OpeningDesign/Vacation_Rental/Transfer/20170905 - ridge rafter hanger proposal/20170905 - ridge rafter hanger proposal - KDF Markup.pdf

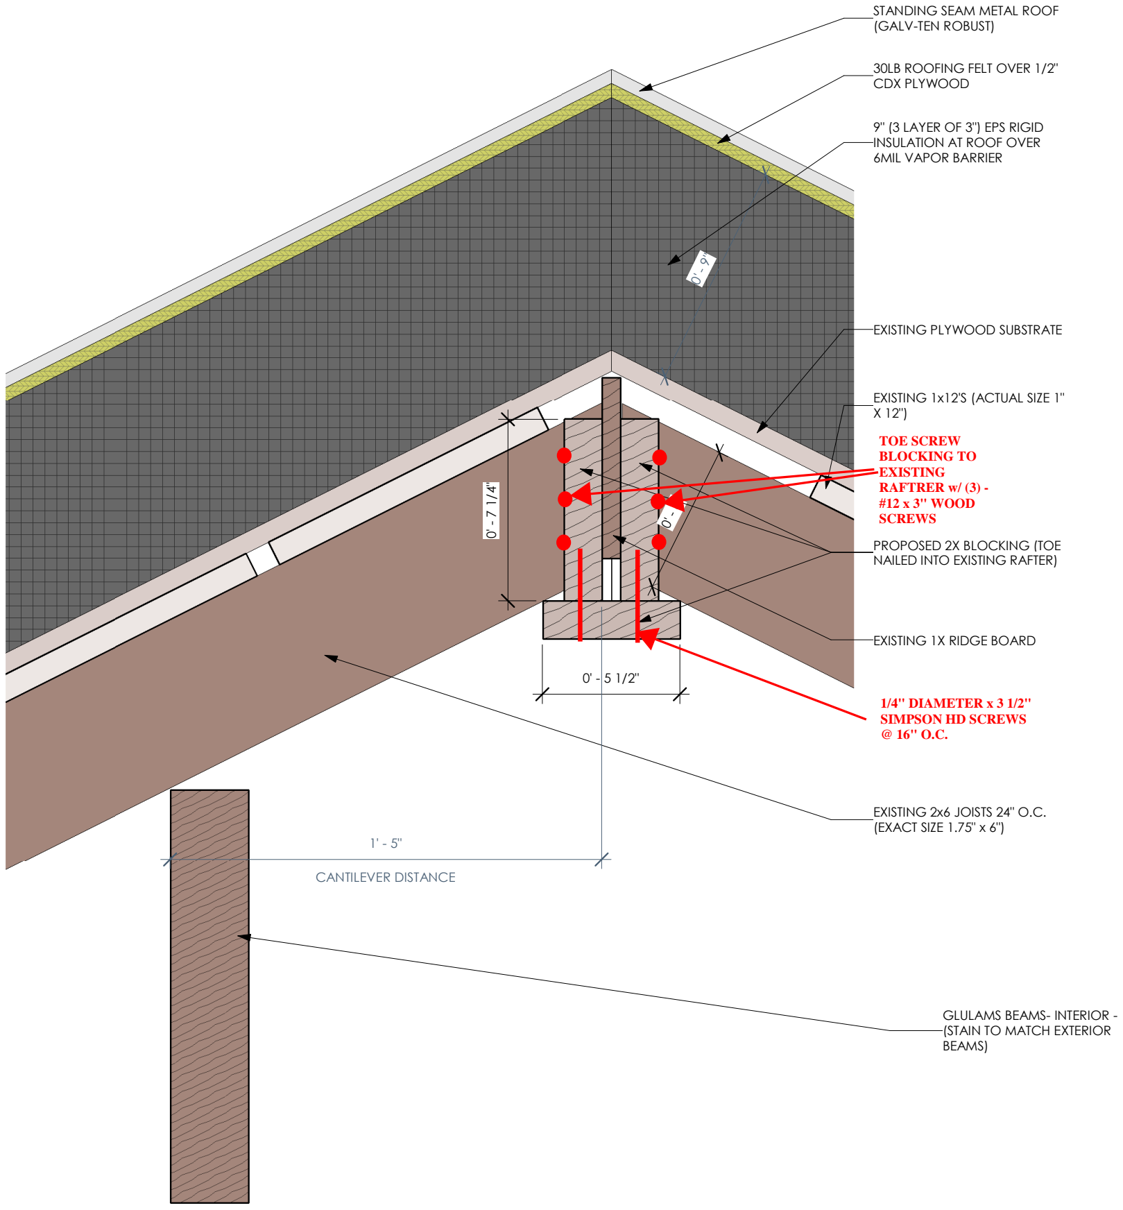
[picture p10: page 1]

EXISTING 1X RIDGE BOARD

GLULAMS BEAMS- INTERIOR -
(STAIN TO MATCH EXTERIOR
BEAMS)

0' - 9"

STANDING SEAM METAL ROOF
(GALV-TEN ROBUST)

30LB ROOFING FELT OVER 1/2" CDX PLYWOOD

9" (3 LAYER OF 3") EPS RIGID INSULATION AT ROOF OVER
6MIL VAPOR BARRIER

EXISTING 1x12'S (ACTUAL SIZE 1" X 12")

0' - 6"

PROPOSED 2X BLOCKING (TOE
NAILED INTO EXISTING RAFTER)

0' - 7 1/4"

0' - 5 1/2"

EXISTING PLYWOOD SUBSTRATE

EXISTING 2x6 JOISTS 24" O.C. (EXACT SIZE 1.75" x 6")

CANTILEVER DISTANCE

1' - 5"
