OpeningDesign/Vacation_Rental/Models/2D Documents/Enscape_2017-05-05-13-06-47.png

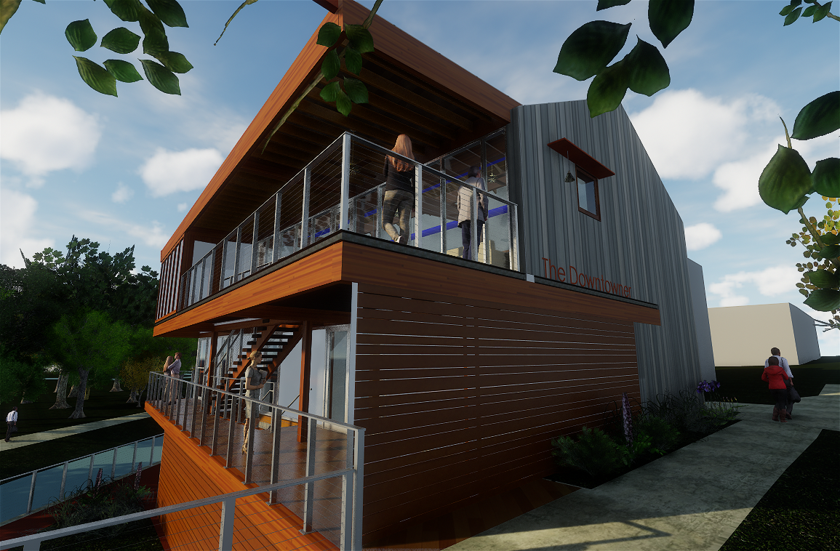
Models/2D Documents/Enscape_2017-05-05-13-06-47.png
