OpeningDesign/Vacation_Rental/Models/2D Documents/Enscape_2017-06-13-12-27-37.png

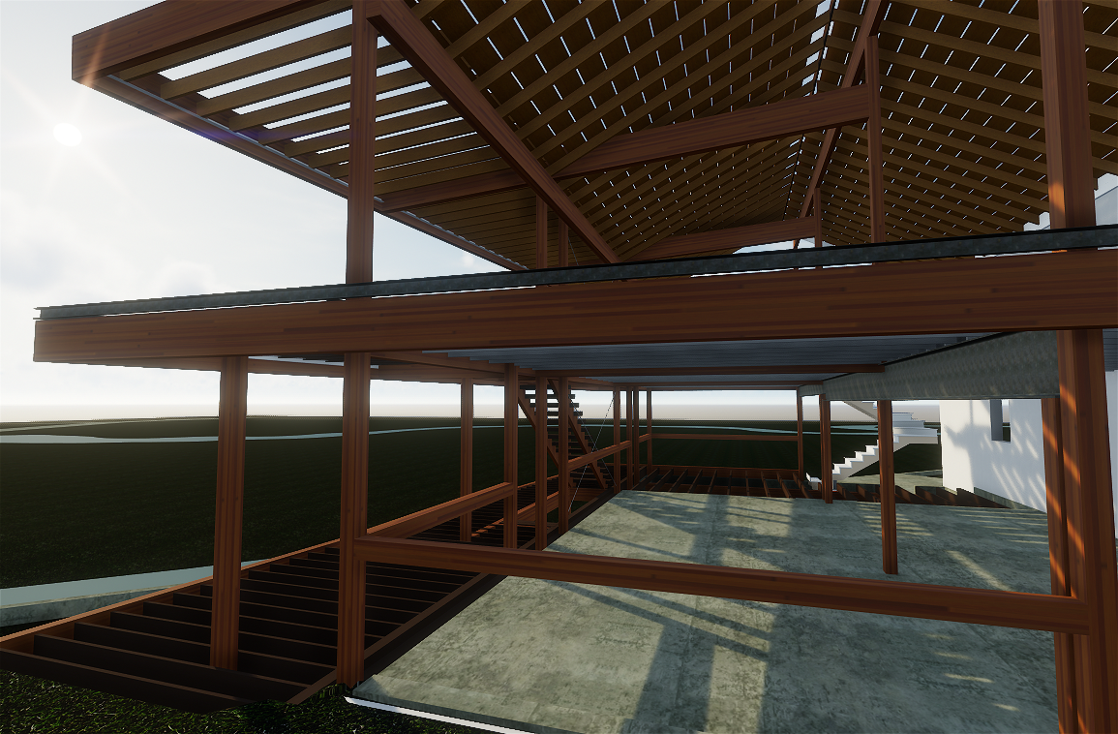
Models/2D Documents/Enscape_2017-06-13-12-27-37.png
