OpeningDesign/Vacation_Rental/Models/2D Documents/Precedent Images/0c7a3d3e602ee59556915388a51b5f31.jpg

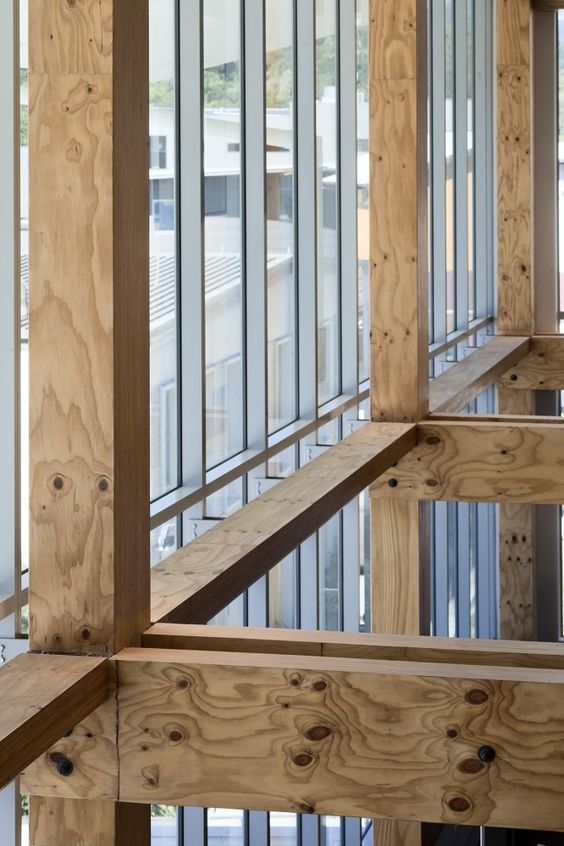
Models/2D Documents/Precedent Images/0c7a3d3e602ee59556915388a51b5f31.jpg
