OpeningDesign/Vacation_Rental/Models/2D Documents/Precedent Images/0d3b4f92185cae513149416970916cf3.jpg

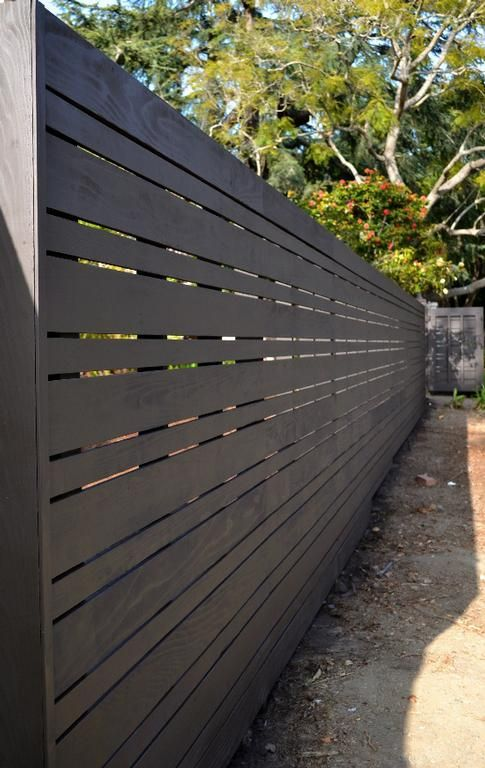
Models/2D Documents/Precedent Images/0d3b4f92185cae513149416970916cf3.jpg
