OpeningDesign/Vacation_Rental/Models/2D Documents/Precedent Images/0d22dfaaf4365529f39f1fb8fd99be02.jpg

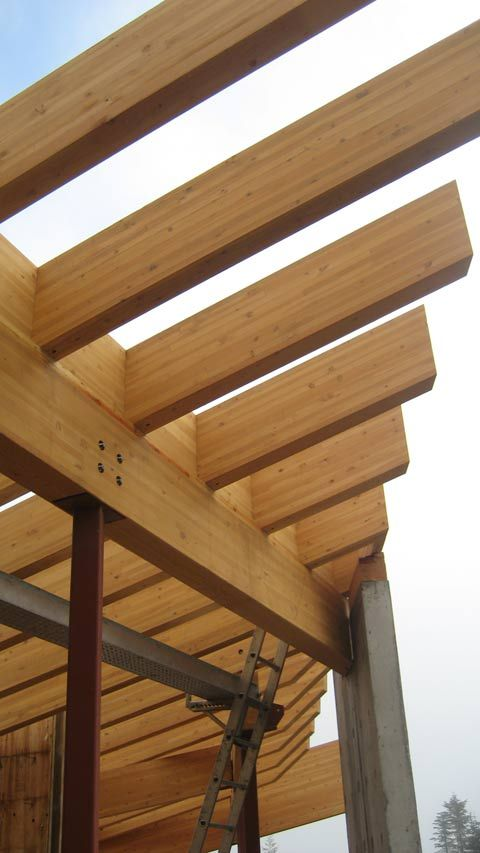
Models/2D Documents/Precedent Images/0d22dfaaf4365529f39f1fb8fd99be02.jpg
