OpeningDesign/Vacation_Rental/Models/2D Documents/Precedent Images/0e876199f10c692c4519da679c8bf5a2.jpg

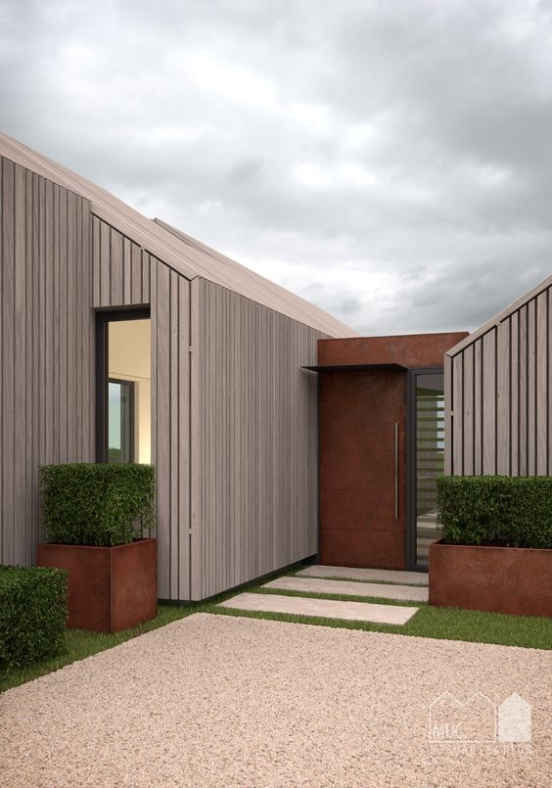
Models/2D Documents/Precedent Images/0e876199f10c692c4519da679c8bf5a2.jpg
