OpeningDesign/Vacation_Rental/Models/2D Documents/Precedent Images/2aeafff6965cd7d682d069013d51a1f6.jpg

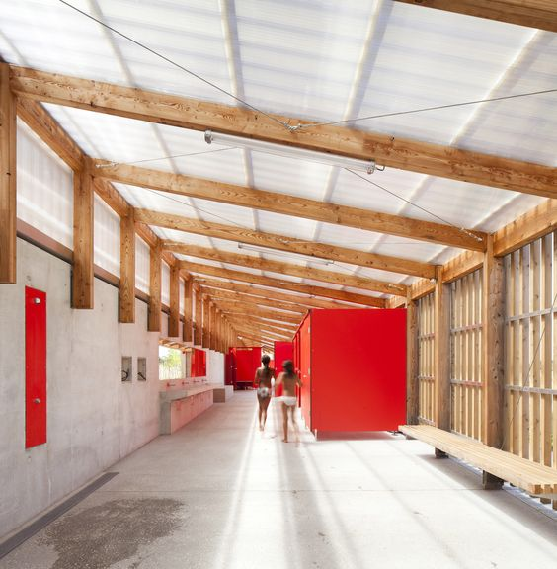
Models/2D Documents/Precedent Images/2aeafff6965cd7d682d069013d51a1f6.jpg
