OpeningDesign/Vacation_Rental/Models/2D Documents/Precedent Images/2b15397afc1d49e527a551473df39ec7.jpg

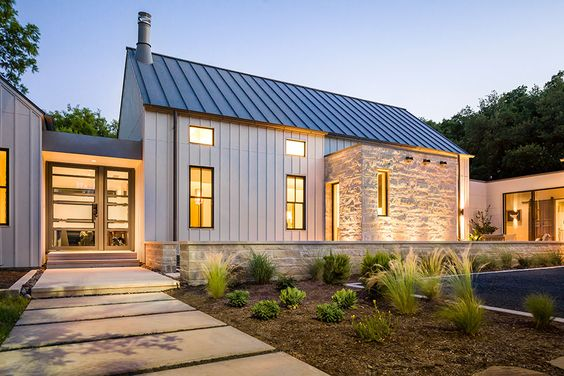
Models/2D Documents/Precedent Images/2b15397afc1d49e527a551473df39ec7.jpg
