OpeningDesign/Vacation_Rental/Models/2D Documents/Precedent Images/02c92ba6af77f66db8dde50bc57269ea.jpg

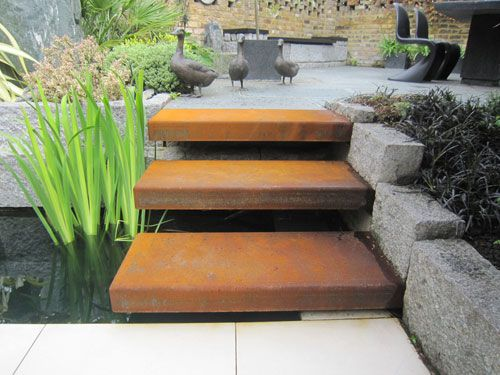
Models/2D Documents/Precedent Images/02c92ba6af77f66db8dde50bc57269ea.jpg
