OpeningDesign/Vacation_Rental/Models/2D Documents/Precedent Images/06a3a0534c0e5ad84e067b8049411fe7.jpg

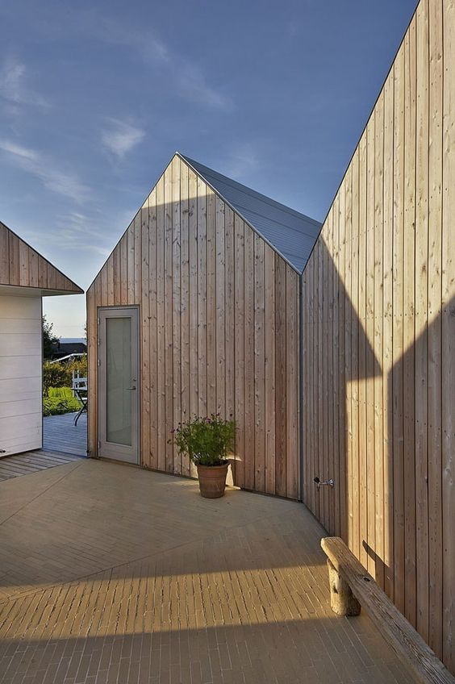
Models/2D Documents/Precedent Images/06a3a0534c0e5ad84e067b8049411fe7.jpg
