OpeningDesign/Vacation_Rental/Models/2D Documents/Precedent Images/07fff5209de71a5784c75fbcb462362a.jpg

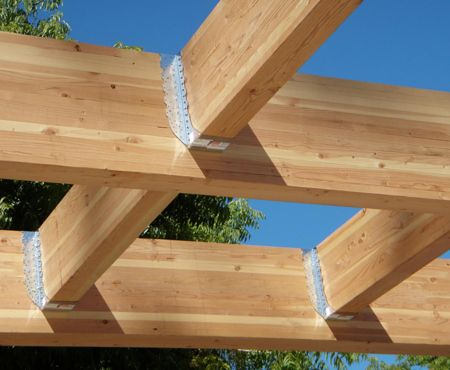
Models/2D Documents/Precedent Images/07fff5209de71a5784c75fbcb462362a.jpg
