OpeningDesign/Vacation_Rental/Models/2D Documents/Precedent Images/9a9ac3109ec64012235650a28028a656.jpg

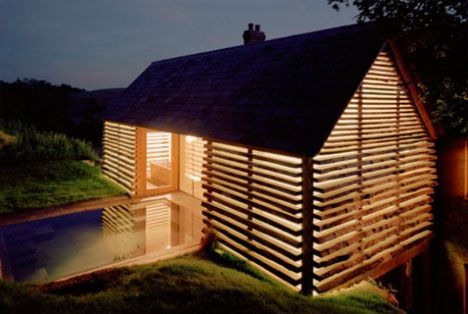
Models/2D Documents/Precedent Images/9a9ac3109ec64012235650a28028a656.jpg
