OpeningDesign/Vacation_Rental/Models/2D Documents/Precedent Images/9c87666fc1ba1ee0fd325ccdcd60f64e.jpg

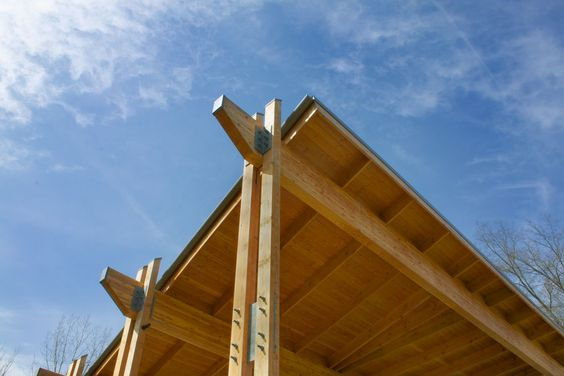
Models/2D Documents/Precedent Images/9c87666fc1ba1ee0fd325ccdcd60f64e.jpg
