OpeningDesign/Vacation_Rental/Models/2D Documents/Precedent Images/40b55ad3849afebcd33c69893c14218f.jpg

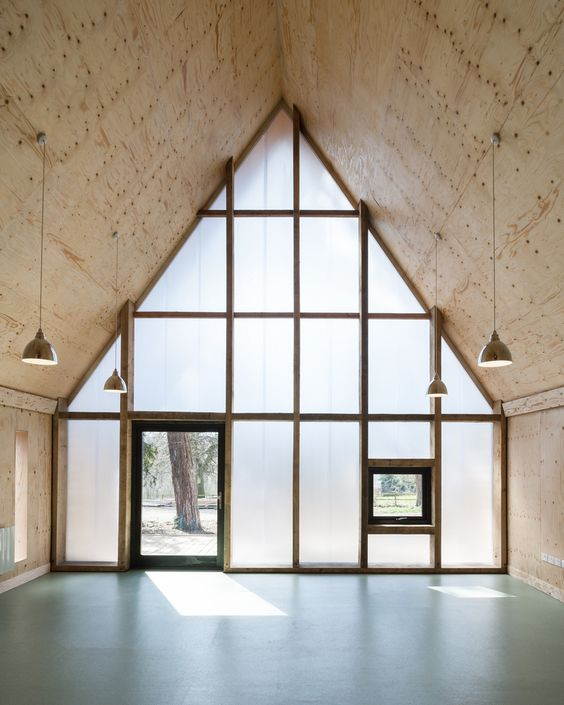
Models/2D Documents/Precedent Images/40b55ad3849afebcd33c69893c14218f.jpg
