OpeningDesign/Vacation_Rental/Models/2D Documents/Precedent Images/41b5add22737bef4c1494f2282eae9dd.jpg

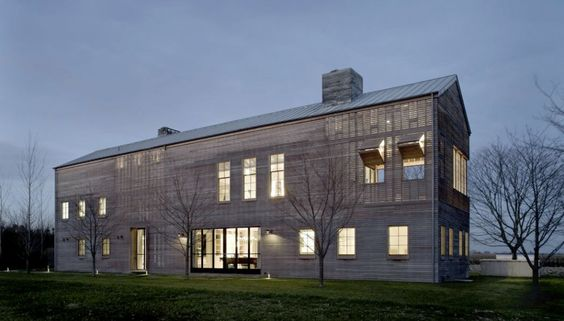
Models/2D Documents/Precedent Images/41b5add22737bef4c1494f2282eae9dd.jpg
