OpeningDesign/Vacation_Rental/Models/2D Documents/Precedent Images/42fc526cb2111db98651c72a134e993a.jpg

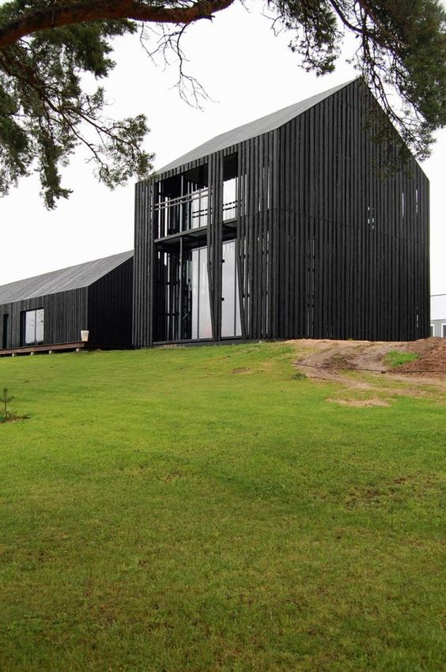
Models/2D Documents/Precedent Images/42fc526cb2111db98651c72a134e993a.jpg
