OpeningDesign/Vacation_Rental/Models/2D Documents/Precedent Images/55af67913b7fc2eed08f882becbad7a5.jpg

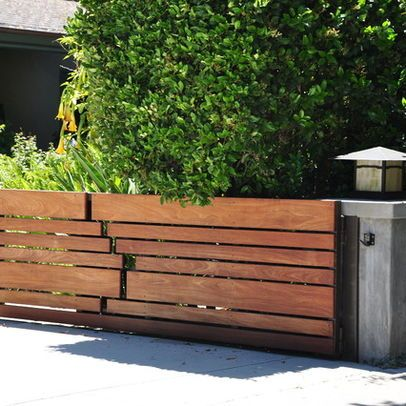
Models/2D Documents/Precedent Images/55af67913b7fc2eed08f882becbad7a5.jpg
