OpeningDesign/Vacation_Rental/Models/2D Documents/Precedent Images/78e75d421c53866a26f0dbb1211216cf.jpg

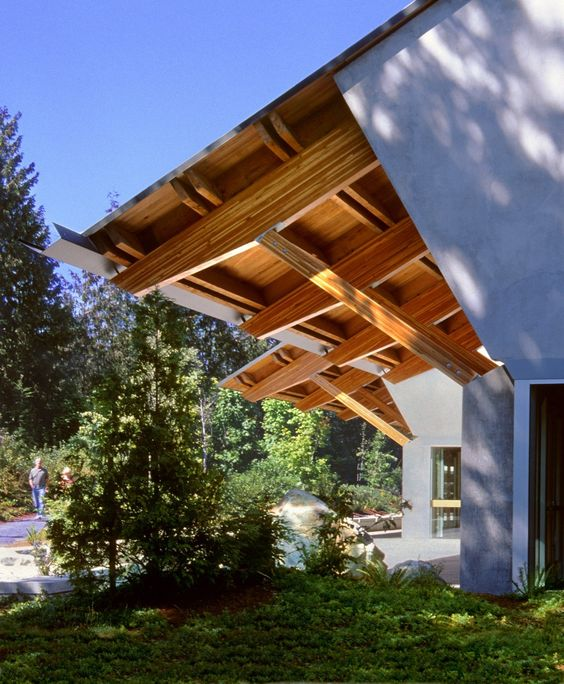
Models/2D Documents/Precedent Images/78e75d421c53866a26f0dbb1211216cf.jpg
