OpeningDesign/Vacation_Rental/Models/2D Documents/Precedent Images/87a9d24e1d08ba55797b84f50cd7fb18.jpg

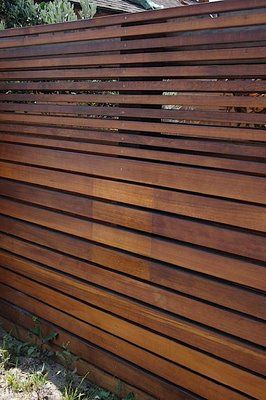
Models/2D Documents/Precedent Images/87a9d24e1d08ba55797b84f50cd7fb18.jpg
