OpeningDesign/Vacation_Rental/Models/2D Documents/Precedent Images/184f7b51ef069aa56a82b9aa3c524680.jpg

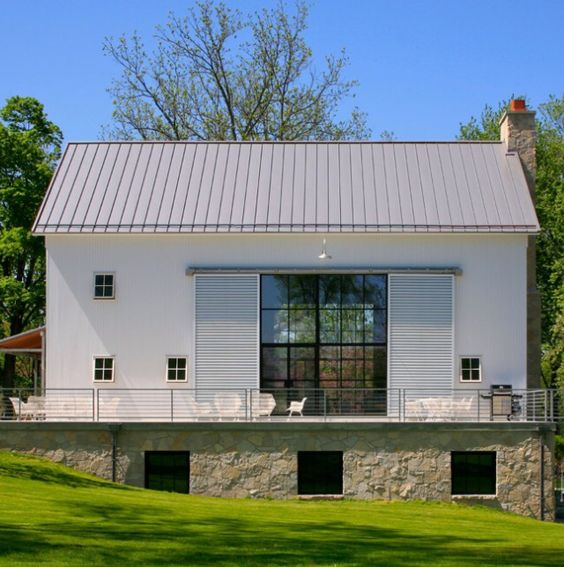
Models/2D Documents/Precedent Images/184f7b51ef069aa56a82b9aa3c524680.jpg
