OpeningDesign/Vacation_Rental/Models/2D Documents/Precedent Images/188d307774ca5b3812a683e529af5a94.jpg

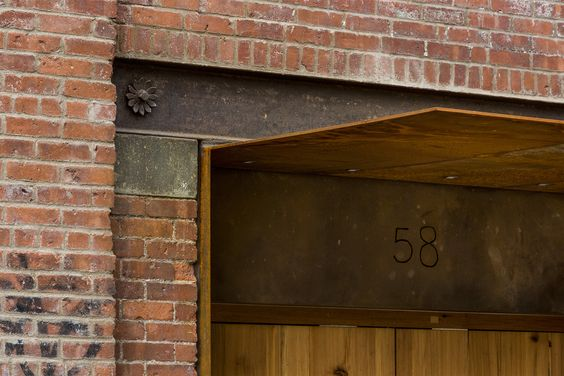
Models/2D Documents/Precedent Images/188d307774ca5b3812a683e529af5a94.jpg
