OpeningDesign/Vacation_Rental/Models/2D Documents/Precedent Images/335ba02f0525db59a8c18d0f0f9bd925.jpg

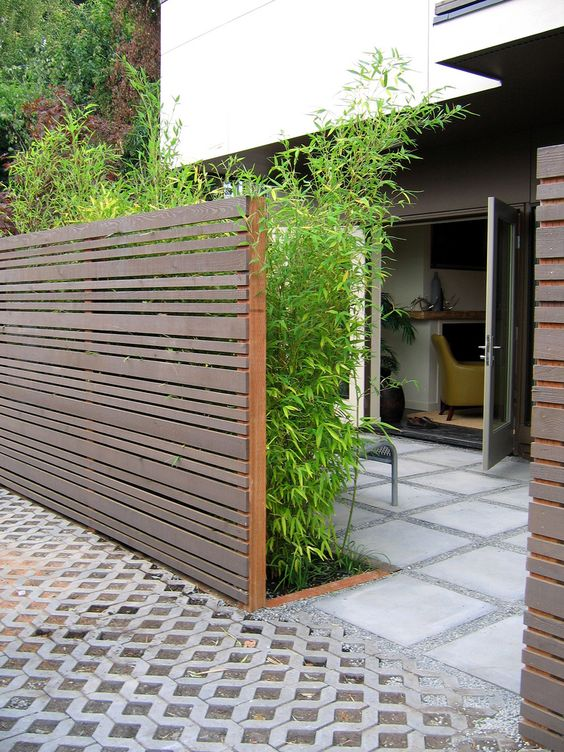
Models/2D Documents/Precedent Images/335ba02f0525db59a8c18d0f0f9bd925.jpg
