OpeningDesign/Vacation_Rental/Models/2D Documents/Precedent Images/350d798f98d4a8c157ad74bf83be0b5d.jpg

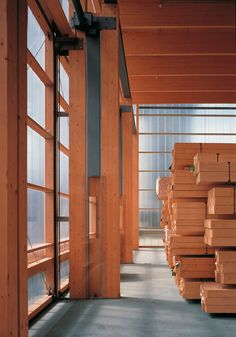
Models/2D Documents/Precedent Images/350d798f98d4a8c157ad74bf83be0b5d.jpg
