OpeningDesign/Vacation_Rental/Models/2D Documents/Precedent Images/5657ed915eb3acebcfed94b91c742628.jpg

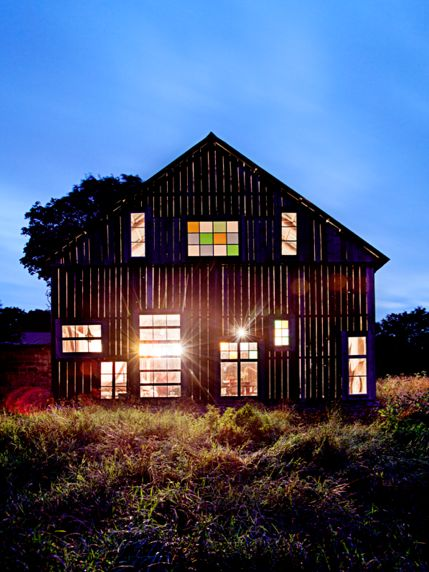
Models/2D Documents/Precedent Images/5657ed915eb3acebcfed94b91c742628.jpg
