OpeningDesign/Vacation_Rental/Models/2D Documents/Precedent Images/7824d757f0b7d5c43f43977f591d6d58.jpg

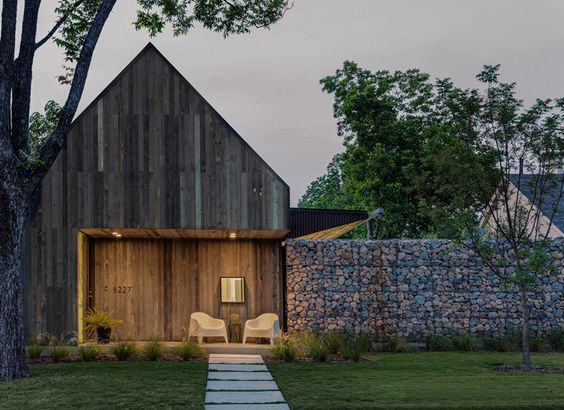
Models/2D Documents/Precedent Images/7824d757f0b7d5c43f43977f591d6d58.jpg
