OpeningDesign/Vacation_Rental/Models/2D Documents/Precedent Images/19436df78f297fb4a34a5acba1796042.jpg

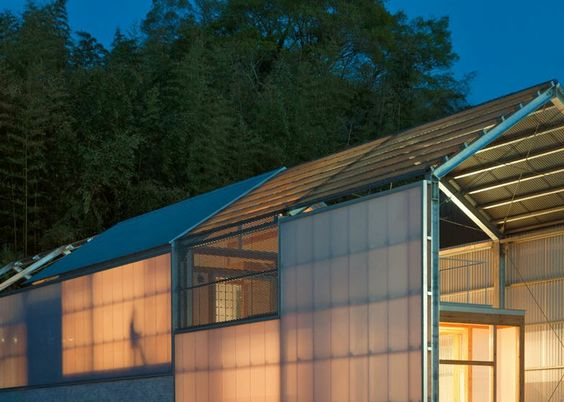
Models/2D Documents/Precedent Images/19436df78f297fb4a34a5acba1796042.jpg
