OpeningDesign/Vacation_Rental/Models/2D Documents/Precedent Images/040659eb7f77c008b3507f8cc1e04a2e.jpg

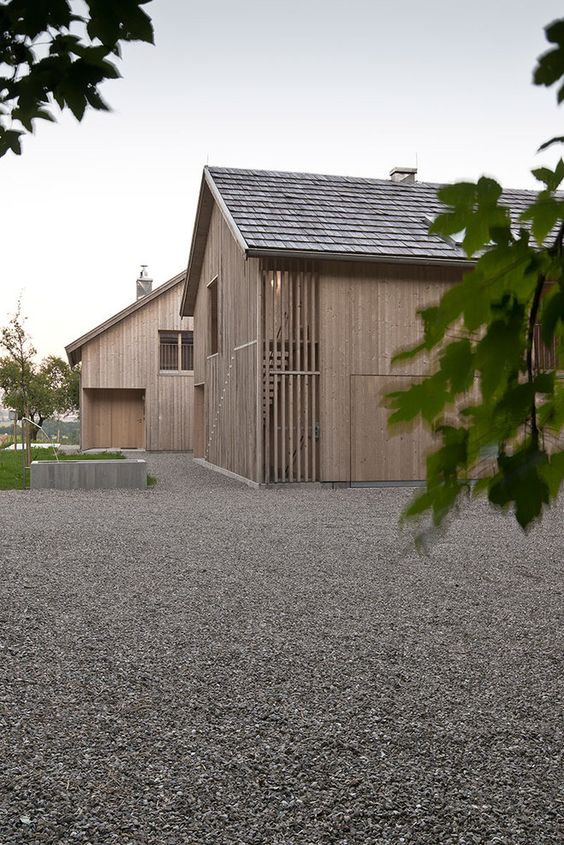
Models/2D Documents/Precedent Images/040659eb7f77c008b3507f8cc1e04a2e.jpg
