OpeningDesign/Vacation_Rental/Models/2D Documents/Precedent Images/148513be1fd4c37da1aaef3aa7b98338.jpg

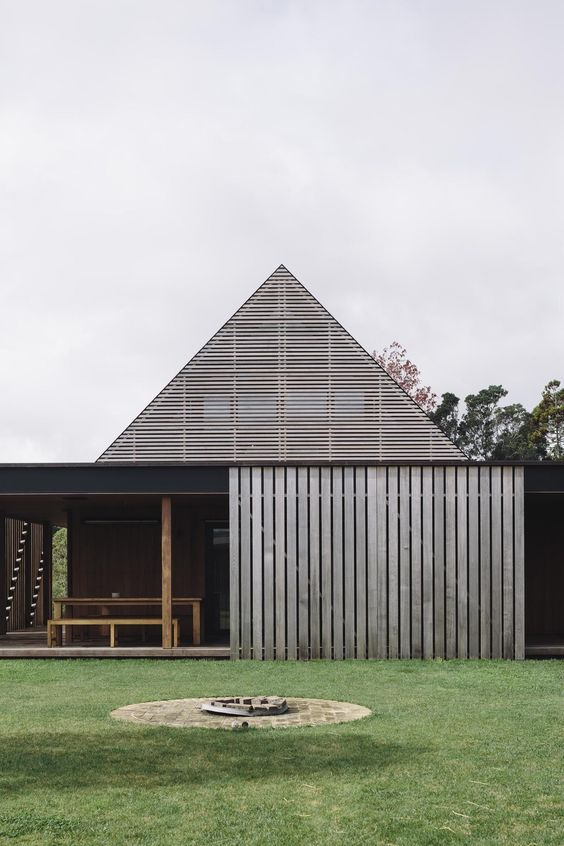
Models/2D Documents/Precedent Images/148513be1fd4c37da1aaef3aa7b98338.jpg
