OpeningDesign/Vacation_Rental/Models/2D Documents/Precedent Images/7329964b805389fec1def58e11ec604a.jpg

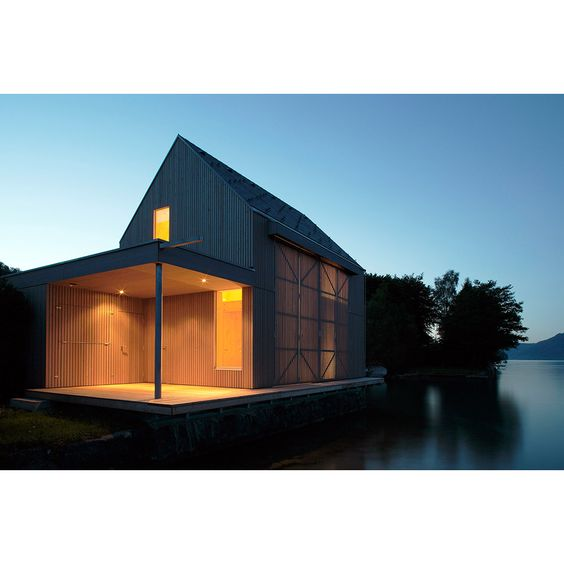
Models/2D Documents/Precedent Images/7329964b805389fec1def58e11ec604a.jpg
