OpeningDesign/Vacation_Rental/Models/2D Documents/Precedent Images/57048091b4c16367bc145f9d35cd8de7.jpg

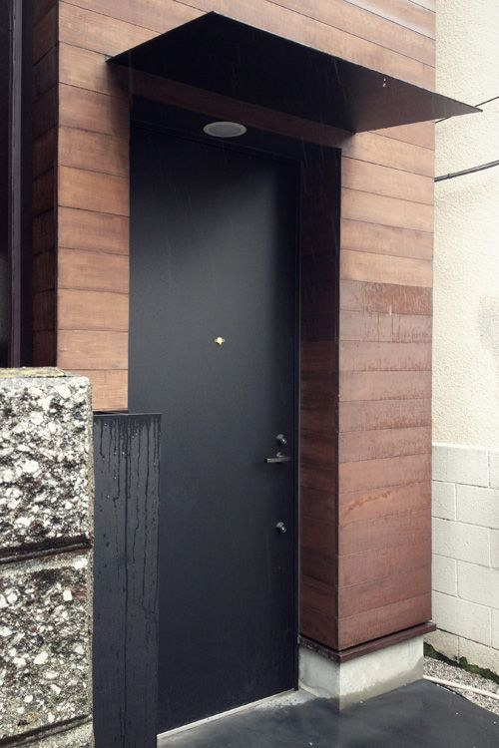
Models/2D Documents/Precedent Images/57048091b4c16367bc145f9d35cd8de7.jpg
