OpeningDesign/Vacation_Rental/Models/2D Documents/Precedent Images/80009552e02b91b7375557edf337d2f3.jpg

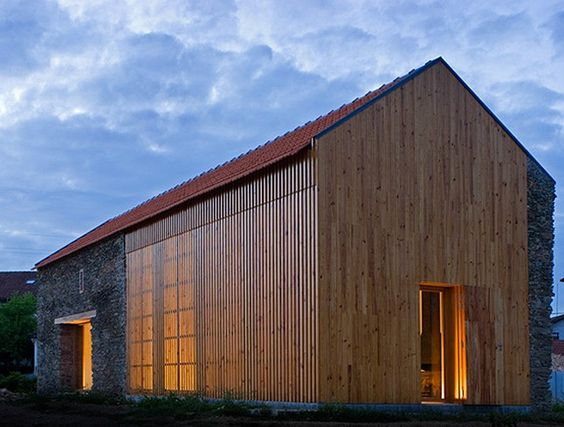
Models/2D Documents/Precedent Images/80009552e02b91b7375557edf337d2f3.jpg
