OpeningDesign/Vacation_Rental/Models/2D Documents/Precedent Images/a5a983e3bf02a2cea2f723c142aec2b0.jpg

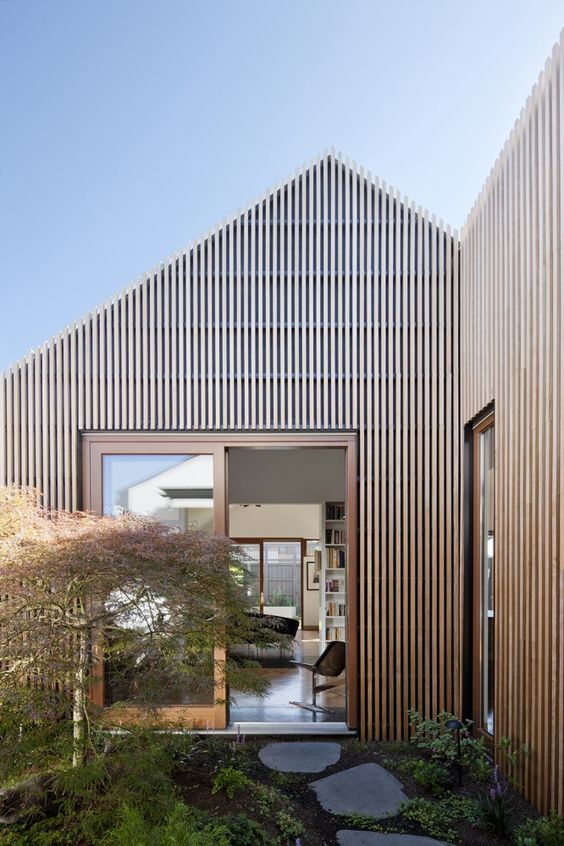
Models/2D Documents/Precedent Images/a5a983e3bf02a2cea2f723c142aec2b0.jpg
