OpeningDesign/Vacation_Rental/Models/2D Documents/Precedent Images/a7e06f509b7f7ce895a32ad0f5a3a4d4.jpg

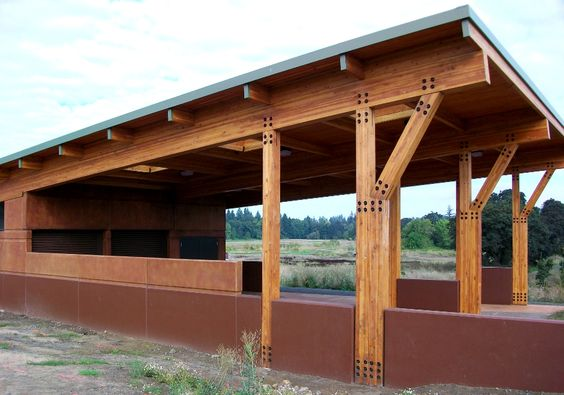
Models/2D Documents/Precedent Images/a7e06f509b7f7ce895a32ad0f5a3a4d4.jpg
