OpeningDesign/Vacation_Rental/Models/2D Documents/Precedent Images/a407f5ff8347d7328c1e697cfa142259.jpg

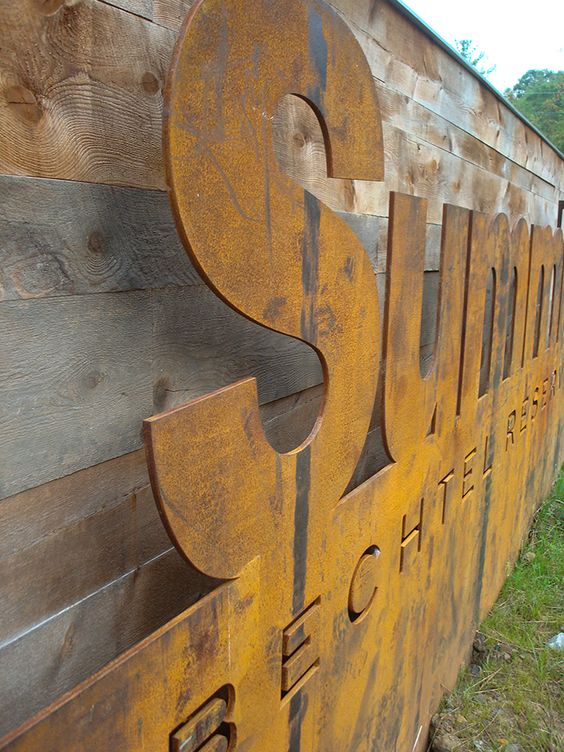
Models/2D Documents/Precedent Images/a407f5ff8347d7328c1e697cfa142259.jpg
