OpeningDesign/Vacation_Rental/Models/2D Documents/Precedent Images/abbfe04b8cfb12c9ef20e34d3efc613c.jpg

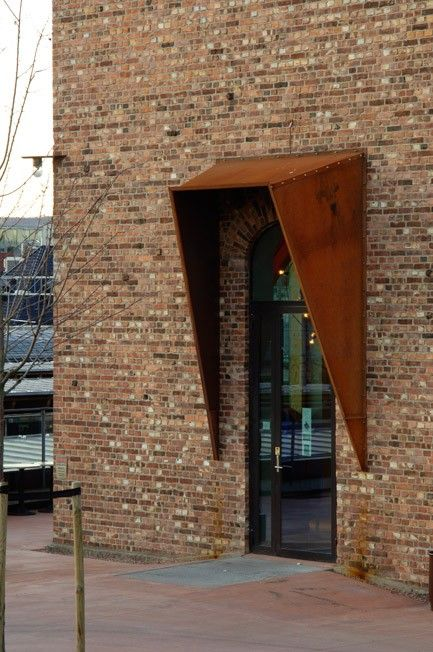
Models/2D Documents/Precedent Images/abbfe04b8cfb12c9ef20e34d3efc613c.jpg
