OpeningDesign/Vacation_Rental/Models/2D Documents/Precedent Images/adb4d52d20b00e25765e1fd135ce175e.jpg

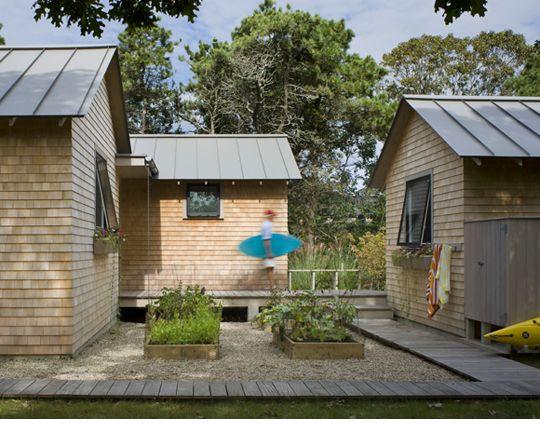
Models/2D Documents/Precedent Images/adb4d52d20b00e25765e1fd135ce175e.jpg
