OpeningDesign/Vacation_Rental/Models/2D Documents/Precedent Images/af5ca8ab25973f4a139beec4719d8663.jpg

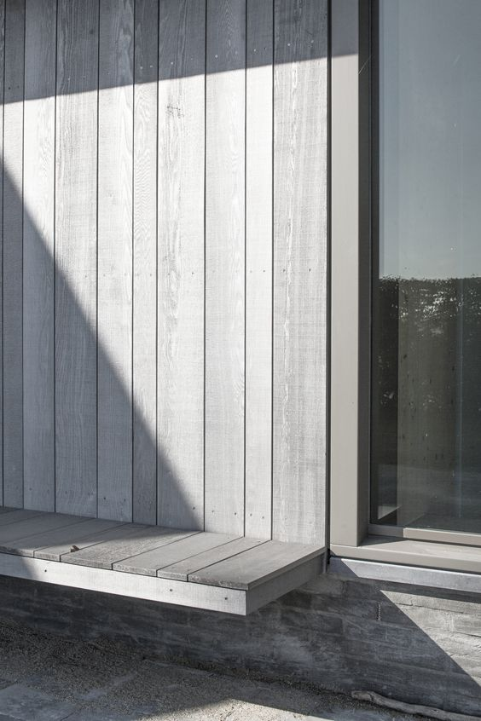
Models/2D Documents/Precedent Images/af5ca8ab25973f4a139beec4719d8663.jpg
