OpeningDesign/Vacation_Rental/Models/2D Documents/Precedent Images/b6b6c0b5eac12a77ff2778b2761079a8.jpg

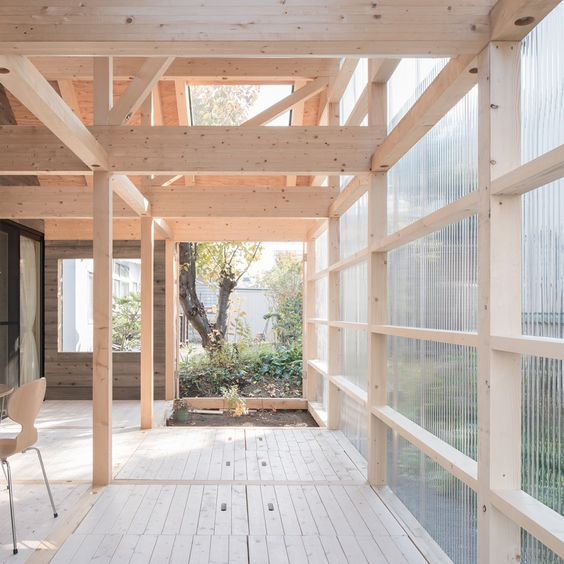
Models/2D Documents/Precedent Images/b6b6c0b5eac12a77ff2778b2761079a8.jpg
