OpeningDesign/Vacation_Rental/Models/2D Documents/Precedent Images/b44d1605a9f73c70cb136d1f243c0d6f.jpg

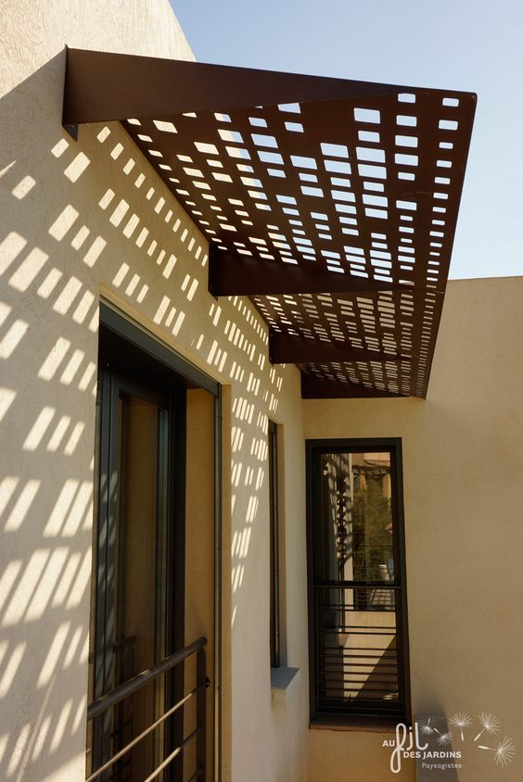
Models/2D Documents/Precedent Images/b44d1605a9f73c70cb136d1f243c0d6f.jpg
