OpeningDesign/Vacation_Rental/Models/2D Documents/Precedent Images/b58d95502113ab2a8a6457f16e2dfd0d.jpg

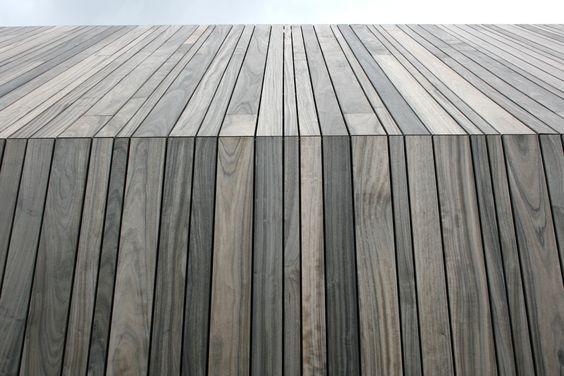
Models/2D Documents/Precedent Images/b58d95502113ab2a8a6457f16e2dfd0d.jpg
