OpeningDesign/Vacation_Rental/Models/2D Documents/Precedent Images/b794573e810852b9f5c5818d71a66ad9.jpg

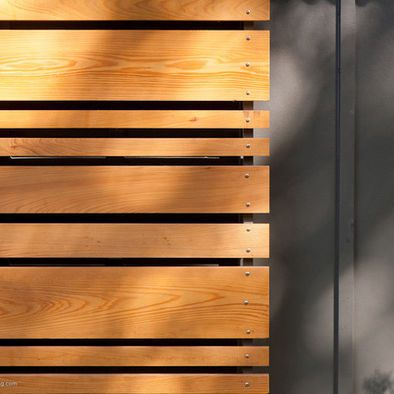
Models/2D Documents/Precedent Images/b794573e810852b9f5c5818d71a66ad9.jpg
