OpeningDesign/Vacation_Rental/Models/2D Documents/Precedent Images/bb8e8208-fb95-49fd-9c0d-446f227f3a53_400.jpg

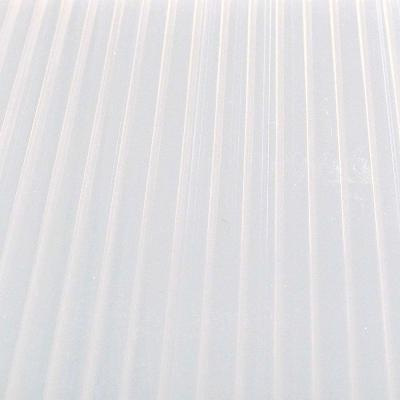
Models/2D Documents/Precedent Images/bb8e8208-fb95-49fd-9c0d-446f227f3a53_400.jpg
