OpeningDesign/Vacation_Rental/Models/2D Documents/Precedent Images/c44c588e8d558fd1838573a1d4a702a1.jpg

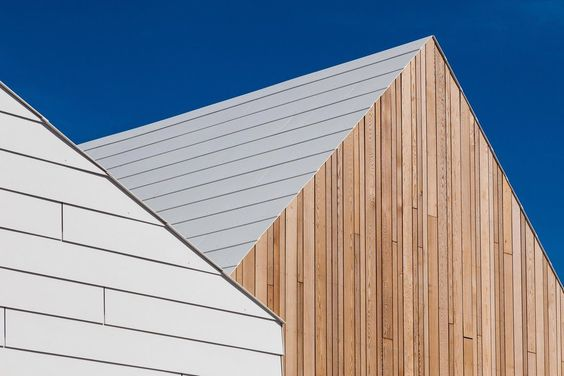
Models/2D Documents/Precedent Images/c44c588e8d558fd1838573a1d4a702a1.jpg
