OpeningDesign/Vacation_Rental/Models/2D Documents/Precedent Images/c00492bd0c0bb27d8dadb2e220c72b18.jpg

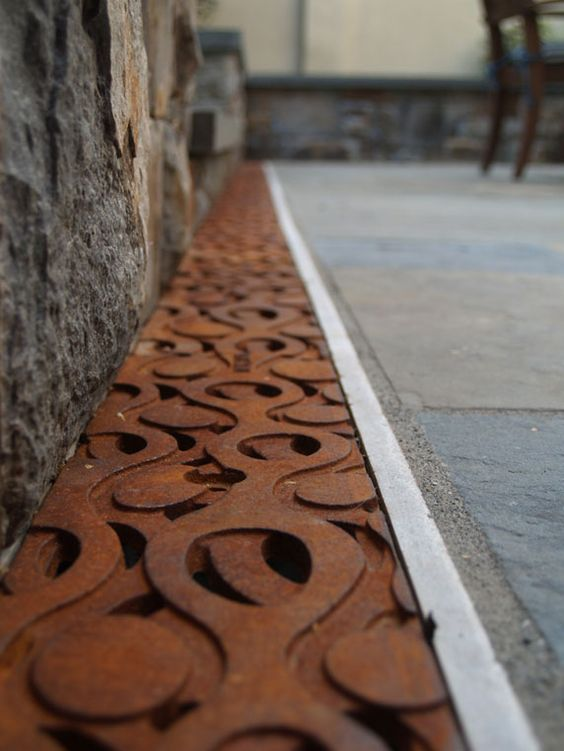
Models/2D Documents/Precedent Images/c00492bd0c0bb27d8dadb2e220c72b18.jpg
