OpeningDesign/Vacation_Rental/Models/2D Documents/Precedent Images/chrome_2016-11-02_14-01-50.png

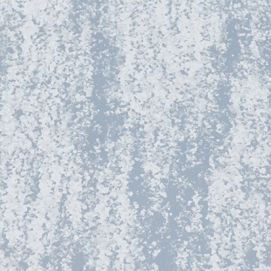
Models/2D Documents/Precedent Images/chrome_2016-11-02_14-01-50.png
