OpeningDesign/Vacation_Rental/Models/2D Documents/Precedent Images/d8a0bcfc8ddbbb11d38e08802ca983df.jpg

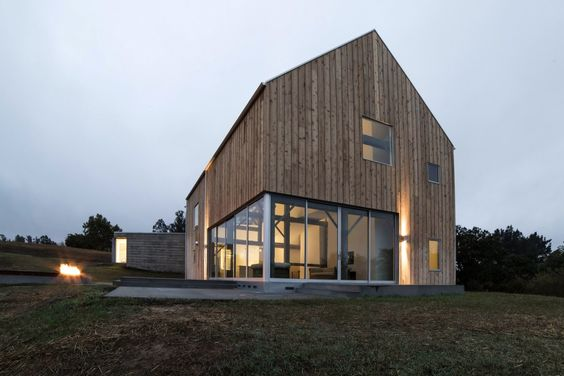
Models/2D Documents/Precedent Images/d8a0bcfc8ddbbb11d38e08802ca983df.jpg
