OpeningDesign/Vacation_Rental/Models/2D Documents/Precedent Images/d315beef983d25dbf1215081fba08e31.jpg

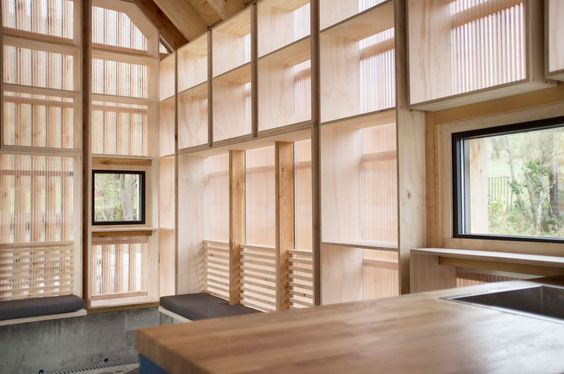
Models/2D Documents/Precedent Images/d315beef983d25dbf1215081fba08e31.jpg
