OpeningDesign/Vacation_Rental/Models/2D Documents/Precedent Images/d9029c70ddbc12151304676f0983d141.jpg

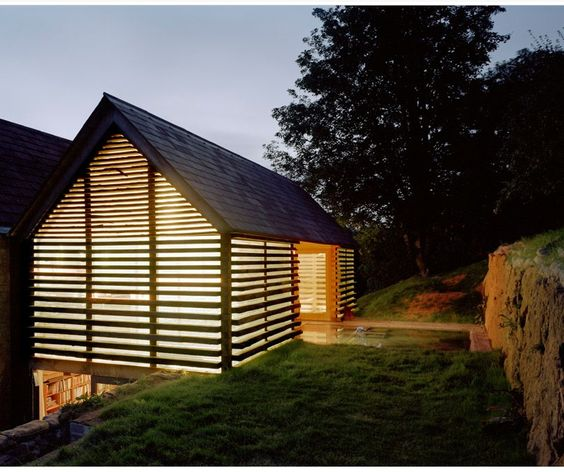
Models/2D Documents/Precedent Images/d9029c70ddbc12151304676f0983d141.jpg
