OpeningDesign/Vacation_Rental/Models/2D Documents/Precedent Images/e4ac24d96331886f48b93c2413805d46.jpg

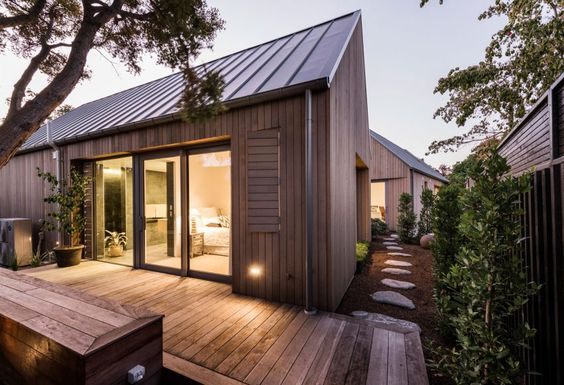
Models/2D Documents/Precedent Images/e4ac24d96331886f48b93c2413805d46.jpg
