OpeningDesign/Vacation_Rental/Models/2D Documents/Precedent Images/e55f57aed85fb10bcdb1eadcb82aa508.jpg

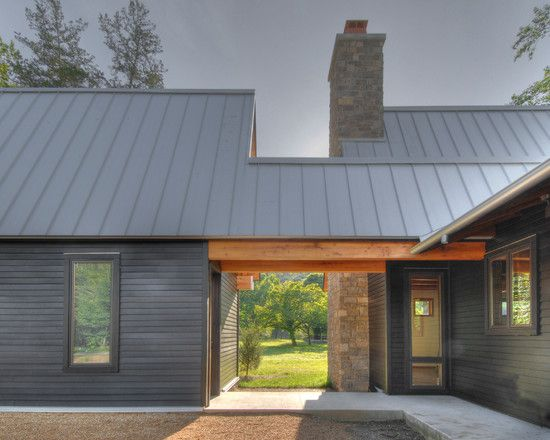
Models/2D Documents/Precedent Images/e55f57aed85fb10bcdb1eadcb82aa508.jpg
