OpeningDesign/Vacation_Rental/Models/2D Documents/Precedent Images/ec4af35faf6695d70a6081da4c38bd10.jpg

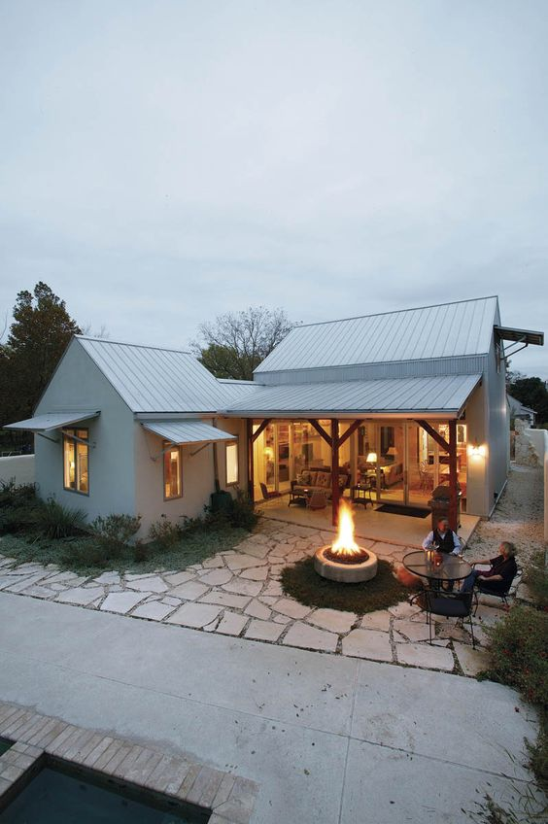
Models/2D Documents/Precedent Images/ec4af35faf6695d70a6081da4c38bd10.jpg
