OpeningDesign/Vacation_Rental/Models/2D Documents/Precedent Images/ec76f3e3b3678906dc25c459d5dc28e5.jpg

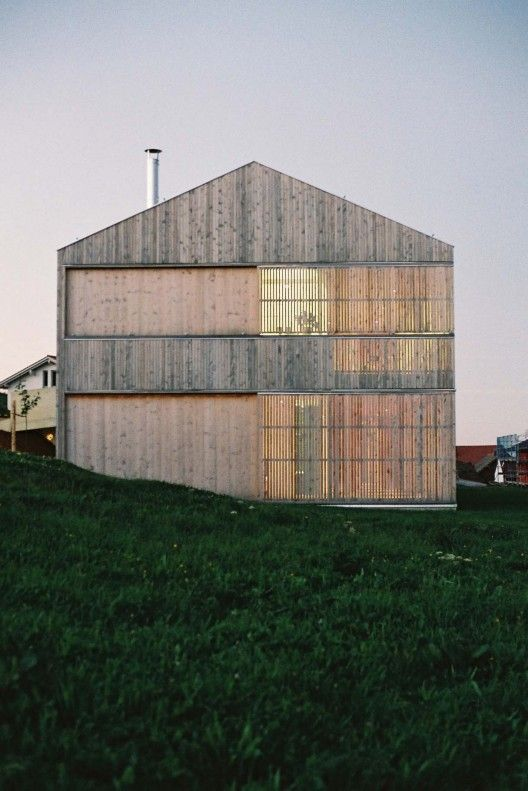
Models/2D Documents/Precedent Images/ec76f3e3b3678906dc25c459d5dc28e5.jpg
