OpeningDesign/Vacation_Rental/Models/2D Documents/Precedent Images/f5e04f823d698f583e8dc3702eadc1c3.jpg

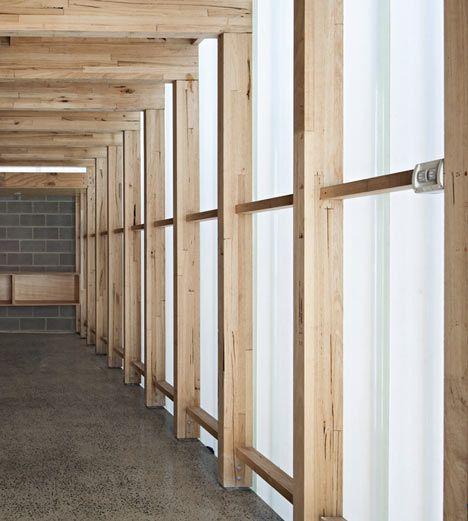
Models/2D Documents/Precedent Images/f5e04f823d698f583e8dc3702eadc1c3.jpg
