OpeningDesign/Vacation_Rental/Models/2D Documents/Precedent Images/f12e88fc55a7d9233867dde64b918f38.jpg

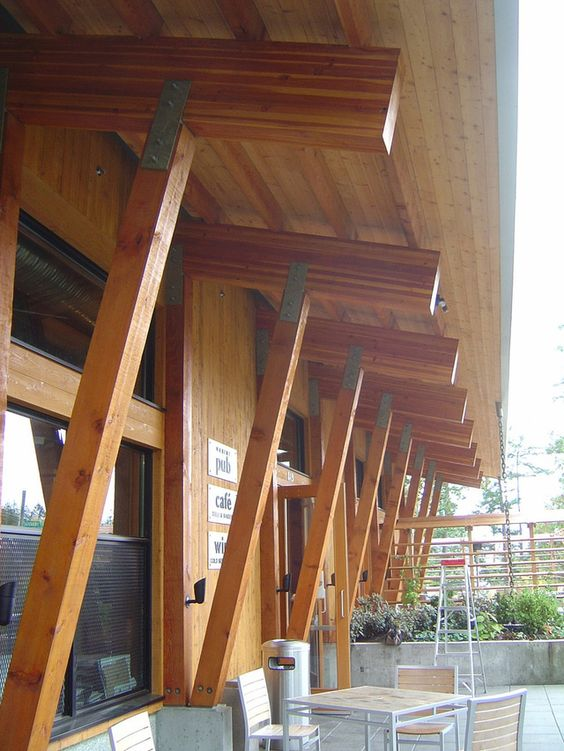
Models/2D Documents/Precedent Images/f12e88fc55a7d9233867dde64b918f38.jpg
