OpeningDesign/Vacation_Rental/Models/2D Documents/Precedent Images/f586c71b3e9edebeaa1a09f825422619.jpg

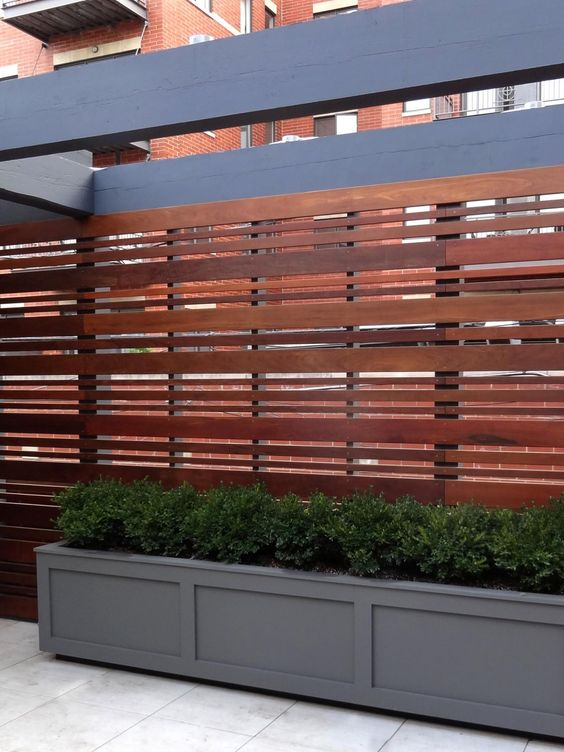
Models/2D Documents/Precedent Images/f586c71b3e9edebeaa1a09f825422619.jpg
