OpeningDesign/Vacation_Rental/Models/2D Documents/Precedent Images/fb6aa189b32866a8f8519f56d074caaf.jpg

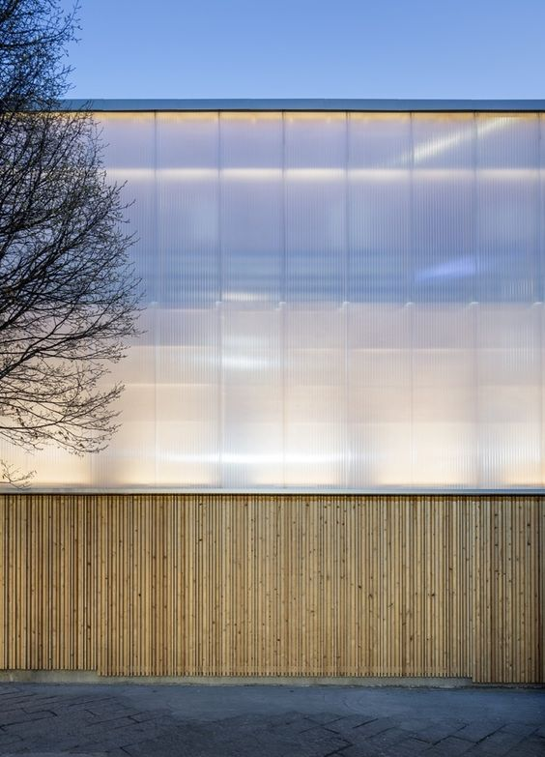
Models/2D Documents/Precedent Images/fb6aa189b32866a8f8519f56d074caaf.jpg
