OpeningDesign/Vacation_Rental/Models/2D Documents/Precedent Images/Galvalume-plus_grande.png

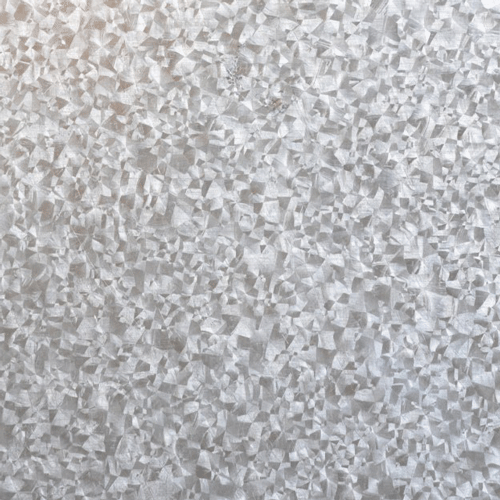
Models/2D Documents/Precedent Images/Galvalume-plus_grande.png
