OpeningDesign/Vacation_Rental/Models/2D Documents/Precedent Images/JUNTA_COM_DOBRA_EM_A_O_CORTEN.jpg

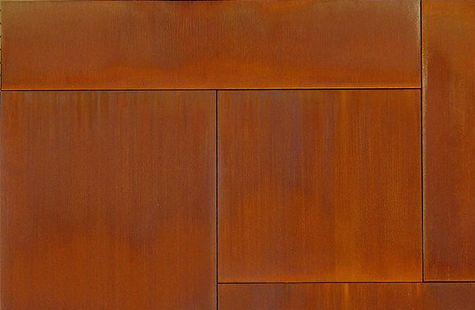
Models/2D Documents/Precedent Images/JUNTA_COM_DOBRA_EM_A_O_CORTEN.jpg
