OpeningDesign/Vacation_Rental/Models/2D Documents/Precedent Images/ss_cordovan_brown_728x728.jpg

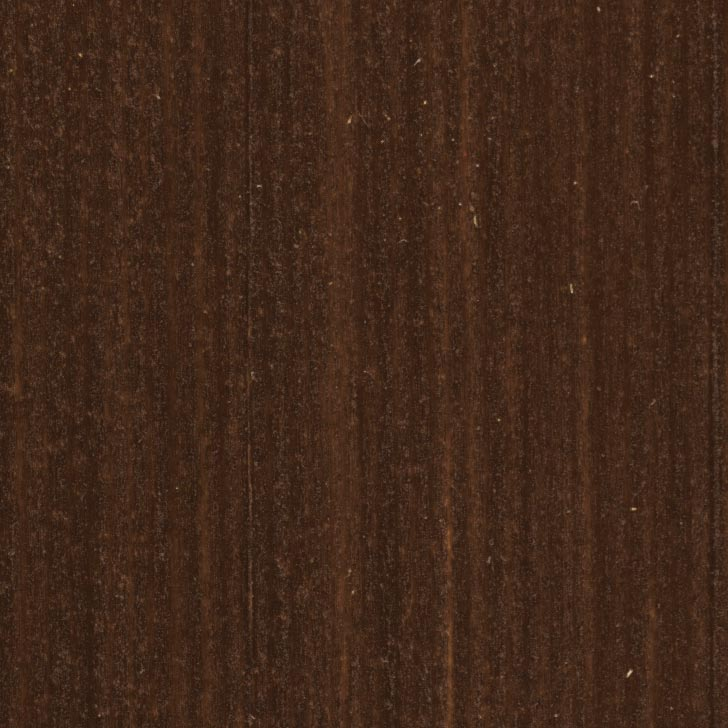
Models/2D Documents/Precedent Images/ss_cordovan_brown_728x728.jpg
