OpeningDesign/Vacation_Rental/Models/2D Documents/Precedent Images/ss_dark_slate_REV1_228x228.jpg

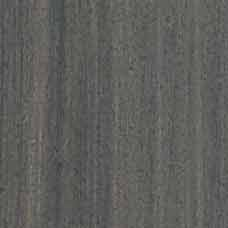
Models/2D Documents/Precedent Images/ss_dark_slate_REV1_228x228.jpg
