OpeningDesign/Vacation_Rental/Models/2D Documents/Revit_2017-05-05_12-48-27.png

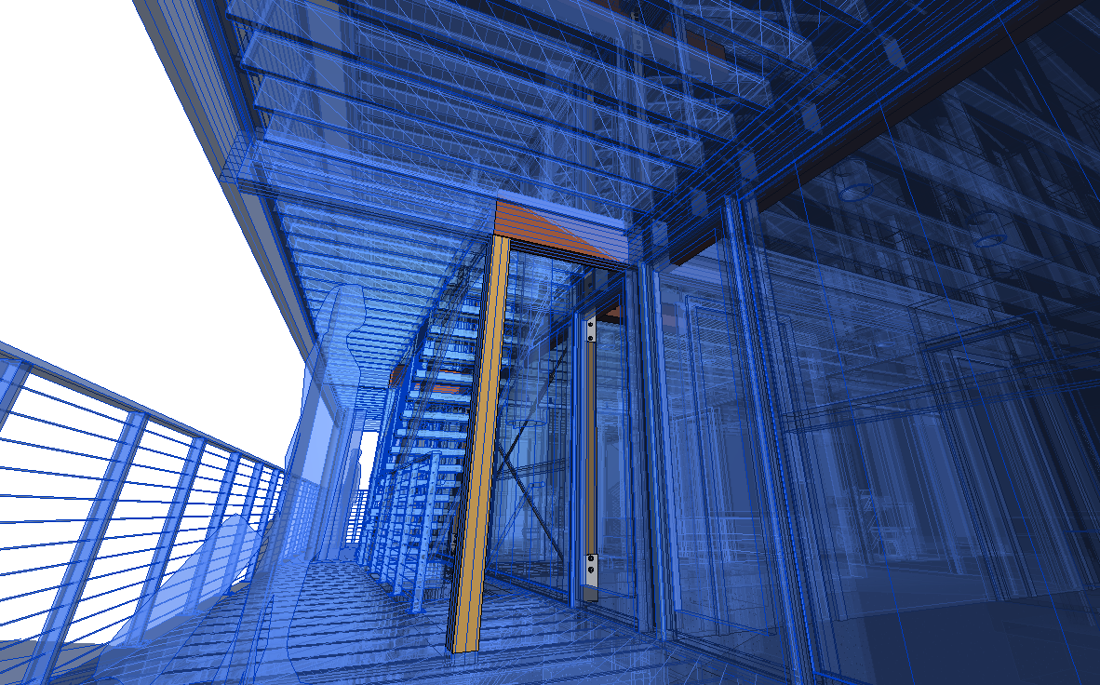
Models/2D Documents/Revit_2017-05-05_12-48-27.png
