OpeningDesign/Vacation_Rental/Models/Textures/Corten-Steel-Texture.jpg

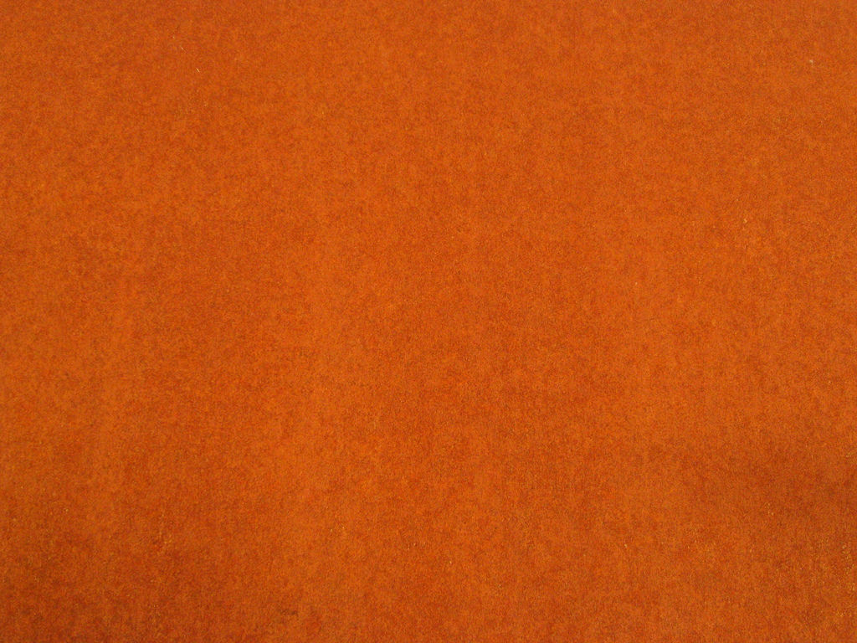
Models/Textures/Corten-Steel-Texture.jpg
