OpeningDesign/Vacation_Rental/Models/Textures/map2.jpg

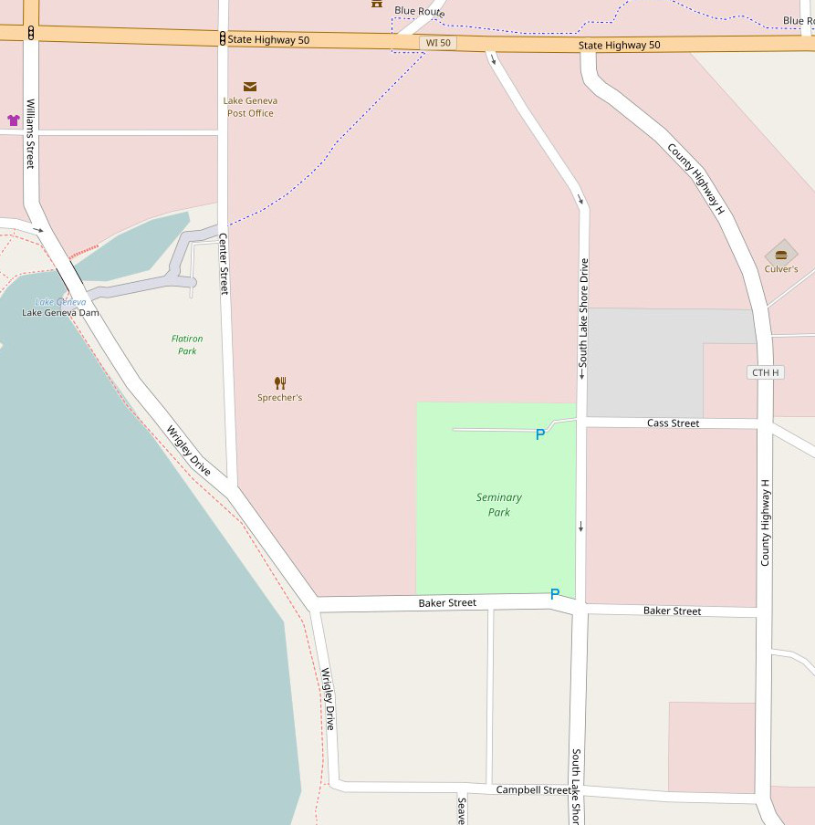
Models/Textures/map2.jpg
