OpeningDesign/Vacation_Rental/Models/Textures/map.jpg

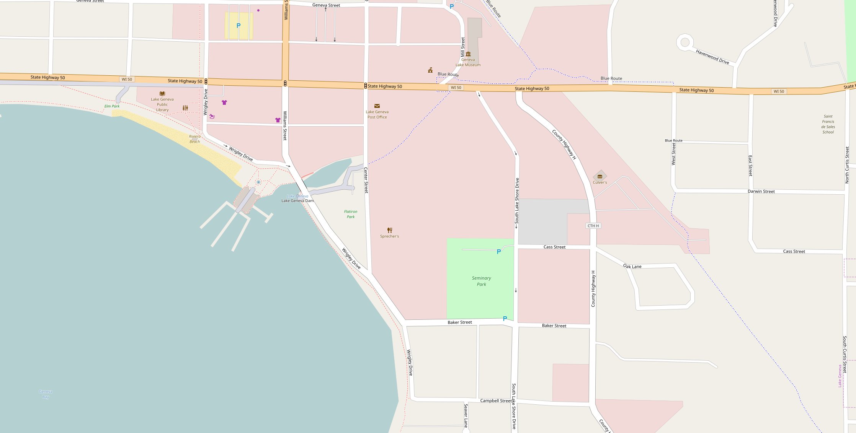
Models/Textures/map.jpg
