OpeningDesign/Vacation_Rental/Models/Textures/mulch_seamless_texture_by_borderlight-d7t0iaq.jpg

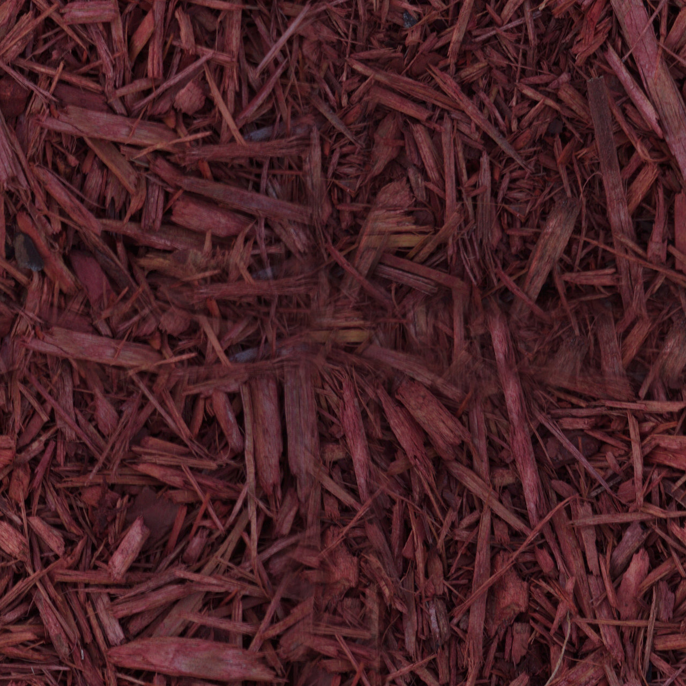
Models/Textures/mulch_seamless_texture_by_borderlight-d7t0iaq.jpg
