OpeningDesign/Vacation_Rental/Models/Textures/SIDING WITH FASTENERS.png

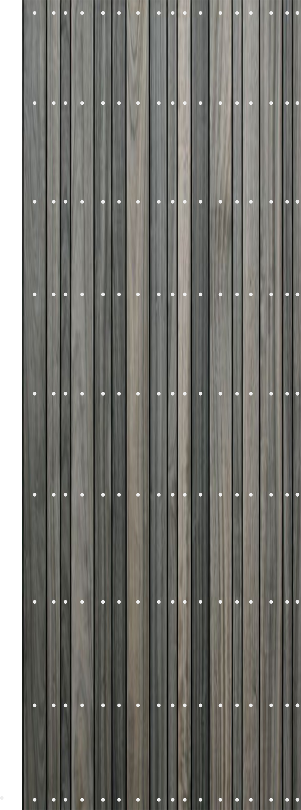
Models/Textures/SIDING WITH FASTENERS.png
