OpeningDesign/Vacation_Rental/Models/Textures/siding.jpg

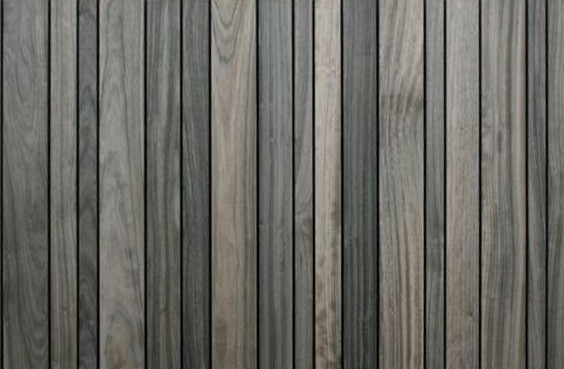
Models/Textures/siding.jpg
