OpeningDesign/Vacation_Rental/Research and CA/Research and Submittals/02 - Existing Conditions and Code Research/3-19-2015_Zoning_Map_36X38_w_Floodway.jpg

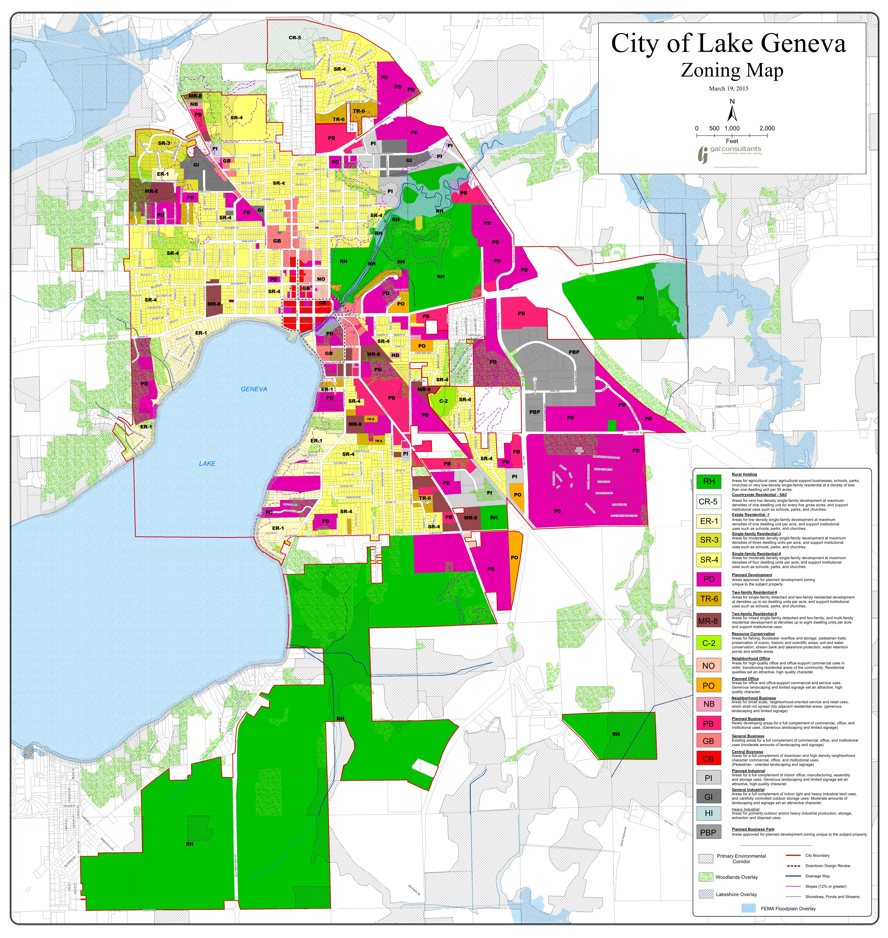
Research and CA/Research and Submittals/02 - Existing Conditions and Code Research/3-19-2015_Zoning_Map_36X38_w_Floodway.jpg
