OpeningDesign/Vacation_Rental/Research and CA/Research and Submittals/02 - Existing Conditions and Code Research/aerial - 100.jpg

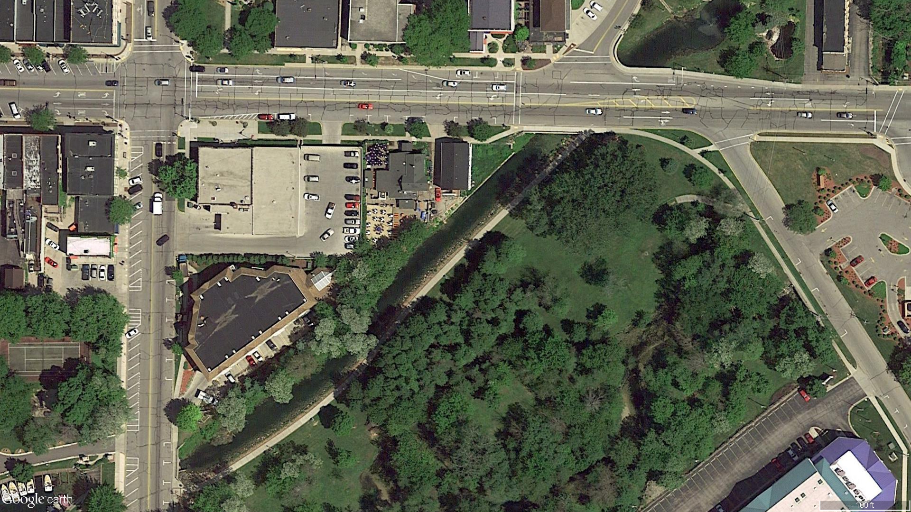
Research and CA/Research and Submittals/02 - Existing Conditions and Code Research/aerial - 100.jpg
