OpeningDesign/Vacation_Rental/Research and CA/Research and Submittals/02 - Existing Conditions and Code Research/chrome_2016-08-26_13-33-07.jpg

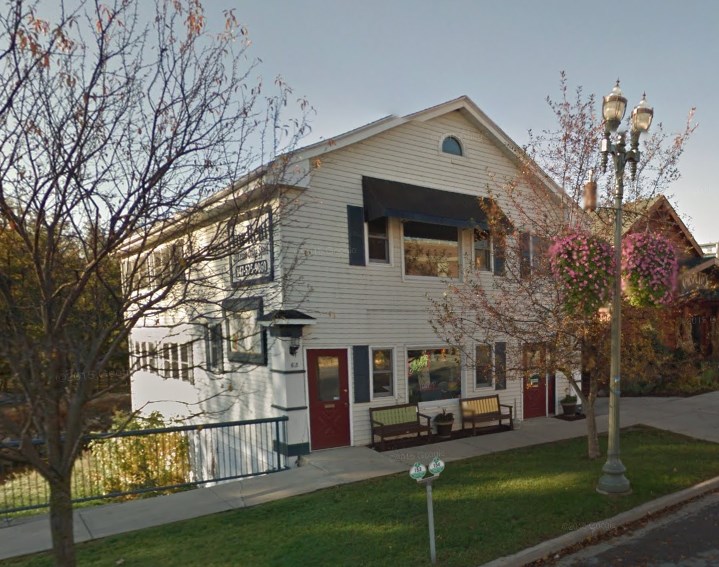
Research and CA/Research and Submittals/02 - Existing Conditions and Code Research/chrome_2016-08-26_13-33-07.jpg
