OpeningDesign/Vacation_Rental/Research and CA/Research and Submittals/02 - Existing Conditions and Code Research/chrome_2016-08-26_13-34-08.png

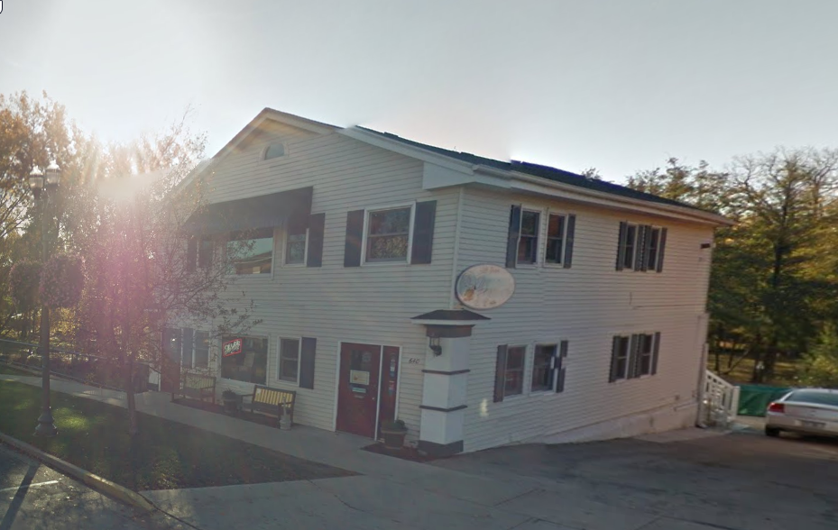
Research and CA/Research and Submittals/02 - Existing Conditions and Code Research/chrome_2016-08-26_13-34-08.png
