OpeningDesign/Vacation_Rental/Research and CA/Research and Submittals/02 - Existing Conditions and Code Research/Site Photos and Videos/20160901/2016-09-01 14.06.57.jpg

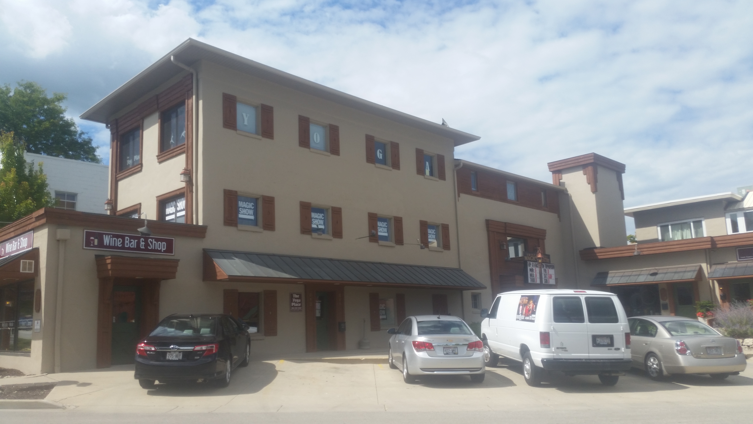
Research and CA/Research and Submittals/02 - Existing Conditions and Code Research/Site Photos and Videos/20160901/2016-09-01 14.06.57.jpg
