OpeningDesign/Vacation_Rental/Research and CA/Research and Submittals/02 - Existing Conditions and Code Research/Site Photos and Videos/fire lane/vlc_2016-10-19_09-33-59.jpg

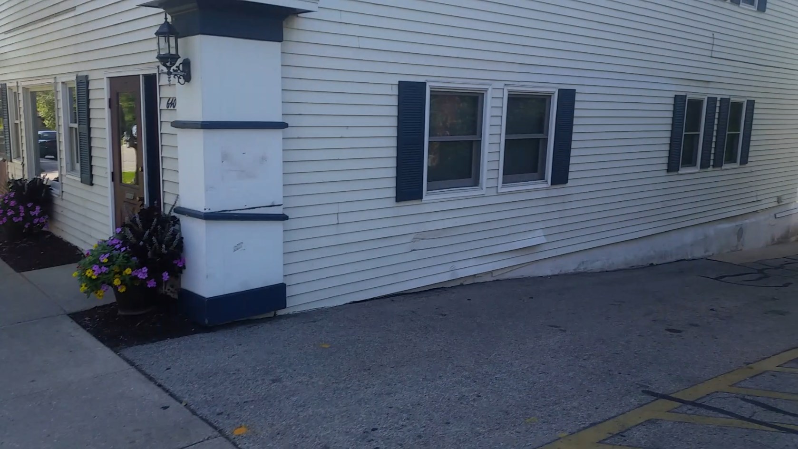
Research and CA/Research and Submittals/02 - Existing Conditions and Code Research/Site Photos and Videos/fire lane/vlc_2016-10-19_09-33-59.jpg
