OpeningDesign/Vacation_Rental/Research and CA/Research and Submittals/02 - Existing Conditions and Code Research/ZOP 00305 - 1984.jpg

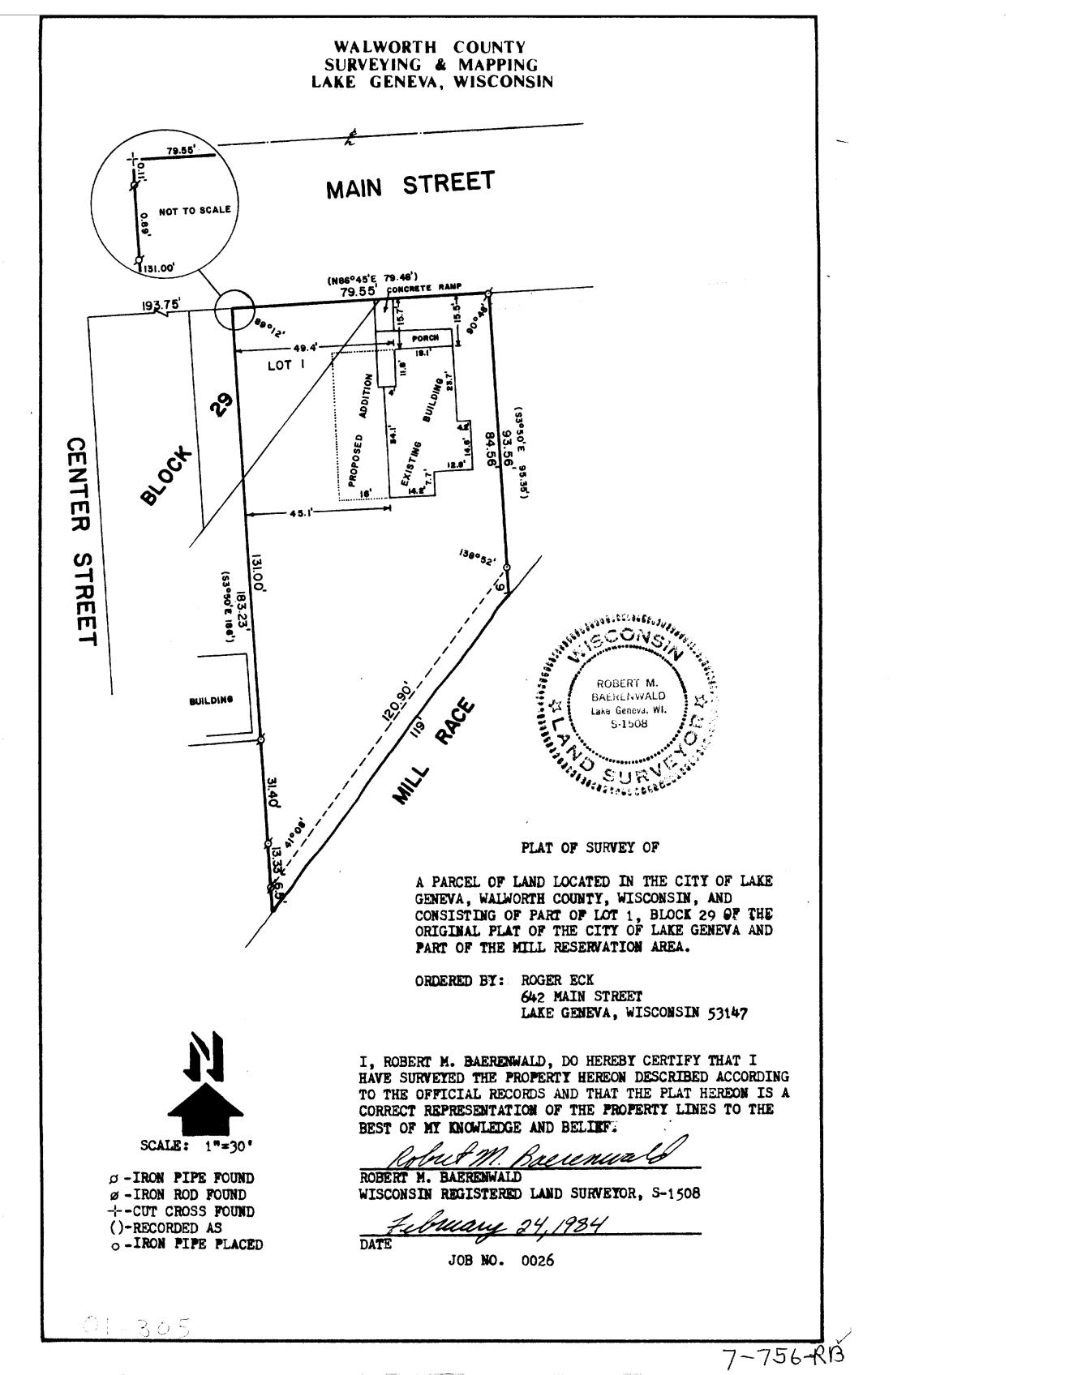
Research and CA/Research and Submittals/02 - Existing Conditions and Code Research/ZOP 00305 - 1984.jpg
