OpeningDesign/Vacation_Rental/Research and CA/Research and Submittals/02 - Existing Conditions and Code Research/ZOP 00306 Survey.jpg

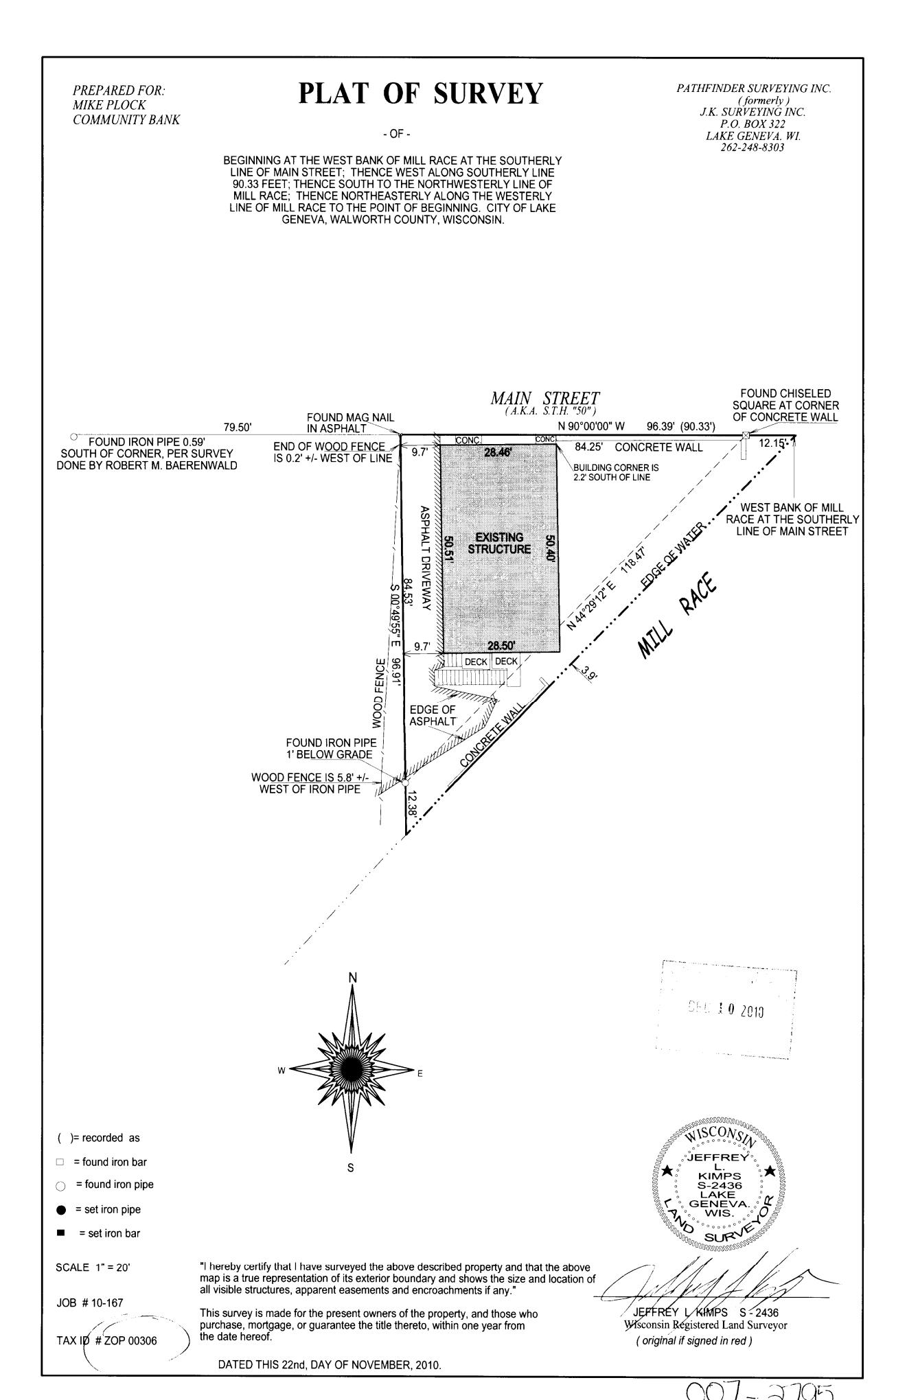
Research and CA/Research and Submittals/02 - Existing Conditions and Code Research/ZOP 00306 Survey.jpg
