OpeningDesign/Vacation_Rental/Research and CA/Research and Submittals/06 - Wood, Plastics, and Composites/Vertical Siding/2016-10-22 14.03.35.jpg

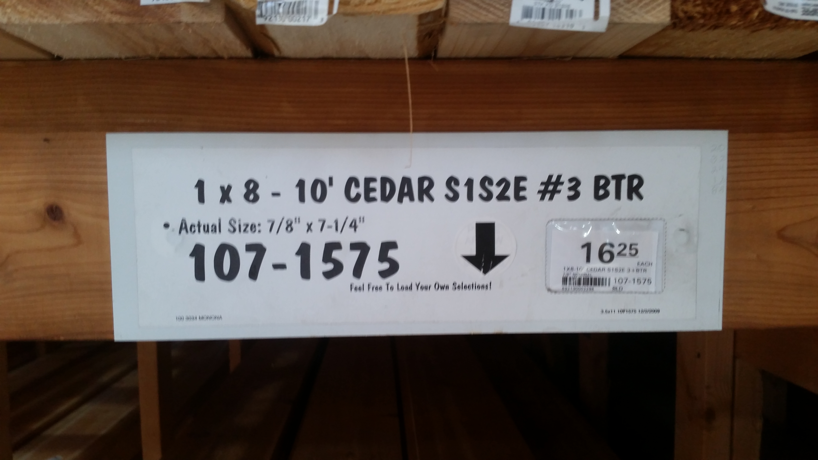
Research and CA/Research and Submittals/06 - Wood, Plastics, and Composites/Vertical Siding/2016-10-22 14.03.35.jpg
