OpeningDesign/Vacation_Rental/Research and CA/Research and Submittals/06 - Wood, Plastics, and Composites/Vertical Siding/Thermory/20171204 - Siding & Decking - 1.jpg

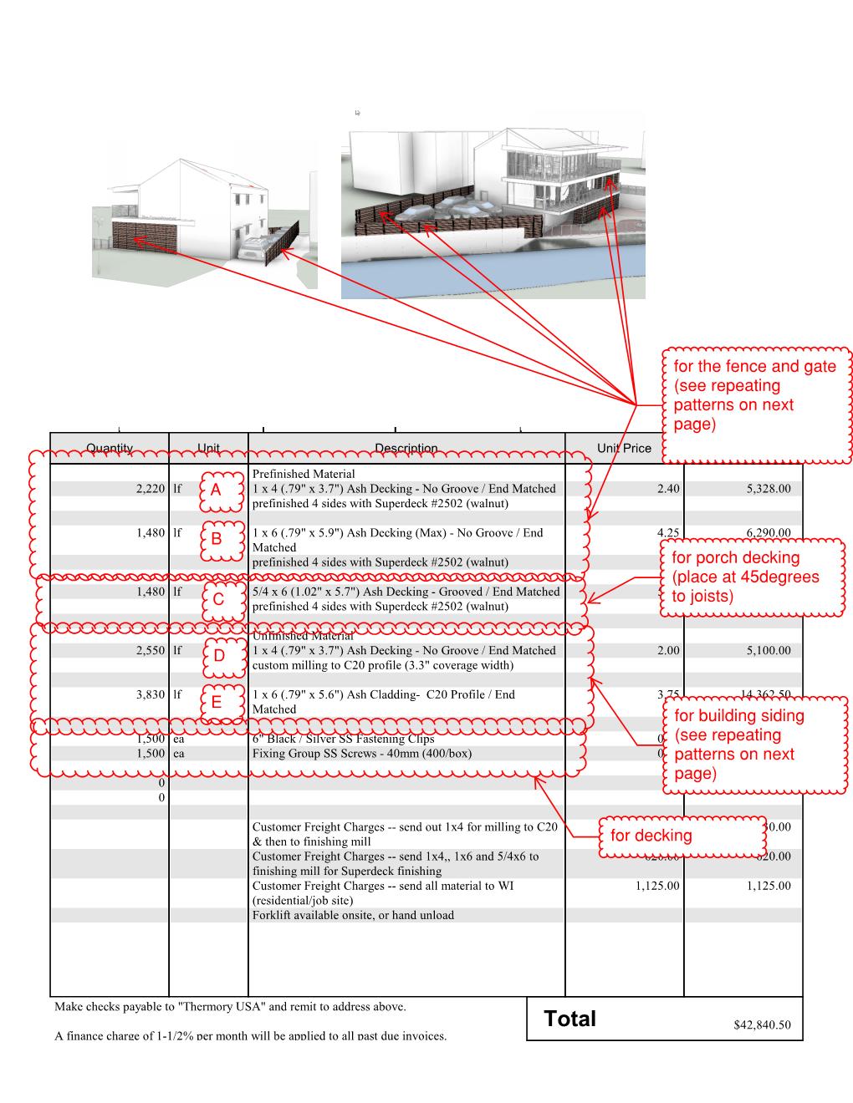
Research and CA/Research and Submittals/06 - Wood, Plastics, and Composites/Vertical Siding/Thermory/20171204 - Siding & Decking - 1.jpg
