OpeningDesign/Vacation_Rental/Research and CA/Site Reports and Photos/20171212/East Facade.jpeg

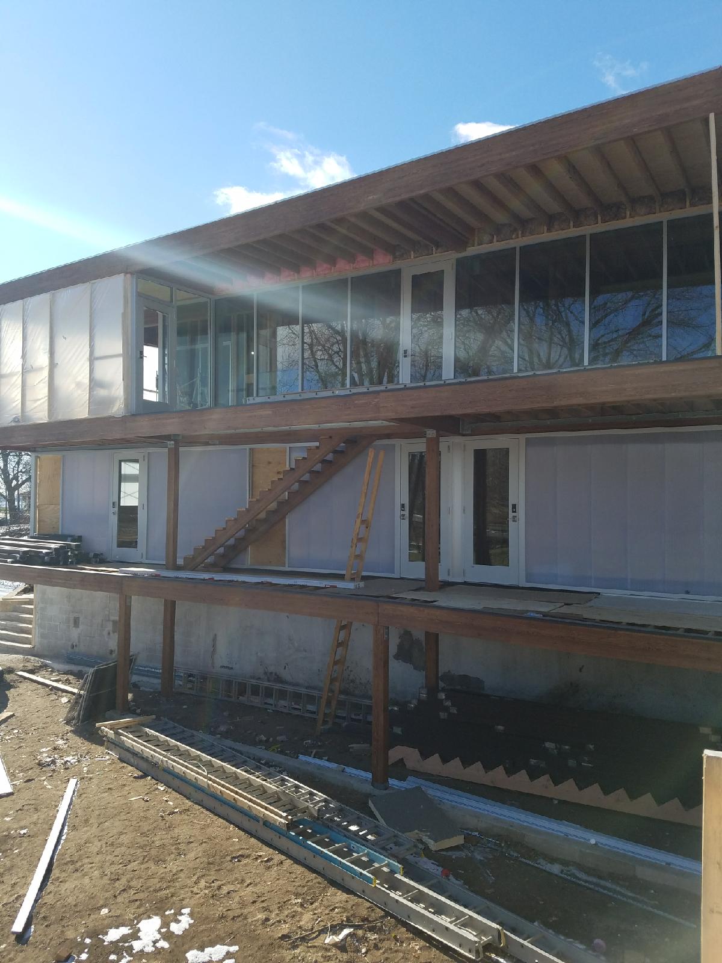
Research and CA/Site Reports and Photos/20171212/East Facade.jpeg
