OpeningDesign/Vacation_Rental/Research and CA/Site Reports and Photos/20180108 - glulam cracks/unnamed (2).jpg

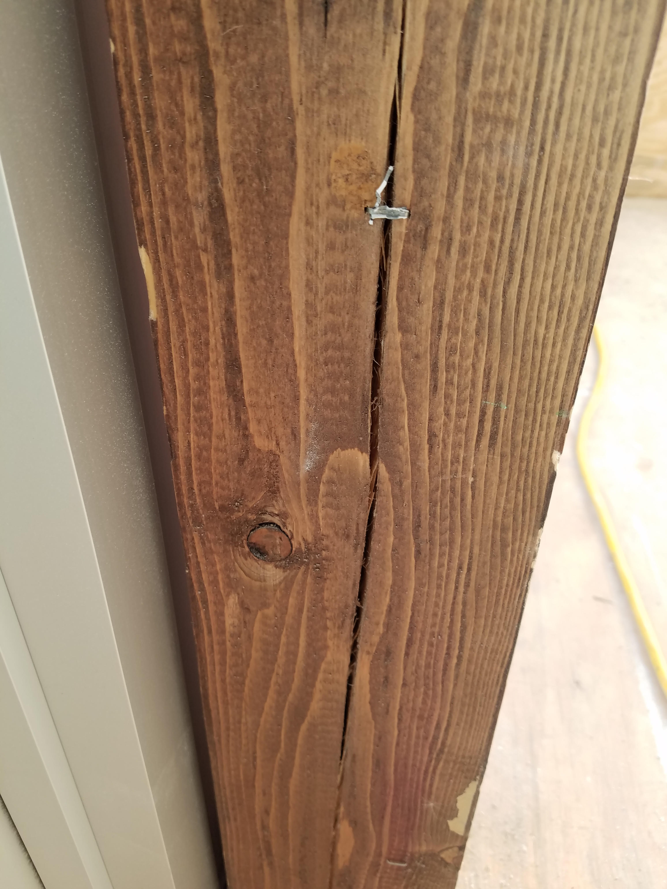
Research and CA/Site Reports and Photos/20180108 - glulam cracks/unnamed (2).jpg
