OpeningDesign/Vacation_Rental/Research and CA/Site Reports and Photos/20180108 - glulam cracks/unnamed.jpg

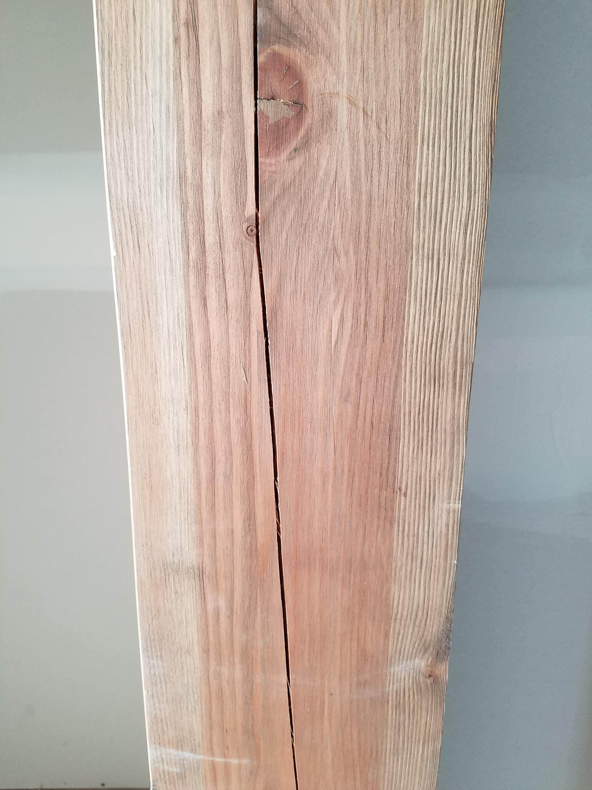
Research and CA/Site Reports and Photos/20180108 - glulam cracks/unnamed.jpg
