OpeningDesign/Vacation_Rental/Research and CA/Site Reports and Photos/20180212/2018-02-10 15.50.50.jpg

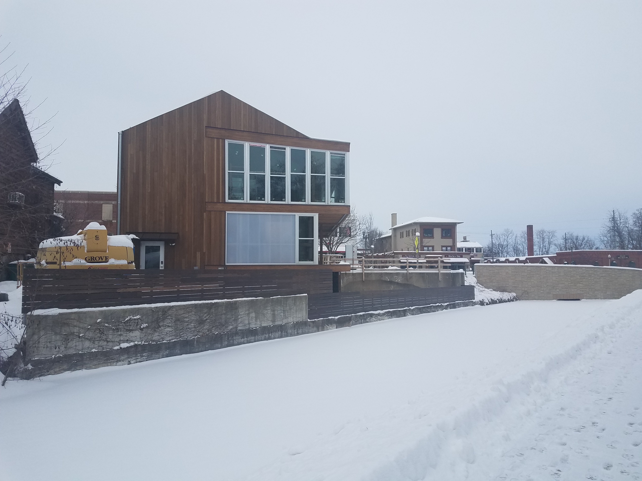
Research and CA/Site Reports and Photos/20180212/2018-02-10 15.50.50.jpg
