OpeningDesign/Vacation_Rental/Research and CA/Site Reports and Photos/20180212/2018-02-10 16.08.14.jpg

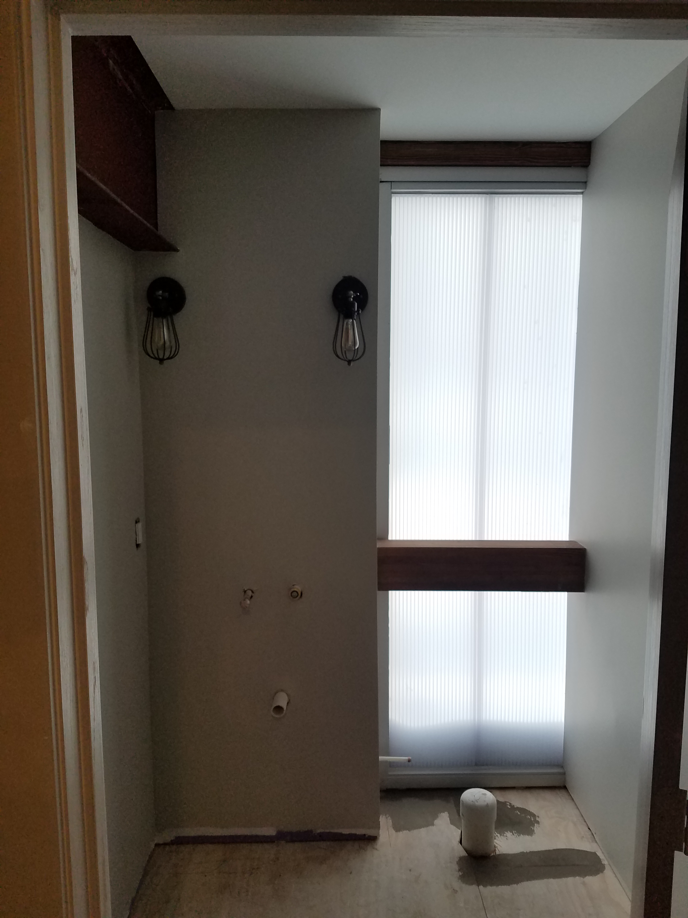
Research and CA/Site Reports and Photos/20180212/2018-02-10 16.08.14.jpg
