OpeningDesign/Vacation_Rental/Transfer/20160918 - floor plan options - owner review/20160919 - Lake Geneva - Vacation Rental Page 005.jpg

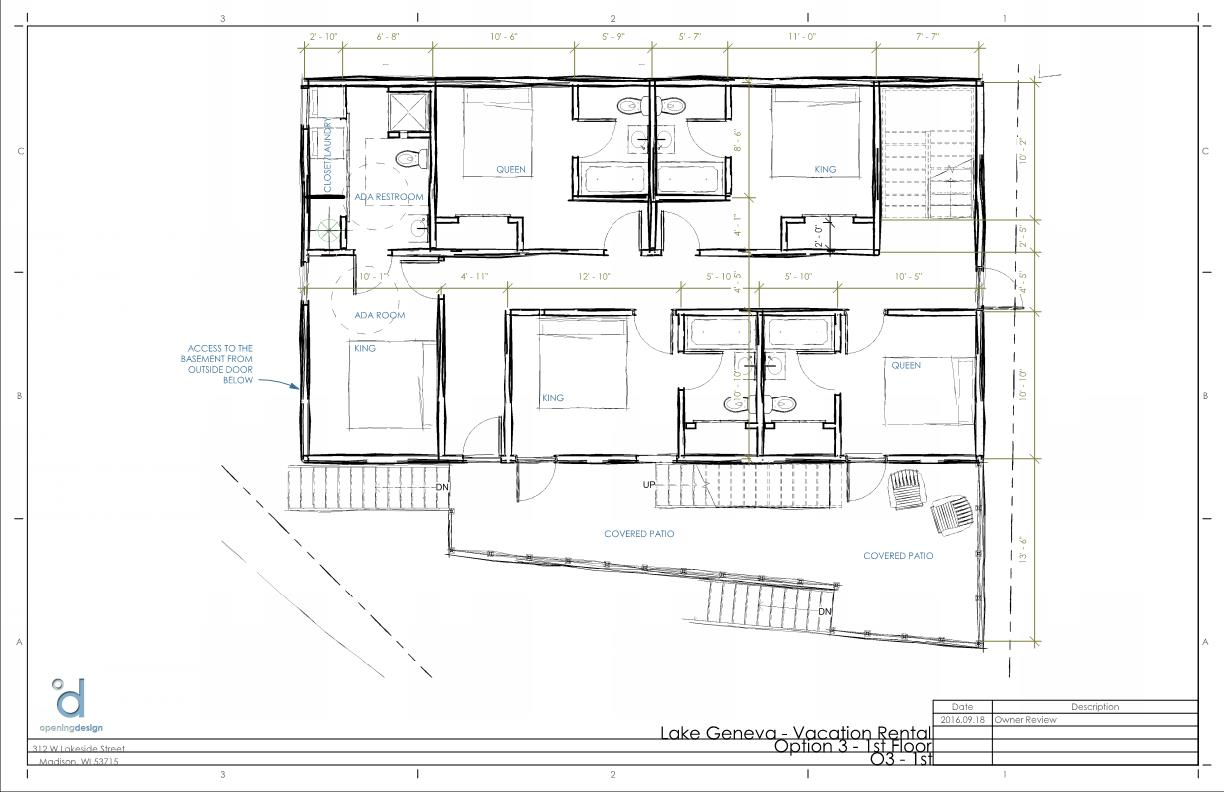
Transfer/20160918 - floor plan options - owner review/20160919 - Lake Geneva - Vacation Rental Page 005.jpg
