OpeningDesign/Vacation_Rental/Transfer/20160927 - city submission - pre-review/renderings/8.png

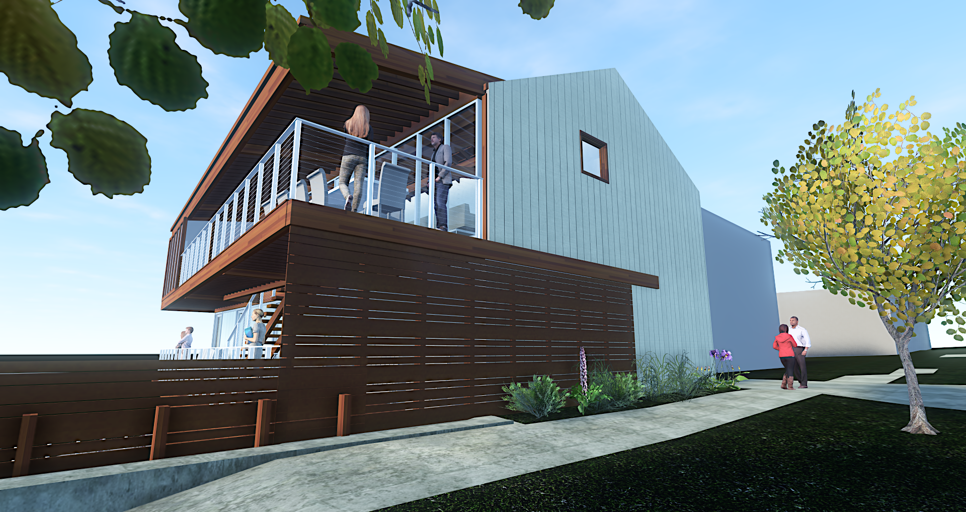
Transfer/20160927 - city submission - pre-review/renderings/8.png
