OpeningDesign/Vacation_Rental/Transfer/20160927 - city submission - pre-review/renderings/Enscape_2016-09-26-15-20-03.png

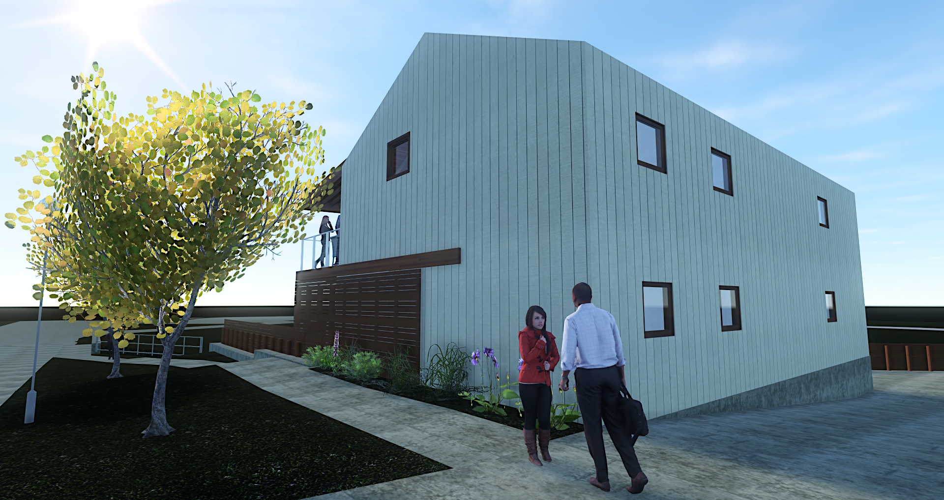
Transfer/20160927 - city submission - pre-review/renderings/Enscape_2016-09-26-15-20-03.png
