OpeningDesign/Vacation_Rental/Transfer/20160928 - owner review/20160928 - LF Vacation Rental Page 009.jpg

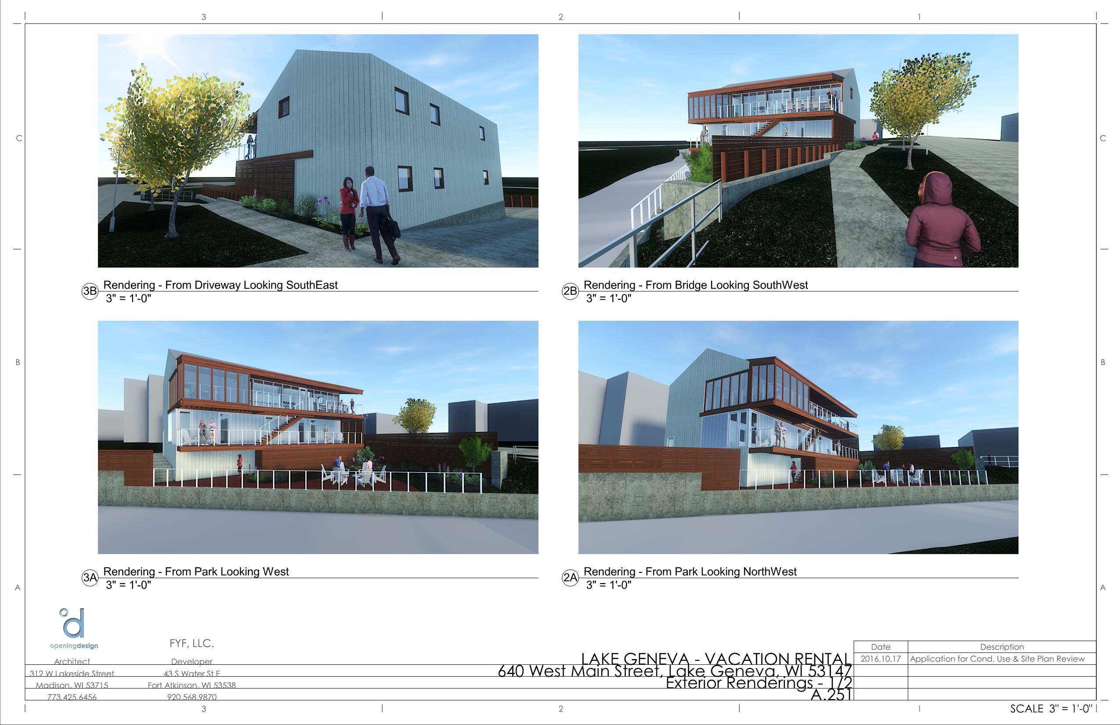
Transfer/20160928 - owner review/20160928 - LF Vacation Rental Page 009.jpg
