OpeningDesign/Vacation_Rental/Transfer/20170327 - jpgs to owner/Enscape_2016-09-29-14-08-28.png

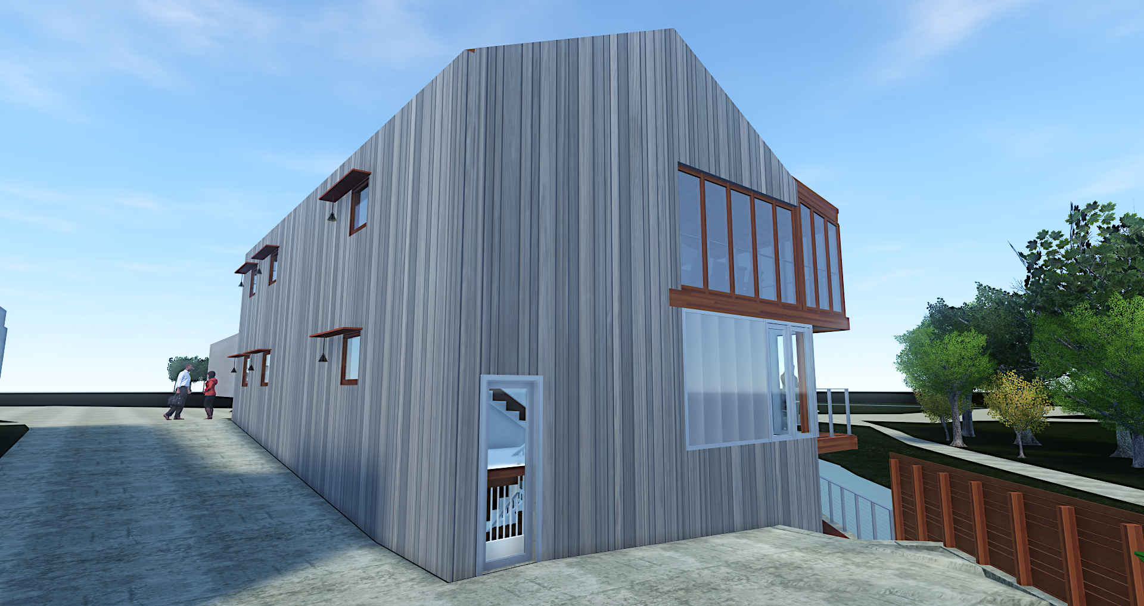
Transfer/20170327 - jpgs to owner/Enscape_2016-09-29-14-08-28.png
