OpeningDesign/Vacation_Rental/Transfer/20170509 - from regis for review/0.PNG

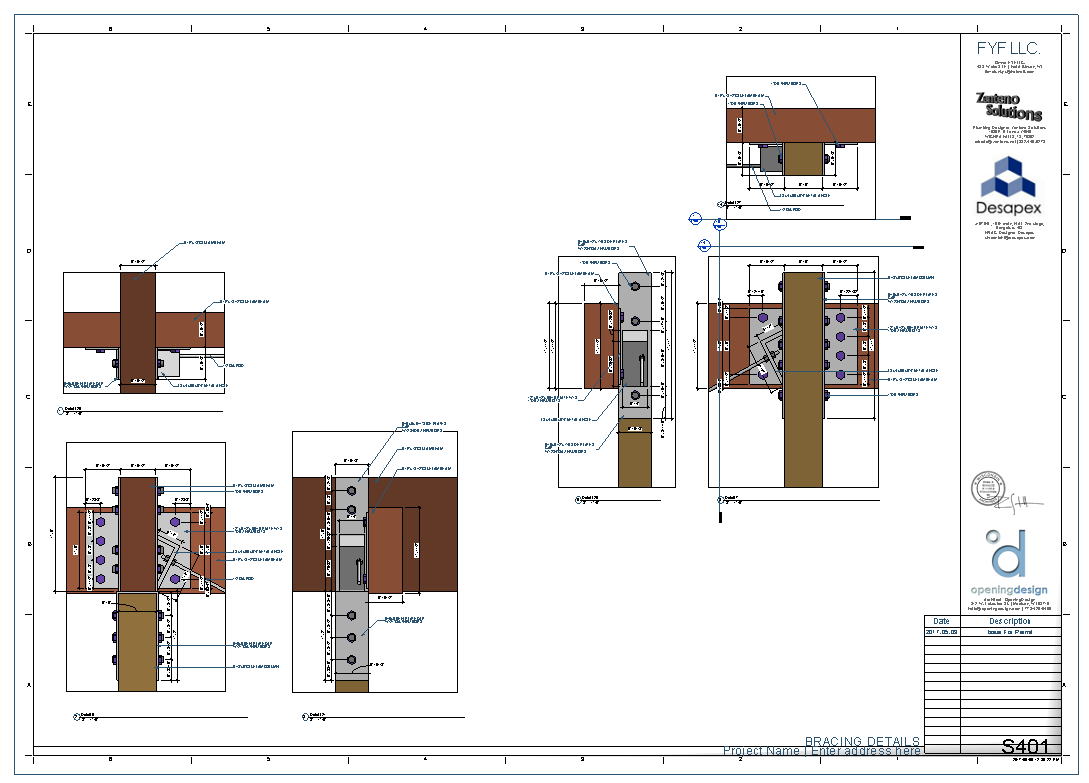
Transfer/20170509 - from regis for review/0.PNG
