OpeningDesign/Vacation_Rental/Transfer/20170509 - from regis for review/1.PNG

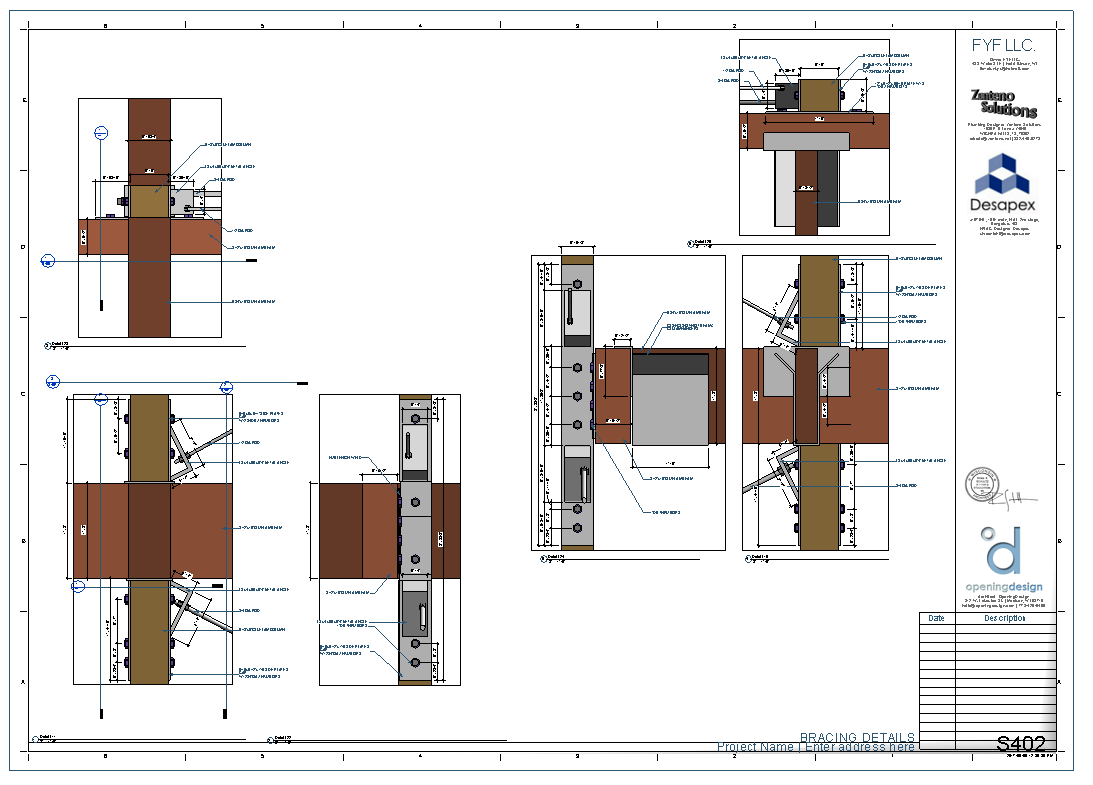
Transfer/20170509 - from regis for review/1.PNG
