OpeningDesign/Vacation_Rental/Transfer/20170509 - from regis for review/3 in scale.PNG

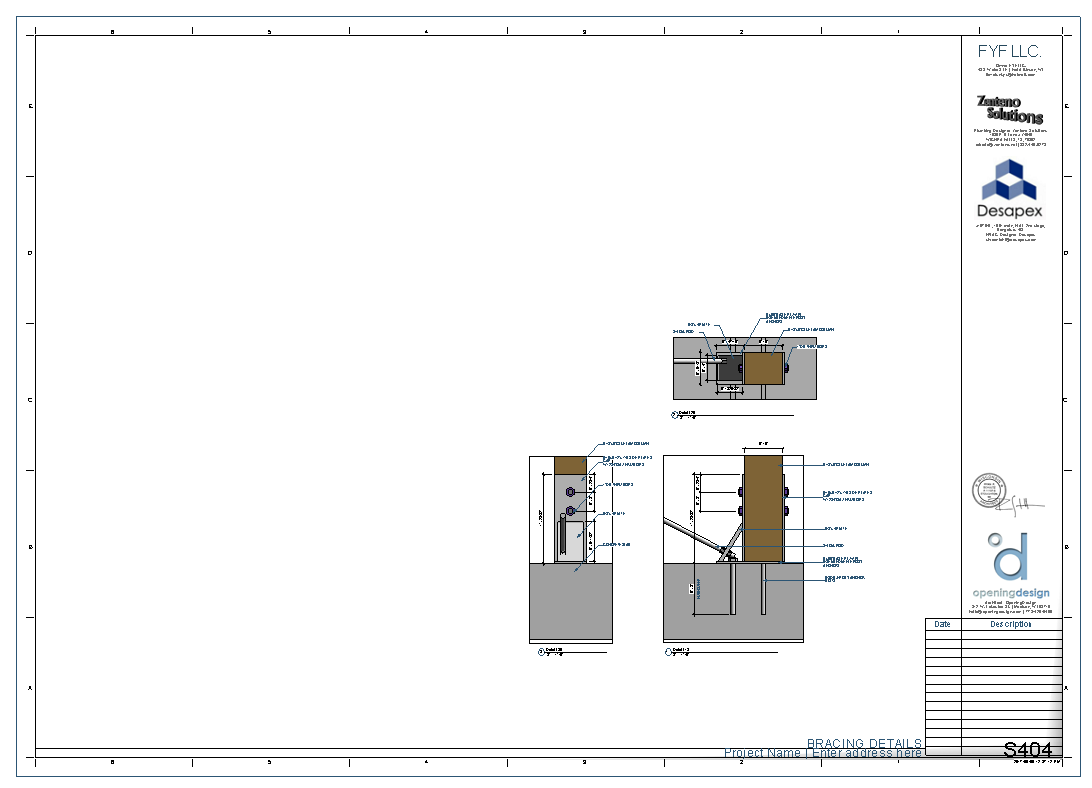
Transfer/20170509 - from regis for review/3 in scale.PNG
