OpeningDesign/Vacation_Rental/Transfer/20170509 - from regis for review/3.PNG

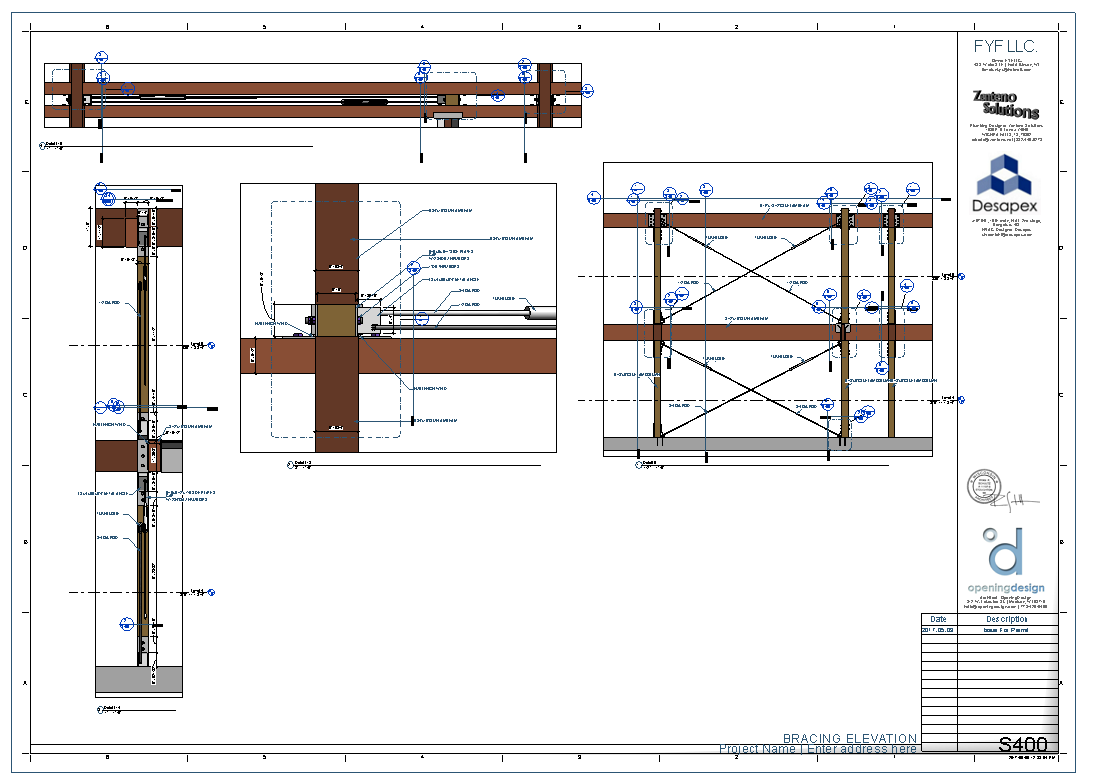
Transfer/20170509 - from regis for review/3.PNG
