OpeningDesign/Vacation_Rental/Transfer/20170713 - ASK-001 - Foundation Plan/20170713 - ASK-001 - Foundation Plan.jpg

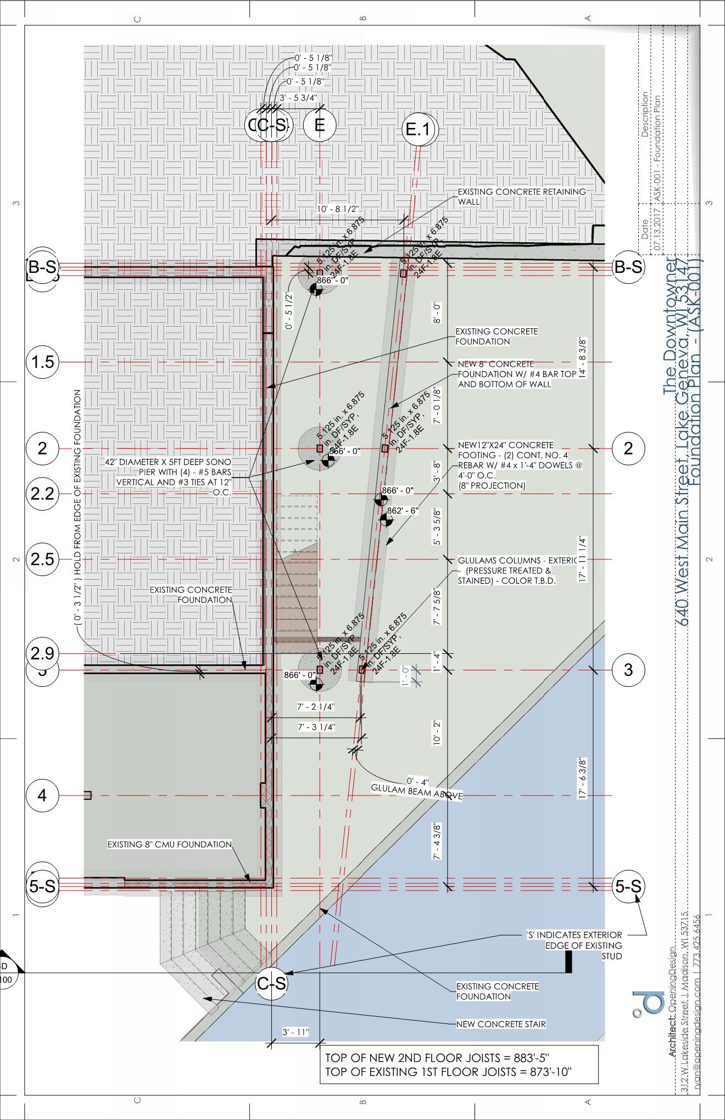
Transfer/20170713 - ASK-001 - Foundation Plan/20170713 - ASK-001 - Foundation Plan.jpg
