OpeningDesign/Vacation_Rental/Transfer/20171011 - to GC - Lateral Bracket Clarification/Resized_20171010_134201.jpeg

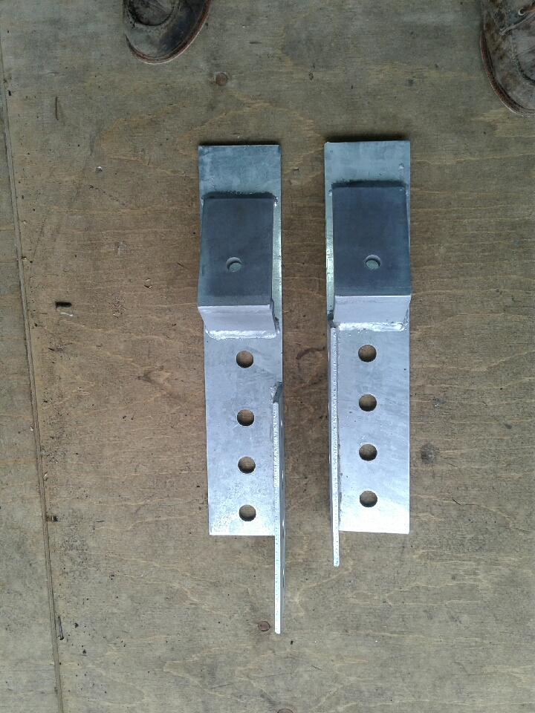
Transfer/20171011 - to GC - Lateral Bracket Clarification/Resized_20171010_134201.jpeg
