OpeningDesign/Vacation_Rental/Transfer/20171011 - to GC - Lateral Bracket Clarification/Revu_2017-10-11_12-00-46.png

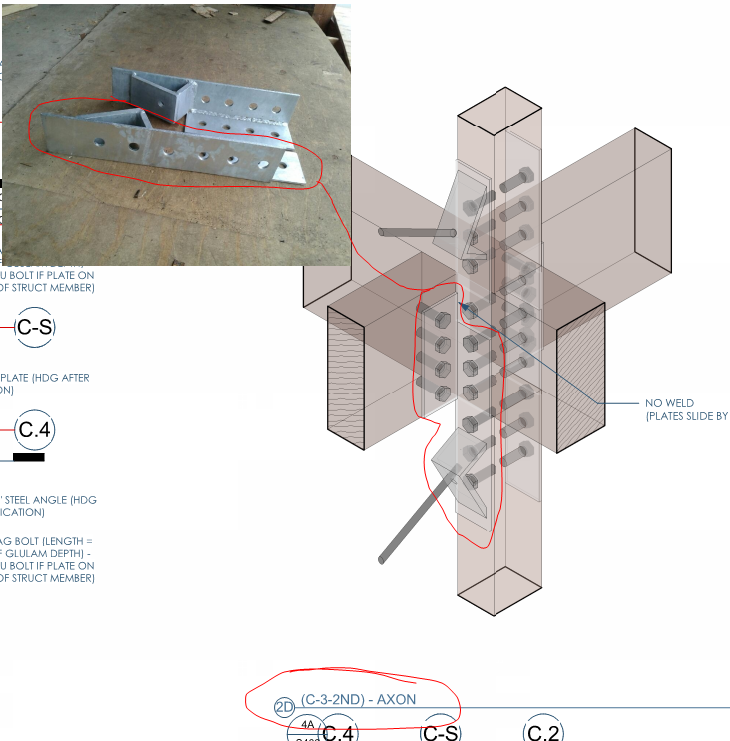
Transfer/20171011 - to GC - Lateral Bracket Clarification/Revu_2017-10-11_12-00-46.png
