OpeningDesign/Vacation_Rental/Transfer/20171011 - to GC - Lateral Bracket Clarification/Revu_2017-10-11_12-01-23.png

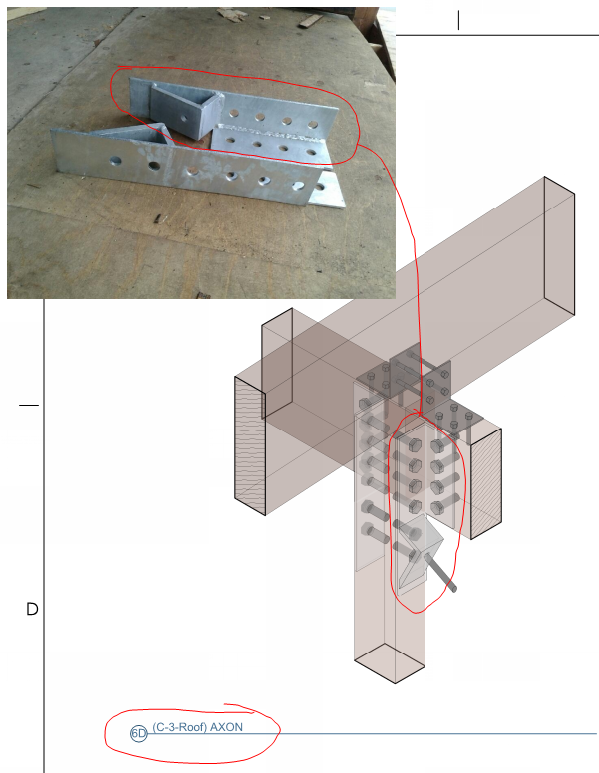
Transfer/20171011 - to GC - Lateral Bracket Clarification/Revu_2017-10-11_12-01-23.png
