OpeningDesign/Vacation_Rental/Transfer/20171011 - to GC - Lateral Bracket Clarification/Revu_2017-10-11_12-14-20.png

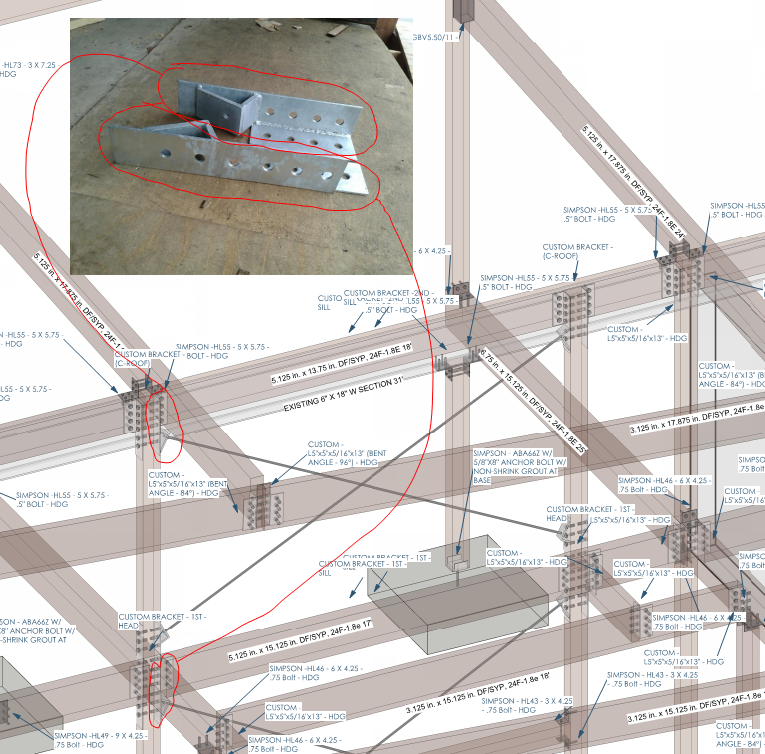
Transfer/20171011 - to GC - Lateral Bracket Clarification/Revu_2017-10-11_12-14-20.png
