OpeningDesign/Vacation_Rental/Transfer/20171222 - fence design - owner review/20171223 - The Downtowner - Fence Details Page 003.jpg

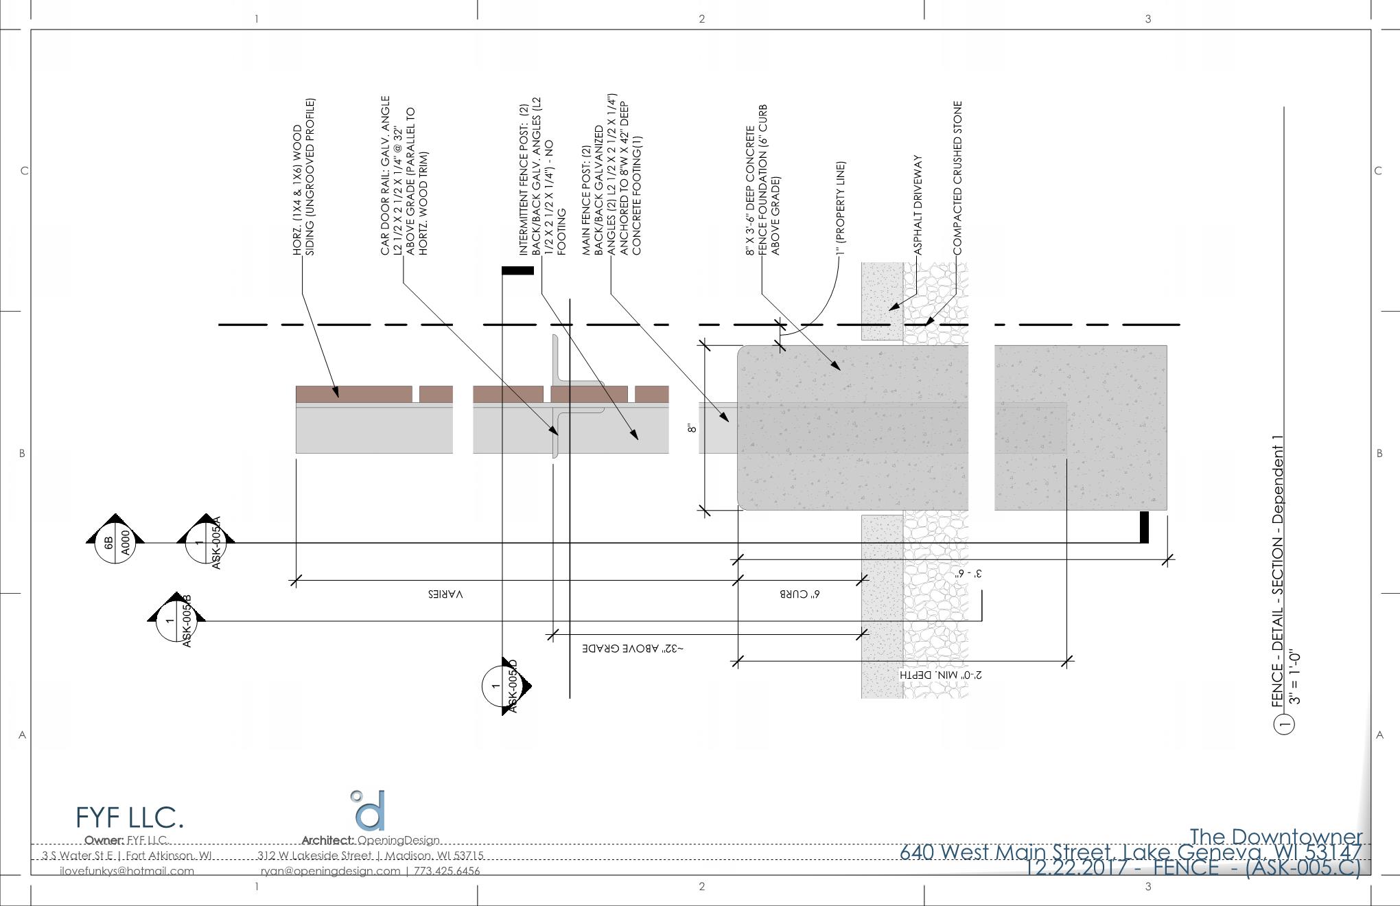
Transfer/20171222 - fence design - owner review/20171223 - The Downtowner - Fence Details Page 003.jpg
