OpeningDesign/Vacation_Rental/Transfer/20171222 - fence design - owner review/The_Downtowner_ARCH.rvt_2017-Dec-23_03-04-55PM-000_FENCE_PERSPECTIVE_1_jpg.jpg

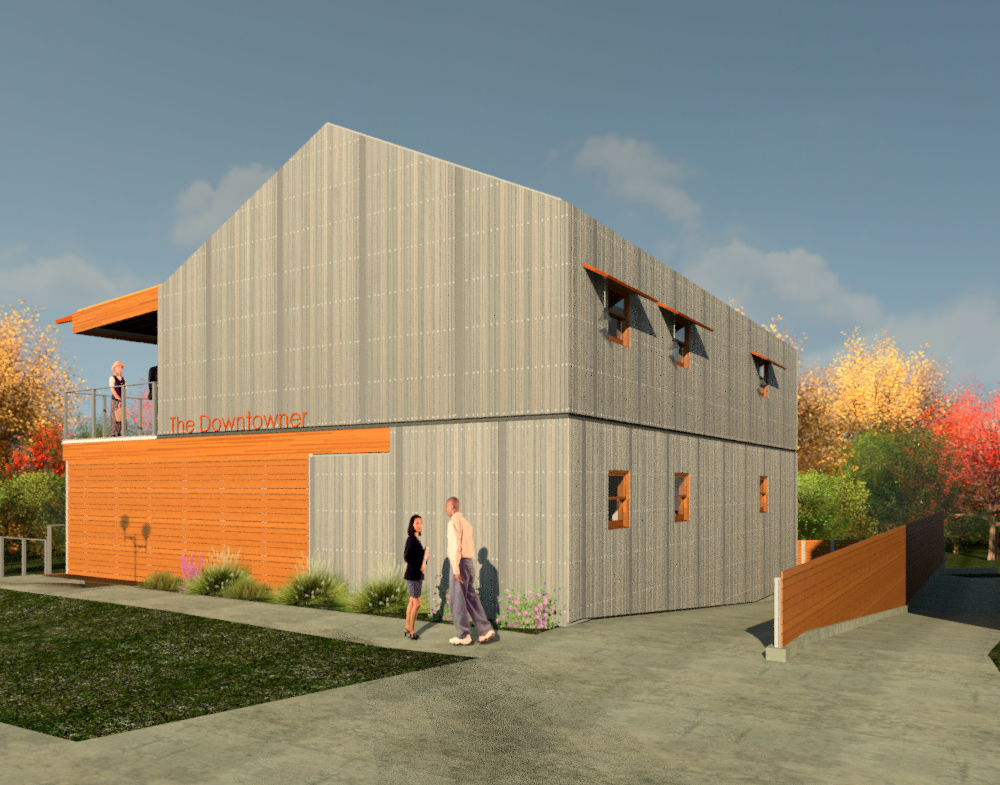
Transfer/20171222 - fence design - owner review/The_Downtowner_ARCH.rvt_2017-Dec-23_03-04-55PM-000_FENCE_PERSPECTIVE_1_jpg.jpg
