OpeningDesign/Vacation_Rental/Transfer/20180205 - to owner - signage for review/Enscape_2018-02-05-10-50-24.png

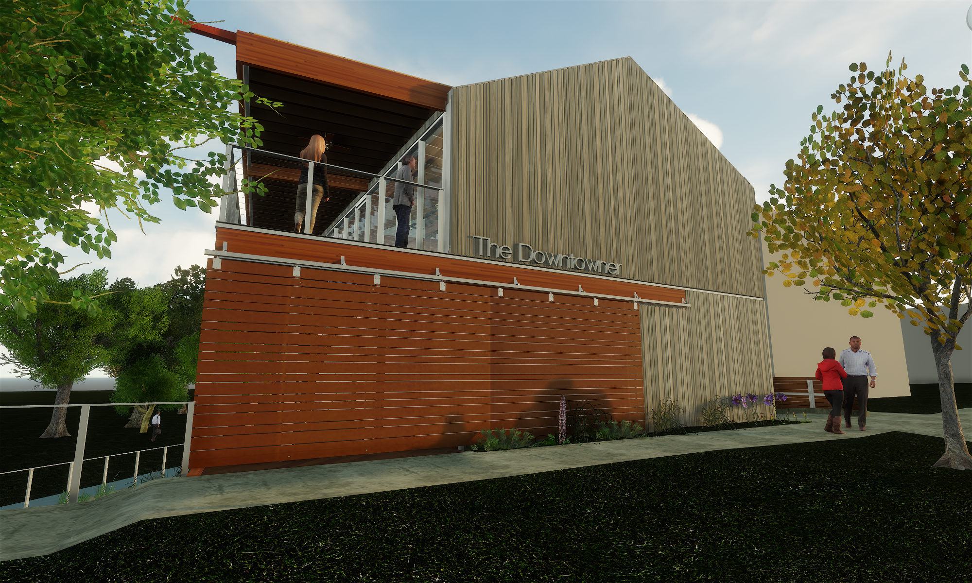
Transfer/20180205 - to owner - signage for review/Enscape_2018-02-05-10-50-24.png
