OpeningDesign/Vacation_Rental/Transfer/20180212 - Combined CD set & site photos/axon.jpg

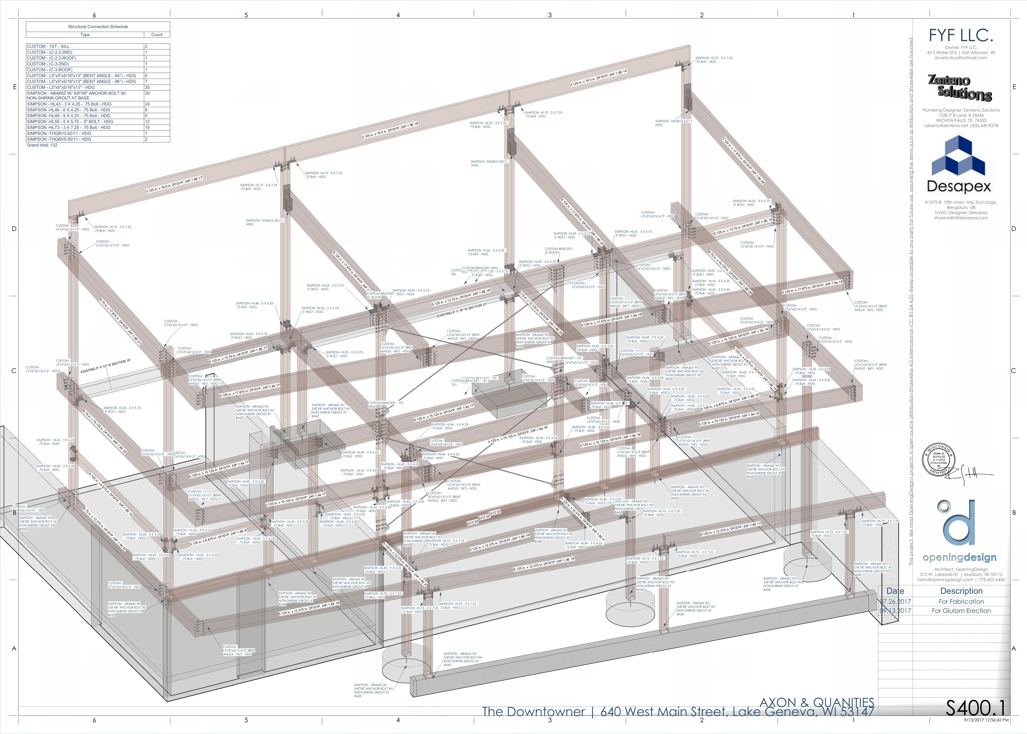
Transfer/20180212 - Combined CD set & site photos/axon.jpg
