OpeningDesign/Vacation_Rental/Transfer/20170327 - jpgs to owner/20161102 - Drawings - Plan Commission - Review of Materials and Fence Page 005.jpg

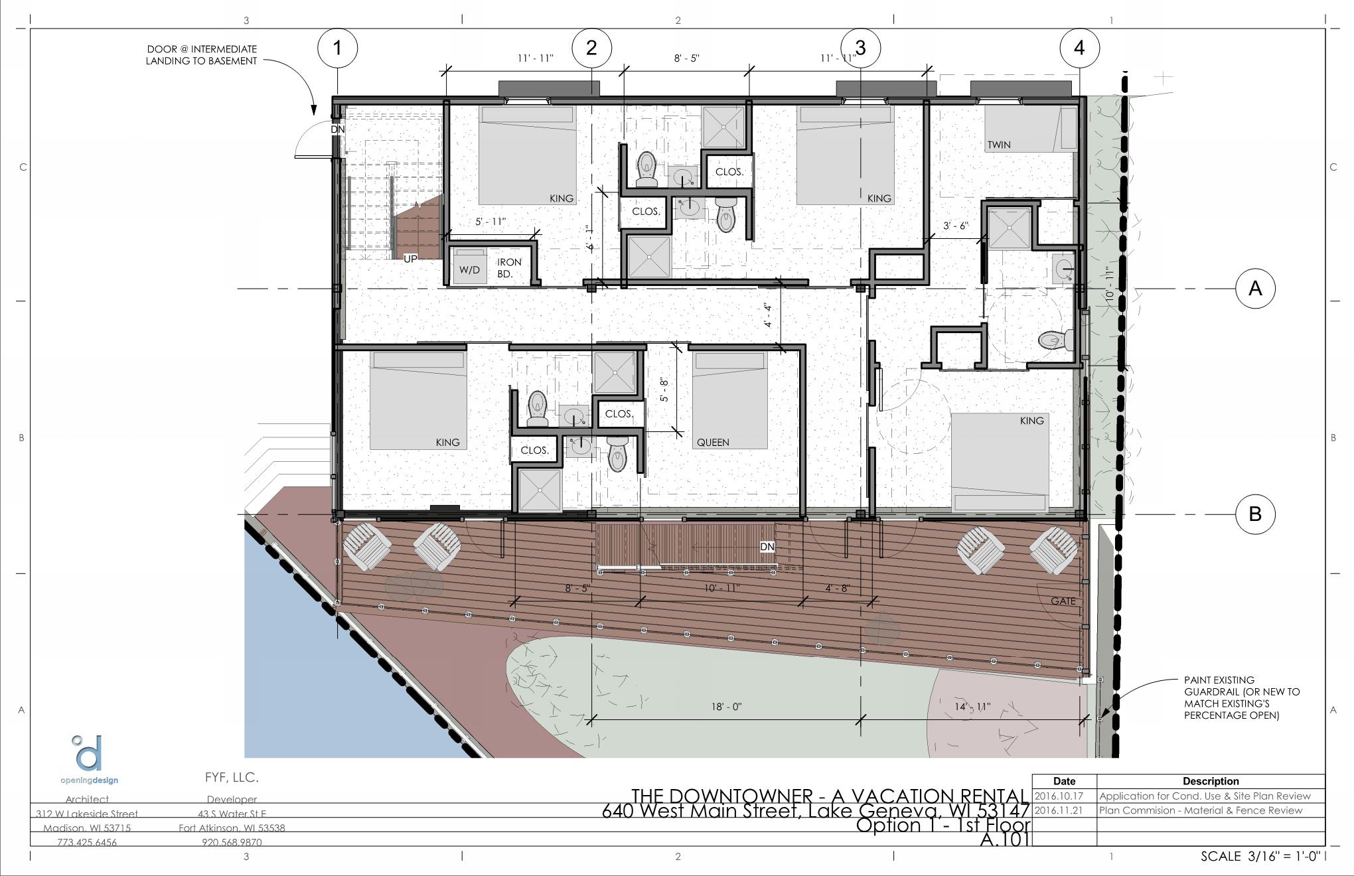
Transfer/20170327 - jpgs to owner/20161102 - Drawings - Plan Commission - Review of Materials and Fence Page 005.jpg
