OpeningDesign/Vacation_Rental/Transfer/20170924 - Marketing Materials/1st Floor Plan.jpg

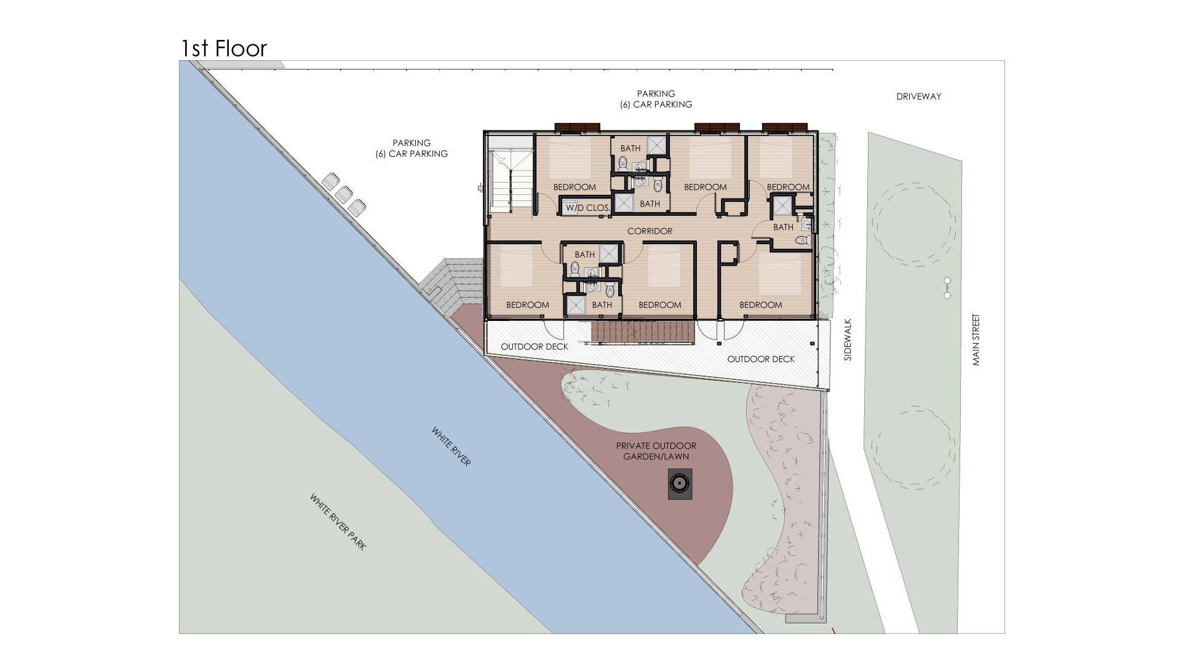
Transfer/20170924 - Marketing Materials/1st Floor Plan.jpg
