OpeningDesign/Vacation_Rental/Transfer/20160930 - Final Printing for City Review/20160930 - Drawings - Conditional Use and Site Review Approval - Vacation Rental Page 010.jpg

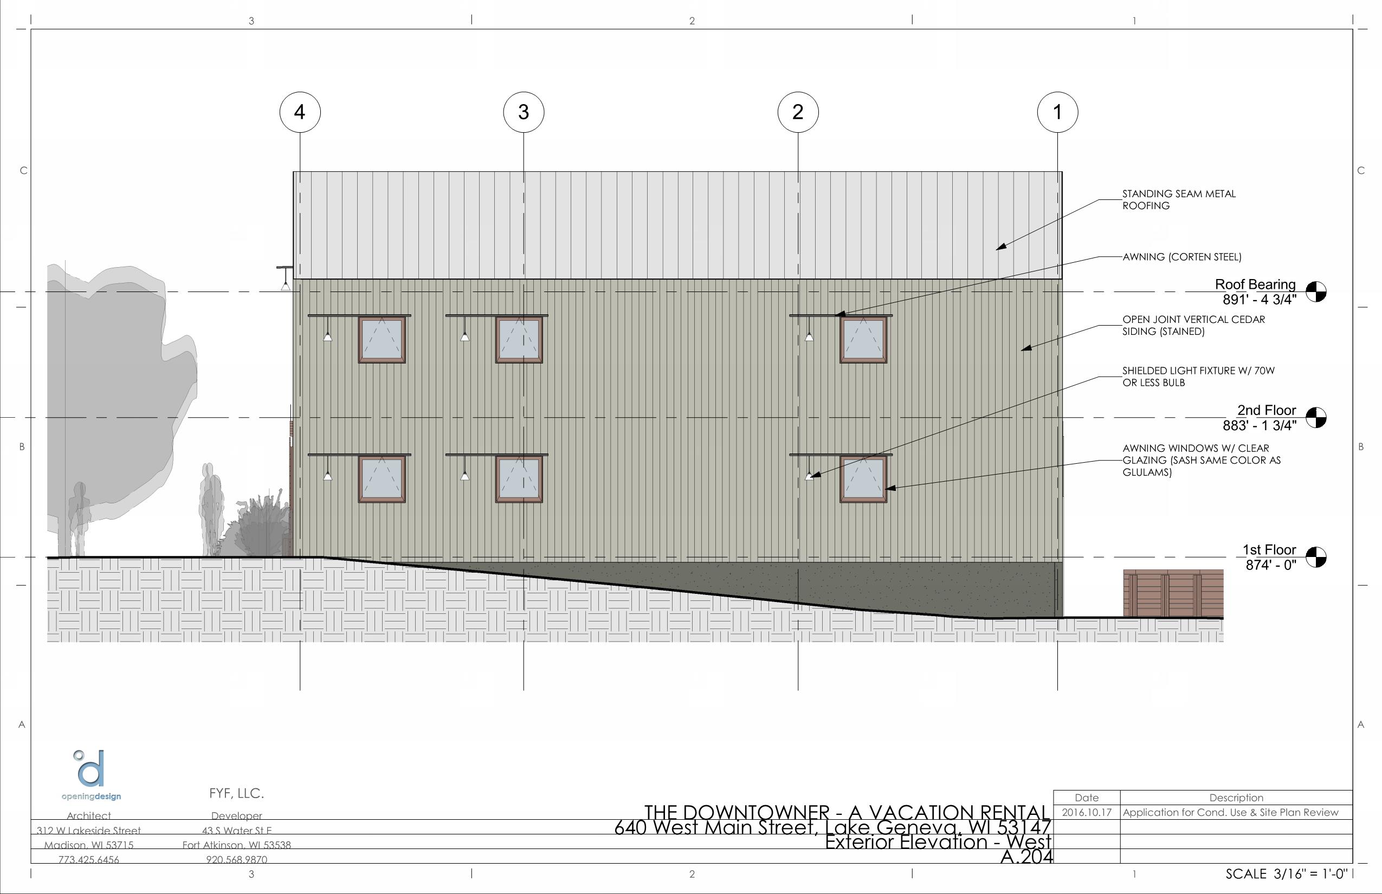
Transfer/20160930 - Final Printing for City Review/20160930 - Drawings - Conditional Use and Site Review Approval - Vacation Rental Page 010.jpg
