OpeningDesign/Vacation_Rental/Transfer/20170726 - to Metal Fabricator - connection shop drawings/Enscape_2017-07-27-08-49-24.png

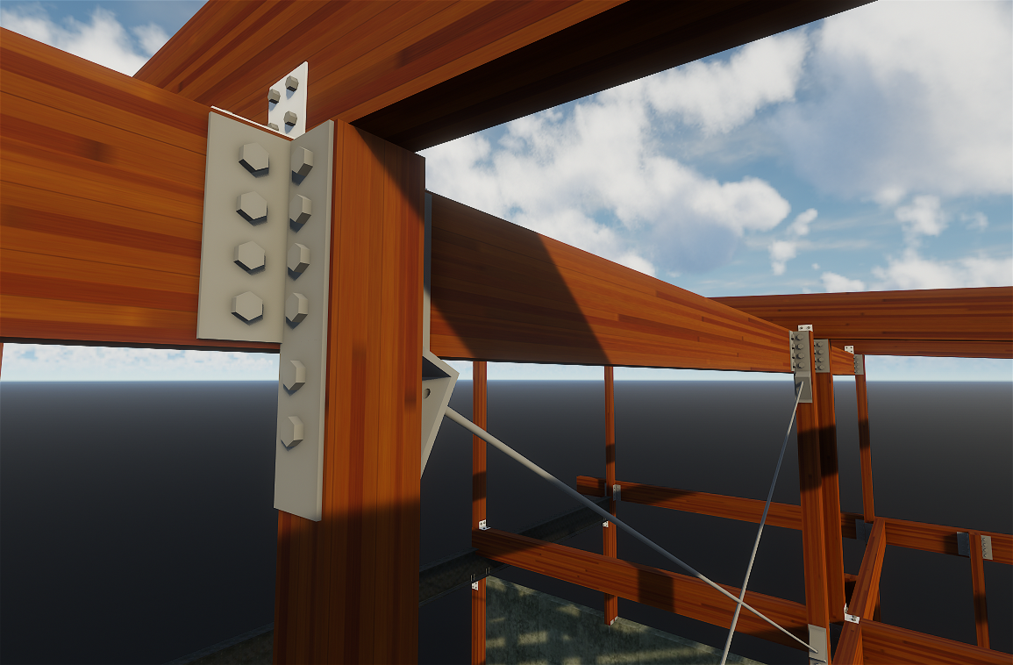
Transfer/20170726 - to Metal Fabricator - connection shop drawings/Enscape_2017-07-27-08-49-24.png
