OpeningDesign/Vacation_Rental/Transfer/20170519 ----- ISSUE FOR BID & PERMIT -------/The Downtowner_ARCH - Sheet - A400 - EXTERIOR DETAILS.pdf

A.S

B

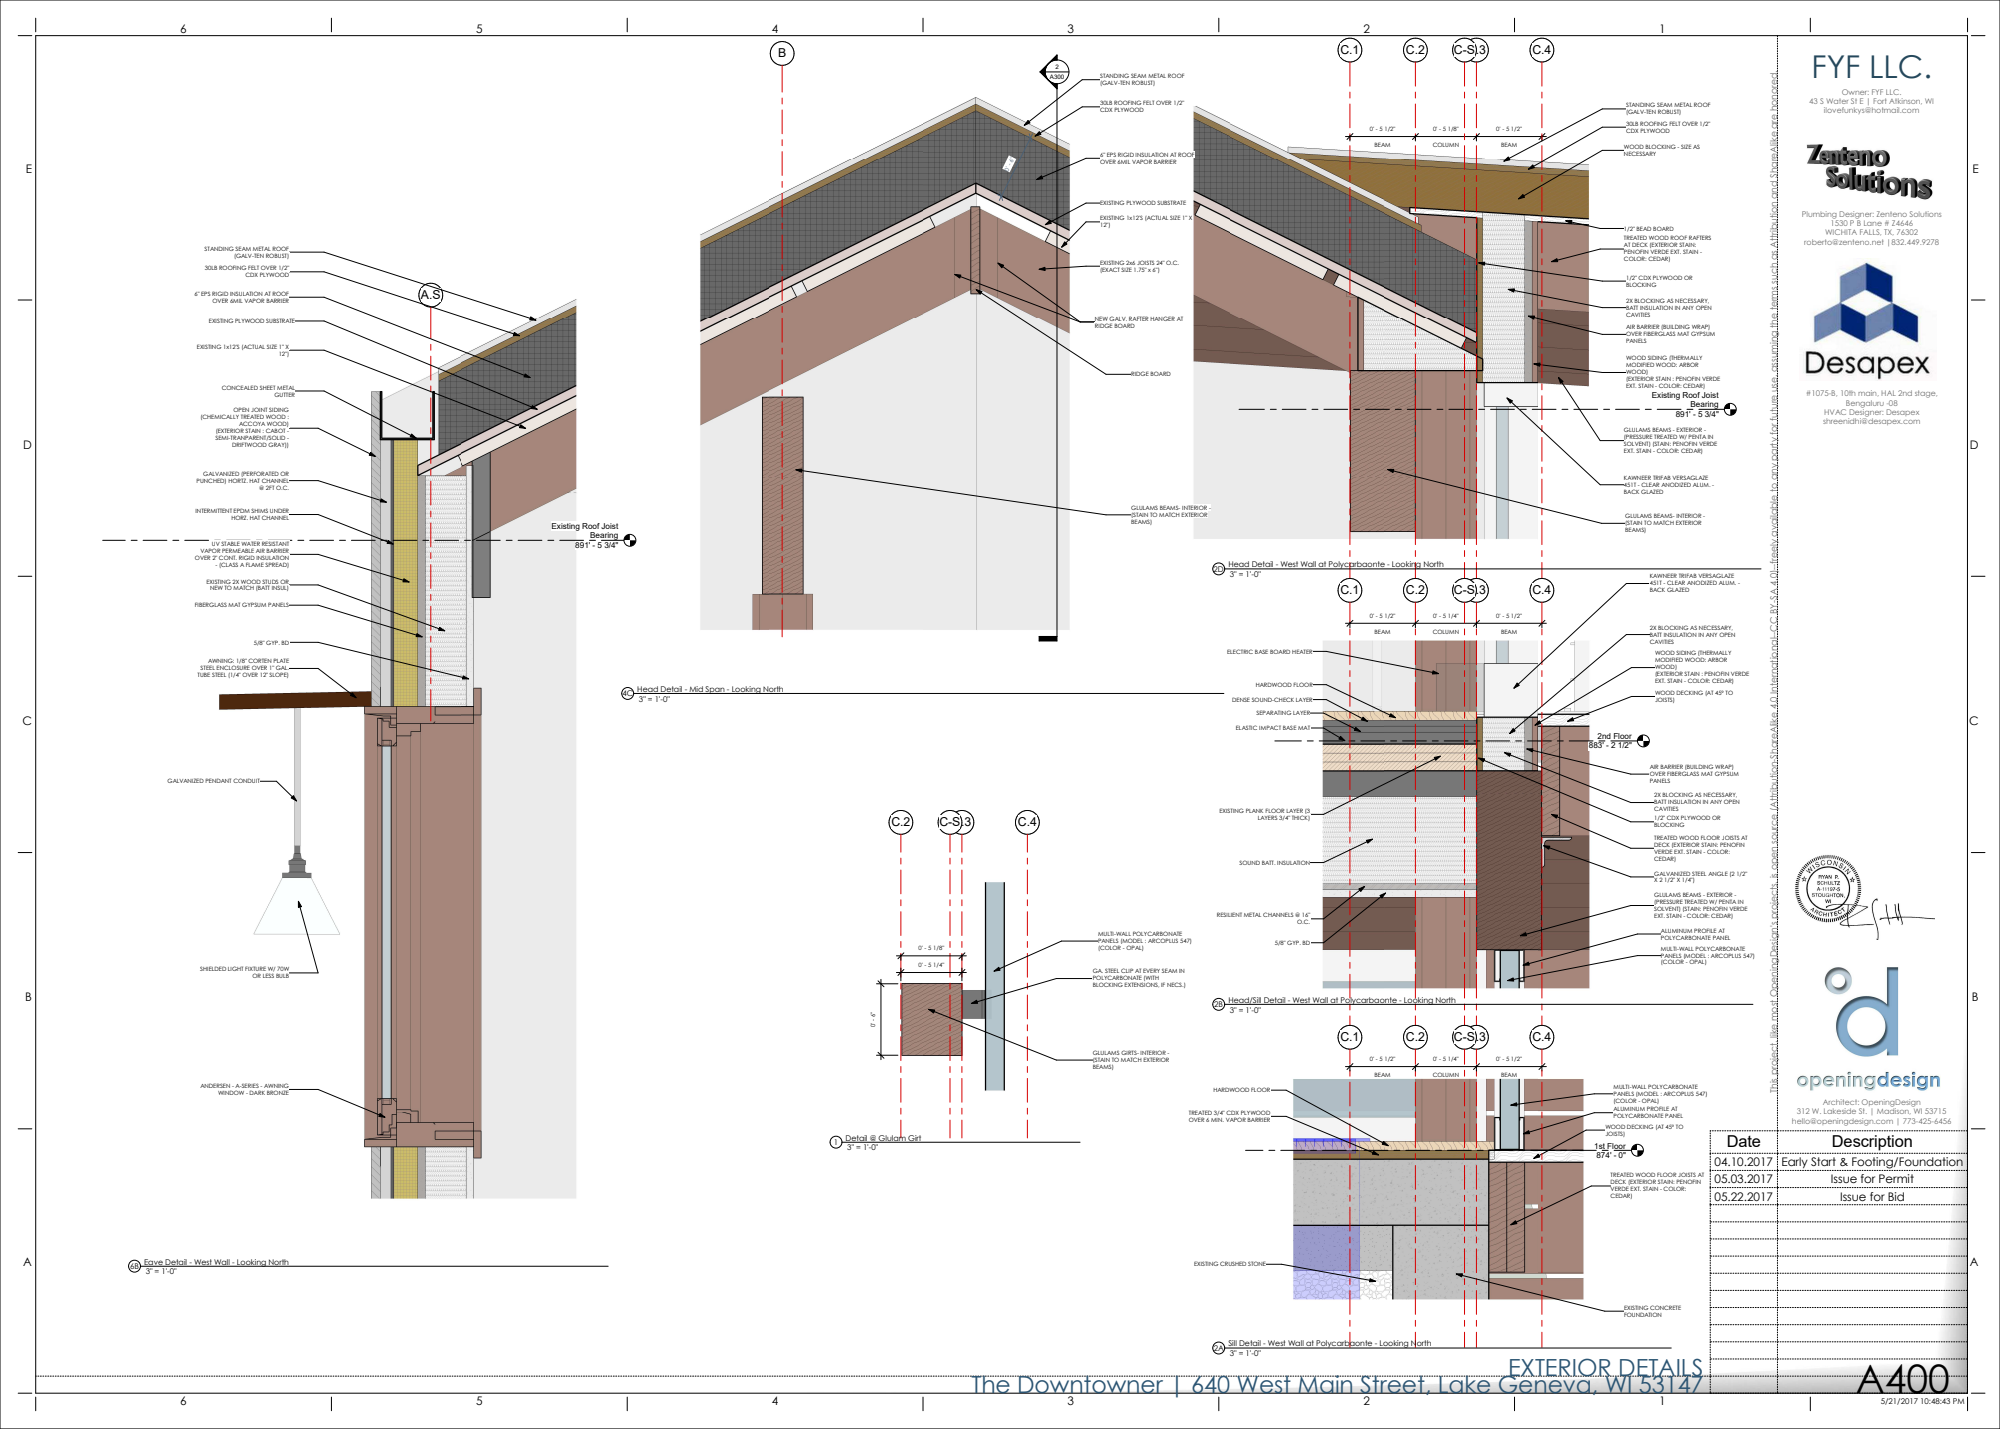
[picture p239: page 1]
Bearing 891' - 5 3/4"; ACCOYA WOOD); GUTTER; 5/8" GYP. BD; CDX PLYWOOD; RIDGE BOARD; EXISTING 2x6 JOISTS 24" O.C. (EXACT SIZE 1.75" x 6"); BEAM; COLUMN; 2nd Floor 883' - 2 1/2"; LAYERS 3/4" THICK); HARDWOOD FLOOR; SEPARATING LAYER; EXISTING CONCRETE FOUNDATION; Architect: OpeningDesign; FYF LLC.; Date; Description

This project, like most OpeningDesign's projects, is open source (Attribution-ShareAlike 4.0 International--CC BY-SA 4.0)--freely available to any party for future use, assuming the terms such as Attribution and ShareAlike are honored.

STANDING SEAM METAL ROOF
(GALV-TEN ROBUST)

Owner: FYF LLC.

30LB ROOFING FELT OVER 1/2"
CDX PLYWOOD

43 S Water St E | Fort Atkinson, WI
ilovefunkys@hotmail.com

WOOD BLOCKING - SIZE AS
NECESSARY

6" EPS RIGID INSULATION AT ROOF
OVER 6MIL VAPOR BARRIER

EXISTING PLYWOOD SUBSTRATE

Plumbing Designer: Zenteno Solutions

EXISTING 1x12'S (ACTUAL SIZE 1" X

1530 P B Lane # Z4646
WICHITA FALLS, TX, 76302
roberto@zenteno.net |832.449.9278

1/2" BEAD BOARD
TREATED WOOD ROOF RAFTERS
AT DECK (EXTERIOR STAIN:
PENOFIN VERDE EXT. STAIN -
COLOR: CEDAR)

1/2" CDX PLYWOOD OR
BLOCKING

2X BLOCKING AS NECESSARY,
BATT INSULATION IN ANY OPEN
CAVITIES

NEW GALV. RAFTER HANGER AT
RIDGE BOARD

AIR BARRIER (BUILDING WRAP)
OVER FIBERGLASS MAT GYPSUM
PANELS

WOOD SIDING (THERMALLY
MODIFIED WOOD: ARBOR
WOOD)
(EXTERIOR STAIN : PENOFIN VERDE
EXT. STAIN - COLOR: CEDAR)

CONCEALED SHEET METAL

Existing Roof Joist

#1075-B, 10th main, HAL 2nd stage,

Bengaluru -08
HVAC Designer: Desapex
shreenidhi@desapex.com

OPEN JOINT SIDING

(CHEMICALLY TREATED WOOD :

(EXTERIOR STAIN : CABOT -
SEMI-TRANPARENT/SOLID -
DRIFTWOOD GRAY))

GLULAMS BEAMS - EXTERIOR -
(PRESSURE TREATED W/ PENTA IN
SOLVENT) (STAIN: PENOFIN VERDE

GALVANIZED (PERFORATED OR
PUNCHED) HORTZ. HAT CHANNEL

KAWNEER TRIFAB VERSAGLAZE
451T - CLEAR ANODIZED ALUM. -
BACK GLAZED

GLULAMS BEAMS- INTERIOR -
(STAIN TO MATCH EXTERIOR
BEAMS)

INTERMITTENT EPDM SHIMS UNDER

HORZ. HAT CHANNEL

UV STABLE WATER RESISTANT
VAPOR PERMEABLE AIR BARRIER
OVER 2" CONT. RIGID INSULATION

- (CLASS A FLAME SPREAD)

3" = 1'-0" 2D Head Detail - West Wall at Polycarbaonte - Looking North

EXISTING 2X WOOD STUDS OR
NEW TO MATCH (BATT INSUL)

FIBERGLASS MAT GYPSUM PANELS

ELECTRIC BASE BOARD HEATER

AWNING: 1/8" CORTEN PLATE
STEEL ENCLOSURE OVER 1" GAL.
TUBE STEEL (1/4" OVER 12" SLOPE)

3" = 1'-0" 4C Head Detail - Mid Span - Looking North

WOOD DECKING (AT 45° TO
JOISTS)

DENSE SOUND-CHECK LAYER

ELASTIC IMPACT BASE MAT

GALVANIZED PENDANT CONDUIT

EXISTING PLANK FLOOR LAYER (3

TREATED WOOD FLOOR JOISTS AT
DECK (EXTERIOR STAIN: PENOFIN
VERDE EXT. STAIN - COLOR:
CEDAR)

SOUND BATT. INSULATION

GALVANIZED STEEL ANGLE (2 1/2"

RESILIENT METAL CHANNELS @ 16"

ALUMINUM PROFILE AT
POLYCARBONATE PANEL

MULTI-WALL POLYCARBONATE
PANELS (MODEL : ARCOPLUS 547)
(COLOR - OPAL)

SHIELDED LIGHT FIXTURE W/ 70W

GA. STEEL CLIP AT EVERY SEAM IN
POLYCARBONATE (WITH
BLOCKING EXTENSIONS, IF NECS.)

OR LESS BULB

3" = 1'-0" 2B Head/Sill Detail - West Wall at Polycarbaonte - Looking North

GLULAMS GIRTS- INTERIOR -

ANDERSEN - A-SERIES - AWNING

1st Floor

WINDOW - DARK BRONZE

312 W. Lakeside St. | Madison, WI 53715
hello@openingdesign.com | 773-425-6456

TREATED 3/4" CDX PLYWOOD
OVER 6 MIN. VAPOR BARRIER

3" = 1'-0" 1 Detail @ Glulam Girt

04.10.2017 Early Start & Footing/Foundation
05.03.2017 Issue for Permit
05.22.2017 Issue for Bid

3" = 1'-0" 6B Eave Detail - West Wall - Looking North

EXISTING CRUSHED STONE

3" = 1'-0" 2A Sill Detail - West Wall at Polycarbaonte - Looking North

EXTERIOR DETAILS The Downtowner | 640 West Main Street, Lake Geneva, WI 53147
