OpeningDesign/Vacation_Rental/Transfer/20170519 ----- ISSUE FOR BID & PERMIT -------/The Downtowner_ARCH - Sheet - A401 - EXTERIOR DETAILS.pdf

## Existing Roof Joist Bearing

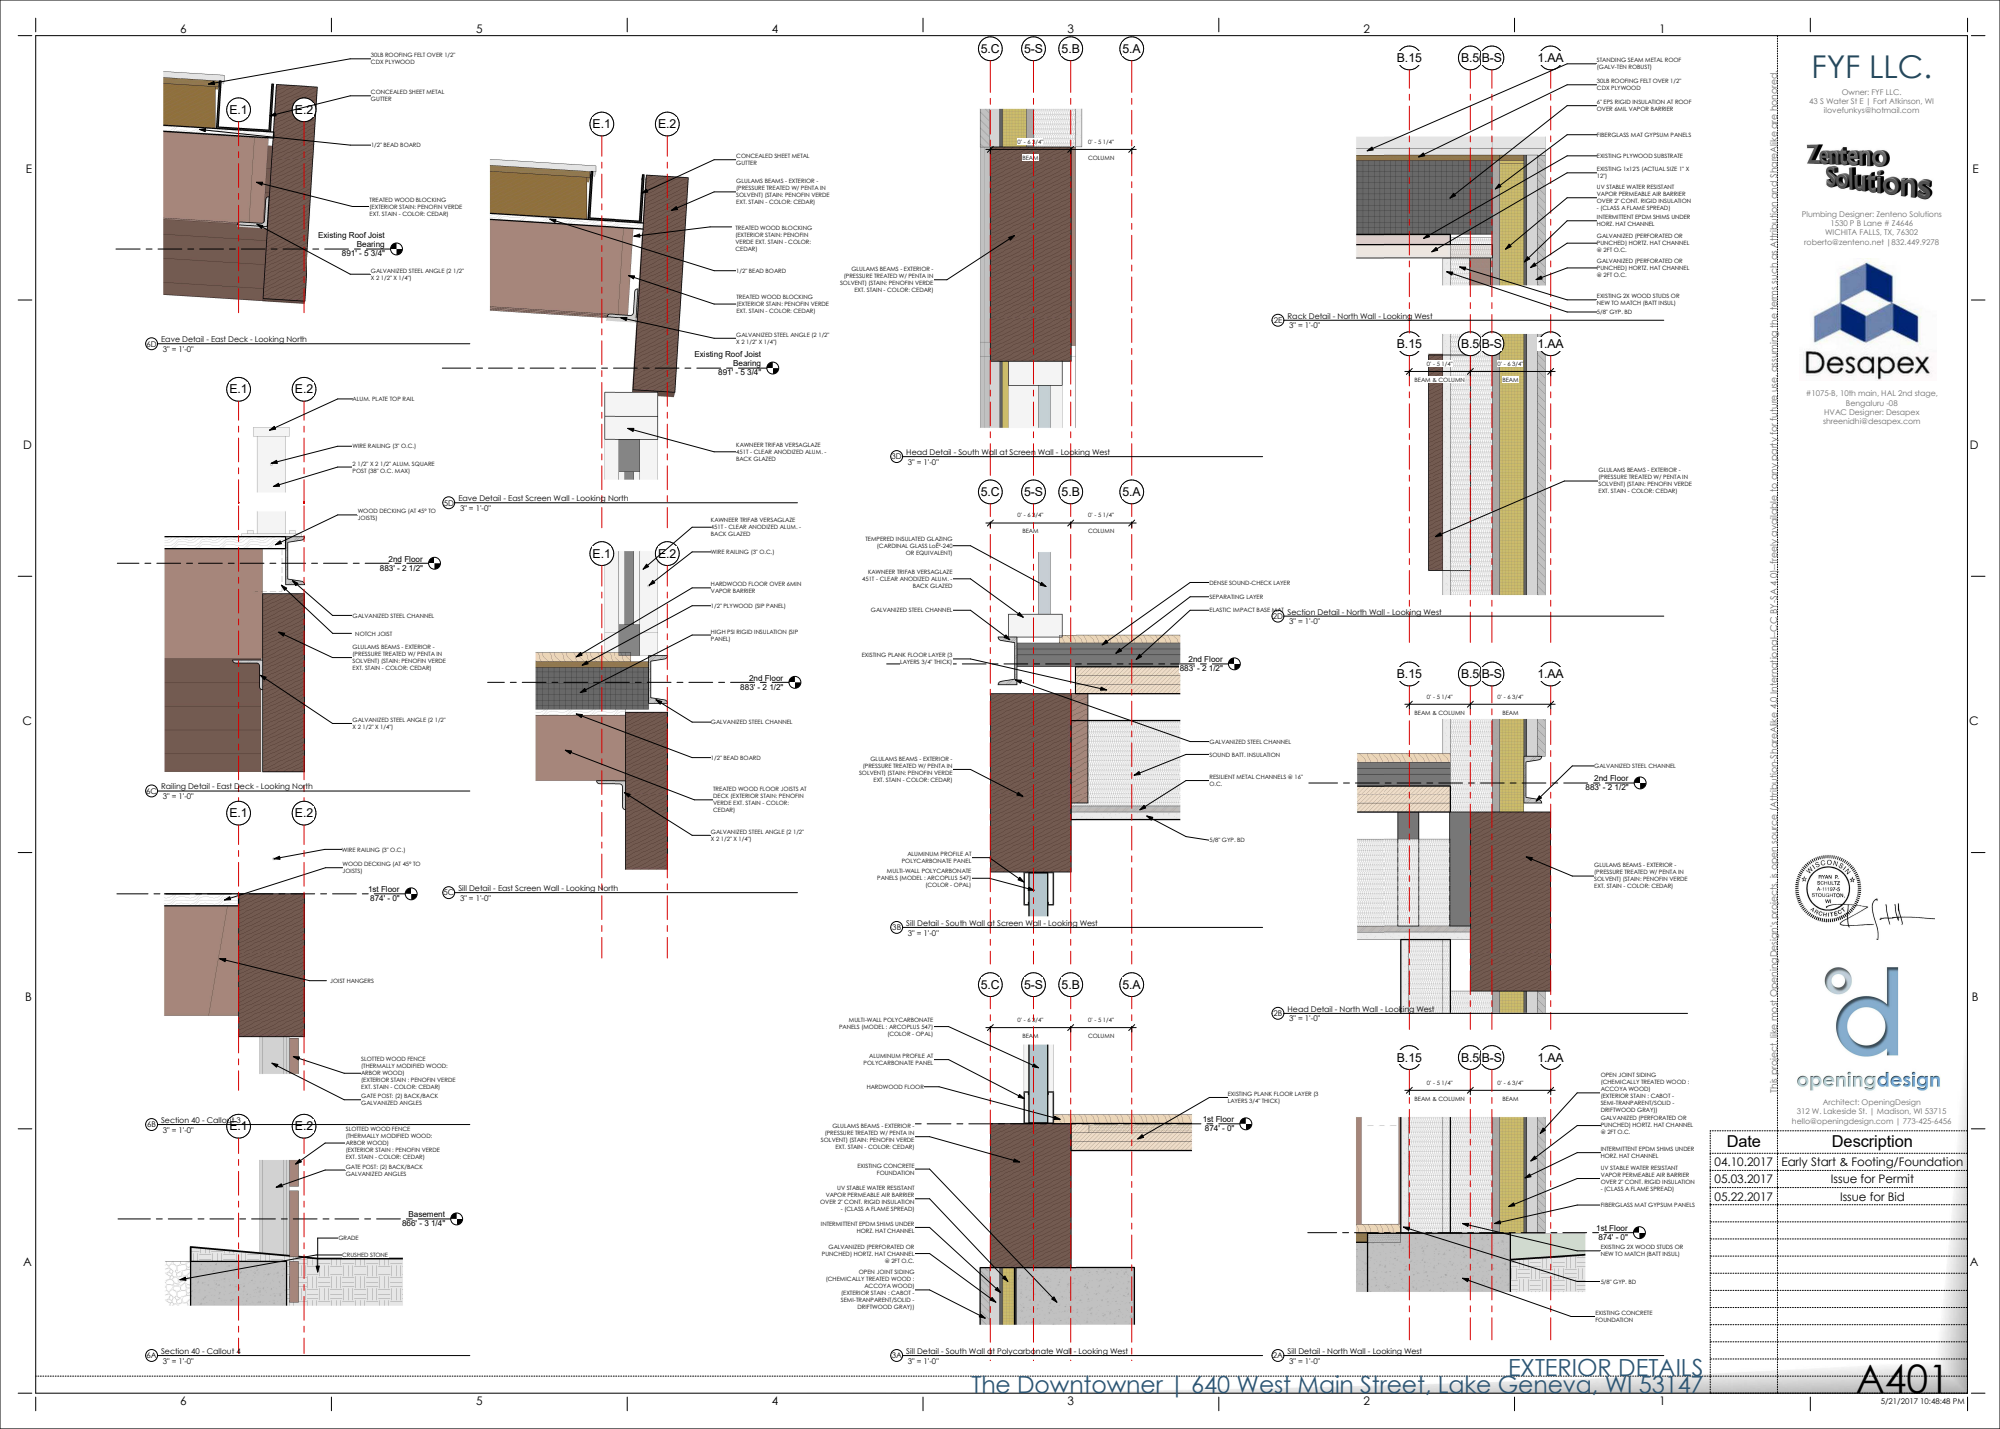
[picture p240: page 1]
1/2" BEAD BOARD; 2nd Floor 883' - 2 1/2"; 2 1/2" X 2 1/2" ALUM. SQUARE POST (38" O.C. MAX); WIRE RAILING (3" O.C.); NOTCH JOIST; 1st Floor 874' - 0"; JOIST HANGERS; Basement 866' - 3 1/4"; CRUSHED STONE; GRADE; BEAM; COLUMN; (COLOR - OPAL); 5/8" GYP. BD; BACK GLAZED; OR EQUIVALENT); LAYERS 3/4" THICK); SEPARATING LAYER; EXISTING CONCRETE FOUNDATION; ACCOYA WOOD); HARDWOOD FLOOR; Bearing 891' - 5 3/4"; BEAM & COLUMN; GALVANIZED STEEL CHANNEL; Architect: OpeningDesign; FYF LLC.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

30LB ROOFING FELT OVER 1/2"
CDX PLYWOOD

STANDING SEAM METAL ROOF
(GALV-TEN ROBUST)

This project, like most OpeningDesign's projects, is open source (Attribution-ShareAlike 4.0 International--CC BY-SA 4.0)--freely available to any party for future use, assuming the terms such as Attribution and ShareAlike are honored.

CONCEALED SHEET METAL
GUTTER

Owner: FYF LLC.

6" EPS RIGID INSULATION AT ROOF
OVER 6MIL VAPOR BARRIER

43 S Water St E | Fort Atkinson, WI
ilovefunkys@hotmail.com

FIBERGLASS MAT GYPSUM PANELS

EXISTING PLYWOOD SUBSTRATE

EXISTING 1x12'S (ACTUAL SIZE 1" X

GLULAMS BEAMS - EXTERIOR -
(PRESSURE TREATED W/ PENTA IN
SOLVENT) (STAIN: PENOFIN VERDE
EXT. STAIN - COLOR: CEDAR)

UV STABLE WATER RESISTANT
VAPOR PERMEABLE AIR BARRIER
OVER 2" CONT. RIGID INSULATION
- (CLASS A FLAME SPREAD)
INTERMITTENT EPDM SHIMS UNDER
HORZ. HAT CHANNEL

TREATED WOOD BLOCKING
(EXTERIOR STAIN: PENOFIN VERDE

Plumbing Designer: Zenteno Solutions

1530 P B Lane # Z4646
WICHITA FALLS, TX, 76302
roberto@zenteno.net |832.449.9278

(EXTERIOR STAIN: PENOFIN
VERDE EXT. STAIN - COLOR:
CEDAR)

GALVANIZED (PERFORATED OR
PUNCHED) HORTZ. HAT CHANNEL

GALVANIZED STEEL ANGLE (2 1/2"

EXISTING 2X WOOD STUDS OR
NEW TO MATCH (BATT INSUL)
5/8" GYP. BD

3" = 1'-0" 2E Rack Detail - North Wall - Looking West

3" = 1'-0" 6D Eave Detail - East Deck - Looking North

Existing Roof Joist

#1075-B, 10th main, HAL 2nd stage,

ALUM. PLATE TOP RAIL

Bengaluru -08
HVAC Designer: Desapex
shreenidhi@desapex.com

KAWNEER TRIFAB VERSAGLAZE
451T - CLEAR ANODIZED ALUM. -
BACK GLAZED

3" = 1'-0" 3D Head Detail - South Wall at Screen Wall - Looking West

3" = 1'-0" 5D Eave Detail - East Screen Wall - Looking North

WOOD DECKING (AT 45° TO
JOISTS)

TEMPERED INSULATED GLAZING
(CARDINAL GLASS LoĒ²-240

HARDWOOD FLOOR OVER 6MIN
VAPOR BARRIER

DENSE SOUND-CHECK LAYER

1/2" PLYWOOD (SIP PANEL)

GALVANIZED STEEL CHANNEL

ELASTIC IMPACT BASE MAT

3" = 1'-0" 2D Section Detail - North Wall - Looking West

HIGH PSI RIGID INSULATION (SIP
PANEL)

EXISTING PLANK FLOOR LAYER (3

SOUND BATT. INSULATION

RESILIENT METAL CHANNELS @ 16"

3" = 1'-0" 6C Railing Detail - East Deck - Looking North

TREATED WOOD FLOOR JOISTS AT
DECK (EXTERIOR STAIN: PENOFIN

ALUMINUM PROFILE AT
POLYCARBONATE PANEL
MULTI-WALL POLYCARBONATE
PANELS (MODEL : ARCOPLUS 547)

3" = 1'-0" 5C Sill Detail - East Screen Wall - Looking North

3" = 1'-0" 3B Sill Detail - South Wall at Screen Wall - Looking West

3" = 1'-0" 2B Head Detail - North Wall - Looking West

SLOTTED WOOD FENCE
(THERMALLY MODIFIED WOOD:
ARBOR WOOD)
(EXTERIOR STAIN : PENOFIN VERDE
GATE POST: (2) BACK/BACK
GALVANIZED ANGLES

OPEN JOINT SIDING
(CHEMICALLY TREATED WOOD :
ACCOYA WOOD)
(EXTERIOR STAIN : CABOT -
SEMI-TRANPARENT/SOLID -
DRIFTWOOD GRAY))

LAYERS 3/4" THICK)

312 W. Lakeside St. | Madison, WI 53715
hello@openingdesign.com | 773-425-6456

04.10.2017 Early Start & Footing/Foundation
05.03.2017 Issue for Permit
05.22.2017 Issue for Bid

3" = 1'-0" 3A Sill Detail - South Wall at Polycarbonate Wall - Looking West

3" = 1'-0" 2A Sill Detail - North Wall - Looking West

EXTERIOR DETAILS The Downtowner | 640 West Main Street, Lake Geneva, WI 53147
