OpeningDesign/Vacation_Rental/Transfer/20170519 ----- ISSUE FOR BID & PERMIT -------/The Downtowner_ARCH - Sheet - A402 - EXTERIOR DETAILS.pdf

B.15 | B.5 | 1.AA

B-S

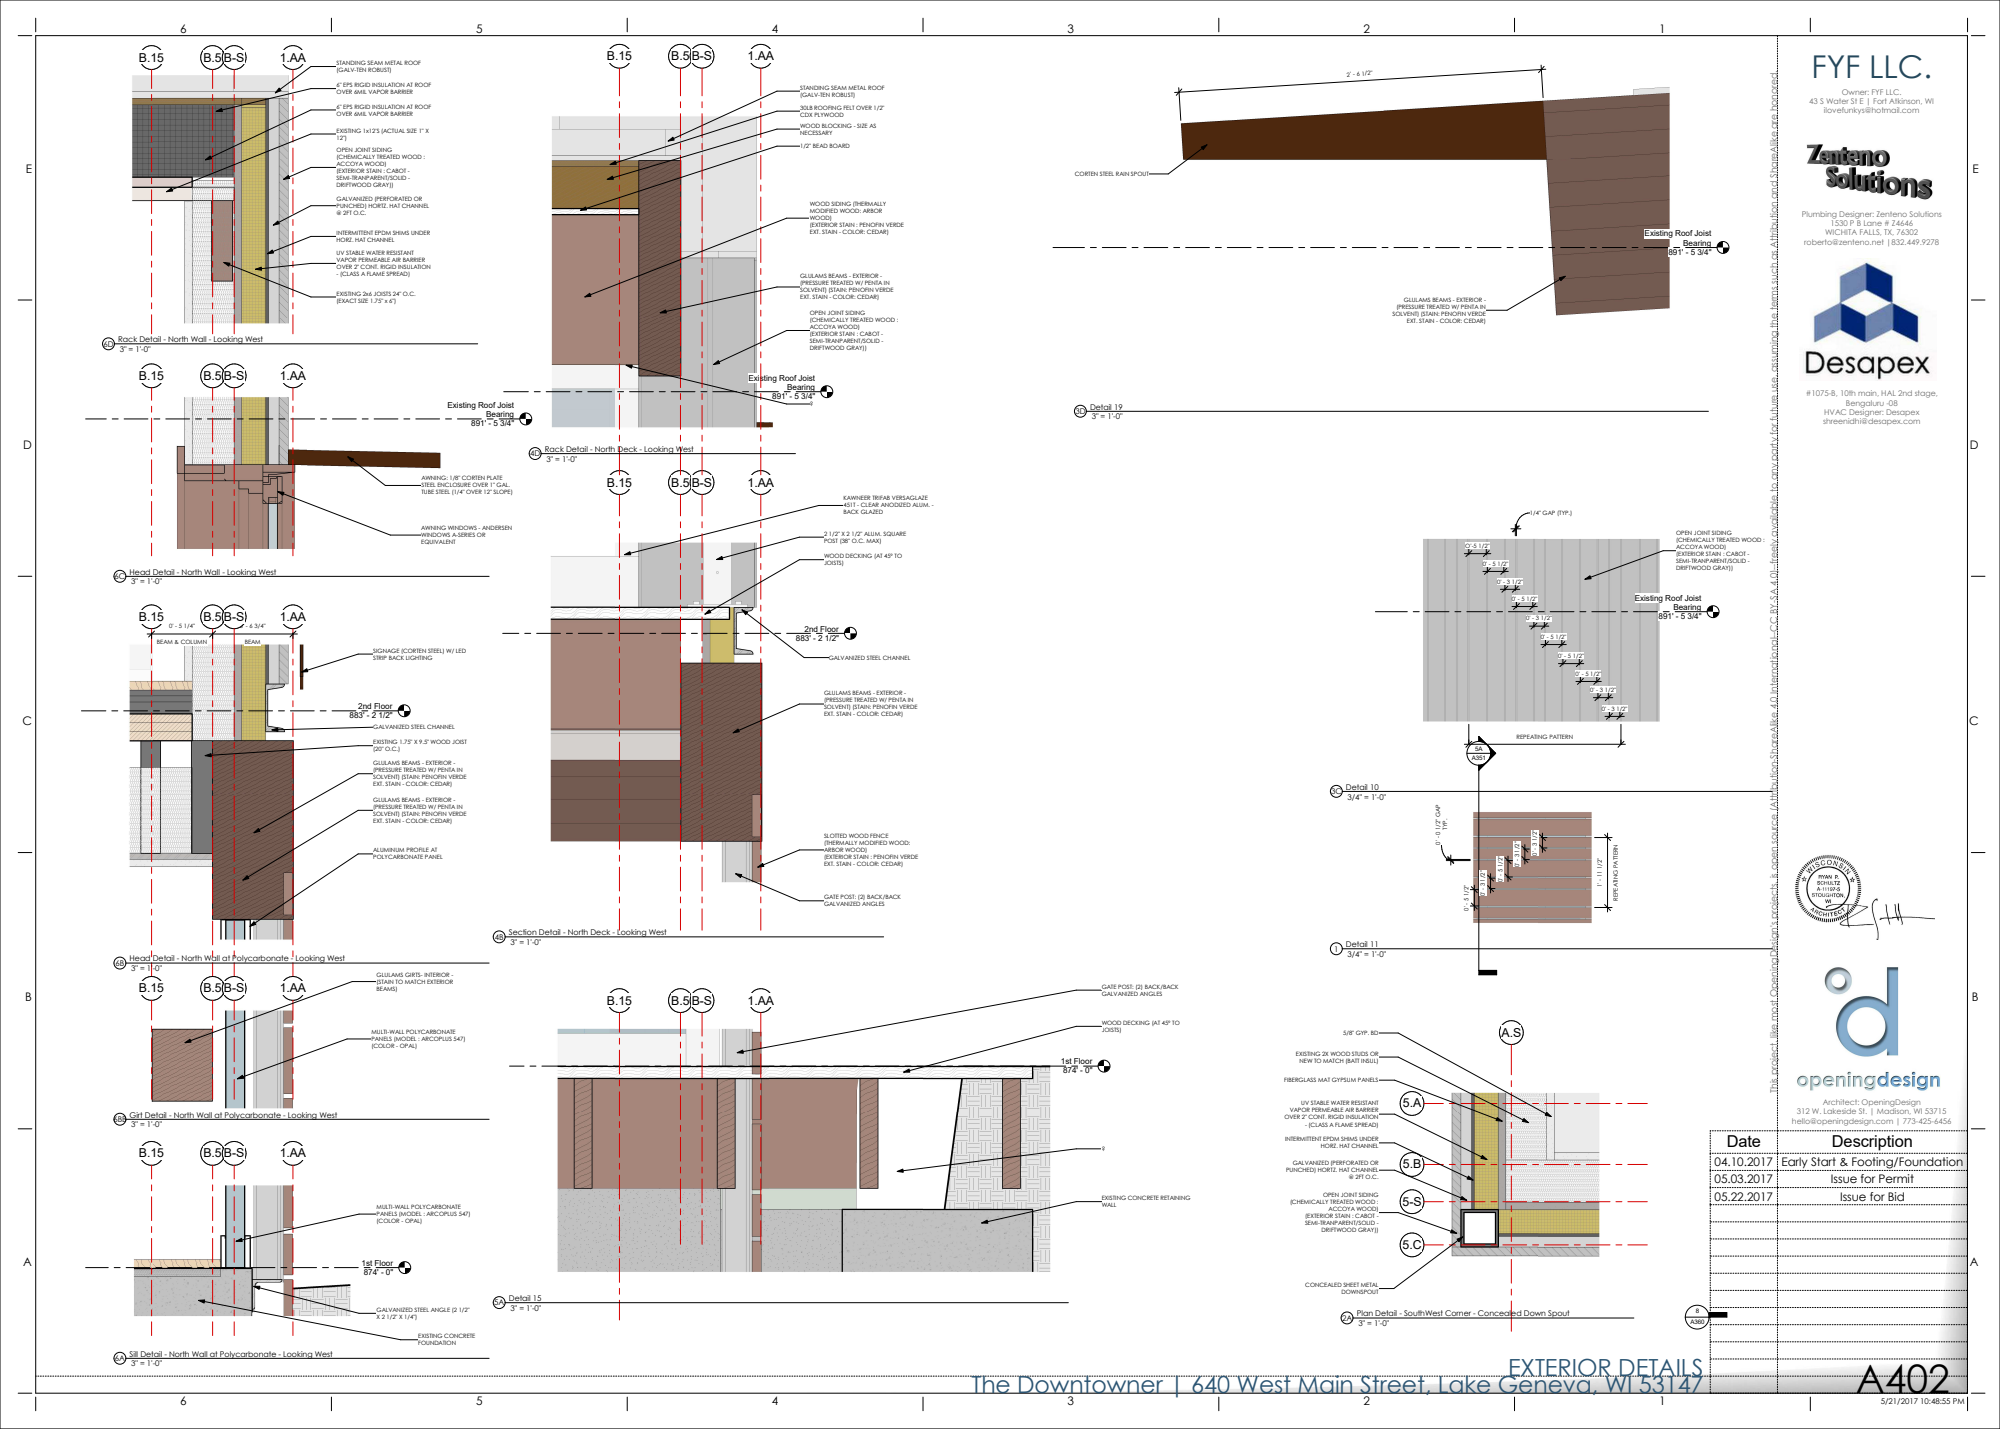
[picture p241: page 1]
Bearing 891' - 5 3/4"; STANDING SEAM METAL ROOF; EXISTING 2x6 JOISTS 24" O.C. (EXACT SIZE 1.75" x 6"); 2nd Floor 883' - 2 1/2"; BEAM & COLUMN; BEAM; 1st Floor 874' - 0"; EXISTING CONCRETE FOUNDATION; 2 1/2" X 2 1/2" ALUM. SQUARE POST (38" O.C. MAX); 1/2" BEAD BOARD; REPEATING PATTERN; 1/4" GAP (TYP.); DOWNSPOUT; ACCOYA WOOD); 5/8" GYP. BD; TYP.; 0' - 0 1/2" GAP; Architect: OpeningDesign; FYF LLC.; 3" = 1'-0" 5A Detail 15; 3" = 1'-0" 3D Detail 19; 3/4" = 1'-0" 3C Detail 10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

(GALV-TEN ROBUST)

This project, like most OpeningDesign's projects, is open source (Attribution-ShareAlike 4.0 International--CC BY-SA 4.0)--freely available to any party for future use, assuming the terms such as Attribution and ShareAlike are honored.

6" EPS RIGID INSULATION AT ROOF
OVER 6MIL VAPOR BARRIER

STANDING SEAM METAL ROOF

Owner: FYF LLC.

43 S Water St E | Fort Atkinson, WI
ilovefunkys@hotmail.com

30LB ROOFING FELT OVER 1/2"
CDX PLYWOOD

WOOD BLOCKING - SIZE AS
NECESSARY

EXISTING 1x12'S (ACTUAL SIZE 1" X

OPEN JOINT SIDING
(CHEMICALLY TREATED WOOD :
ACCOYA WOOD)
(EXTERIOR STAIN : CABOT -
SEMI-TRANPARENT/SOLID -
DRIFTWOOD GRAY))

CORTEN STEEL RAIN SPOUT

GALVANIZED (PERFORATED OR
PUNCHED) HORTZ. HAT CHANNEL

WOOD SIDING (THERMALLY
MODIFIED WOOD: ARBOR
WOOD)
(EXTERIOR STAIN : PENOFIN VERDE
EXT. STAIN - COLOR: CEDAR)

Plumbing Designer: Zenteno Solutions

1530 P B Lane # Z4646
WICHITA FALLS, TX, 76302
roberto@zenteno.net |832.449.9278

INTERMITTENT EPDM SHIMS UNDER
HORZ. HAT CHANNEL

Existing Roof Joist

UV STABLE WATER RESISTANT
VAPOR PERMEABLE AIR BARRIER
OVER 2" CONT. RIGID INSULATION
- (CLASS A FLAME SPREAD)

GLULAMS BEAMS - EXTERIOR -
(PRESSURE TREATED W/ PENTA IN
SOLVENT) (STAIN: PENOFIN VERDE

3" = 1'-0" 6D Rack Detail - North Wall - Looking West

#1075-B, 10th main, HAL 2nd stage,

Bengaluru -08
HVAC Designer: Desapex
shreenidhi@desapex.com

3" = 1'-0" 4D Rack Detail - North Deck - Looking West

AWNING: 1/8" CORTEN PLATE
STEEL ENCLOSURE OVER 1" GAL.
TUBE STEEL (1/4" OVER 12" SLOPE)

KAWNEER TRIFAB VERSAGLAZE
451T - CLEAR ANODIZED ALUM. -
BACK GLAZED

AWNING WINDOWS - ANDERSEN
WINDOWS A-SERIES OR
EQUIVALENT

WOOD DECKING (AT 45° TO
JOISTS)

3" = 1'-0" 6C Head Detail - North Wall - Looking West

SIGNAGE (CORTEN STEEL) W/ LED
STRIP BACK LIGHTING

GALVANIZED STEEL CHANNEL

EXISTING 1.75" X 9.5" WOOD JOIST

SLOTTED WOOD FENCE
(THERMALLY MODIFIED WOOD:
ARBOR WOOD)

ALUMINUM PROFILE AT
POLYCARBONATE PANEL

GATE POST: (2) BACK/BACK
GALVANIZED ANGLES

3" = 1'-0" 4B Section Detail - North Deck - Looking West

3" = 1'-0" 6B Head Detail - North Wall at Polycarbonate - Looking West

GLULAMS GIRTS- INTERIOR -
(STAIN TO MATCH EXTERIOR
BEAMS)

MULTI-WALL POLYCARBONATE
PANELS (MODEL : ARCOPLUS 547)
(COLOR - OPAL)

EXISTING 2X WOOD STUDS OR
NEW TO MATCH (BATT INSUL)

FIBERGLASS MAT GYPSUM PANELS

312 W. Lakeside St. | Madison, WI 53715
hello@openingdesign.com | 773-425-6456

3" = 1'-0" 6BB Girt Detail - North Wall at Polycarbonate - Looking West

04.10.2017 Early Start & Footing/Foundation
05.03.2017 Issue for Permit
05.22.2017 Issue for Bid

5-S OPEN JOINT SIDING (CHEMICALLY TREATED WOOD :

EXISTING CONCRETE RETAINING
WALL

CONCEALED SHEET METAL

GALVANIZED STEEL ANGLE (2 1/2"

3" = 1'-0" 2A Plan Detail - SouthWest Corner - Concealed Down Spout

3" = 1'-0" 6A Sill Detail - North Wall at Polycarbonate - Looking West

EXTERIOR DETAILS The Downtowner | 640 West Main Street, Lake Geneva, WI 53147
