OpeningDesign/Vacation_Rental/Transfer/20170519 ----- ISSUE FOR BID & PERMIT -------/The Downtowner_ARCH - Sheet - S500 - FRAMING SCHEDULE.pdf

Architect: OpeningDesign
312 W. Lakeside St. | Madison, WI 53715
hello@openingdesign.com | 773-425-6456

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
Owner: FYF LLC.

### 43 S Water St E | Fort Atkinson, WI

ilovefunkys@hotmail.com

FYF LLC.

Plumbing Designer: Zenteno Solutions 1530 P B Lane # Z4646
WICHITA FALLS, TX, 76302
roberto@zenteno.net |832.449.9278

#1075-B, 10th main, HAL 2nd stage, Bengaluru -08

HVAC Designer: Desapex
shreenidhi@desapex.com

This project, like most OpeningDesign's projects, is open source (Attribution-ShareAlike 4.0 International--CC BY-SA 4.0)--freely available to any party for future use, assuming the terms such as Attribution and ShareAlike are honored.

5/21/2017 10:49:10 PM

# S500 FRAMING SCHEDULE The Downtowner | 640 West Main Street, Lake Geneva, WI 53147

Structural Framing Schedule

MARK | TYPE | DESCRIPTION - FINISH | LENGTH | LEVEL

ELEVATIO
N

ELEV. AT
BOTTOM

ELEVATIO
N AT TOP
C4X5.4: 3 | | | 101' - 9 13/32"
EXISTING 5" X 12" W SECTION | EXISTING STEEL W SECTION | 18' - 4 1/2" | 2nd Floor | 883' - 2 1/2" | 881' - 2 1/2" | 883' - 2 1/2"
EXISTING 6" X 18" W SECTION | EXISTING STEEL W SECTION | 30' - 6 5/16" | 2nd Floor | 883' - 2 1/2" | 880' - 8 19/32" | 883' - 2 1/2"
EXISTING 6" X 18" W SECTION: 1 | 30' - 6 5/16"
L2-1/2X2-1/2X1/4 | GALVANIZED STEEL ANGLE (2 1/2" X 2 1/2" X 1/4") | 3' - 5 1/2" | 2nd Floor | 883' - 2 1/2" | 882' - 3 7/8" | 883' - 2 1/2"
L2-1/2X2-1/2X1/4 | GALVANIZED STEEL ANGLE (2 1/2" X 2 1/2" X 1/4") | 3' - 5 1/2" | 2nd Floor | 883' - 2 1/2" | 882' - 3 7/8" | 883' - 2 1/2"
L2-1/2X2-1/2X1/4 | GALVANIZED STEEL ANGLE (2 1/2" X 2 1/2" X 1/4") | 13' - 11
9/16"
2nd Floor | 883' - 2 1/2" | Varies | Varies
L2-1/2X2-1/2X1/4 | GALVANIZED STEEL ANGLE (2 1/2" X 2 1/2" X 1/4") | 14' - 1
11/32"
2nd Floor | 883' - 2 1/2" | 882' - 3 7/8" | 883' - 2 1/2"
L2-1/2X2-1/2X1/4 | GALVANIZED STEEL ANGLE (2 1/2" X 2 1/2" X 1/4") | 14' - 4 7/8" | 2nd Floor | 883' - 2 1/2" | 882' - 3 7/8" | 883' - 2 1/2"
L2-1/2X2-1/2X1/4 | GALVANIZED STEEL ANGLE (2 1/2" X 2 1/2" X 1/4") | 16' - 5 3/8" | 2nd Floor | 883' - 2 1/2" | 882' - 3 3/4" | 883' - 2 1/2"
L2-1/2X2-1/2X1/4 | GALVANIZED STEEL ANGLE (2 1/2" X 2 1/2" X 1/4") | 16' - 5 7/8" | 2nd Floor | 883' - 2 1/2" | 882' - 3 3/4" | 883' - 2 1/2"
L2-1/2X2-1/2X1/4 | GALVANIZED STEEL ANGLE (2 1/2" X 2 1/2" X 1/4") | 16' - 6 9/16" | 2nd Floor | 883' - 2 1/2" | Varies | Varies
L2-1/2X2-1/2X1/4 | GALVANIZED STEEL ANGLE (2 1/2" X 2 1/2" X 1/4") | 18' - 0 15/32" | 2nd Floor | 883' - 2 1/2" | 882' - 3 7/8" | 883' - 2 1/2"
L2-1/2X2-1/2X1/4 | GALVANIZED STEEL ANGLE (2 1/2" X 2 1/2" X 1/4") | 18' - 1 15/32" | 2nd Floor | 883' - 2 1/2" | 882' - 3 7/8" | 883' - 2 1/2"
L2-1/2X2-1/2X1/4 | GALVANIZED STEEL ANGLE (2 1/2" X 2 1/2" X 1/4") | 18' - 6 5/8" | 2nd Floor | 883' - 2 1/2" | Varies | Varies
L2-1/2X2-1/2X1/4: 11 | 153' - 7 1/8"
2nd Floor: 37 | 685' - 10 1/4"

Existing Roof Joist Bearing
3 1/2" x 16 1/2" GLULAM | GLULAMS BEAMS- INTERIOR - (STAIN TO MATCH EXTERIOR BEAMS) | 14' - 5 11/32" | Existing Roof Joist Bearing | 891' - 5 3/4" | 891' - 5 3/4" | 897' - 6 3/4"
3 1/2" x 16 1/2" GLULAM | GLULAMS BEAMS- INTERIOR - (STAIN TO MATCH EXTERIOR BEAMS) | 16' - 9 3/4" | Existing Roof Joist Bearing | 891' - 5 3/4" | 891' - 5 3/4" | 897' - 6 3/4"
3 1/2" x 16 1/2" GLULAM | GLULAMS BEAMS- INTERIOR - (STAIN TO MATCH EXTERIOR BEAMS) | 18' - 5 25/32" | Existing Roof Joist Bearing | 891' - 5 3/4" | 891' - 5 3/4" | 897' - 6 3/4"
3 1/2" x 16 1/2" GLULAM: 3 | 49' - 8 7/8"
5 1/2" X 13 1/2" GLULAM | GLULAMS BEAMS - EXTERIOR - (PRESSURE TREATED W/ PENTA IN SOLVENT) (STAIN: PENOFIN VERDE EXT. STAIN - COLOR: CEDAR) | 19' - 11 7/8" | Existing Roof Joist Bearing | 891' - 5 3/4" | 890' - 7 1/2" | 891' - 9"
5 1/2" X 13 1/2" GLULAM | GLULAMS BEAMS- INTERIOR - (STAIN TO MATCH EXTERIOR BEAMS) | 14' - 5 1/32" | Existing Roof Joist Bearing | 891' - 5 3/4" | 890' - 7 1/2" | 891' - 9"
5 1/2" X 13 1/2" GLULAM | GLULAMS BEAMS- INTERIOR - (STAIN TO MATCH EXTERIOR BEAMS) | 18' - 5 25/32" | Existing Roof Joist Bearing | 891' - 5 3/4" | 890' - 7 1/2" | 891' - 9"
5 1/2" X 13 1/2" GLULAM: 3 | 52' - 10 11/16"
Existing Roof Joist Bearing: 6 | 102' - 7 17/32"

Structural Framing Schedule

MARK | TYPE | DESCRIPTION - FINISH | LENGTH | LEVEL

ELEVATIO
N

ELEV. AT
BOTTOM

ELEVATIO
N AT TOP

Basement
3 1/8" X 12" GLULAM -STRINGER | GLULAMS BEAMS - EXTERIOR - (PRESSURE TREATED W/ PENTA IN SOLVENT) (STAIN: PENOFIN VERDE EXT. STAIN - COLOR: CEDAR) | 16' - 0" | Basement | 866' - 3 1/4" | 865' - 3 1/4" | 866' - 3 1/4"
3 1/8" X 12" GLULAM -STRINGER | GLULAMS BEAMS - EXTERIOR - (PRESSURE TREATED W/ PENTA IN SOLVENT) (STAIN: PENOFIN VERDE EXT. STAIN - COLOR: CEDAR) | 16' - 0" | Basement | 866' - 3 1/4" | 865' - 3 1/4" | 866' - 3 1/4" | EXISTING 5" X 12" W SECTION: 1 18' - 4 1/2"
3 1/8" X 12" GLULAM - STRINGER: 2 | 32' - 0"
Basement: 2 | 32' - 0"
1st Floor
1 3/4 x 9 1/2 LVL | LVL | 3' - 11 1/4" | 1st Floor | 874' - 0" | 873' - 3 1/2" | 874' - 1"
1 3/4 x 9 1/2 LVL | LVL | 3' - 11 1/4" | 1st Floor | 874' - 0" | 873' - 3 1/2" | 874' - 1"
1 3/4 x 9 1/2 LVL: 2 | | 7' - 10 1/2"
3 1/2" X 12" GLULAM | GLULAMS BEAMS - EXTERIOR - (PRESSURE TREATED W/ PENTA IN SOLVENT) (STAIN: PENOFIN VERDE EXT. STAIN - COLOR: CEDAR) | 3' - 3 3/8" | 1st Floor | 874' - 0" | 872' - 11" | 874' - 0"

3 1/2" X 12"
GLULAM

GLULAMS BEAMS - EXTERIOR - (PRESSURE TREATED W/ PENTA IN SOLVENT) (STAIN: PENOFIN VERDE EXT. STAIN - COLOR: CEDAR)

3' - 4 3/8" | 1st Floor | 874' - 0" | 872' - 11" | 874' - 0"
3 1/2" X 12" GLULAM: 2 | 6' - 7 3/4"
3 1/8" X 12" GLULAM -STRINGER | GLULAMS BEAMS - EXTERIOR - (PRESSURE TREATED W/ PENTA IN SOLVENT) (STAIN: PENOFIN VERDE EXT. STAIN - COLOR: CEDAR) | 19' - 0" | 1st Floor | 874' - 0" | 873' - 0" | 874' - 0"
3 1/8" X 12" GLULAM -STRINGER | GLULAMS BEAMS - EXTERIOR - (PRESSURE TREATED W/ PENTA IN SOLVENT) (STAIN: PENOFIN VERDE EXT. STAIN - COLOR: CEDAR) | 19' - 0" | 1st Floor | 874' - 0" | 873' - 0" | 874' - 0"
3 1/8" X 12" GLULAM - STRINGER: 2 | 38' - 0"
5 1/2" X 12" GLULAM | GLULAMS BEAMS - EXTERIOR - (PRESSURE TREATED W/ PENTA IN SOLVENT) (STAIN: PENOFIN VERDE EXT. STAIN - COLOR: CEDAR) | 16' - 9 5/32" | 1st Floor | 874' - 0" | 873' - 0" | 874' - 0"
5 1/2" X 12" GLULAM | GLULAMS BEAMS - EXTERIOR - (PRESSURE TREATED W/ PENTA IN SOLVENT) (STAIN: PENOFIN VERDE EXT. STAIN - COLOR: CEDAR) | 16' - 10 3/8" | 1st Floor | 874' - 0" | 873' - 0" | 874' - 0"
5 1/2" X 12" GLULAM | GLULAMS BEAMS - EXTERIOR - (PRESSURE TREATED W/ PENTA IN SOLVENT) (STAIN: PENOFIN VERDE EXT. STAIN - COLOR: CEDAR) | 18' - 4 25/32" | 1st Floor | 874' - 0" | 872' - 11" | 874' - 0"
5 1/2" X 12" GLULAM | GLULAMS BEAMS - EXTERIOR - (PRESSURE TREATED W/ PENTA IN SOLVENT) (STAIN: PENOFIN VERDE EXT. STAIN - COLOR: CEDAR) | 18' - 7 1/32" | 1st Floor | 874' - 0" | 873' - 0" | 874' - 0"
5 1/2" X 12" GLULAM: 4 | 70' - 7 11/32"
5 1/8" x 6" GLULAM GIRT | GLULAMS GIRTS- INTERIOR - (STAIN TO MATCH EXTERIOR BEAMS) | 4' - 4 3/4" | 1st Floor | 874' - 0" | 874' - 0" | 877' - 6"
5 1/8" x 6" GLULAM GIRT | GLULAMS GIRTS- INTERIOR - (STAIN TO MATCH EXTERIOR BEAMS) | 7' - 7" | 1st Floor | 874' - 0" | 874' - 0" | 877' - 6"
5 1/8" x 6" GLULAM GIRT | GLULAMS GIRTS- INTERIOR - (STAIN TO MATCH EXTERIOR BEAMS) | 9' - 9 21/32" | 1st Floor | 874' - 0" | 874' - 0" | 877' - 6"
5 1/8" x 6" GLULAM GIRT | GLULAMS GIRTS- INTERIOR - (STAIN TO MATCH EXTERIOR BEAMS) | 14' - 3 25/32" | 1st Floor | 874' - 0" | 874' - 0" | 877' - 6"
5 1/8" x 6" GLULAM GIRT | GLULAMS GIRTS- INTERIOR - (STAIN TO MATCH EXTERIOR BEAMS) | 14' - 9 9/16" | 1st Floor | 874' - 0" | 874' - 0" | 877' - 6"
5 1/8" x 6" GLULAM GIRT | GLULAMS GIRTS- INTERIOR - (STAIN TO MATCH EXTERIOR BEAMS) | 14' - 9 9/16" | 1st Floor | 874' - 0" | 874' - 0" | 877' - 6"
5 1/8" x 6" GLULAM GIRT: 6 | | 65' - 8 5/16"
6 3/4" x 12" GLULAM | GLULAMS BEAMS - EXTERIOR - (PRESSURE TREATED W/ PENTA IN SOLVENT) (STAIN: PENOFIN VERDE EXT. STAIN - COLOR: CEDAR) | 21' - 4 15/32" | 1st Floor | 874' - 0" | 873' - 0" | 874' - 0"
6 3/4" x 12" GLULAM: 1 | | 21' - 4 15/32"
L2-1/2X2-1/2X1/4 | GALVANIZED STEEL ANGLE (2 1/2" X 2 1/2" X 1/4") | 12' - 8 9/16" | 1st Floor | 874' - 0" | 873' - 8 1/2" | 874' - 0"
L2-1/2X2-1/2X1/4: 1 | | 12' - 8 9/16"
1st Floor: 18 | 222' - 10 29/32"

2nd Floor
1 3/4 x 9 1/2 LVL | LVL | 6' - 10 3/8" | 2nd Floor | 883' - 2 1/2" | 882' - 2 1/2" | 883' - 2 1/2"
1 3/4 x 9 1/2 LVL | LVL | 12' - 8 3/16" | 2nd Floor | 883' - 2 1/2" | 882' - 2 1/2" | 883' - 2 1/2"
1 3/4 x 9 1/2 LVL: 2 | | 19' - 6 9/16"
3 1/2" x 15" GLULAM | GLULAMS BEAMS - EXTERIOR - (PRESSURE TREATED W/ PENTA IN SOLVENT) (STAIN: PENOFIN VERDE EXT. STAIN - COLOR: CEDAR) | 3' - 3 9/16" | 2nd Floor | 883' - 2 1/2" | 881' - 9" | 883' - 2 1/2"
3 1/2" x 15" GLULAM | GLULAMS BEAMS - EXTERIOR - (PRESSURE TREATED W/ PENTA IN SOLVENT) (STAIN: PENOFIN VERDE EXT. STAIN - COLOR: CEDAR) | 14' - 6 5/8" | 2nd Floor | 883' - 2 1/2" | 881' - 9" | 883' - 2 1/2"
3 1/2" x 15" GLULAM | GLULAMS BEAMS - EXTERIOR - (PRESSURE TREATED W/ PENTA IN SOLVENT) (STAIN: PENOFIN VERDE EXT. STAIN - COLOR: CEDAR) | 16' - 9 23/32" | 2nd Floor | 883' - 2 1/2" | 881' - 9" | 883' - 2 1/2"
3 1/2" x 15" GLULAM | GLULAMS BEAMS - EXTERIOR - (PRESSURE TREATED W/ PENTA IN SOLVENT) (STAIN: PENOFIN VERDE EXT. STAIN - COLOR: CEDAR) | 17' - 11 27/32" | 2nd Floor | 883' - 2 1/2" | 881' - 9" | 883' - 2 1/2"
3 1/2" x 15" GLULAM | GLULAMS BEAMS - EXTERIOR - (PRESSURE TREATED W/ PENTA IN SOLVENT) (STAIN: PENOFIN VERDE EXT. STAIN - COLOR: CEDAR) | 18' - 7" | 2nd Floor | 883' - 2 1/2" | 881' - 9" | 883' - 2 1/2"
3 1/2" x 15" GLULAM: 5 | 71' - 2 3/4"
3 1/2" x 18" GLULAM | GLULAMS BEAMS - EXTERIOR - (PRESSURE TREATED W/ PENTA IN SOLVENT) (STAIN: PENOFIN VERDE EXT. STAIN - COLOR: CEDAR) | 14' - 3 1/32" | 2nd Floor | 883' - 2 1/2" | Varies | Varies
3 1/2" x 18" GLULAM | GLULAMS BEAMS - EXTERIOR - (PRESSURE TREATED W/ PENTA IN SOLVENT) (STAIN: PENOFIN VERDE EXT. STAIN - COLOR: CEDAR) | 16' - 9 13/16" | 2nd Floor | 883' - 2 1/2" | Varies | Varies

3 1/2" x 18"
GLULAM

GLULAMS BEAMS - EXTERIOR - (PRESSURE TREATED W/ PENTA IN SOLVENT) (STAIN: PENOFIN VERDE EXT. STAIN - COLOR: CEDAR)

18' - 6 5/8" | 2nd Floor | 883' - 2 1/2" | Varies | Varies

3 1/2" x 18"
GLULAM

GLULAMS BEAMS - EXTERIOR - (PRESSURE TREATED W/ PENTA IN SOLVENT) (STAIN: PENOFIN VERDE EXT. STAIN - COLOR: CEDAR)

26' - 2 1/16" | 2nd Floor | 883' - 2 1/2" | Varies | Varies
3 1/2" x 18" GLULAM: 4 | 75' - 9 1/2"
5 1/2" X 15" GLULAM | GLULAMS BEAMS - EXTERIOR - (PRESSURE TREATED W/ PENTA IN SOLVENT) (STAIN: PENOFIN VERDE EXT. STAIN - COLOR: CEDAR) | 14' - 1 31/32" | 2nd Floor | 883' - 2 1/2" | 881' - 9" | 883' - 2 1/2"
5 1/2" X 15" GLULAM | GLULAMS BEAMS - EXTERIOR - (PRESSURE TREATED W/ PENTA IN SOLVENT) (STAIN: PENOFIN VERDE EXT. STAIN - COLOR: CEDAR) | 16' - 5 3/8" | 2nd Floor | 883' - 2 1/2" | 881' - 9" | 883' - 2 1/2"
5 1/2" X 15" GLULAM | GLULAMS BEAMS - EXTERIOR - (PRESSURE TREATED W/ PENTA IN SOLVENT) (STAIN: PENOFIN VERDE EXT. STAIN - COLOR: CEDAR) | 17' - 11 27/32" | 2nd Floor | 883' - 2 1/2" | 881' - 9" | 883' - 2 1/2"
5 1/2" X 15" GLULAM: 3 | 48' - 7 3/16"
5 1/2" x 18" GLULAM | GLULAMS BEAMS - EXTERIOR - (PRESSURE TREATED W/ PENTA IN SOLVENT) (STAIN: PENOFIN VERDE EXT. STAIN - COLOR: CEDAR) | 22' - 5 23/32" | 2nd Floor | 883' - 2 1/2" | Varies | Varies
5 1/2" x 18" GLULAM | GLULAMS BEAMS - EXTERIOR - (PRESSURE TREATED W/ PENTA IN SOLVENT) (STAIN: PENOFIN VERDE EXT. STAIN - COLOR: CEDAR) | 24' - 5" | 2nd Floor | 883' - 2 1/2" | Varies | Varies
5 1/2" x 18" GLULAM: 2 | 46' - 10 23/32"
6 3/4" x 15" GLULAM | GLULAMS BEAMS - EXTERIOR - (PRESSURE TREATED W/ PENTA IN SOLVENT) (STAIN: PENOFIN VERDE EXT. STAIN - COLOR: CEDAR) | 21' - 4 31/32" | 2nd Floor | 883' - 2 1/2" | 881' - 9" | 883' - 2 1/2"
6 3/4" x 15" GLULAM | GLULAMS BEAMS - EXTERIOR - (PRESSURE TREATED W/ PENTA IN SOLVENT) (STAIN: PENOFIN VERDE EXT. STAIN - COLOR: CEDAR) | 22' - 7 1/4" | 2nd Floor | 883' - 2 1/2" | 881' - 9" | 883' - 2 1/2"
6 3/4" x 15" GLULAM | GLULAMS BEAMS - EXTERIOR - (PRESSURE TREATED W/ PENTA IN SOLVENT) (STAIN: PENOFIN VERDE EXT. STAIN - COLOR: CEDAR) | 24' - 6 1/2" | 2nd Floor | 883' - 2 1/2" | 881' - 9" | 883' - 2 1/2"
6 3/4" x 15" GLULAM | GLULAMS BEAMS - EXTERIOR - (PRESSURE TREATED W/ PENTA IN SOLVENT) (STAIN: PENOFIN VERDE EXT. STAIN - COLOR: CEDAR) | 29' - 5 3/32" | 2nd Floor | 883' - 2 1/2" | 881' - 9" | 883' - 2 1/2"
6 3/4" x 15" GLULAM: 4 | 97' - 11 13/16"

6 3/4" x 18"
GLULAM

GLULAMS BEAMS - EXTERIOR - (PRESSURE TREATED W/ PENTA IN SOLVENT) (STAIN: PENOFIN VERDE EXT. STAIN - COLOR: CEDAR)

21' - 6
13/32"
2nd Floor | 883' - 2 1/2" | Varies | Varies
6 3/4" x 18" GLULAM: 1 | 21' - 6 13/32"
C4X5.4 | GALVANIZED STEEL CHANNEL | 21' - 4 15/32" | 2nd Floor | 883' - 2 1/2" | 883' - 0 3/4" | 883' - 4 3/4"
C4X5.4 | GALVANIZED STEEL CHANNEL | 29' - 5
19/32"
2nd Floor | 883' - 2 1/2" | 883' - 0 3/4" | 883' - 4 3/4"
C4X5.4 | GALVANIZED STEEL CHANNEL | 50' - 11
11/32"
2nd Floor | 883' - 2 1/2" | 883' - 0 3/4" | 883' - 4 3/4"

Structural Column Schedule

MARK | TYPE | LEVEL

LEVEL
| | OFFSET | COLUMN LOCATION | LENGTH | DESCRIPTION - FINISH | Top Offset

Basement
5 1/8" x 6" G.L. | Basement | 0' - 2" | B.5-E | 6' - 5 3/4" | GLULAMS COLUMNS - EXTERIOR (PRESSURE TREATED W/ PENTA IN SOLVENT) (STAIN: PENOFIN VERDE EXT. STAIN - COLOR: CEDAR) | -1' - 1"
5 1/8" x 6" G.L. | Basement | 0' - 2" | B.5-E.1 | 6' - 6 3/4" | GLULAMS COLUMNS - EXTERIOR (PRESSURE TREATED W/ PENTA IN SOLVENT) (STAIN: PENOFIN VERDE EXT. STAIN - COLOR: CEDAR) | -1' - 0"
5 1/8" x 6" G.L. | Basement | 0' - 2" | E-2 | 6' - 5 3/4" | GLULAMS COLUMNS - EXTERIOR (PRESSURE TREATED W/ PENTA IN SOLVENT) (STAIN: PENOFIN VERDE EXT. STAIN - COLOR: CEDAR) | -1' - 1"
5 1/8" x 6" G.L. | Basement | 0' - 2" | E-3 | 6' - 5 3/4" | GLULAMS COLUMNS - EXTERIOR (PRESSURE TREATED W/ PENTA IN SOLVENT) (STAIN: PENOFIN VERDE EXT. STAIN - COLOR: CEDAR) | -1' - 1"
5 1/8" x 6" G.L. | Basement | 0' - 2" | E.1-2 | 6' - 6 3/4" | GLULAMS COLUMNS - EXTERIOR (PRESSURE TREATED W/ PENTA IN SOLVENT) (STAIN: PENOFIN VERDE EXT. STAIN - COLOR: CEDAR) | -1' - 0"
5 1/8" x 6" G.L. | Basement | 0' - 2" | E.1-3 | 6' - 5 3/4" | GLULAMS COLUMNS - EXTERIOR (PRESSURE TREATED W/ PENTA IN SOLVENT) (STAIN: PENOFIN VERDE EXT. STAIN - COLOR: CEDAR) | -1' - 1"
5 1/8" x 6" G.L.: 6 | 39' - 0 1/2"
40" | Basement | -5' - 4 1/2" | E-1.AA | 5' - 1" | 40" DIAMETER X 5FT DEEP SONO PIER WITH (4) - #5 BARS VERTICAL AND #3 TIES AT 12" O.C. | -0' - 3 1/2"
40" | Basement | -5' - 4 1/2" | E-2 | 5' - 1" | 40" DIAMETER X 5FT DEEP SONO PIER WITH (4) - #5 BARS VERTICAL AND #3 TIES AT 12" O.C. | -0' - 3 1/2"
40" | Basement | -5' - 3 1/2" | E-3 | 5' - 0" | 40" DIAMETER X 5FT DEEP SONO PIER WITH (4) - #5 BARS VERTICAL AND #3 TIES AT 12" O.C. | -0' - 3 1/2"
40": 3 | 15' - 2"
PIPE COLUMN | Basement | 0' - 0" | B(-2' - 0 13/16")-5.A(2' - 10 29/32") | 7' - 0 1/4" | Steel ASTM A53 | -0' - 8 1/2"
PIPE COLUMN: 1 | | | | 7' - 0 1/4"
Basement: 10 | | | | 61' - 2 3/4"
1st Floor
5 1/8" x 6" G.L. | 1st Floor | 0' - 0" | B.5-E | 9' - 0" | GLULAMS COLUMNS - EXTERIOR (PRESSURE TREATED W/ PENTA IN SOLVENT) (STAIN: PENOFIN VERDE EXT. STAIN - COLOR: CEDAR) | -0' - 2 1/2"
5 1/8" x 6" G.L. | 1st Floor | 0' - 0" | E-2 | 7' - 9" | GLULAMS COLUMNS - EXTERIOR (PRESSURE TREATED W/ PENTA IN SOLVENT) (STAIN: PENOFIN VERDE EXT. STAIN - COLOR: CEDAR) | -1' - 5 1/2"
5 1/8" x 6" G.L. | 1st Floor | 0' - 0" | E-3 | 7' - 9" | GLULAMS COLUMNS - EXTERIOR (PRESSURE TREATED W/ PENTA IN SOLVENT) (STAIN: PENOFIN VERDE EXT. STAIN - COLOR: CEDAR) | -1' - 5 1/2"
5 1/8" x 6" G.L. | 1st Floor | -0' - 0 3/4" | B-2 | 6' - 9 11/32" | GLULAMS COLUMNS - INTERIOR - (STAIN TO MATCH EXTERIOR COLUMNS) | -2' - 5 29/32"
5 1/8" x 6" G.L. | 1st Floor | -0' - 0 3/4" | B-2.9 | 6' - 9 11/32" | GLULAMS COLUMNS - INTERIOR - (STAIN TO MATCH EXTERIOR COLUMNS) | -2' - 5 29/32"
5 1/8" x 6" G.L. | 1st Floor | -1' - 0" | B-3 | 8' - 2 1/2" | GLULAMS COLUMNS - INTERIOR - (STAIN TO MATCH EXTERIOR COLUMNS) | -2' - 0"
5 1/8" x 6" G.L. | 1st Floor | -1' - 0" | B-5.A | 9' - 4 1/2" | GLULAMS COLUMNS - INTERIOR - (STAIN TO MATCH EXTERIOR COLUMNS) | -0' - 10"
5 1/8" x 6" G.L. | 1st Floor | -0' - 0 3/4" | B-B.5 | 8' - 5 1/4" | GLULAMS COLUMNS - INTERIOR - (STAIN TO MATCH EXTERIOR COLUMNS) | -0' - 10"
5 1/8" x 6" G.L. | 1st Floor | -0' - 0 3/4" | B-B.5(-1' - 0 3/16") | 6' - 9 11/32" | GLULAMS COLUMNS - INTERIOR - (STAIN TO MATCH EXTERIOR COLUMNS) | -2' - 5 29/32"
5 1/8" x 6" G.L. | 1st Floor | -0' - 0 3/4" | B.5-C.2 | 8' - 5 1/4" | GLULAMS COLUMNS - INTERIOR - (STAIN TO MATCH EXTERIOR COLUMNS) | -0' - 10"
5 1/8" x 6" G.L. | 1st Floor | -0' - 0 3/4" | C.2-2 | 8' - 0 3/4" | GLULAMS COLUMNS - INTERIOR - (STAIN TO MATCH EXTERIOR COLUMNS) | -1' - 2 1/2"
5 1/8" x 6" G.L. | 1st Floor | -0' - 0 3/4" | C.2-2.2 | 8' - 5 1/4" | GLULAMS COLUMNS - INTERIOR - (STAIN TO MATCH EXTERIOR COLUMNS) | -0' - 10"
5 1/8" x 6" G.L. | 1st Floor | -1' - 0" | C.2-3 | 8' - 9" | GLULAMS COLUMNS - INTERIOR - (STAIN TO MATCH EXTERIOR COLUMNS) | -1' - 5 1/2"
5 1/8" x 6" G.L. | 1st Floor | -1' - 0" | C.2-5.A | 9' - 4 1/2" | GLULAMS COLUMNS - INTERIOR - (STAIN TO MATCH EXTERIOR COLUMNS) | -0' - 10"
5 1/8" x 6" G.L.: 14 | 113' - 11 1/16"
5 1/8" X 6" GLULAM @ JAMB | 1st Floor | -0' - 0 3/4" | C.1(0' - 8 1/16")-1.5(-3' -1 13/32") | 8' - 3 1/4" | GLULAMS COLUMNS - INTERIOR - (STAIN TO MATCH EXTERIOR COLUMNS) | -1' - 0"
5 1/8" X 6" GLULAM @ JAMB | 1st Floor | -1' - 0" | C.1(0' - 8 1/16")-4(1' - 2 3/4") | 9' - 8 1/2" | GLULAMS COLUMNS - INTERIOR - (STAIN TO MATCH EXTERIOR COLUMNS) | -0' - 6"
5 1/8" X 6" GLULAM @ JAMB | 1st Floor | -1' - 0" | C.1(0' - 8 3/8")-3(-4' - 10 3/4") | 9' - 8 1/2" | GLULAMS COLUMNS - INTERIOR - (STAIN TO MATCH EXTERIOR COLUMNS) | -0' - 6"
5 1/8" X 6" GLULAM @ JAMB: 3 | 27' - 8 1/4"
1st Floor: 17 | 141' - 7 5/16"

2nd Floor
5 1/8" x 6" G.L. | 2nd Floor | -0' - 2 1/2" | B-2 | 13' - 2 1/4" | GLULAMS COLUMNS - INTERIOR - (STAIN TO MATCH EXTERIOR COLUMNS) | 4' - 8 1/2"
5 1/8" x 6" G.L. | 2nd Floor | -1' - 0" | B-3 | 13' - 11 3/4" | GLULAMS COLUMNS - INTERIOR - (STAIN TO MATCH EXTERIOR COLUMNS) | 4' - 8 1/2"
5 1/8" x 6" G.L. | 2nd Floor | -0' - 10" | B-5.A | 13' - 9 3/4" | GLULAMS COLUMNS - INTERIOR - (STAIN TO MATCH EXTERIOR COLUMNS) | 4' - 8 1/2"
5 1/8" x 6" G.L. | 2nd Floor | -0' - 10" | B-B.5 | 13' - 9 3/4" | GLULAMS COLUMNS - INTERIOR - (STAIN TO MATCH EXTERIOR COLUMNS) | 4' - 8 1/2"
5 1/8" x 6" G.L. | 2nd Floor | -0' - 10" | B.5-C.2 | 9' - 4 1/2" | GLULAMS COLUMNS - INTERIOR - (STAIN TO MATCH EXTERIOR COLUMNS) | 0' - 3 1/4"
5 1/8" x 6" G.L. | 2nd Floor | -0' - 2 1/2" | C.2-2 | 8' - 9" | GLULAMS COLUMNS - INTERIOR - (STAIN TO MATCH EXTERIOR COLUMNS) | 0' - 3 1/4"
5 1/8" x 6" G.L. | 2nd Floor | -0' - 10" | C.2-2.2 | 9' - 4 1/2" | GLULAMS COLUMNS - INTERIOR - (STAIN TO MATCH EXTERIOR COLUMNS) | 0' - 3 1/4"
5 1/8" x 6" G.L. | 2nd Floor | -0' - 2 1/2" | C.2-3 | 8' - 9" | GLULAMS COLUMNS - INTERIOR - (STAIN TO MATCH EXTERIOR COLUMNS) | 0' - 3 1/4"
5 1/8" x 6" G.L. | 2nd Floor | -0' - 10" | C.2-5.A | 9' - 4 1/2" | GLULAMS COLUMNS - INTERIOR - (STAIN TO MATCH EXTERIOR COLUMNS) | 0' - 3 1/4"
5 1/8" x 6" G.L.: 9 | 100' - 5"
2nd Floor: 9 | 100' - 5"
Date | Description

## 05.22.2017 Issue for Bid
