OpeningDesign/Vacation_Rental/Transfer/20170519 ----- ISSUE FOR BID & PERMIT -------/The Downtowner_HVAC - Sheet - M-002 - HVAC 1st & 2nd Floor plan.pdf

# BCDE

# ABCDE

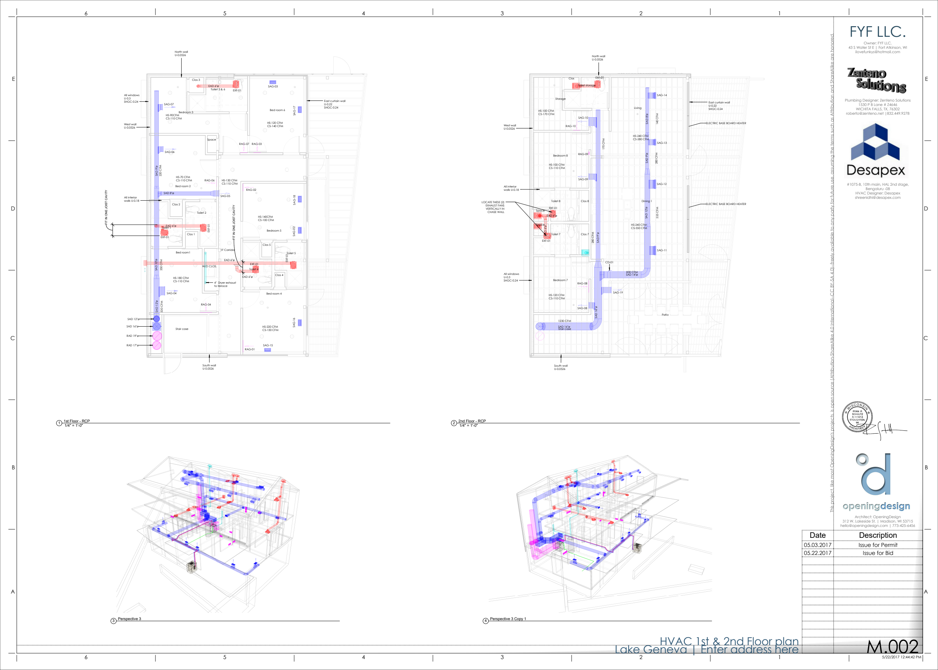
[picture p242: page 1]

Stair case

Clos 1

Clos 2

Clos 4

Clos 5

Bed room1

Clos 3

Space

Bed room 2

Toilet 3 & 6

Bed room 6

1F Corridor

Bedroom 5

Bed room 4

Toilet 1

Toilet 2

Toilet 5

Toilet 4

Bedroom 3

W/D CLOS.

HS-180 CFM
CS-110 CFM

SAD 12"ø

## 530 CFM 350 CFM 220 CFM

EXF-01

EXF-01

SAD 10"ø SAD 9"ø

EAD 6"ø

SAG-04

SAG-05

SAG-07

SAG-06

SAD 12"ø

EAD 6"ø

EAD 6"ø

EAD 6"ø
EXF-01

HS-70 CFM
CS-110 CFM

HS-90CFM
CS-110 CFM

HS-220 CFM
CS-130 CFM

HS-140CFM
CS-100 CFM

HS-120 CFM
CS-140 CFM

HS-130 CFM
CS-110 CFM

SAD 16"ø

RAD 19"ø

East curtain wall
U-0.22
SHGC-0.24

West wall
U-0.0526

North wall
U-0.0526

South wall
U-0.0526

All interior
walls U-0.18

All windows
U-0.3
SHGC-0.24

SAD 8"ø

RAD 17"ø

4" Dryer exhaust
to terrace

EXF-01

SAG-02

SAG-03

SAG-16

SAG-15

SAG-17 SAG-18

EXF-01

FIT IN ONE JOIST CAVITY

FIT IN ONE JOIST CAVITY

RAG-04

RAG-06

RAG-07 RAG-03

RAG-01

RAG-02

HS-120 CFM
CS-110 CFM

## SAD 16"ø SAD 9"ø

EXF-01

EXF-01

EXF-01

1230 CFM

830 CFM

280 CFM

## 555 CFM 280 CFM 140 CFM

SAD 14"ø

RAG-10

RAG-09

SAG-09

RAG-08

SAG-08

SAG-10

### SAD 12"ø SAD 9"ø SAD 8"ø

170 CFM

HS-100 CFM
CS-110 CFM

HS-100 CFM
CS-170 CFM

HS-240 CFM
CS-280 CFM

HS-240 CFM
CS-550 CFM

East curtain wall
U-0.22
SHGC-0.24

West wall
U-0.0526

North wall
U-0.0526

South wall
U-0.0526

All interior
walls U-0.18

All windows
U-0.3
SHGC-0.24

SAD 16"ø

EAD 6"ø

EAD 6"ø

CD-01

SAG-11

SAG-14

SAG-13

SAG-12

LOCATE THESE (2)
EXHAUST FANS
VERTICALLY IN
CHASE WALL

SAG-19

Stair case

Space

Bedroom 7

Space

Bedroom 8

Toilet 7 | Clos 7
Toilet 8 | Clos 8

Storage

Clos

Living

Dining 1

Toilet storage

Patio

ELECTRIC BASE BOARD HEATER

ELECTRIC BASE BOARD HEATER

## Architect: OpeningDesign 312 W. Lakeside St. | Madison, WI 53715 hello@openingdesign.com | 773-425-6456

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
Owner: FYF LLC.

## 43 S Water St E | Fort Atkinson, WI ilovefunkys@hotmail.com

FYF LLC.

## Plumbing Designer: Zenteno Solutions 1530 P B Lane # Z4646 WICHITA FALLS, TX, 76302 roberto@zenteno.net |832.449.9278

#1075-B, 10th main, HAL 2nd stage,

## Bengaluru -08 HVAC Designer: Desapex shreenidhi@desapex.com

This project, like most OpeningDesign's projects, is open source (Attribution-ShareAlike 4.0 International--CC BY-SA 4.0)--freely available to any party for future use, assuming the terms such as Attribution and ShareAlike are honored.

M.002

5/22/2017 12:44:42 PM

# HVAC 1st & 2nd Floor plan Lake Geneva | Enter address here

Date | Description

# 05.03.2017 Issue for Permit 05.22.2017 Issue for Bid

1/4" = 1'-0"

1

## 1st Floor - RCP

1/4" = 1'-0"

2

## 2nd Floor - RCP

3

## Perspective 3

4

## Perspective 3 Copy 1
