OpeningDesign/Vacation_Rental/Transfer/20170519 ----- ISSUE FOR BID & PERMIT -------/The_Downtowner_PLMB_ZS - Sheet - P0-00 - PLUMBING SYMBOLS & ABBREVIATIONS.pdf

PLUMBING PIPING LEGEND | PROJECT NOTES | DRAWING LIST

# PLUMBING ABBREVIATIONS

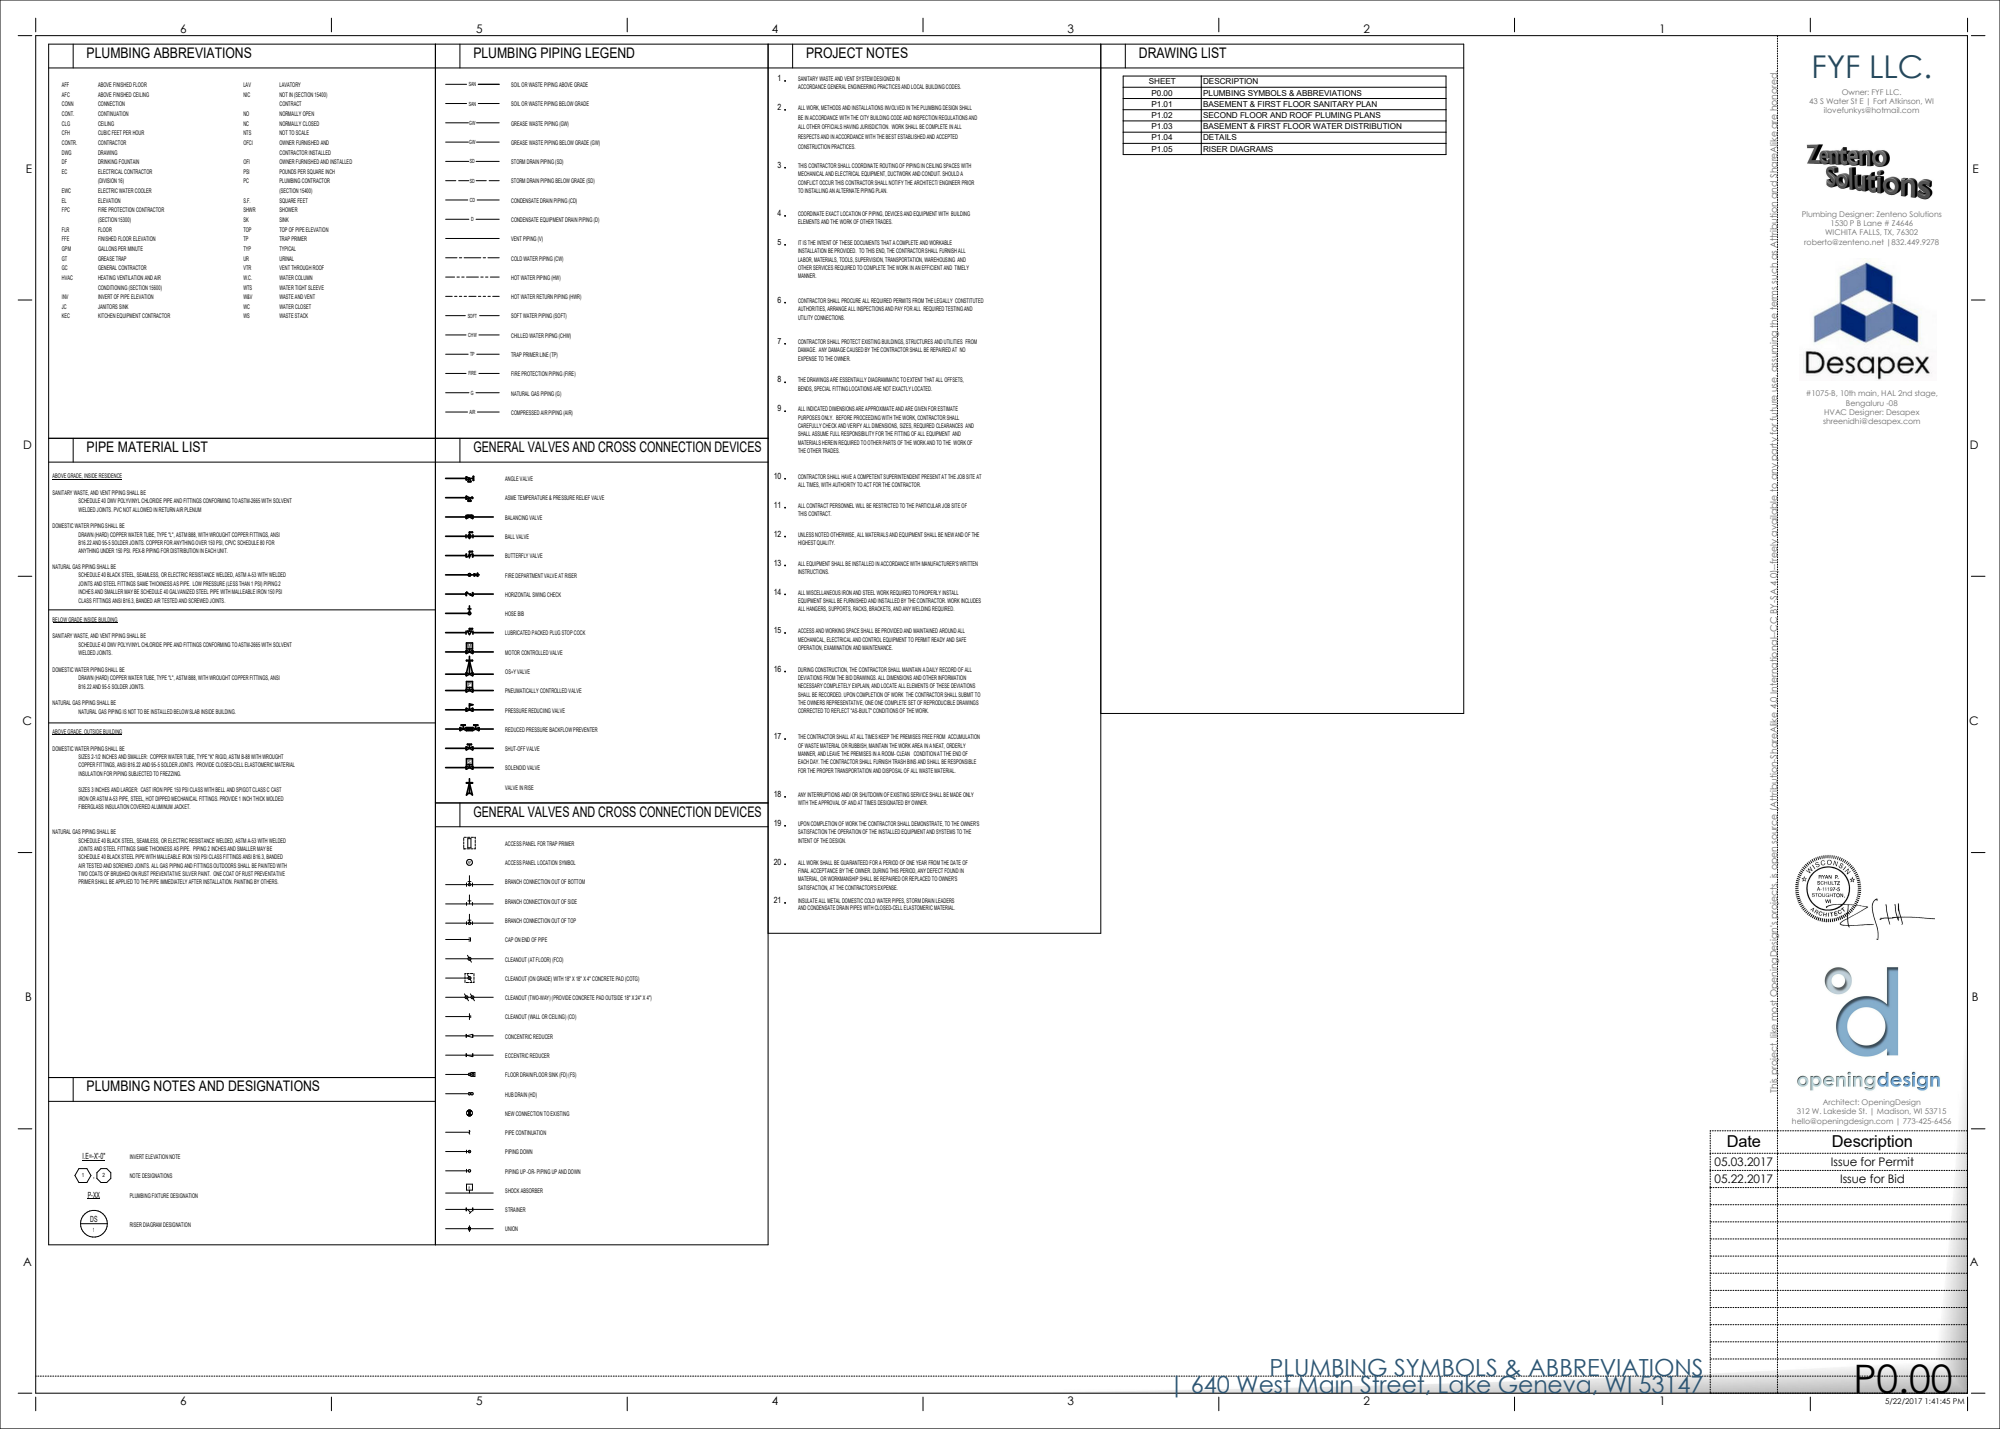
[picture p243: page 1]
PSI; OFI; OFCI; LAV; NIC; INV; HVAC; GPM; FPC; FFE; FLR; EWC; DWG; CONT.; CLG; CFH; AFC; CONN; AFF; SHWR; NTS; NOT TO SCALE; WTS; TYP; TOP; NORMALLY CLOSED; TRAP PRIMER; GREASE TRAP; SQUARE FEET; CONTR.; VTR; VENT PIPING (V); SAN; CHW; SOFT; FIRE; AIR; BALANCING VALVE; SOLENOID VALVE; BALL VALVE; BUTTERFLY VALVE; ANGLE VALVE; OS+Y VALVE; PIPING DOWN; UNION; ECCENTRIC REDUCER; CONCENTRIC REDUCER; STRAINER; HOSE BIB; SHOCK ABSORBER; NOTE DESIGNATIONS; KEC; KITCHEN EQUIPMENT CONTRACTOR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

This project, like most OpeningDesign's projects, is open source (Attribution-ShareAlike 4.0 International--CC BY-SA 4.0)--freely available to any party for future use, assuming the terms such as Attribution and ShareAlike are honored.

SANITARY WASTE AND VENT SYSTEM DESIGNED IN
ACCORDANCE GENERAL ENGINEERING PRACTICES AND LOCAL BUILDING CODES.

SHEET | DESCRIPTION
P0.00 | PLUMBING SYMBOLS & ABBREVIATIONS
P1.01 | BASEMENT & FIRST FLOOR SANITARY PLAN
P1.02 | SECOND FLOOR AND ROOF PLUMING PLANS
P1.03 | BASEMENT & FIRST FLOOR WATER DISTRIBUTION
P1.04 | DETAILS
P1.05 | RISER DIAGRAMS

ABOVE FINISHED FLOOR
ABOVE FINISHED CEILING
CONNECTION
CONTINUATION
CEILING
CUBIC FEET PER HOUR
CONTRACTOR
DRAWING
DRINKING FOUNTAIN
ELECTRICAL CONTRACTOR
(DIVISION 16)
ELECTRIC WATER COOLER
ELEVATION
FIRE PROTECTION CONTRACTOR

LAVATORY
NOT IN (SECTION 15400)
CONTRACT
NORMALLY OPEN

SOIL OR WASTE PIPING ABOVE GRADE

Owner: FYF LLC.

SOIL OR WASTE PIPING BELOW GRADE

43 S Water St E | Fort Atkinson, WI
ilovefunkys@hotmail.com

ALL WORK, METHODS AND INSTALLATIONS INVOLVED IN THE PLUMBING DESIGN SHALL
BE IN ACCORDANCE WITH THE CITY BUILDING CODE AND INSPECTION REGULATIONS AND
ALL OTHER OFFICIALS HAVING JURISDICTION. WORK SHALL BE COMPLETE IN ALL
RESPECTS AND IN ACCORDANCE WITH THE BEST ESTABLISHED AND ACCEPTED
CONSTRUCTION PRACTICES.

GREASE WASTE PIPING (GW)

OWNER FURNISHED AND
CONTRACTOR INSTALLED
OWNER FURNISHED AND INSTALLED
POUNDS PER SQUARE INCH
PLUMBING CONTRACTOR
(SECTION 15400)

GREASE WASTE PIPING BELOW GRADE (GW)

STORM DRAIN PIPING (SD)

THIS CONTRACTOR SHALL COORDINATE ROUTING OF PIPING IN CEILING SPACES WITH
MECHANICAL AND ELECTRICAL EQUIPMENT, DUCTWORK AND CONDUIT. SHOULD A
CONFLICT OCCUR THIS CONTRACTOR SHALL NOTIFY THE ARCHITECT/ ENGINEER PRIOR
TO INSTALLING AN ALTERNATE PIPING PLAN.

STORM DRAIN PIPING BELOW GRADE (SD)

CONDENSATE DRAIN PIPING (CD)

SHOWER
SINK
TOP OF PIPE ELEVATION

COORDINATE EXACT LOCATION OF PIPING, DEVICES AND EQUIPMENT WITH BUILDING
ELEMENTS AND THE WORK OF OTHER TRADES.

Plumbing Designer: Zenteno Solutions

(SECTION 15300)
FLOOR
FINISHED FLOOR ELEVATION
GALLONS PER MINUTE

CONDENSATE EQUIPMENT DRAIN PIPING (D)

1530 P B Lane # Z4646
WICHITA FALLS, TX, 76302
roberto@zenteno.net |832.449.9278

IT IS THE INTENT OF THESE DOCUMENTS THAT A COMPLETE AND WORKABLE
INSTALLATION BE PROVIDED. TO THIS END, THE CONTRACTOR SHALL FURNISH ALL
LABOR, MATERIALS, TOOLS, SUPERVISION, TRANSPORTATION, WAREHOUSING AND
OTHER SERVICES REQUIRED TO COMPLETE THE WORK IN AN EFFICIENT AND TIMELY
MANNER.

TYPICAL
URINAL
VENT THROUGH ROOF
WATER COLUMN
WATER TIGHT SLEEVE
WASTE AND VENT
WATER CLOSET
WASTE STACK

COLD WATER PIPING (CW)

GENERAL CONTRACTOR
HEATING VENTILATION AND AIR
CONDITIONING (SECTION 15600)
INVERT OF PIPE ELEVATION
JANITORS SINK

HOT WATER PIPING (HW)

HOT WATER RETURN PIPING (HWR)

CONTRACTOR SHALL PROCURE ALL REQUIRED PERMITS FROM THE LEGALLY CONSTITUTED
AUTHORITIES, ARRANGE ALL INSPECTIONS AND PAY FOR ALL REQUIRED TESTING AND
UTILITY CONNECTIONS.

SOFT WATER PIPING (SOFT)

CHILLED WATER PIPNG (CHW)

CONTRACTOR SHALL PROTECT EXISTING BUILDINGS, STRUCTURES AND UTILITIES FROM
DAMAGE. ANY DAMAGE CAUSED BY THE CONTRACTOR SHALL BE REPAIRED AT NO
EXPENSE TO THE OWNER.

TRAP PRIMER LINE (TP)

FIRE PROTECTION PIPING (FIRE)

THE DRAWINGS ARE ESSENTIALLY DIAGRAMMATIC TO EXTENT THAT ALL OFFSETS,
BENDS, SPECIAL FITTING LOCATIONS ARE NOT EXACTLY LOCATED.

NATURAL GAS PIPING (G)

#1075-B, 10th main, HAL 2nd stage,

Bengaluru -08
HVAC Designer: Desapex
shreenidhi@desapex.com

COMPRESSED AIR PIPING (AIR)

ALL INDICATED DIMENSIONS ARE APPROXIMATE AND ARE GIVEN FOR ESTIMATE
PURPOSES ONLY. BEFORE PROCEEDING WITH THE WORK, CONTRACTOR SHALL
CAREFULLY CHECK AND VERIFY ALL DIMENSIONS, SIZES, REQUIRED CLEARANCES AND
SHALL ASSUME FULL RESPONSIBILITY FOR THE FITTING OF ALL EQUIPMENT AND
MATERIALS HEREIN REQUIRED TO OTHER PARTS OF THE WORK AND TO THE WORK OF
THE OTHER TRADES.

PIPE MATERIAL LIST

GENERAL VALVES AND CROSS CONNECTION DEVICES

ABOVE GRADE, INSIDE RESIDENCE

CONTRACTOR SHALL HAVE A COMPETENT SUPERINTENDENT PRESENT AT THE JOB SITE AT
ALL TIMES, WITH AUTHORITY TO ACT FOR THE CONTRACTOR.

SANITARY WASTE, AND VENT PIPING SHALL BE

SCHEDULE 40 DWV POLYVINYL CHLORIDE PIPE AND FITTINGS CONFORMING TO ASTM-2665 WITH SOLVENT
WELDED JOINTS. PVC NOT ALLOWED IN RETURN AIR PLENUM

ASME TEMPERATURE & PRESSURE RELIEF VALVE

ALL CONTRACT PERSONNEL WILL BE RESTRICTED TO THE PARTICULAR JOB SITE OF
THIS CONTRACT.

DOMESTIC WATER PIPING SHALL BE

DRAWN (HARD) COPPER WATER TUBE, TYPE "L", ASTM B88, WITH WROUGHT COPPER FITTINGS, ANSI
B16.22 AND 95-5 SOLDER JOINTS. COPPER FOR ANYTHING OVER 150 PSI, CPVC SCHEDULE 80 FOR
ANYTHING UNDER 150 PSI. PEX-B PIPING FOR DISTRIBUTION IN EACH UNIT.

UNLESS NOTED OTHERWISE, ALL MATERIALS AND EQUIPMENT SHALL BE NEW AND OF THE
HIGHEST QUALITY.

ALL EQUIPMENT SHALL BE INSTALLED IN ACCORDANCE WITH MANUFACTURER'S WRITTEN
INSTRUCTIONS.

NATURAL GAS PIPING SHALL BE

SCHEDULE 40 BLACK STEEL, SEAMLESS, OR ELECTRIC RESISTANCE WELDED, ASTM A-53 WITH WELDED
JOINTS AND STEEL FITTINGS SAME THICKNESS AS PIPE. LOW PRESSURE (LESS THAN 1 PSI) PIPING 2
INCHES AND SMALLER MAY BE SCHEDULE 40 GALVANIZED STEEL PIPE WITH MALLEABLE IRON 150 PSI
CLASS FITTINGS ANSI B16.3, BANDED AIR TESTED AND SCREWED JOINTS.

FIRE DEPARTMENT VALVE AT RISER

ALL MISCELLANEOUS IRON AND STEEL WORK REQUIRED TO PROPERLY INSTALL
EQUIPMENT SHALL BE FURNISHED AND INSTALLED BY THE CONTRACTOR. WORK INCLUDES
ALL HANGERS, SUPPORTS, RACKS, BRACKETS, AND ANY WELDING REQUIRED.

HORIZONTAL SWING CHECK

BELOW GRADE INSIDE BUILDING

LUBRICATED PACKED PLUG STOP COCK

ACCESS AND WORKING SPACE SHALL BE PROVIDED AND MAINTAINED AROUND ALL
MECHANICAL, ELECTRICAL AND CONTROL EQUIPMENT TO PERMIT READY AND SAFE
OPERATION, EXAMINATION AND MAINTENANCE.

WELDED JOINTS.

MOTOR CONTROLLED VALVE

DURING CONSTRUCTION, THE CONTRACTOR SHALL MAINTAIN A DAILY RECORD OF ALL
DEVIATIONS FROM THE BID DRAWINGS. ALL DIMENSIONS AND OTHER INFORMATION
NECESSARY COMPLETELY EXPLAIN, AND LOCATE ALL ELEMENTS OF THESE DEVIATIONS
SHALL BE RECORDED. UPON COMPLETION OF WORK THE CONTRACTOR SHALL SUBMIT TO
THE OWNERS REPRESENTATIVE, ONE ONE COMPLETE SET OF REPRODUCIBLE DRAWINGS
CORRECTED TO REFLECT "AS-BUILT" CONDITIONS OF THE WORK.

B16.22 AND 95-5 SOLDER JOINTS.

PNEUMATICALLY CONTROLLED VALVE

NATURAL GAS PIPING IS NOT TO BE INSTALLED BELOW SLAB INSIDE BUILDING.

PRESSURE REDUCIING VALVE

REDUCED PRESSURE BACKFLOW PREVENTER

ABOVE GRADE, OUTSIDE BUILDING

THE CONTRACTOR SHALL AT ALL TIMES KEEP THE PREMISES FREE FROM ACCUMULATION
OF WASTE MATERIAL OR RUBBISH, MAINTAIN THE WORK AREA IN A NEAT, ORDERLY
MANNER, AND LEAVE THE PREMISES IN A ROOM- CLEAN CONDITION AT THE END OF
EACH DAY. THE CONTRACTOR SHALL FURNISH TRASH BINS AND SHALL BE RESPONSIBLE
FOR THE PROPER TRANSPORTATION AND DISPOSAL OF ALL WASTE MATERIAL.

SHUT-OFF VALVE

SIZES 2-1/2 INCHES AND SMALLER: COPPER WATER TUBE, TYPE "K" RIGID, ASTM B-88 WITH WROUGHT
COPPER FITTINGS, ANSI B16.22 AND 95-5 SOLDER JOINTS. PROVIDE CLOSED-CELL ELASTOMERIC MATERIAL
INSULATION FOR PIPING SUBJECTED TO FREZZING.

VALVE IN RISE

SIZES 3 INCHES AND LARGER: CAST IRON PIPE 150 PSI CLASS WITH BELL AND SPIGOT CLASS C CAST
IRON OR ASTM A-53 PIPE, STEEL, HOT DIPPED MECHANICAL FITTINGS. PROVIDE 1 INCH THICK MOLDED
FIBERGLASS INSULATION COVERED ALUMINUM JACKET.

ANY INTERRUPTIONS AND/ OR SHUTDOWN OF EXISTING SERVICE SHALL BE MADE ONLY
WITH THE APPROVAL OF AND AT TIMES DESIGNATED BY OWNER.

UPON COMPLETION OF WORK THE CONTRACTOR SHALL DEMONSTRATE, TO THE OWNER'S
SATISFACTION THE OPERATION OF THE INSTALLED EQUIPMENT AND SYSTEMS TO THE
INTENT OF THE DESIGN.

JOINTS AND STEEL FITTINGS SAME THICKNESS AS PIPE. PIPING 2 INCHES AND SMALLER MAY BE
SCHEDULE 40 BLACK STEEL PIPE WITH MALLEABLE IRON 150 PSI CLASS FITTINGS ANSI B16.3, BANDED
AIR TESTED AND SCREWED JOINTS. ALL GAS PIPING AND FITTINGS OUTDOORS SHALL BE PAINTED WITH
TWO COATS OF BRUSHED ON RUST PREVENTATIVE SILVER PAINT. ONE COAT OF RUST PREVENTATIVE
PRIMER SHALL BE APPLIED TO THE PIPE IMMEDIATELY AFTER INSTALLATION. PAINTING BY OTHERS.

ACCESS PANEL FOR TRAP PRIMER

ALL WORK SHALL BE GUARANTEED FOR A PERIOD OF ONE YEAR FROM THE DATE OF
FINAL ACCEPTANCE BY THE OWNER. DURING THIS PERIOD, ANY DEFECT FOUND IN
MATERIAL, OR WORKMANSHIP SHALL BE REPAIRED OR REPLACED TO OWNER'S
SATISFACTION, AT THE CONTRACTOR'S EXPENSE.

ACCESS PANEL LOCATION SYMBOL CLEANOUT (AT FLOOR) (FCO) CLEANOUT (ON GRADE) WITH 18" X 18" X 4" CONCRETE PAD (COTG) CLEANOUT (TWO-WAY) (PROVIDE CONCRETE PAD OUTSIDE 18" X 24" X 4") HUB DRAIN (HD) PIPE CONTINUATION

BRANCH CONNECTION OUT OF BOTTOM

BRANCH CONNECTION OUT OF SIDE

AND CONDENSATE DRAIN PIPES WITH CLOSED-CELL ELASTOMERIC MATERIAL.

BRANCH CONNECTION OUT OF TOP

CAP ON END OF PIPE

CLEANOUT (WALL OR CEILING) (CO)

FLOOR DRAIN/FLOOR SINK (FD) (FS)

PLUMBING NOTES AND DESIGNATIONS

312 W. Lakeside St. | Madison, WI 53715
hello@openingdesign.com | 773-425-6456

NEW CONNECTION TO EXISTING

I.E=-X'-0" P-XX DS 1 | | INVERT ELEVATION NOTE PLUMBING FIXTURE DESIGNATION RISER DIAGRAM DESIGNATION

05.03.2017 Issue for Permit
05.22.2017 Issue for Bid

PIPING UP -OR- PIPING UP AND DOWN

PLUMBING SYMBOLS & ABBREVIATIONS

640 West Main Street, Lake Geneva, WI 53147
