OpeningDesign/Vacation_Rental/Transfer/20170503 ----- ISSUE FOR PERMIT ------/A000 - SITE PLAN & CODE SUMMARY.pdf

# MAIN STREET

E

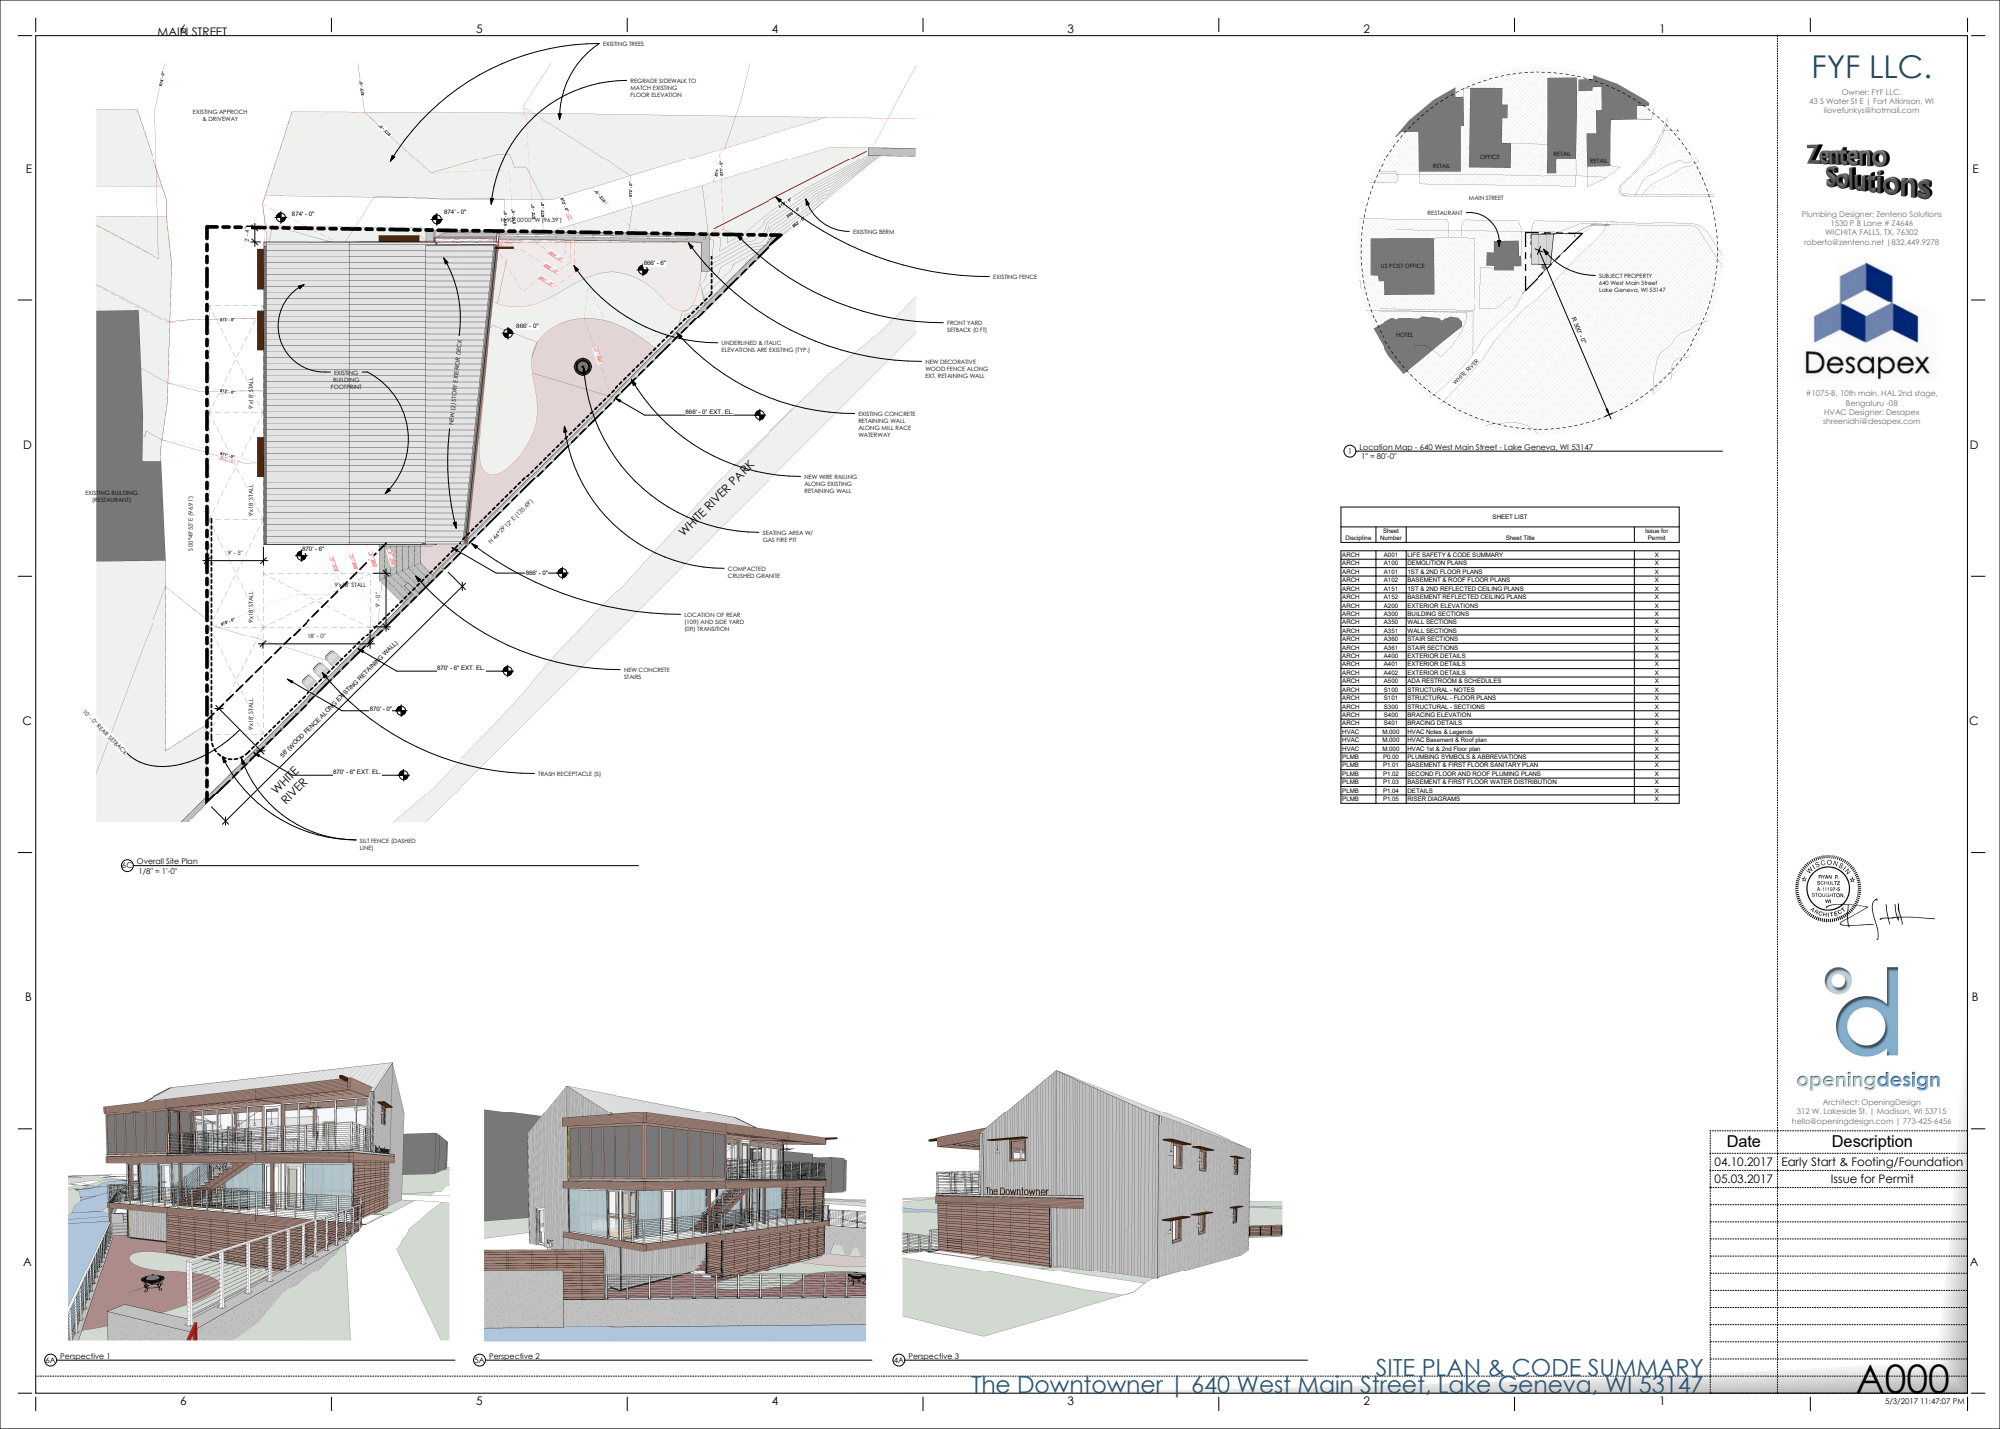
[picture p245: page 1]
870' - 6" EXT. EL.; 866' - 0" EXT. EL.; EXISTING BERM; 9'x18' STALL; 10' - 0" REAR SETBACK; EXISTING APPROCH & DRIVEWAY; EXISTING TREES; TRASH RECEPTACLE (S); WHITE RIVER; EXISTING FENCE; COMPACTED CRUSHED GRANITE; FOOTPRINT; EXT; FRONT YARD SETBACK (0 FT); EXISTING BUILDING (RESTAURANT); HOTEL; RESTAURANT; OFFICE; RETAIL RETAIL; RETAIL; MAIN STREET; Architect: OpeningDesign; FYF LLC.; SITE PLAN & CODE SUMMARY The Downtowner | 640 West Main Street, Lake Geneva, WI 53147 ⁶A Perspective 1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

REGRADE SIDEWALK TO
MATCH EXISTING
FLOOR ELEVATION

Owner: FYF LLC.

43 S Water St E | Fort Atkinson, WI
ilovefunkys@hotmail.com

Plumbing Designer: Zenteno Solutions

1530 P B Lane # Z4646
WICHITA FALLS, TX, 76302
roberto@zenteno.net |832.449.9278

US POST OFFICE

SUBJECT PROPERTY
640 West Main Street
Lake Geneva, WI 53147

UNDERLINED & ITALIC
ELEVATIONS ARE EXISTING (TYP.)

NEW DECORATIVE
WOOD FENCE ALONG

EXT. RETAINING WALL EXISTING BUILDING

9'x18' STALL 9'x18' STALL 9'x18' STALL

#1075-B, 10th main, HAL 2nd stage,

Bengaluru -08
HVAC Designer: Desapex
shreenidhi@desapex.com

EXISTING CONCRETE
RETAINING WALL
ALONG MILL RACE
WATERWAY

1" = 80'-0" 1 Location Map - 640 West Main Street - Lake Geneva, WI 53147

WHITE RIVER PARK

NEW WIRE RAILING
ALONG EXISTING

SEATING AREA W/
GAS FIRE PIT

ARCH | A001 | LIFE SAFETY & CODE SUMMARY | X
ARCH | A100 | DEMOLITION PLANS | X
ARCH | A101 | 1ST & 2ND FLOOR PLANS | X
ARCH | A102 | BASEMENT & ROOF FLOOR PLANS | X
ARCH | A151 | 1ST & 2ND REFLECTED CEILING PLANS | X
ARCH | A152 | BASEMENT REFLECTED CEILING PLANS | X
ARCH | A200 | EXTERIOR ELEVATIONS | X
ARCH | A300 | BUILDING SECTIONS | X
ARCH | A350 | WALL SECTIONS | X
ARCH | A351 | WALL SECTIONS | X
ARCH | A360 | STAIR SECTIONS | X
ARCH | A361 | STAIR SECTIONS | X
ARCH | A400 | EXTERIOR DETAILS | X
ARCH | A401 | EXTERIOR DETAILS | X
ARCH | A402 | EXTERIOR DETAILS | X
ARCH | A500 | ADA RESTROOM & SCHEDULES | X
ARCH | S100 | STRUCTURAL - NOTES | X
ARCH | S101 | STRUCTURAL - FLOOR PLANS | X
ARCH | S300 | STRUCTURAL - SECTIONS | X
ARCH | S400 | BRACING ELEVATION | X
ARCH | S401 | BRACING DETAILS | X
HVAC | M.000 | HVAC Notes & Legends | X
HVAC | M.000 | HVAC Basement & Roof plan | X
HVAC | M.000 | HVAC 1st & 2nd Floor plan | X
PLMB | P0.00 | PLUMBING SYMBOLS & ABBREVIATIONS | X
PLMB | P1.01 | BASEMENT & FIRST FLOOR SANITARY PLAN | X
PLMB | P1.02 | SECOND FLOOR AND ROOF PLUMING PLANS | X
PLMB | P1.03 | BASEMENT & FIRST FLOOR WATER DISTRIBUTION | X
PLMB | P1.04 | DETAILS | X
PLMB | P1.05 | RISER DIAGRAMS | X

LOCATION OF REAR
(10ft) AND SIDE YARD
(0ft) TRANSITION

56' (WOOD FENCE ALONG EXISTING RETAINING WALL) NEW CONCRETE STAIRS

SILT FENCE (DASHED
LINE)

1/8" = 1'-0" 6C Overall Site Plan

312 W. Lakeside St. | Madison, WI 53715
hello@openingdesign.com | 773-425-6456

04.10.2017 Early Start & Footing/Foundation
05.03.2017 Issue for Permit
