OpeningDesign/Vacation_Rental/Transfer/20170503 ----- ISSUE FOR PERMIT ------/A400 - EXTERIOR DETAILS.pdf

## Existing Roof Joist Bearing

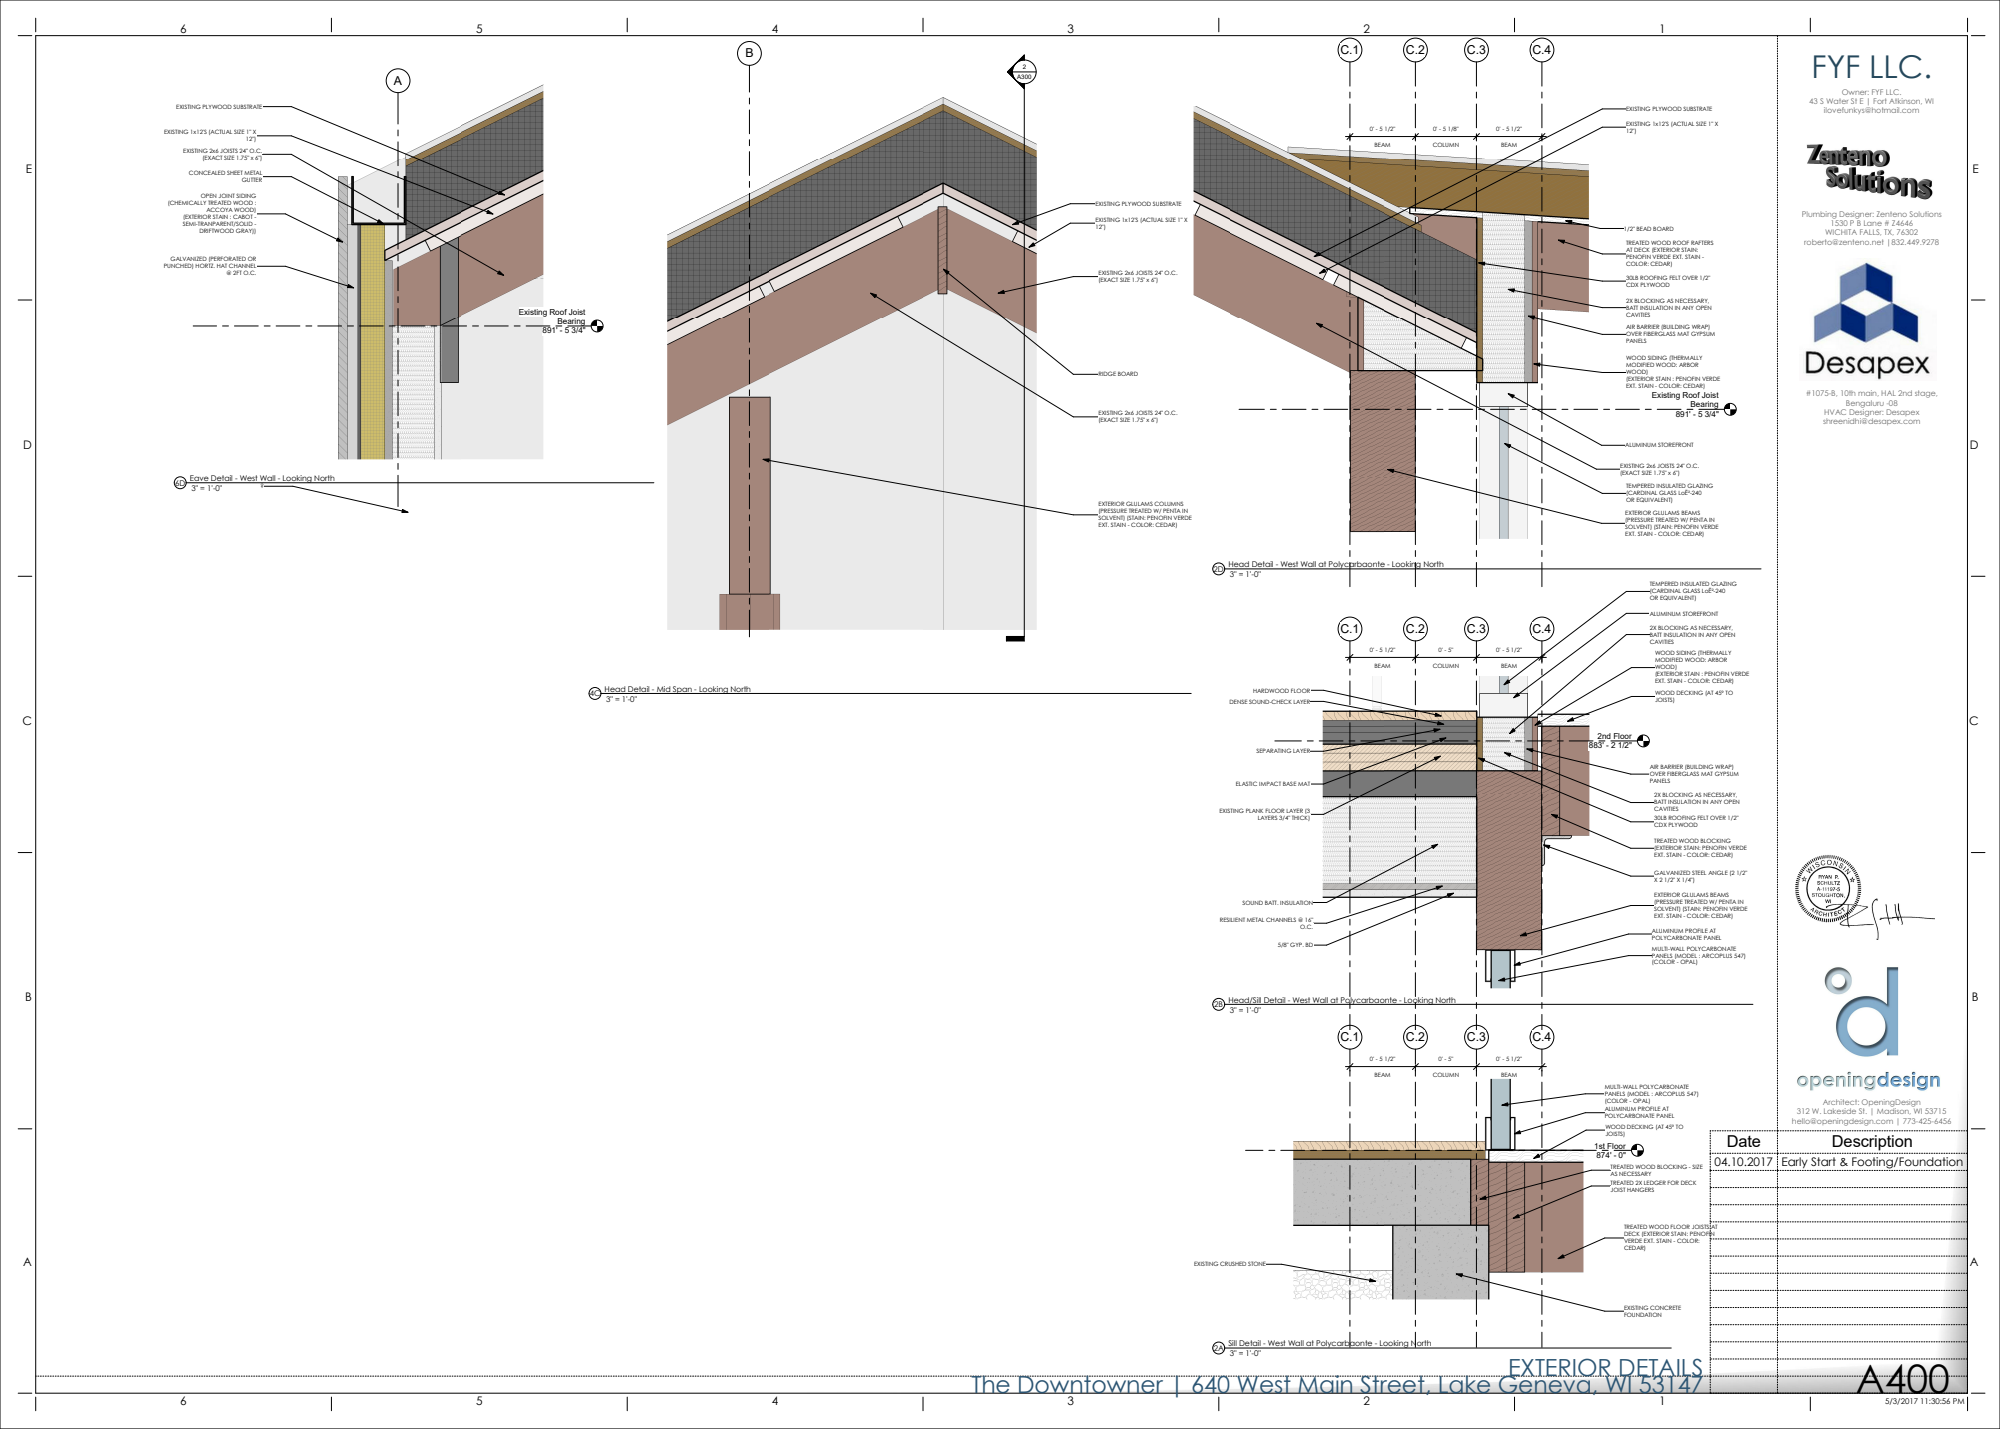
[picture p246: page 1]
ACCOYA WOOD); GUTTER; EXISTING 2x6 JOISTS 24" O.C. (EXACT SIZE 1.75" x 6"); RIDGE BOARD; Bearing 891' - 5 3/4"; 1/2" BEAD BOARD; BEAM; COLUMN; ALUMINUM STOREFRONT; 2nd Floor 883' - 2 1/2"; HARDWOOD FLOOR; SEPARATING LAYER; LAYERS 3/4" THICK); 5/8" GYP. BD; MULTI-WALL POLYCARBONATE; EXISTING CONCRETE FOUNDATION; Architect: OpeningDesign; FYF LLC.; Date; Description

Owner: FYF LLC.

43 S Water St E | Fort Atkinson, WI
ilovefunkys@hotmail.com

EXISTING PLYWOOD SUBSTRATE

EXISTING 1x12'S (ACTUAL SIZE 1" X

CONCEALED SHEET METAL

OPEN JOINT SIDING

(CHEMICALLY TREATED WOOD :

Plumbing Designer: Zenteno Solutions

(EXTERIOR STAIN : CABOT -
SEMI-TRANPARENT/SOLID -
DRIFTWOOD GRAY))

1530 P B Lane # Z4646
WICHITA FALLS, TX, 76302
roberto@zenteno.net |832.449.9278

TREATED WOOD ROOF RAFTERS
AT DECK (EXTERIOR STAIN:
PENOFIN VERDE EXT. STAIN -
COLOR: CEDAR)

GALVANIZED (PERFORATED OR
PUNCHED) HORTZ. HAT CHANNEL

30LB ROOFING FELT OVER 1/2"
CDX PLYWOOD

2X BLOCKING AS NECESSARY,
BATT INSULATION IN ANY OPEN
CAVITIES

AIR BARRIER (BUILDING WRAP)
OVER FIBERGLASS MAT GYPSUM
PANELS

WOOD SIDING (THERMALLY
MODIFIED WOOD: ARBOR
WOOD)
(EXTERIOR STAIN : PENOFIN VERDE
EXT. STAIN - COLOR: CEDAR)

Existing Roof Joist

#1075-B, 10th main, HAL 2nd stage,

Bengaluru -08
HVAC Designer: Desapex
shreenidhi@desapex.com

3" = 1'-0" 6D Eave Detail - West Wall - Looking North

TEMPERED INSULATED GLAZING
(CARDINAL GLASS LoĒ²-240
OR EQUIVALENT)

EXTERIOR GLULAMS COLUMNS
(PRESSURE TREATED W/ PENTA IN
SOLVENT) (STAIN: PENOFIN VERDE

EXTERIOR GLULAMS BEAMS

3" = 1'-0" 2D Head Detail - West Wall at Polycarbaonte - Looking North

3" = 1'-0" 4C Head Detail - Mid Span - Looking North

WOOD DECKING (AT 45° TO
JOISTS)

DENSE SOUND-CHECK LAYER

ELASTIC IMPACT BASE MAT

EXISTING PLANK FLOOR LAYER (3

TREATED WOOD BLOCKING
(EXTERIOR STAIN: PENOFIN VERDE

GALVANIZED STEEL ANGLE (2 1/2"

SOUND BATT. INSULATION

RESILIENT METAL CHANNELS @ 16"

ALUMINUM PROFILE AT
POLYCARBONATE PANEL

PANELS (MODEL : ARCOPLUS 547)
(COLOR - OPAL)

3" = 1'-0" 2B Head/Sill Detail - West Wall at Polycarbaonte - Looking North

MULTI-WALL POLYCARBONATE
1st Floor

312 W. Lakeside St. | Madison, WI 53715
hello@openingdesign.com | 773-425-6456

04.10.2017 Early Start & Footing/Foundation

TREATED WOOD BLOCKING - SIZE
AS NECESSARY
TREATED 2X LEDGER FOR DECK
JOIST HANGERS

TREATED WOOD FLOOR JOISTS AT
DECK (EXTERIOR STAIN: PENOFIN
VERDE EXT. STAIN - COLOR:
CEDAR)

EXISTING CRUSHED STONE

3" = 1'-0" 2A Sill Detail - West Wall at Polycarbaonte - Looking North

EXTERIOR DETAILS The Downtowner | 640 West Main Street, Lake Geneva, WI 53147
