OpeningDesign/Vacation_Rental/Transfer/20170503 ----- ISSUE FOR PERMIT ------/A401 - EXTERIOR DETAILS.pdf

## Existing Roof Joist Bearing

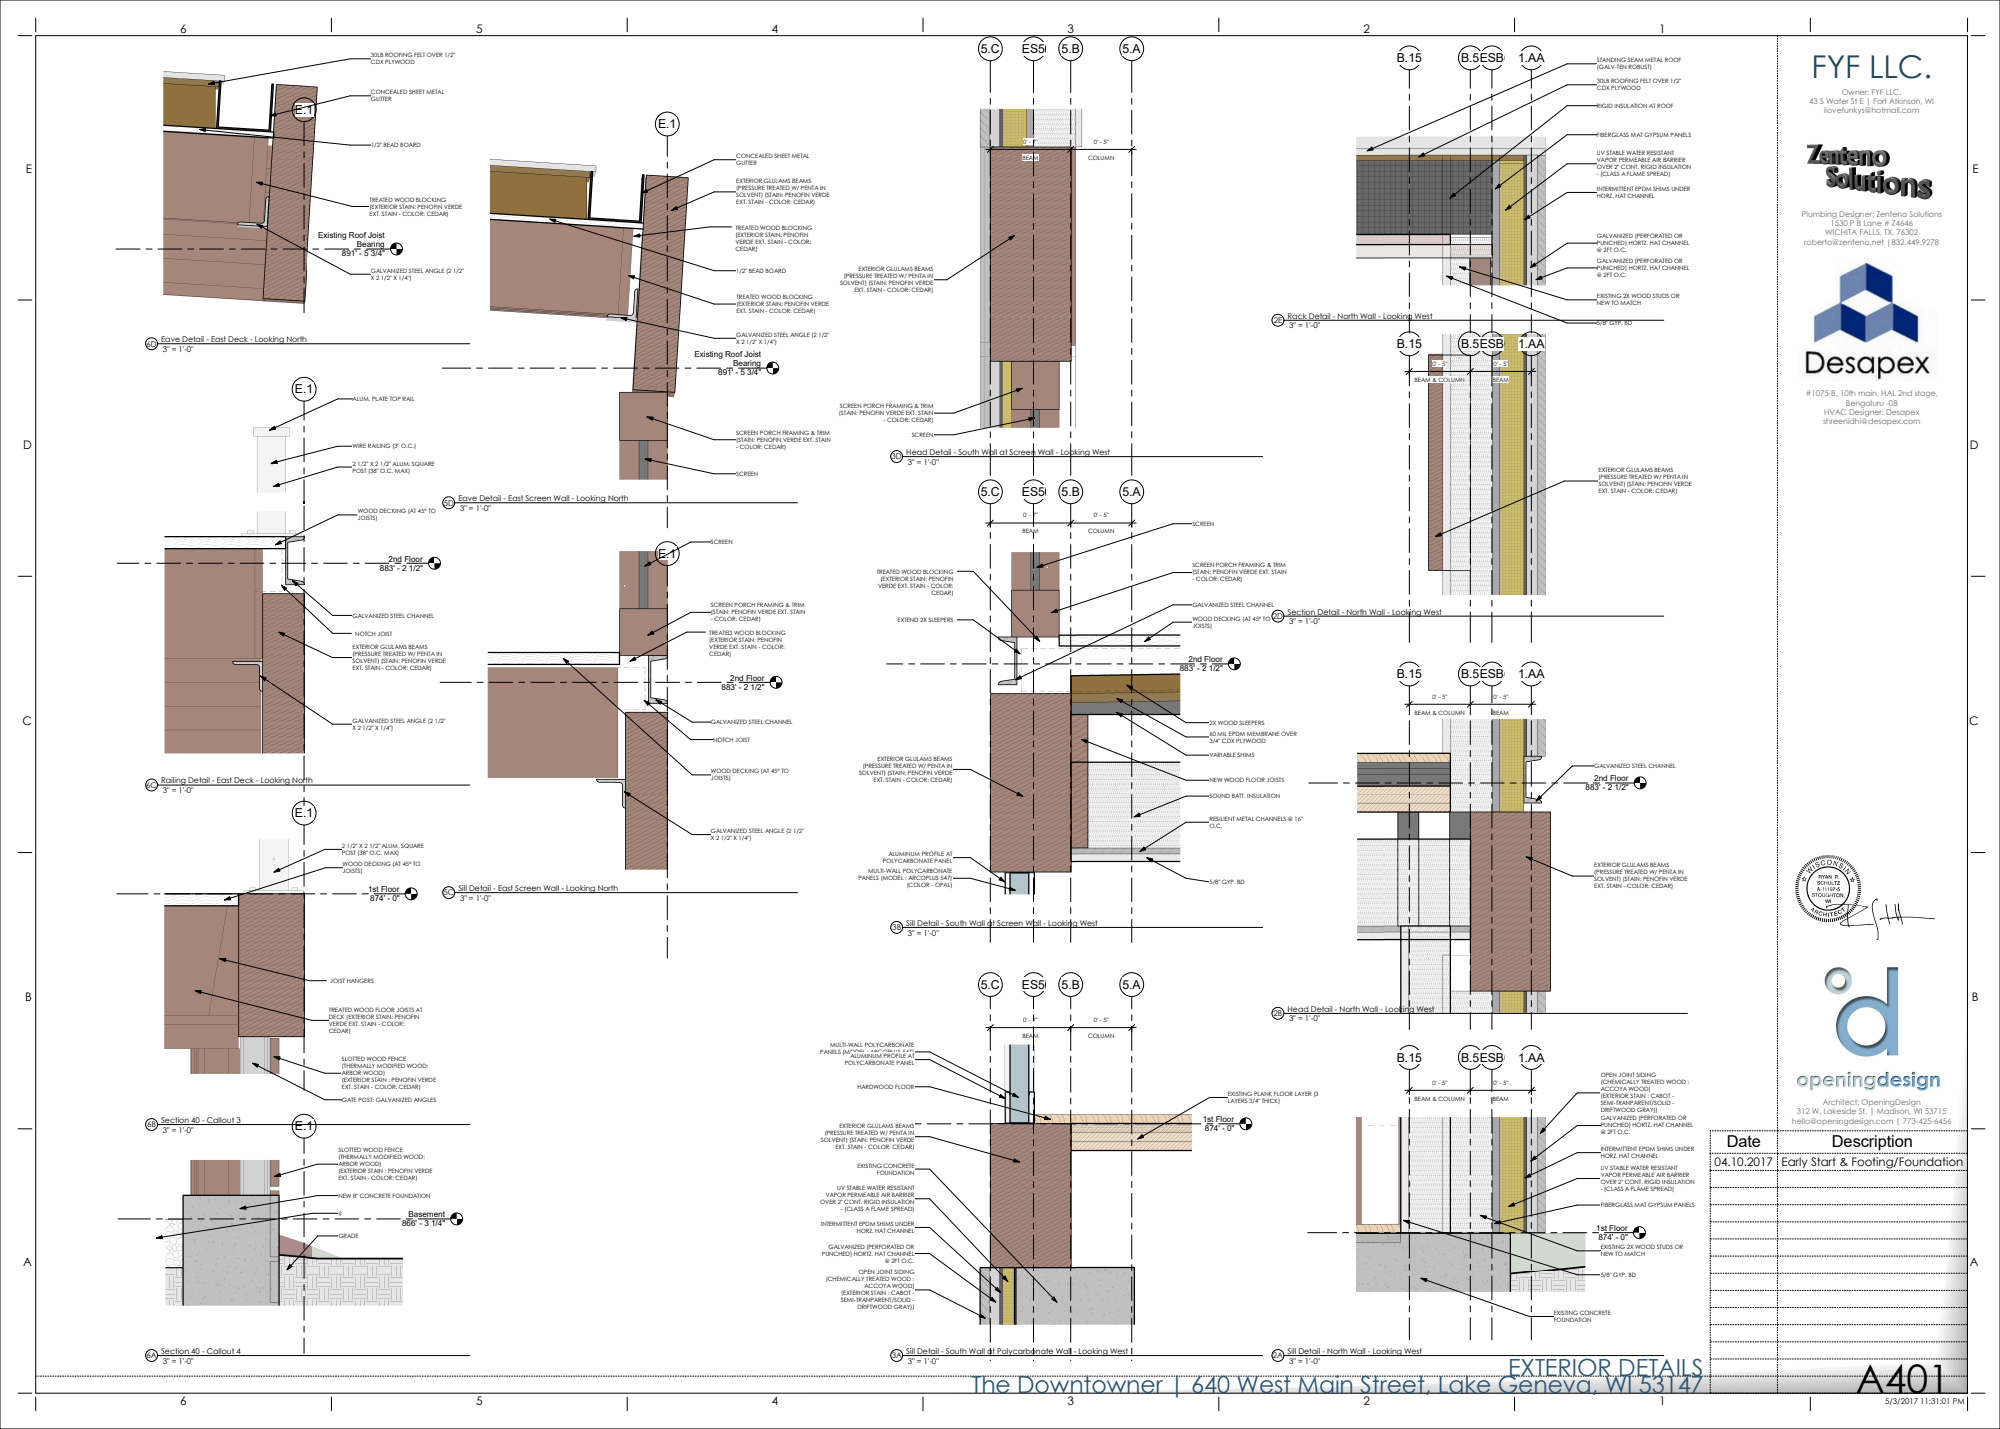
[picture p247: page 1]
1/2" BEAD BOARD; 2nd Floor 883' - 2 1/2"; 2 1/2" X 2 1/2" ALUM. SQUARE POST (38" O.C. MAX); WIRE RAILING (3" O.C.); NOTCH JOIST; 1st Floor 874' - 0"; JOIST HANGERS; Basement 866' - 3 1/4"; GRADE; BEAM; COLUMN; - COLOR: CEDAR); SCREEN; 2X WOOD SLEEPERS; VARIABLE SHIMS; (COLOR - OPAL); EXTEND 2X SLEEPERS; CEDAR); 5/8" GYP. BD; EXISTING CONCRETE FOUNDATION; ACCOYA WOOD); HARDWOOD FLOOR; Bearing 891' - 5 3/4"; BEAM & COLUMN; ESB; GALVANIZED STEEL CHANNEL; Architect: OpeningDesign; FYF LLC.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

30LB ROOFING FELT OVER 1/2"
CDX PLYWOOD

STANDING SEAM METAL ROOF
(GALV-TEN ROBUST)

CONCEALED SHEET METAL
GUTTER

Owner: FYF LLC.

43 S Water St E | Fort Atkinson, WI
ilovefunkys@hotmail.com

RIGID INSULATION AT ROOF

FIBERGLASS MAT GYPSUM PANELS

UV STABLE WATER RESISTANT
VAPOR PERMEABLE AIR BARRIER
OVER 2" CONT. RIGID INSULATION
- (CLASS A FLAME SPREAD)

EXTERIOR GLULAMS BEAMS
(PRESSURE TREATED W/ PENTA IN
SOLVENT) (STAIN: PENOFIN VERDE
EXT. STAIN - COLOR: CEDAR)

INTERMITTENT EPDM SHIMS UNDER
HORZ. HAT CHANNEL

TREATED WOOD BLOCKING
(EXTERIOR STAIN: PENOFIN VERDE

Plumbing Designer: Zenteno Solutions

1530 P B Lane # Z4646
WICHITA FALLS, TX, 76302
roberto@zenteno.net |832.449.9278

(EXTERIOR STAIN: PENOFIN
VERDE EXT. STAIN - COLOR:
CEDAR)

GALVANIZED (PERFORATED OR
PUNCHED) HORTZ. HAT CHANNEL

GALVANIZED STEEL ANGLE (2 1/2"

EXISTING 2X WOOD STUDS OR
NEW TO MATCH

3" = 1'-0" 2E Rack Detail - North Wall - Looking West

3" = 1'-0" 6D Eave Detail - East Deck - Looking North

Existing Roof Joist

#1075-B, 10th main, HAL 2nd stage,

ALUM. PLATE TOP RAIL

SCREEN PORCH FRAMING & TRIM
(STAIN: PENOFIN VERDE EXT. STAIN

Bengaluru -08
HVAC Designer: Desapex
shreenidhi@desapex.com

- COLOR: CEDAR)

3" = 1'-0" 3D Head Detail - South Wall at Screen Wall - Looking West

3" = 1'-0" 5D Eave Detail - East Screen Wall - Looking North

WOOD DECKING (AT 45° TO
JOISTS)

GALVANIZED STEEL CHANNEL

3" = 1'-0" 2D Section Detail - North Wall - Looking West

60 MIL EPDM MEMBRANE OVER
3/4" CDX PLYWOOD

3" = 1'-0" 6C Railing Detail - East Deck - Looking North

NEW WOOD FLOOR JOISTS

SOUND BATT. INSULATION

RESILIENT METAL CHANNELS @ 16"

ALUMINUM PROFILE AT
POLYCARBONATE PANEL
MULTI-WALL POLYCARBONATE
PANELS (MODEL : ARCOPLUS 547)

3" = 1'-0" 5C Sill Detail - East Screen Wall - Looking North

3" = 1'-0" 3B Sill Detail - South Wall at Screen Wall - Looking West

TREATED WOOD FLOOR JOISTS AT
DECK (EXTERIOR STAIN: PENOFIN

3" = 1'-0" 2B Head Detail - North Wall - Looking West

(COLOR - OPAL) ALUMINUM PROFILE AT POLYCARBONATE PANEL

SLOTTED WOOD FENCE
(THERMALLY MODIFIED WOOD:
ARBOR WOOD)
(EXTERIOR STAIN : PENOFIN VERDE

OPEN JOINT SIDING
(CHEMICALLY TREATED WOOD :
ACCOYA WOOD)
(EXTERIOR STAIN : CABOT -
SEMI-TRANPARENT/SOLID -
DRIFTWOOD GRAY))

EXISTING PLANK FLOOR LAYER (3
LAYERS 3/4" THICK)

GATE POST: GALVANIZED ANGLES

312 W. Lakeside St. | Madison, WI 53715
hello@openingdesign.com | 773-425-6456

04.10.2017 Early Start & Footing/Foundation

NEW 8" CONCRETE FOUNDATION

3" = 1'-0" 3A Sill Detail - South Wall at Polycarbonate Wall - Looking West

3" = 1'-0" 2A Sill Detail - North Wall - Looking West

EXTERIOR DETAILS The Downtowner | 640 West Main Street, Lake Geneva, WI 53147
