OpeningDesign/Vacation_Rental/Transfer/20170519 ----- ISSUE FOR BID & PERMIT -------/The Downtowner_ARCH - Sheet - A501 - SCHEDULES.pdf

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
6 | 5 | 4 | 3 | 2 | 1

Owner: FYF LLC.

### 43 S Water St E | Fort Atkinson, WI

ilovefunkys@hotmail.com

FYF LLC.

Plumbing Designer: Zenteno Solutions 1530 P B Lane # Z4646
WICHITA FALLS, TX, 76302
roberto@zenteno.net |832.449.9278

#1075-B, 10th main, HAL 2nd stage, Bengaluru -08

HVAC Designer: Desapex
shreenidhi@desapex.com

This project, like most OpeningDesign's projects, is open source (Attribution-ShareAlike 4.0 International--CC BY-SA 4.0)--freely available to any party for future use, assuming the terms such as Attribution and ShareAlike are honored.

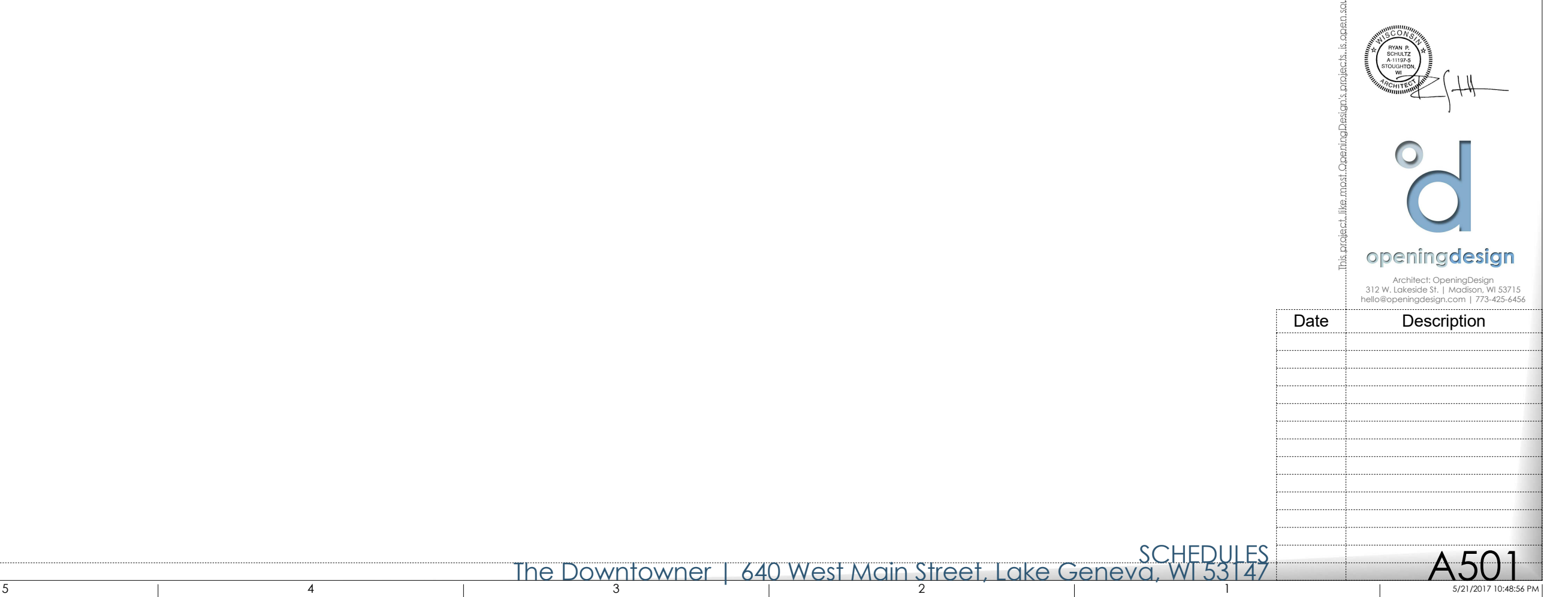
[picture p251: figure]
Architect: OpeningDesign 312 W. Lakeside St. | Madison, WI 53715 hello@openingdesign.com | 773-425-6456; Date; Description

# SCHEDULES The Downtowner | 640 West Main Street, Lake Geneva, WI 53147

Wall Schedule

Type | Area | Phase Created
(P4) INTERIOR 2X4 WALL | 482 SF | New Construction
(P4) INTERIOR 2X4 WALL | 121 SF | New Construction
(P4) INTERIOR 2X4 WALL | 122 SF | New Construction
(P4) INTERIOR 2X4 WALL | 161 SF | New Construction
(P4) INTERIOR 2X4 WALL | 69 SF | New Construction
(P4) INTERIOR 2X4 WALL | 108 SF | New Construction
(P4) INTERIOR 2X4 WALL | 119 SF | New Construction
(P4) INTERIOR 2X4 WALL | 106 SF | New Construction
(P4) INTERIOR 2X4 WALL | 202 SF | New Construction
(P4) INTERIOR 2X4 WALL | 32 SF | New Construction
(P4) INTERIOR 2X4 WALL | 21 SF | New Construction
(P4) INTERIOR 2X4 WALL | 22 SF | New Construction
(P4) INTERIOR 2X4 WALL | 29 SF | New Construction
(P4) INTERIOR 2X4 WALL | 34 SF | New Construction | MULTI-WALL POLYCARBONATE PANELS (MODEL- ARCOPLUS 547) (COLOR - OPAL): 6 435 SF
(P4) INTERIOR 2X4 WALL | 21 SF | New Construction
(P4) INTERIOR 2X4 WALL | 22 SF | New Construction
(P4) INTERIOR 2X4 WALL | 29 SF | New Construction
(P4) INTERIOR 2X4 WALL | 33 SF | New Construction
(P4) INTERIOR 2X4 WALL | 18 SF | New Construction
(P4) INTERIOR 2X4 WALL | 24 SF | New Construction
(P4) INTERIOR 2X4 WALL | 30 SF | New Construction
(P4) INTERIOR 2X4 WALL | 30 SF | New Construction
(P4) INTERIOR 2X4 WALL | 18 SF | New Construction
(P4) INTERIOR 2X4 WALL | 24 SF | New Construction
(P4) INTERIOR 2X4 WALL | 24 SF | New Construction
(P4) INTERIOR 2X4 WALL | 23 SF | New Construction
(P4) INTERIOR 2X4 WALL | 69 SF | New Construction
(P4) INTERIOR 2X4 WALL | 36 SF | New Construction
(P4) INTERIOR 2X4 WALL | 25 SF | New Construction
(P4) INTERIOR 2X4 WALL | 23 SF | New Construction
(P4) INTERIOR 2X4 WALL | 26 SF | New Construction
(P4) INTERIOR 2X4 WALL | 93 SF | New Construction
(P4) INTERIOR 2X4 WALL | 26 SF | New Construction
(P4) INTERIOR 2X4 WALL | 26 SF | New Construction
(P4) INTERIOR 2X4 WALL | 97 SF | New Construction
(P4) INTERIOR 2X4 WALL | 87 SF | New Construction
(P4) INTERIOR 2X4 WALL | 114 SF | New Construction
(P4) INTERIOR 2X4 WALL | 18 SF | New Construction
(P4) INTERIOR 2X4 WALL | 49 SF | New Construction
(P4) INTERIOR 2X4 WALL | 20 SF | New Construction
(P4) INTERIOR 2X4 WALL | 26 SF | New Construction
(P4) INTERIOR 2X4 WALL | 97 SF | New Construction
(P4) INTERIOR 2X4 WALL | 11 SF | New Construction
(P4) INTERIOR 2X4 WALL | 9 SF | New Construction
(P4) INTERIOR 2X4 WALL | 15 SF | New Construction
(P4) INTERIOR 2X4 WALL | 16 SF | New Construction
(P4) INTERIOR 2X4 WALL | 109 SF | New Construction
(P4) INTERIOR 2X4 WALL | 69 SF | New Construction
(P4) INTERIOR 2X4 WALL | 37 SF | New Construction
(P4) INTERIOR 2X4 WALL | 44 SF | New Construction
(P4) INTERIOR 2X4 WALL | 78 SF | New Construction
(P4) INTERIOR 2X4 WALL | 28 SF | New Construction
(P4) INTERIOR 2X4 WALL | 53 SF | New Construction
(P4) INTERIOR 2X4 WALL: 53 | 3224 SF
(P6) INTERIOR 2X6 WALL | 72 SF | New Construction
(P6) INTERIOR 2X6 WALL | 69 SF | New Construction
(P6) INTERIOR 2X6 WALL | 114 SF | New Construction
(P6) INTERIOR 2X6 WALL: 3 | 254 SF
2x4 ALUM. STOREFRONT SYSTEM | 94 SF | New Construction
2x4 ALUM. STOREFRONT SYSTEM | 137 SF | New Construction
2x4 ALUM. STOREFRONT SYSTEM | 106 SF | New Construction
2x4 ALUM. STOREFRONT SYSTEM | 304 SF | New Construction
2x4 ALUM. STOREFRONT SYSTEM | 169 SF | New Construction
2x4 ALUM. STOREFRONT SYSTEM | 62 SF | New Construction
2x4 ALUM. STOREFRONT SYSTEM: 6 | 871 SF
8" CONCRETE FOUNDATION WALL | 122 SF | New Construction
8" CONCRETE FOUNDATION WALL: 1 | 122 SF
ABOVE STOREFRONT | 55 SF | New Construction
ABOVE STOREFRONT: 1 | 55 SF
FURRING | 41 SF | New Construction
FURRING: 1 | 41 SF
OPEN JOINT SIDING | 312 SF | New Construction
OPEN JOINT SIDING | 35 SF | New Construction
OPEN JOINT SIDING | 307 SF | New Construction
OPEN JOINT SIDING | 7 SF | New Construction
OPEN JOINT SIDING | 182 SF | New Construction
OPEN JOINT SIDING: 5 | 843 SF
OPEN JOINT SIDING (1HR) | 821 SF | New Construction
OPEN JOINT SIDING (1HR): 1 | 821 SF
OPEN JOINT SIDING OVER FOUNDATION WALL | 215 SF | New Construction
OPEN JOINT SIDING OVER FOUNDATION WALL | 109 SF | New Construction

OPEN JOINT SIDING OVER FOUNDATION
WALL: 2 | 324 SF
POLYCARBONATE PANEL - ARCOPLUS 547 - OPAL - W/O IR TREATMENT | 100 SF | New Construction
POLYCARBONATE PANEL - ARCOPLUS 547 - OPAL - W/O IR TREATMENT | 110 SF | New Construction
POLYCARBONATE PANEL - ARCOPLUS 547 - OPAL - W/O IR TREATMENT | 388 SF | New Construction

POLYCARBONATE PANEL - ARCOPLUS 547
- OPAL - W/O IR TREATMENT: 3 | 598 SF
Retaining - 10" Concrete | New Construction
Retaining - 10" Concrete | New Construction
Retaining - 10" Concrete: 2 | 0 SF
SLOTTED WOOD FENCE | 269 SF | New Construction
SLOTTED WOOD FENCE | 269 SF | New Construction
SLOTTED WOOD FENCE | 41 SF | New Construction
SLOTTED WOOD FENCE | 139 SF | New Construction
SLOTTED WOOD FENCE | 411 SF | New Construction
SLOTTED WOOD FENCE | 31 SF | New Construction
SLOTTED WOOD FENCE: 6 | 1159 SF
SOFFIT WALL | 17 SF | New Construction
SOFFIT WALL: 1 | 17 SF
Grand total: 85 | 8330 SF

Glazing Schedule

Type Mark | Type | Width | Height | Area
MULTI-WALL POLYCARBONATE PANELS (MODEL- ARCOPLUS 547) (COLOR - OPAL) | 5' - 0 7/8" | 7' - 8 7/8" | 39 SF
MULTI-WALL POLYCARBONATE PANELS (MODEL- ARCOPLUS 547) (COLOR - OPAL) | 7' - 11 9/32" | 7' - 8 7/8" | 61 SF
MULTI-WALL POLYCARBONATE PANELS (MODEL- ARCOPLUS 547) (COLOR - OPAL) | 8' - 8" | 7' - 8 7/8" | 67 SF
MULTI-WALL POLYCARBONATE PANELS (MODEL- ARCOPLUS 547) (COLOR - OPAL) | 10' - 8 7/8" | 7' - 8 7/8" | 83 SF
MULTI-WALL POLYCARBONATE PANELS (MODEL- ARCOPLUS 547) (COLOR - OPAL) | 10' - 9 3/8" | 7' - 8 7/8" | 83 SF

MULTI-WALL POLYCARBONATE PANELS (MODEL- ARCOPLUS
547) (COLOR - OPAL)

12' - 11
9/32"
7' - 8 7/8" | 100 SF
TEMPERED INSULATED GLAZING (CARDINAL GLASS LoĒ²-240 | 29 SF
TEMPERED INSULATED GLAZING (CARDINAL GLASS LoĒ²-240 | 18 SF
TEMPERED INSULATED GLAZING (CARDINAL GLASS LoĒ²-240 | | | 27 SF
TEMPERED INSULATED GLAZING (CARDINAL GLASS LoĒ²-240 | | | 19 SF
TEMPERED INSULATED GLAZING (CARDINAL GLASS LoĒ²-240 | | | 21 SF
TEMPERED INSULATED GLAZING (CARDINAL GLASS LoĒ²-240 | | | 21 SF
TEMPERED INSULATED GLAZING (CARDINAL GLASS LoĒ²-240 | | | 25 SF
TEMPERED INSULATED GLAZING (CARDINAL GLASS LoĒ²-240 | | | 21 SF
TEMPERED INSULATED GLAZING (CARDINAL GLASS LoĒ²-240 | | | 21 SF
TEMPERED INSULATED GLAZING (CARDINAL GLASS LoĒ²-240 | | | 5 SF
TEMPERED INSULATED GLAZING (CARDINAL GLASS LoĒ²-240 | | | 4 SF
TEMPERED INSULATED GLAZING (CARDINAL GLASS LoĒ²-240 | 2' - 9 15/32" | 6' - 10 1/2" | 19 SF
TEMPERED INSULATED GLAZING (CARDINAL GLASS LoĒ²-240 | 2' - 11 31/32" | 6' - 10 1/2" | 21 SF
TEMPERED INSULATED GLAZING (CARDINAL GLASS LoĒ²-240 | 3' - 0 31/32" | 6' - 10 1/2" | 21 SF
TEMPERED INSULATED GLAZING (CARDINAL GLASS LoĒ²-240 | 3' - 0 31/32" | 6' - 10 1/2" | 21 SF
TEMPERED INSULATED GLAZING (CARDINAL GLASS LoĒ²-240 | 3' - 2 1/32" | 6' - 10 1/2" | 22 SF
TEMPERED INSULATED GLAZING (CARDINAL GLASS LoĒ²-240 | 3' - 4 15/32" | 7' - 9" | 26 SF
TEMPERED INSULATED GLAZING (CARDINAL GLASS LoĒ²-240 | 3' - 4 15/32" | 7' - 9" | 26 SF
TEMPERED INSULATED GLAZING (CARDINAL GLASS LoĒ²-240 | 3' - 5 15/32" | 7' - 9" | 27 SF
TEMPERED INSULATED GLAZING (CARDINAL GLASS LoĒ²-240 | 3' - 5 15/32" | 7' - 9" | 27 SF
TEMPERED INSULATED GLAZING (CARDINAL GLASS LoĒ²-240 | 3' - 5 21/32" | 7' - 9" | 27 SF
TEMPERED INSULATED GLAZING (CARDINAL GLASS LoĒ²-240 | 3' - 5 15/16" | 7' - 9" | 27 SF
TEMPERED INSULATED GLAZING (CARDINAL GLASS LoĒ²-240 | 3' - 6 15/16" | 7' - 9" | 28 SF
TEMPERED INSULATED GLAZING (CARDINAL GLASS LoĒ²-240 | 3' - 6 15/16" | 7' - 9" | 28 SF
TEMPERED INSULATED GLAZING (CARDINAL GLASS LoĒ²-240 | 3' - 7 11/16" | 7' - 9" | 28 SF
TEMPERED INSULATED GLAZING (CARDINAL GLASS LoĒ²-240 | 4' - 1 9/32" | 6' - 10 1/2" | 28 SF
TEMPERED INSULATED GLAZING (CARDINAL GLASS LoĒ²-240: 26 | 584 SF
