OpeningDesign/Vacation_Rental/Transfer/20170519 ----- ISSUE FOR BID & PERMIT -------/The Downtowner_ARCH_2D and Schedules - Sheet - A500 - ADA RESTROOM & SCHEDULES.pdf

10 28 00
SURFACE
MOUNTED
PAPER TOWEL
DISPENSER

OPERATIN

G POINT

4' - 0" MAX

10 28 00
SOAP
DISPENSER

OPERATING POINT

2' - 2"

10 28 00
SEAT COVER
DISPENSER AT
SIDE WALL

OPERATING POINT

4' - 0" MAX

10 28 00
SEAT COVER
DISPENSER AT
BACK WALL

OPERATING POINT

2' - 2"

10 28 00
SANITARY
NAPKIN
DISPOSAL

10 28 00
WASTE
RECEPTACLE

42" MAX

27" MAX

IF PROTRUDES

> 4" FROM WALL

10 28 00 RECESSED
PAPER TOWEL /

WASTE RECEPTACLE OPERATING POINT

4' - 0" MAX

OPERATING POINT

4' - 0" MAX

PTD

PTD/WR

SD

SC

SC SN

WR

REFLECTIVE SURFACE
40" MAX BOTTOM OF
EQ | EQ

29" MIN CLR
34" MAX

30" MIN CLR

DIV 22 SINK

10 28 00
MIRROR

34" MAX

APRON CLR

T.O. RIM OR
29" MIN

COUNTER WHICH
EVER IS HIGHER

INSULATE EXPOSED
HOT WATER AND
DRAIN PIPES, TYP

MIN

8"

MIN

### 9" KNEE CLR

27" MIN

17" MIN

DIV 22 SINK

WALL FACE

25" MAX TO FAUCET / SOAP
AT FORWARD APPROACH - 11"
MAX TO ELECTRONIC
FAUCET / SOAP ACTIVATION

33" - 36"

1' - 6"

33" - 36"

1' - 6"
MIN. 39" - 41"

BACK WALL

OF SHOWER

4" MAX.

3" MIN

6" MAX

CONTROLS 48" MAX.
CONTROLS: 38" MIN.

15" MAX FROM C.L.

CONTROLS:

EQ | EQ

MAX

6"

36" MIN

1' - 6"

24" MIN 12" MIN WALL FACE

33" - 36"

10 28 00 GRAB BARS W/
REINFORCEMENT, TYP

15"-19" STANDARD

17"-19" ACCESSIBLE
T.O. SEAT

33" - 36"

12" MAX

42" MIN

2' - 2"

7" - 9"

1 1/2" MIN CLR OBJECTS

12" CLR TO

PROTRUDING

1' - 6" 39" - 41"

39" - 41"

10 28 00 GRAB BARS W/

WALL FACE

REINFORCEMENT, TYP

54" MIN

B

B.5

1.AA

B.15

B-S

4B | A500
| 3B
3C | A500 4C
A500 | 4D

3D

STANDARD ADA FLIP-DOWN BENCH
(PROVIDE BLOCKING
IN WALL)

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
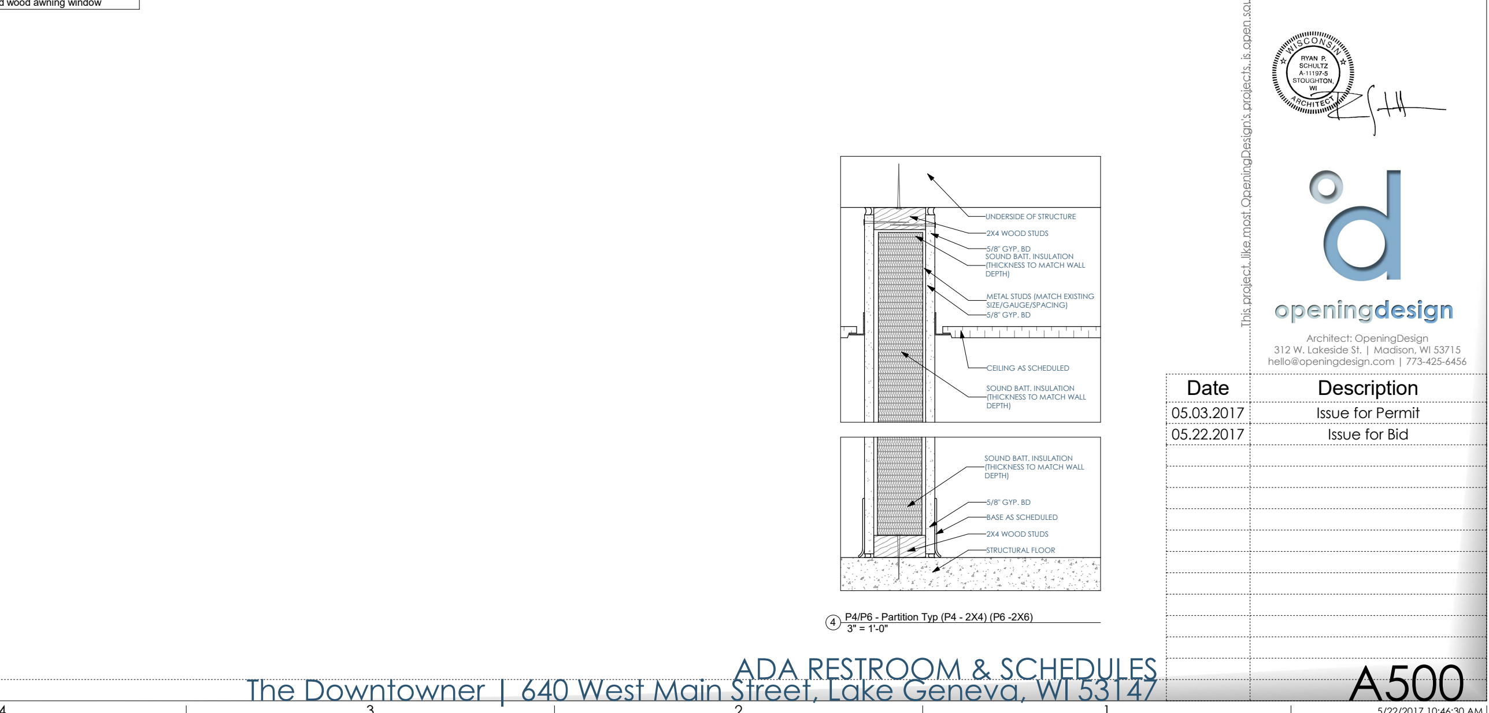
[picture p252: figure]
5/8" GYP. BD; METAL STUDS (MATCH EXISTING SIZE/GAUGE/SPACING); 2X4 WOOD STUDS; SOUND BATT. INSULATION (THICKNESS TO MATCH WALL DEPTH); BASE AS SCHEDULED; STRUCTURAL FLOOR; CEILING AS SCHEDULED; UNDERSIDE OF STRUCTURE; Architect: OpeningDesign 312 W. Lakeside St. | Madison, WI 53715 hello@openingdesign.com | 773-425-6456; ADA RESTROOM & SCHEDULES; Date; Description; 05.03.2017 Issue for Permit; 05.22.2017 Issue for Bid

5 | 4 | 3 | 2 | 1
6 | 5 | 4 | 3 | 2 | 1

Owner: FYF LLC.

## 43 S Water St E | Fort Atkinson, WI ilovefunkys@hotmail.com

FYF LLC.

## Plumbing Designer: Zenteno Solutions 1530 P B Lane # Z4646 WICHITA FALLS, TX, 76302 roberto@zenteno.net |832.449.9278

#1075-B, 10th main, HAL 2nd stage,

## Bengaluru -08 HVAC Designer: Desapex shreenidhi@desapex.com

This project, like most OpeningDesign's projects, is open source (Attribution-ShareAlike 4.0 International--CC BY-SA 4.0)--freely available to any party for future use, assuming the terms such as Attribution and ShareAlike are honored.

5/22/2017 10:46:30 AM

# The Downtowner | 640 West Main Street, Lake Geneva, WI 53147

1/2" = 1'-0" 3

## ADA COMPLIENT HEIGHTS

## 1/2" = 1'-0" 4C Lavatory - Front Elevation 1/2" = 1'-0" 3C Lavatory - Side Elevation

## 1/2" = 1'-0" 4B Shower - Back Elevation

## 1/2" = 1'-0" 3B Shower - Side Elevation

## 1/2" = 1'-0" 3D Toilet - Front Elevation

## 1/2" = 1'-0" 4D Toilet - Side Elevation

## P4/P6 - Partition Typ (P4 - 2X4) (P6 -2X6)

1/2" = 1'-0"

1

## ADA (TYPE A) RESTROOM PLAN

DOOR SCHEDULE

OD_DS_Door_Type

OD_DS_Door_M
aterial

DOOR SCHEDULE

Door

Number | Room Name | Room
| | Number

Door
Width | Height | Notes
B000 | BASEMENT | B000 | 3' - 0" | 6' - 8" | SWING | T.B.D.
203.A | BATH | 203.A | 2' - 8" | 6' - 4" | SLIDER | T.B.D.
204.A | BATH | 204.A | 2' - 8" | 6' - 4" | SLIDER | T.B.D.
203.B | BATH | 203.A | 5' - 6" | 6' - 5 3/8" SLIDER
204.B | BATH | 204.A | 5' - 6" | 6' - 5 3/8" SLIDER
206 | BATH | 206 | 2' - 10" | 6' - 8" | SWING | T.B.D.
100.A | BATH | 100.A | 2' - 8" | 6' - 4" | SLIDER | T.B.D.
101.A | BATH | 101.A | 2' - 8" | 6' - 4" | SLIDER | T.B.D.
104.A | BATH | 104.A | 2' - 8" | 6' - 4" | SLIDER | T.B.D.
105.A | BATH | 105.A | 2' - 8" | 6' - 4" | SLIDER | T.B.D.
103.A | BATH (ADA) | 103.A | 3' - 0" | 6' - 8" | SWING | T.B.D.
104.B | BEDROOM | 104 | 3' - 0" | 6' - 8" | SWING | T.B.D.
101 | BEDROOM | 101 | 3' - 0" | 6' - 8" | SWING | T.B.D.
102 | BEDROOM | 102 | 3' - 0" | 6' - 8" | SWING | T.B.D.
105.A | BEDROOM | 105 | 3' - 0" | 6' - 8" | SWING | T.B.D.
203 | BEDROOM | 203 | 3' - 0" | 6' - 8" | SWING | T.B.D.
204 | BEDROOM | 204 | 3' - 0" | 6' - 8" | SWING | T.B.D.
104.C | BEDROOM | 104 | 3' - 4" | 7' - 9" | STOREFRONT - SINGLE HUNG WINDOW | ALUM./GLAZIN
| | | | | | G
105.C | BEDROOM | 105 | 3' - 4" | 7' - 9" | STOREFRONT (NARROW STILE) | ALUM./GLAZIN
| | | | | | G
105.E | BEDROOM | 105 | 3' - 4" | 7' - 9" | STOREFRONT - SINGLE HUNG WINDOW | ALUM./GLAZIN
| | | | | | G
103.A | BEDROOM (ADA) | 103 | 3' - 0" | 6' - 8" | SWING | T.B.D.
103.B | BEDROOM (ADA) | 103 | 3' - 0" | 6' - 8" | SWING | T.B.D.
103.C | BEDROOM (ADA) | 103 | 3' - 4" | 7' - 9" | STOREFRONT (NARROW STILE) | ALUM./GLAZIN
| | | | | | G
101.B | CLOS. | 101.B | 2' - 2
| | | 9/16" | 6' - 4" | SLIDER | T.B.D.
100.B | CLOS. | 100.B | 2' - 2
| | | 9/16" | 6' - 4" | SLIDER | T.B.D.
104.B | CLOS. | 104.B | 2' - 2
| | | 9/16" | 6' - 4" | SLIDER | T.B.D.
105.B | CLOS. | 105.B | 2' - 2
| | | 9/16" | 6' - 4" | SLIDER | T.B.D.
102.A | CLOS. | 102.A | 2' - 2
| | | 9/16" | 6' - 4" | SLIDER | T.B.D.
205.A | CLOS. | 205.A | 2' - 2
| | | 9/16" | 6' - 4" | SLIDER | T.B.D.
102.B | CLOS. | 102.B | 2' - 2
| | | 9/16" | 6' - 4" | SLIDER | T.B.D.
100 | CORRIDOR | 106 | 3' - 0" | 6' - 8" | SWING | T.B.D.
106.B | CORRIDOR | 106 | 7' - 6" | 6' - 5 3/8" SLIDER
106 | CORRIDOR | 106 | 3' - 4" | 7' - 9" | STOREFRONT (NARROW STILE) | ALUM./GLAZIN
| | | | | | G
201 | DINING/KITCHEN | 201 | 3' - 0" | 7' - 11" | STOREFRONT (NARROW STILE) | ALUM./GLAZIN
| | | | | | G

180 DEGREE OPEN

109 | OUTDOOR DECK | 109 | 3' - 0 1/2" | 1' - 11
| | | | 1/2" | GATE DOOR | WOOD
208.J | OUTDOOR DECK | 109 | 3' - 4" | 7' - 9" | STOREFRONT - SINGLE HUNG WINDOW | ALUM./GLAZIN
| | | | | | G
B001 | OUTDOOR STORAGE
| UNDER DECK | B001 | 2' - 9 5/8" | 1' - 11
| | | | 1/2" | GATE DOOR | WOOD
208.B | SCREENED PATIO | 208 | 3' - 2
| | | 1/32" | 6' - 10
| | | | 1/2" | STOREFRONT (NARROW STILE) | ALUM./GLAZIN
| | | | | | G

180 DEGREE OPEN

208.A | SCREENED PATIO | 208 | 3' - 2
| | | 1/32" | 6' - 10
| | | | 1/2" | STOREFRONT (NARROW STILE) | ALUM./GLAZIN
| | | | | | G

180 DEGREE OPEN

208.C | SCREENED PATIO | 208 | 2' - 9 7/8" | 7' - 10
| | | | 15/32" | STOREFRONT (NARROW STILE) | ALUM./GLAZIN
| | | | | | G
208.E | SCREENED PATIO | 208 | 2' - 9
| | | 13/16" | 7' - 7
| | | | 1/16" | STOREFRONT (NARROW STILE) | ALUM./GLAZIN
| | | | | | G

180 DEGREE OPEN

208.D | SCREENED PATIO | 208 | 2' - 9
| | | 13/16" | 7' - 7
| | | | 1/16" | STOREFRONT (NARROW STILE) | ALUM./GLAZIN
| | | | | | G

180 DEGREE OPEN

208.G | SCREENED PATIO | 208 | 3' - 2
| | | 19/32"
7' - 0 3/4" STOREFRONT (NARROW STILE) | ALUM./GLAZIN
| | | | | | G

180 DEGREE OPEN

208.F | SCREENED PATIO | 208 | 3' - 2
| | | 19/32"
7' - 0 3/4" STOREFRONT (NARROW STILE) | ALUM./GLAZIN
| | | | | | G

180 DEGREE OPEN

108 | STAIR | 108 | 3' - 0" | 7' - 0" | STOREFRONT (NARROW STILE) | ALUM./GLAZIN
| | | | | | G
205 | STORAGE | 205 | 2' - 10" | 6' - 8" | SWING | T.B.D.

## Window Schedule

Type Mark | Width | Height | Type Comments
W1 | 3' - 1" | 3' - 1" | Fiberglass and Fibrex clad wood awning window
W1 | 3' - 1" | 3' - 1" | Fiberglass and Fibrex clad wood awning window
W1 | 3' - 1" | 3' - 1" | Fiberglass and Fibrex clad wood awning window
W1 | 3' - 1" | 3' - 1" | Fiberglass and Fibrex clad wood awning window
W1 | 3' - 1" | 3' - 1" | Fiberglass and Fibrex clad wood awning window
W1 | 3' - 1" | 3' - 1" | Fiberglass and Fibrex clad wood awning window
W1 | 3' - 1" | 3' - 1" | Fiberglass and Fibrex clad wood awning window
