OpeningDesign/Vacation_Rental/Transfer/20170519 ----- ISSUE FOR BID & PERMIT -------/The Downtowner_HVAC - Sheet - M-001 - HVAC Basement & Roof plan.pdf

### BCDE

### ABCDE

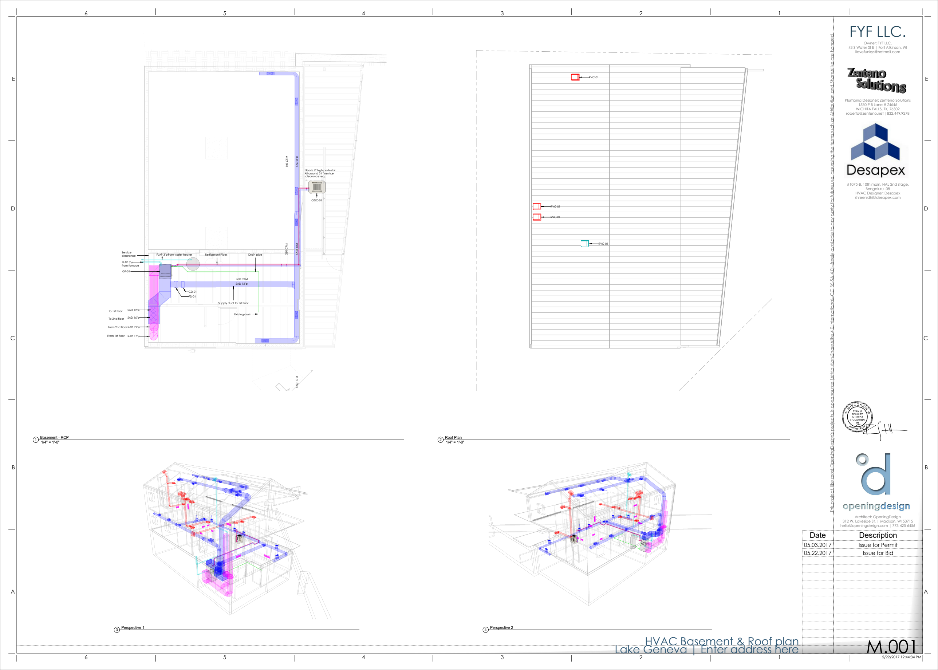
[picture p253: page 1]

RVC-01

RVC-01

RVC-01

RVC-01

500 CFM

SAD 12"ø

SAD 10"ø SAD 8"ø

280 CFM 140 CFM

Needs 6" high pedestal
All around 24 " service
clearance req

Supply duct to 1st floor

ODC-01

GF-01

RAD 17"ø

To 1st floor

To 2nd floor

From 2nd floor

From 1st floor

FLAP 3"ø

FLAP 3"ø

from water heater

from furnace

Service
clearance | Refrigerant Pipes | Drain pipe

Existing drain

RAD 19"ø

SAD 16"ø

FD-01

CD-01

SAD 12"ø

SAD 10"ø

Architect: OpeningDesign
312 W. Lakeside St. | Madison, WI 53715
hello@openingdesign.com | 773-425-6456

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
Owner: FYF LLC.

### 43 S Water St E | Fort Atkinson, WI

ilovefunkys@hotmail.com

FYF LLC.

Plumbing Designer: Zenteno Solutions 1530 P B Lane # Z4646
WICHITA FALLS, TX, 76302
roberto@zenteno.net |832.449.9278

#1075-B, 10th main, HAL 2nd stage, Bengaluru -08

HVAC Designer: Desapex
shreenidhi@desapex.com

This project, like most OpeningDesign's projects, is open source (Attribution-ShareAlike 4.0 International--CC BY-SA 4.0)--freely available to any party for future use, assuming the terms such as Attribution and ShareAlike are honored.

M.001

5/22/2017 12:44:34 PM

# HVAC Basement & Roof plan Lake Geneva | Enter address here

1/4" = 1'-0"

2

Roof Plan

Date | Description

## 05.03.2017 Issue for Permit 05.22.2017 Issue for Bid

1/4" = 1'-0"

1

Basement - RCP

3

Perspective 1
4

Perspective 2
