OpeningDesign/Vacation_Rental/Transfer/20170519 ----- ISSUE FOR BID & PERMIT -------/The Downtowner_ARCH - Sheet - A361 - STAIR SECTIONS.pdf

## Existing Roof Joist Bearing

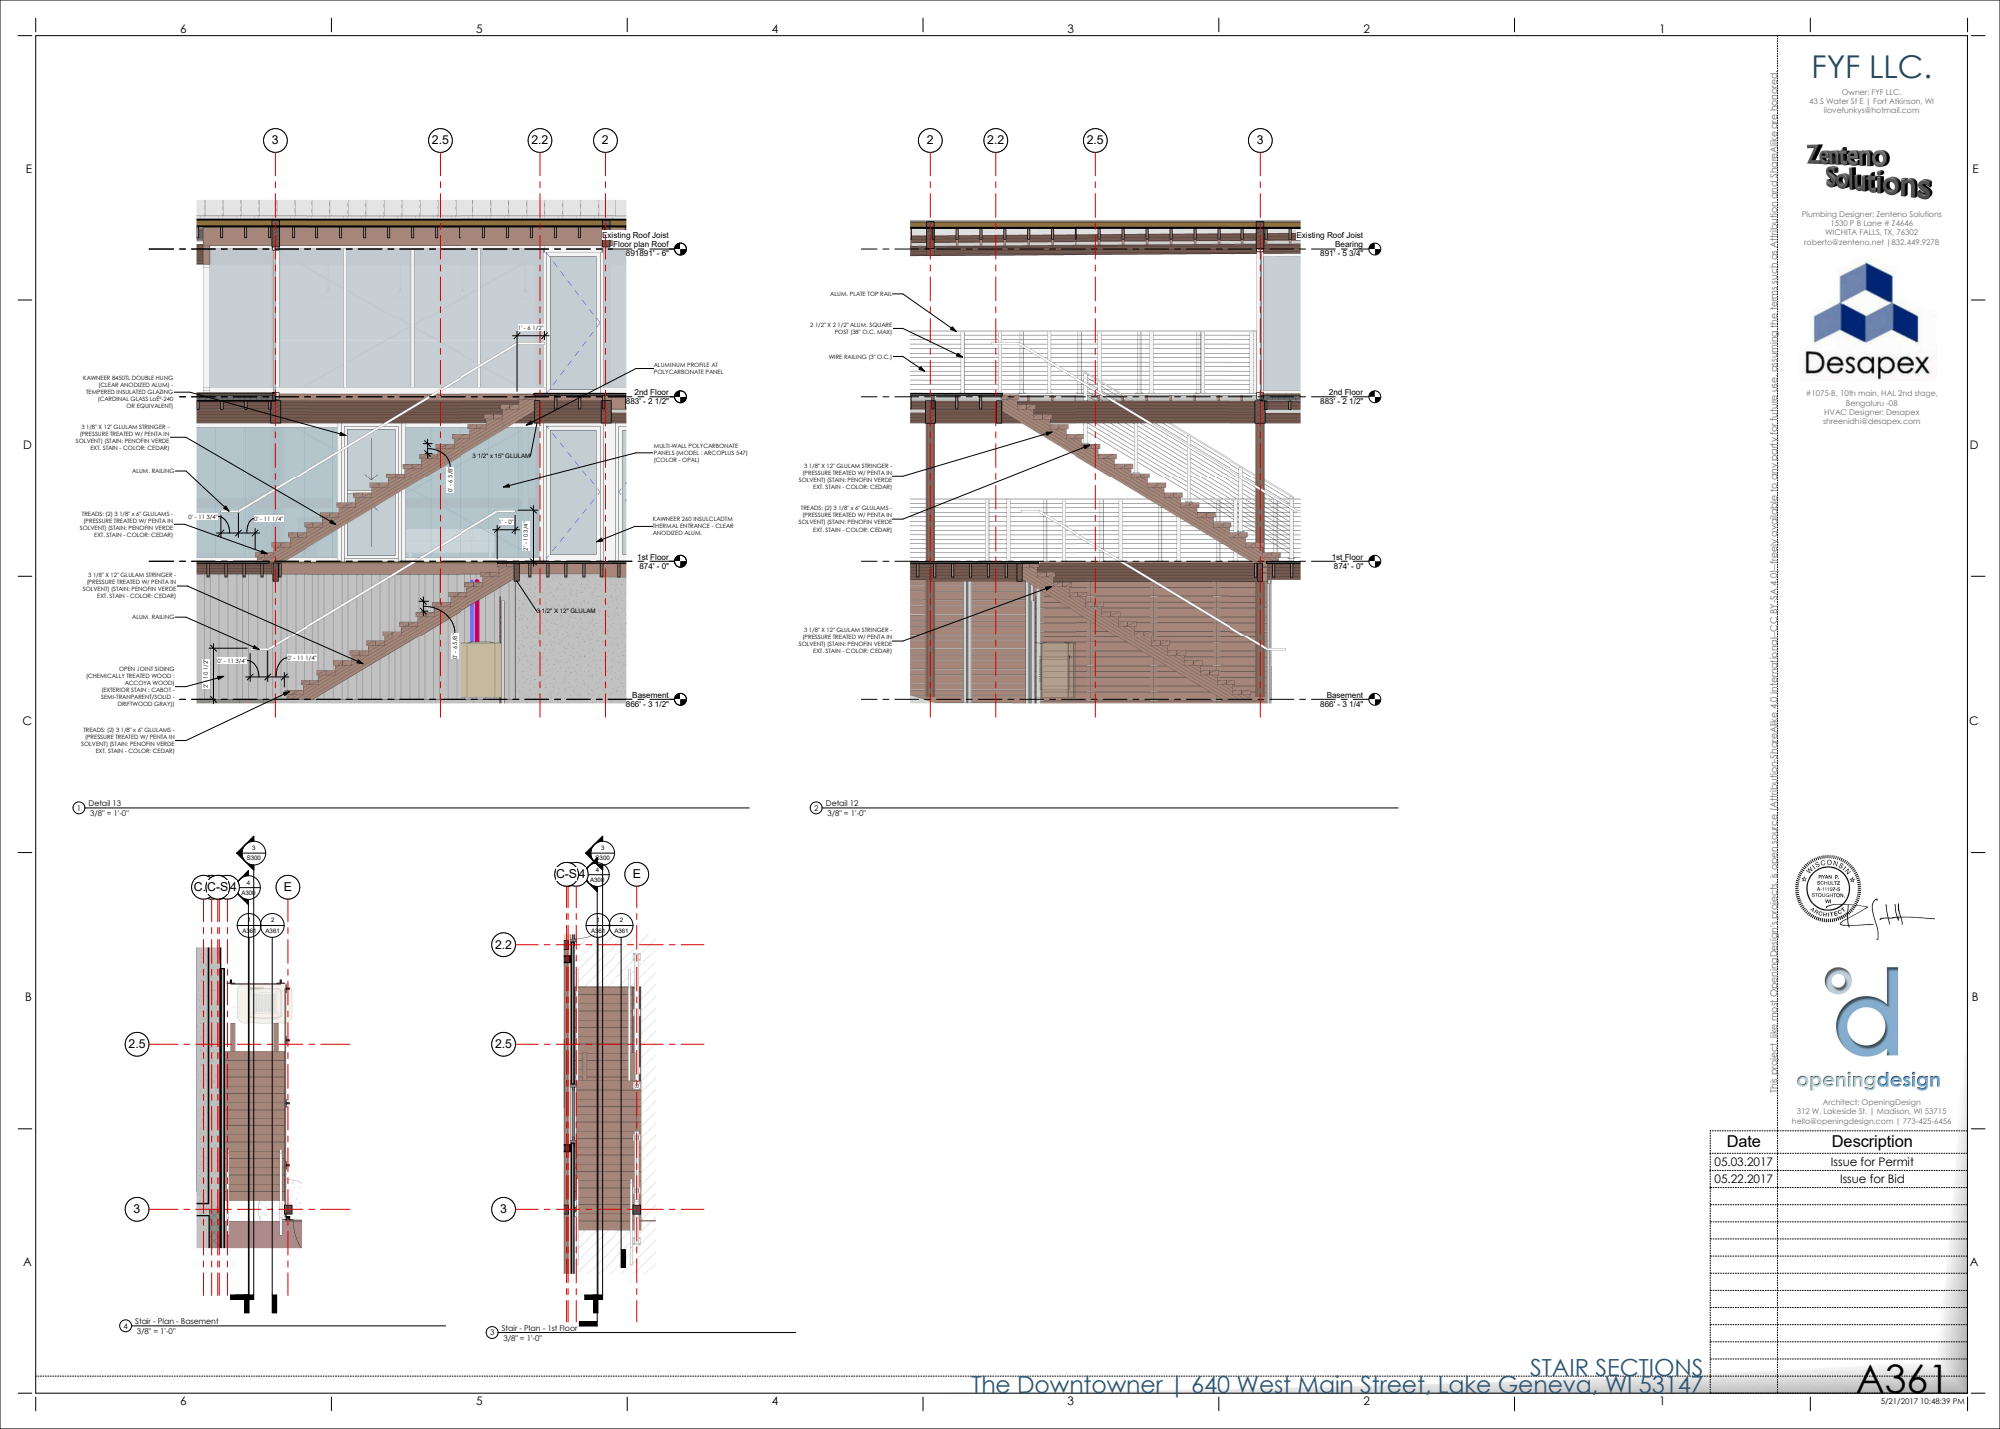
[picture p256: page 1]
1st Floor 874' - 0"; 2nd Floor 883' - 2 1/2"; Basement 866' - 3 1/4"; Basement 866' - 3 1/2"; ALUM. RAILING; 3 1/2" x 15" GLULAM; 3 1/2" X 12" GLULAM; OR EQUIVALENT); ACCOYA WOOD); Bearing 891' - 5 3/4"; 2 1/2" X 2 1/2" ALUM. SQUARE POST (38" O.C. MAX); WIRE RAILING (3" O.C.); Architect: OpeningDesign; FYF LLC.; 3/8" = 1'-0" 1 Detail 13; 3/8" = 1'-0" 2 Detail 12; Date; Description

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

Owner: FYF LLC.

43 S Water St E | Fort Atkinson, WI
ilovefunkys@hotmail.com

Plumbing Designer: Zenteno Solutions

1530 P B Lane # Z4646
WICHITA FALLS, TX, 76302
roberto@zenteno.net |832.449.9278

Existing Roof Joist

Floor plan Roof

ALUM. PLATE TOP RAIL

ALUMINUM PROFILE AT
POLYCARBONATE PANEL

KAWNEER 8450TL DOUBLE HUNG
(CLEAR ANODIZED ALUM) -
TEMPERED INSULATED GLAZING
(CARDINAL GLASS LoĒ²-240

#1075-B, 10th main, HAL 2nd stage,

Bengaluru -08
HVAC Designer: Desapex
shreenidhi@desapex.com

3 1/8" X 12" GLULAM STRINGER -
(PRESSURE TREATED W/ PENTA IN
SOLVENT) (STAIN: PENOFIN VERDE
EXT. STAIN - COLOR: CEDAR)

MULTI-WALL POLYCARBONATE
PANELS (MODEL : ARCOPLUS 547)
(COLOR - OPAL)

TREADS: (2) 3 1/8" x 6" GLULAMS -

KAWNEER 260 INSULCLADTM
THERMAL ENTRANCE - CLEAR
ANODIZED ALUM.

OPEN JOINT SIDING

(CHEMICALLY TREATED WOOD :

(EXTERIOR STAIN : CABOT -
SEMI-TRANPARENT/SOLID -
DRIFTWOOD GRAY))

312 W. Lakeside St. | Madison, WI 53715
hello@openingdesign.com | 773-425-6456

05.03.2017 Issue for Permit
05.22.2017 Issue for Bid

3/8" = 1'-0" 3 Stair - Plan - 1st Floor 3/8" = 1'-0" 4 Stair - Plan - Basement

STAIR SECTIONS The Downtowner | 640 West Main Street, Lake Geneva, WI 53147
