OpeningDesign/Vacation_Rental/Transfer/20170519 ----- ISSUE FOR BID & PERMIT -------/The Downtowner_ARCH_Exterior Details - Sheet - S401 - BRACING DETAILS.pdf

3

C.2

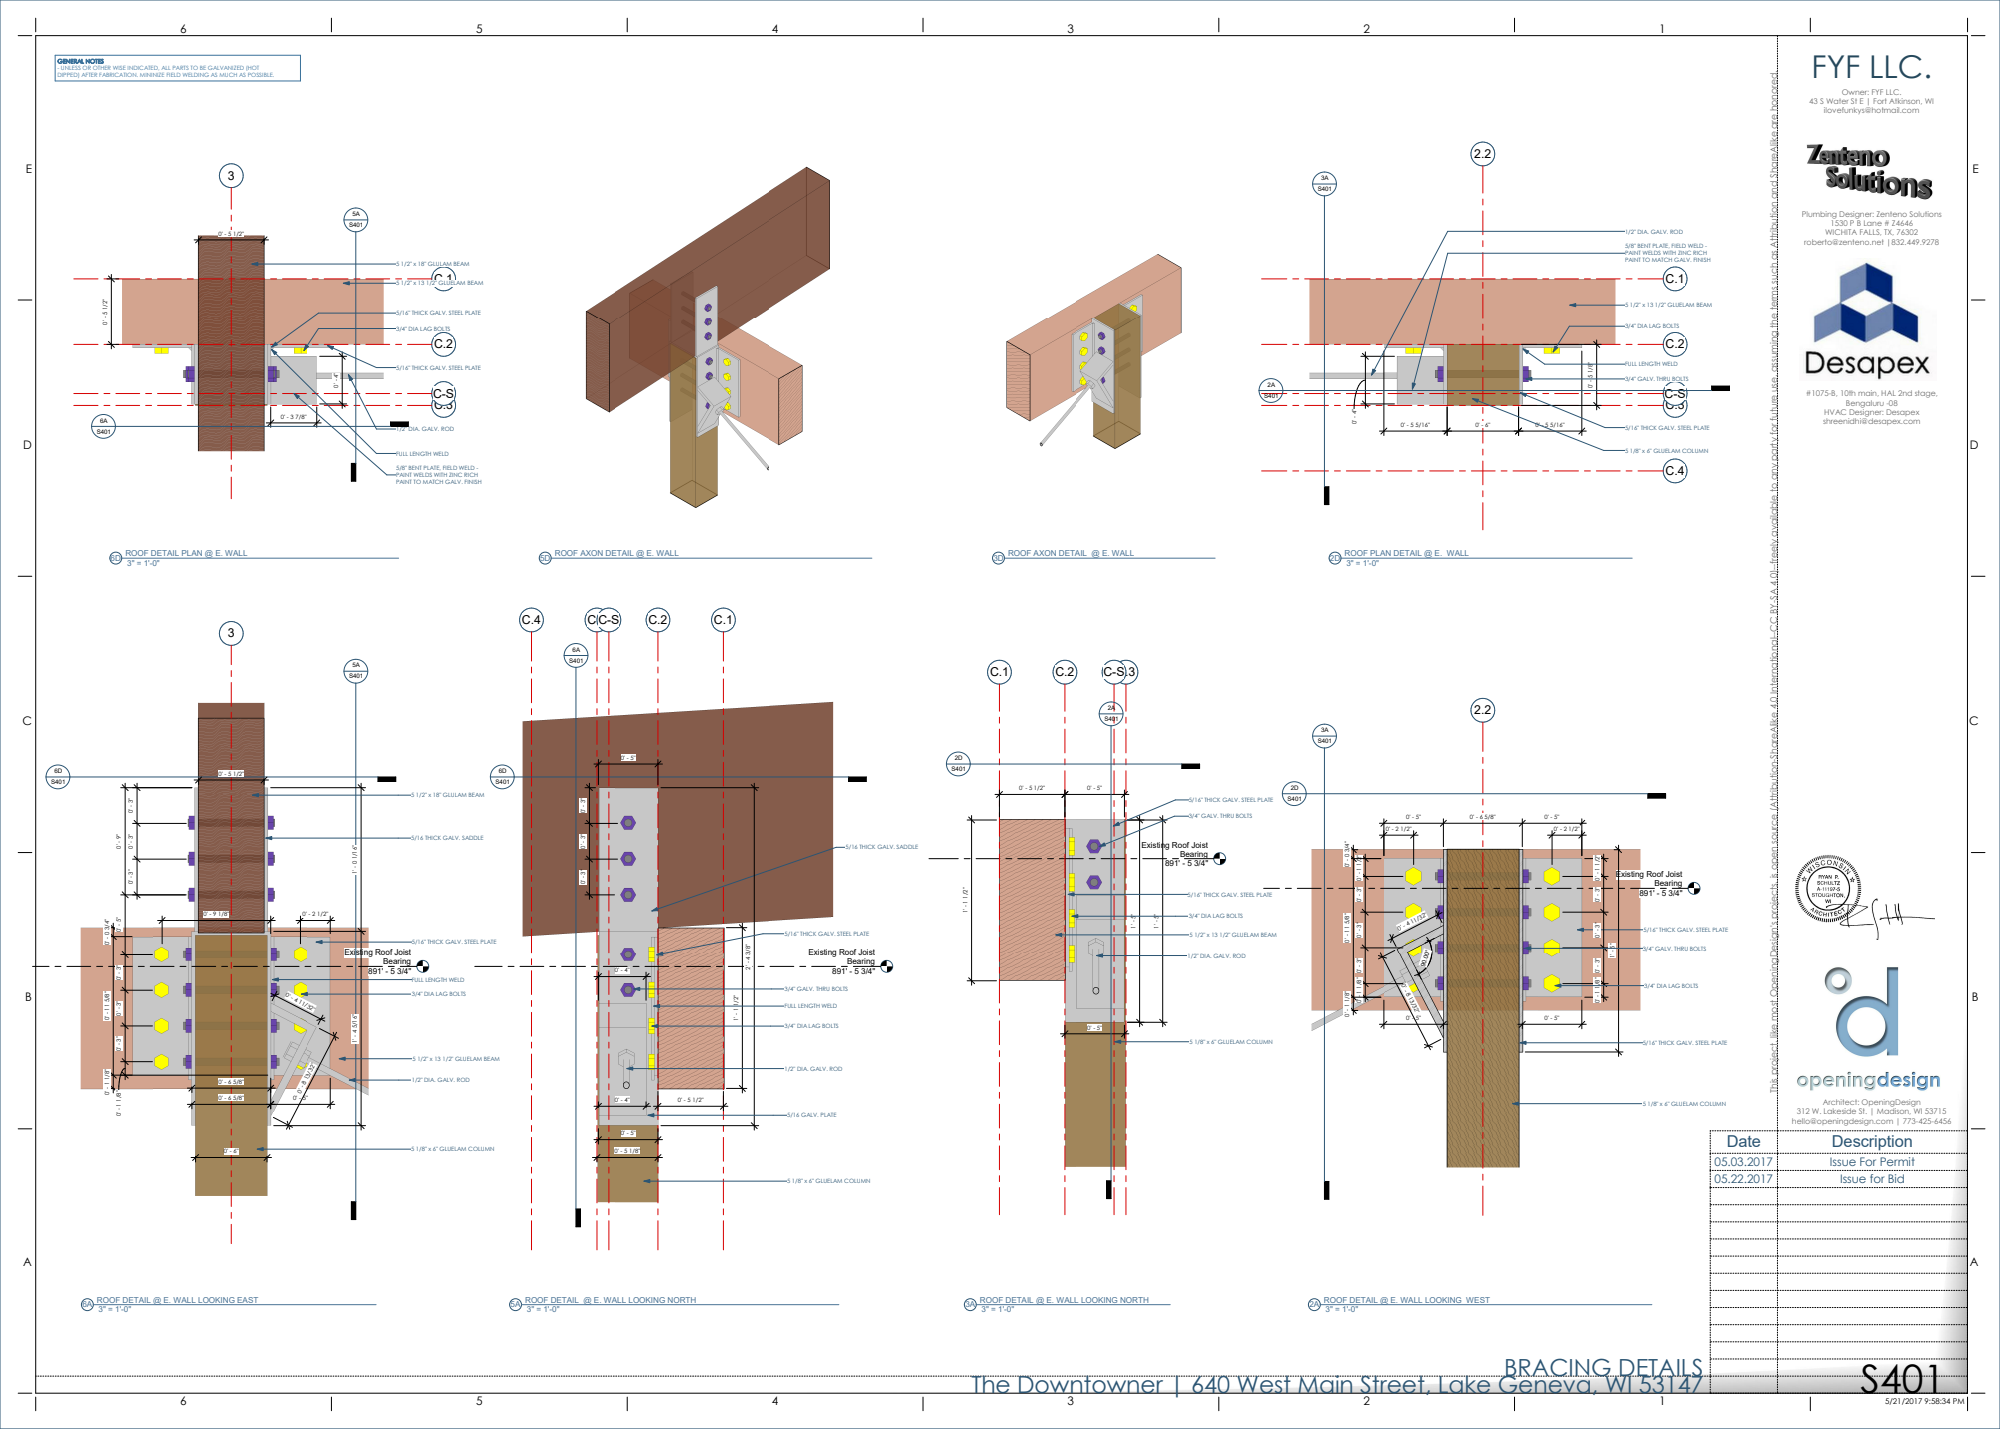
[picture p257: page 1]
5 1/2" x 18" GLULAM BEAM; 5 1/2" x 13 1/2" GLUELAM BEAM; Bearing 891' - 5 3/4"; 5 1/8" x 6" GLUELAM COLUMN; 5/16 GALV. PLATE; Architect: OpeningDesign; FYF LLC.; BRACING DETAILS; ROOF PLAN DETAIL @ E. WALL; 5D ROOF AXON DETAIL @ E. WALL; Date; Description

GENERAL NOTES
- UNLESS OR OTHER WISE INDICATED, ALL PARTS TO BE GALVANIZED (HOT
DIPPED) AFTER FABRICATION. MININIZE FIELD WELDING AS MUCH AS POSSIBLE.

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

Owner: FYF LLC.

43 S Water St E | Fort Atkinson, WI
ilovefunkys@hotmail.com

Plumbing Designer: Zenteno Solutions

1530 P B Lane # Z4646
WICHITA FALLS, TX, 76302
roberto@zenteno.net |832.449.9278

1/2" DIA. GALV. ROD

5/8" BENT PLATE, FIELD WELD -
PAINT WELDS WITH ZINC RICH
PAINT TO MATCH GALV. FINISH

5/16" THICK GALV. STEEL PLATE

3/4" DIA LAG BOLTS

FULL LENGTH WELD

3/4" GALV. THRU BOLTS

#1075-B, 10th main, HAL 2nd stage,

Bengaluru -08
HVAC Designer: Desapex
shreenidhi@desapex.com

3" = 1'-0" 6D ROOF DETAIL PLAN @ E. WALL

ROOF AXON DETAIL @ E. WALL

5/16 THICK GALV. SADDLE

Existing Roof Joist

312 W. Lakeside St. | Madison, WI 53715
hello@openingdesign.com | 773-425-6456

05.03.2017 Issue For Permit
05.22.2017 Issue for Bid

3" = 1'-0" 6A ROOF DETAIL @ E. WALL LOOKING EAST

3" = 1'-0" 5A ROOF DETAIL @ E. WALL LOOKING NORTH

ROOF DETAIL @ E. WALL LOOKING NORTH

ROOF DETAIL @ E. WALL LOOKING WEST

The Downtowner | 640 West Main Street, Lake Geneva, WI 53147
