OpeningDesign/Vacation_Rental/Transfer/20170519 ----- ISSUE FOR BID & PERMIT -------/The Downtowner_ARCH_Exterior Details - Sheet - S402 - BRACING DETAILS.pdf

3

C.3

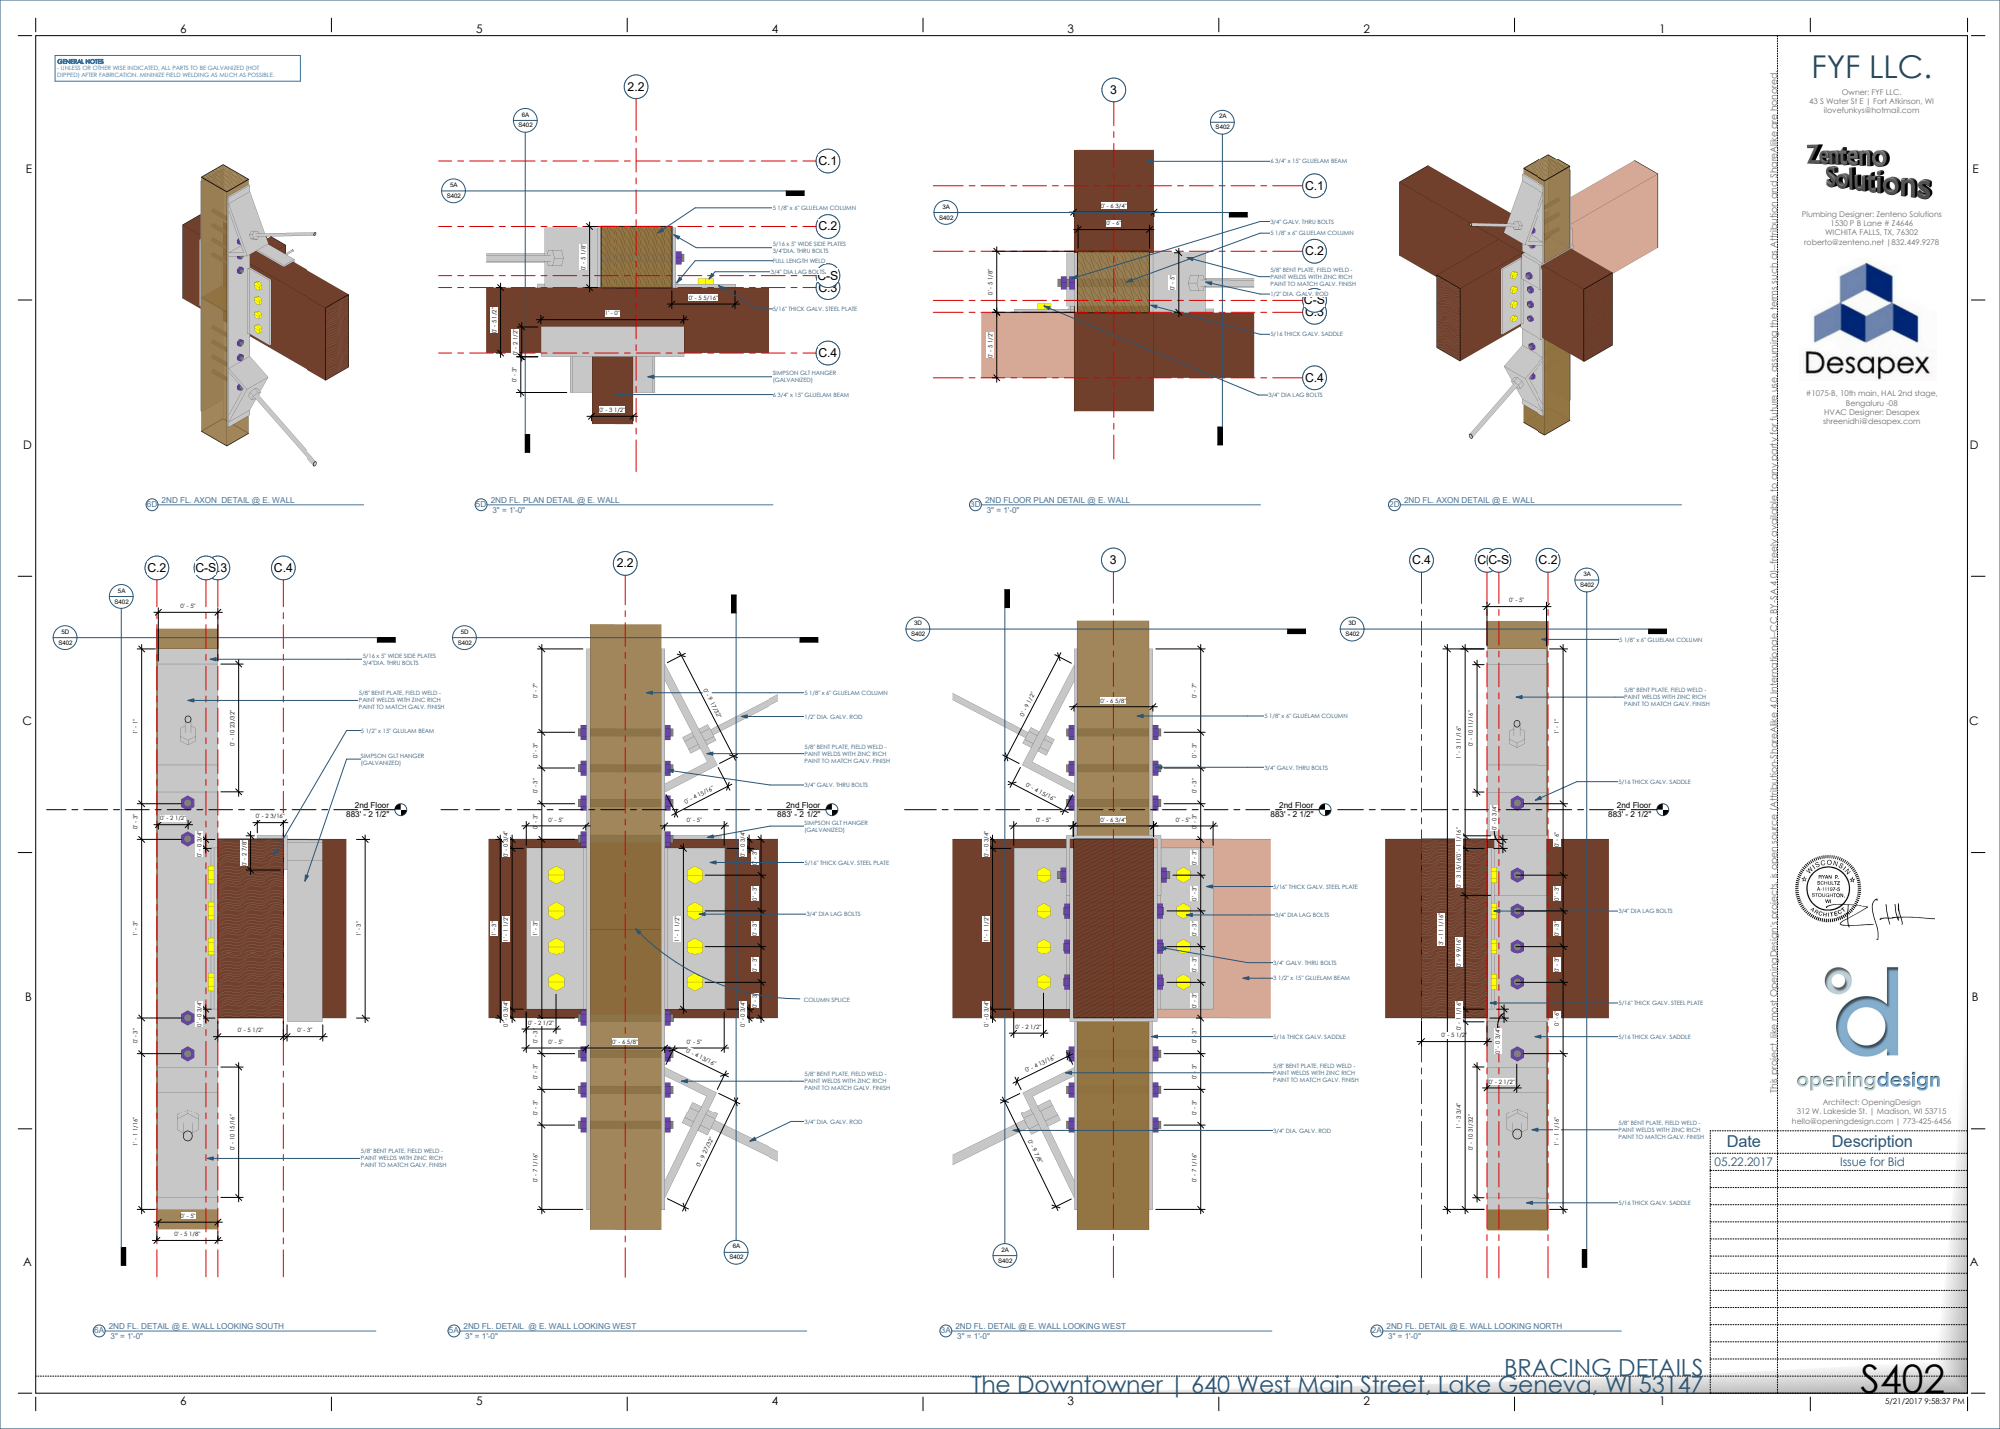
[picture p258: page 1]
2nd Floor 883' - 2 1/2"; 5 1/8" x 6" GLUELAM COLUMN; 6 3/4" x 15" GLUELAM BEAM; 5 1/2" x 15" GLULAM BEAM; 3 1/2" x 15" GLUELAM BEAM; Architect: OpeningDesign; FYF LLC.; BRACING DETAILS; 2ND FLOOR PLAN DETAIL @ E. WALL; 3" = 1'-0" 5D 2ND FL. PLAN DETAIL @ E. WALL; COLUMN SPLICE; Date; Description

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

Owner: FYF LLC.

43 S Water St E | Fort Atkinson, WI
ilovefunkys@hotmail.com

Plumbing Designer: Zenteno Solutions

3/4" GALV. THRU BOLTS

1530 P B Lane # Z4646
WICHITA FALLS, TX, 76302
roberto@zenteno.net |832.449.9278

5/16 x 5" WIDE SIDE PLATES
3/4"DIA. THRU BOLTS
FULL LENGTH WELD

5/8" BENT PLATE, FIELD WELD -
PAINT WELDS WITH ZINC RICH
PAINT TO MATCH GALV. FINISH
1/2" DIA. GALV. ROD

3/4" DIA LAG BOLTS

5/16" THICK GALV. STEEL PLATE

5/16 THICK GALV. SADDLE

SIMPSON GLT HANGER
(GALVANIZED)

#1075-B, 10th main, HAL 2nd stage,

Bengaluru -08
HVAC Designer: Desapex
shreenidhi@desapex.com

6D 2ND FL. AXON DETAIL @ E. WALL

2ND FL. AXON DETAIL @ E. WALL

312 W. Lakeside St. | Madison, WI 53715
hello@openingdesign.com | 773-425-6456

3/4" DIA. GALV. ROD

05.22.2017 Issue for Bid

3" = 1'-0" 6A 2ND FL. DETAIL @ E. WALL LOOKING SOUTH

3" = 1'-0" 5A 2ND FL. DETAIL @ E. WALL LOOKING WEST

2ND FL. DETAIL @ E. WALL LOOKING WEST
The Downtowner | 640 West Main Street, Lake Geneva, WI 53147

2ND FL. DETAIL @ E. WALL LOOKING NORTH
