OpeningDesign/Vacation_Rental/Transfer/20170519 ----- ISSUE FOR BID & PERMIT -------/The Downtowner_ARCH_Exterior Details - Sheet - S403 - BRACING DETAILS.pdf

2

C.2

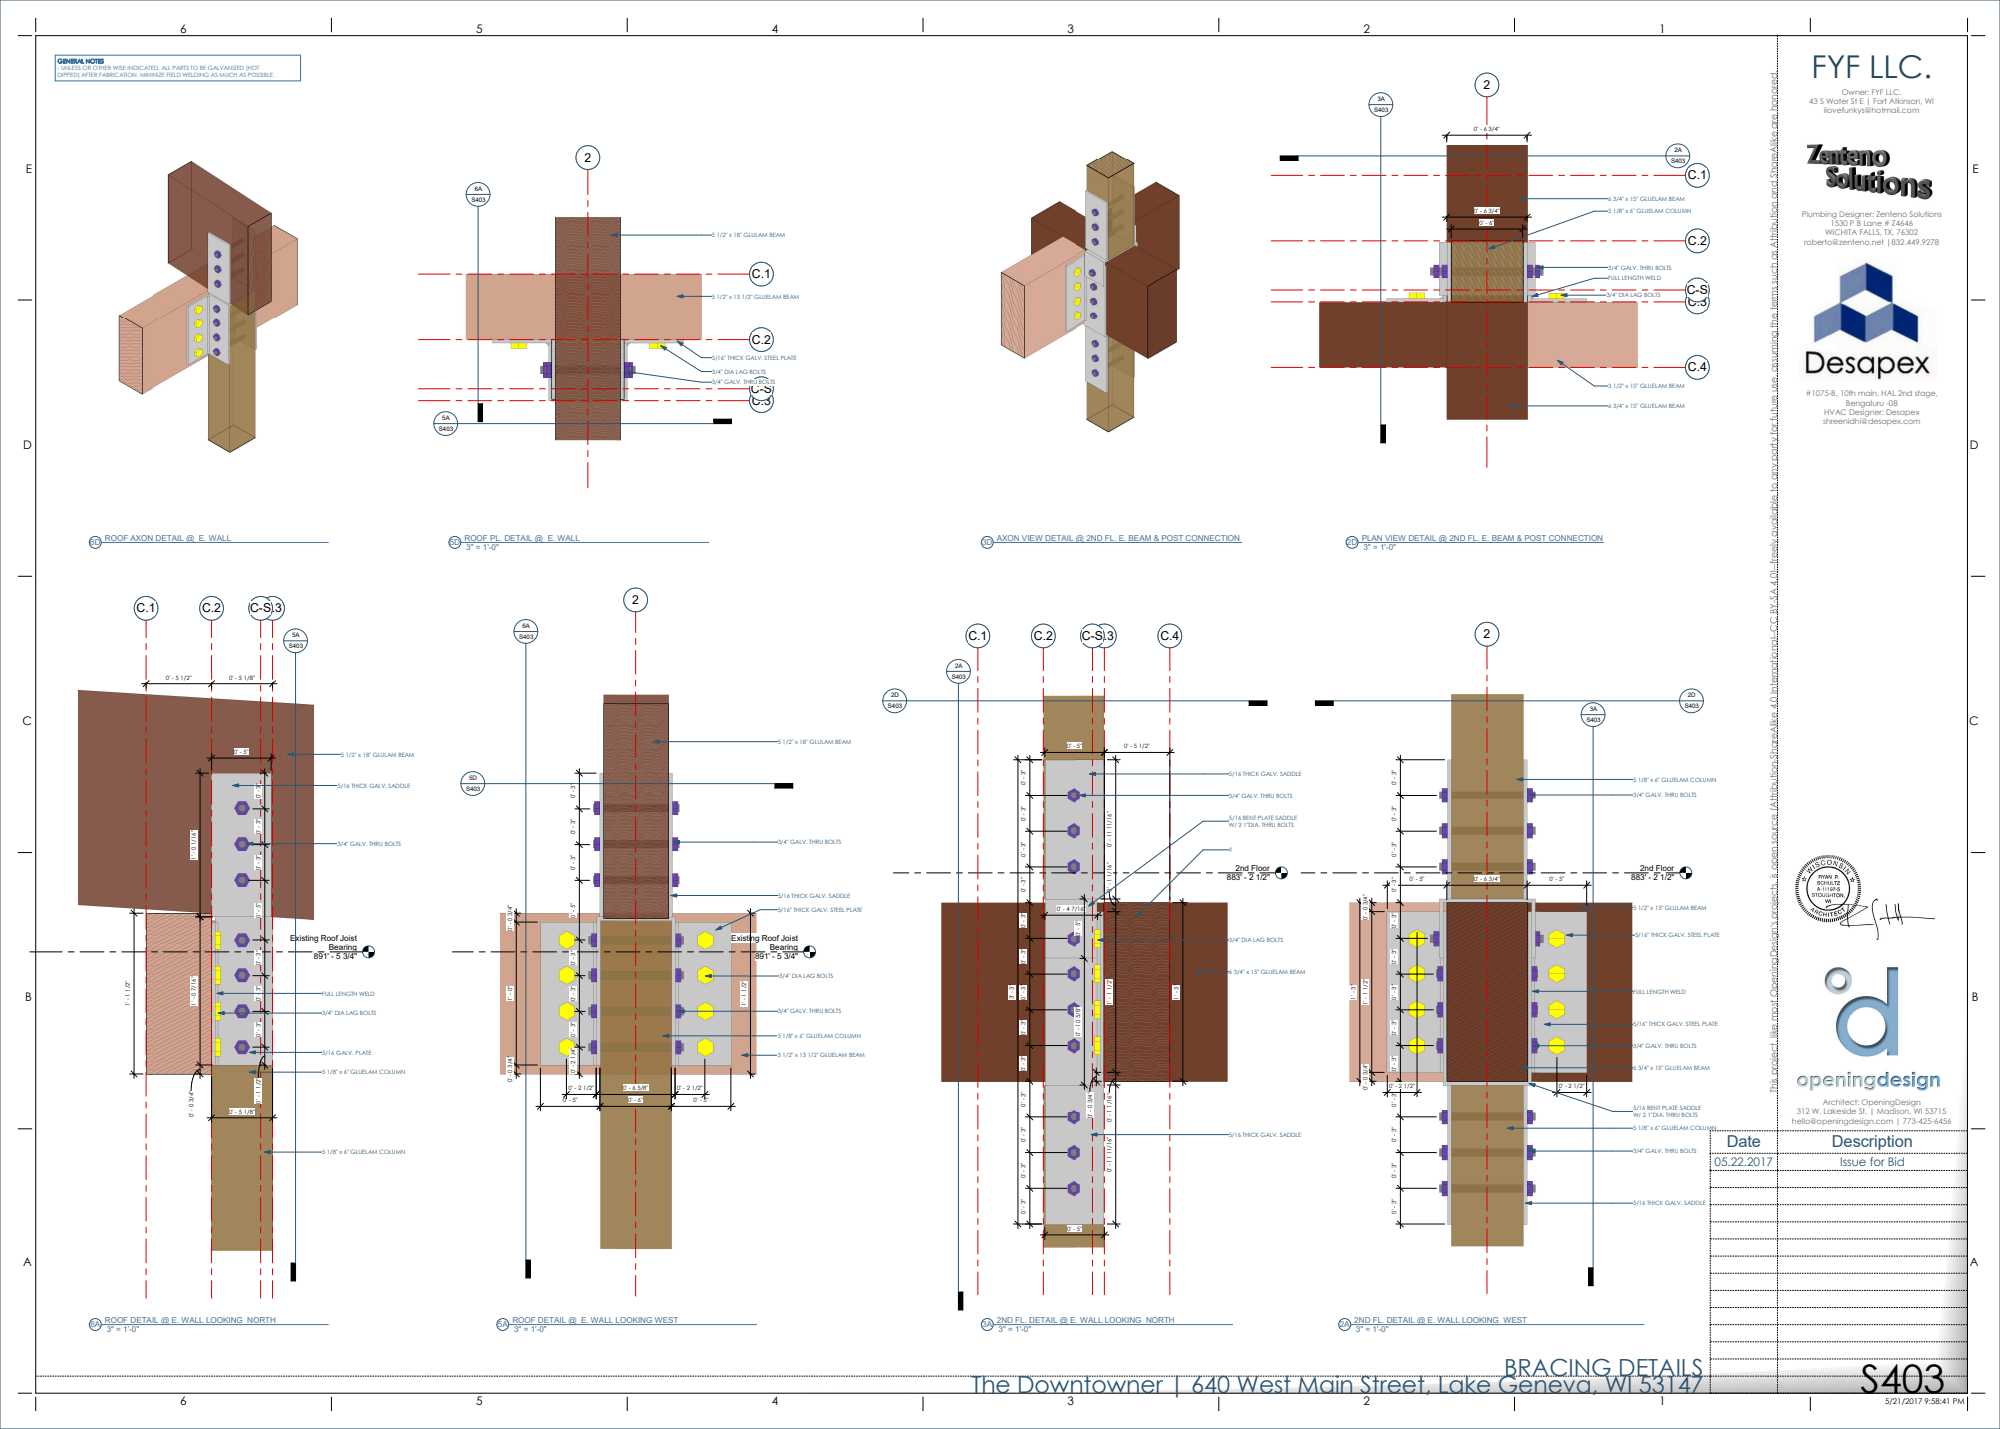
[picture p259: page 1]
Bearing 891' - 5 3/4"; 0' - 3" 0' - 3" 0' - 3" 0' - 5" 0' - 3" 0' - 3" 0' - 3" 0' - 1 1/2" 5 1/8" x 6" GLUELAM COLUMN; 5 1/8" x 6" GLUELAM COLUMN; 5/16 GALV. PLATE; 5 1/2" x 18" GLULAM BEAM; 5 1/2" x 13 1/2" GLUELAM BEAM; 2nd Floor 883' - 2 1/2"; 6 3/4" x 15" GLUELAM BEAM; 3 1/2" x 15" GLUELAM BEAM; 5 1/2" x 15" GLULAM BEAM; FYF LLC.; 3" = 1'-0" 5A ROOF DETAIL @ E. WALL LOOKING WEST; 3" = 1'-0" 2A 2ND FL. DETAIL @ E. WALL LOOKING WEST; Date; Description

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

Owner: FYF LLC.

43 S Water St E | Fort Atkinson, WI
ilovefunkys@hotmail.com

Plumbing Designer: Zenteno Solutions

1530 P B Lane # Z4646
WICHITA FALLS, TX, 76302
roberto@zenteno.net |832.449.9278

3/4" GALV. THRU BOLTS

FULL LENGTH WELD

3/4" DIA LAG BOLTS

5/16" THICK GALV. STEEL PLATE

#1075-B, 10th main, HAL 2nd stage,

Bengaluru -08
HVAC Designer: Desapex
shreenidhi@desapex.com

3" = 1'-0" 2D PLAN VIEW DETAIL @ 2ND FL. E. BEAM & POST CONNECTION 3D AXON VIEW DETAIL @ 2ND FL. E. BEAM & POST CONNECTION 6D ROOF AXON DETAIL @ E. WALL

3" = 1'-0" 5D ROOF PL. DETAIL @ E. WALL

5/16 THICK GALV. SADDLE

0' - 3" 0' - 3" 0' - 3" 0' - 3" 0' - 3" 0' - 3" 0' - 3" 0' - 3" 0' - 3" 0' - 3" 0' - 3" 0' - 3" 0' - 3" 0' - 2 1/2" 0' - 2 1/2" 3/4" GALV. THRU BOLTS 5/16 THICK GALV. SADDLE 5/16 BENT PLATE SADDLE W/ 2 1"DIA. THRU BOLTS Architect: OpeningDesign 312 W. Lakeside St. | Madison, WI 53715 hello@openingdesign.com | 773-425-6456

5/16 BENT PLATE SADDLE
W/ 2 1"DIA. THRU BOLTS

Existing Roof Joist

05.22.2017 Issue for Bid

3" = 1'-0" 6A ROOF DETAIL @ E. WALL LOOKING NORTH

3" = 1'-0" 3A 2ND FL. DETAIL @ E. WALL LOOKING NORTH
S403 BRACING DETAILS The Downtowner | 640 West Main Street, Lake Geneva, WI 53147
