OpeningDesign/Vacation_Rental/Transfer/20170519 ----- ISSUE FOR BID & PERMIT -------/The Downtowner_ARCH_Exterior Details - Sheet - S404 - BRACING DETAILS.pdf

E

E

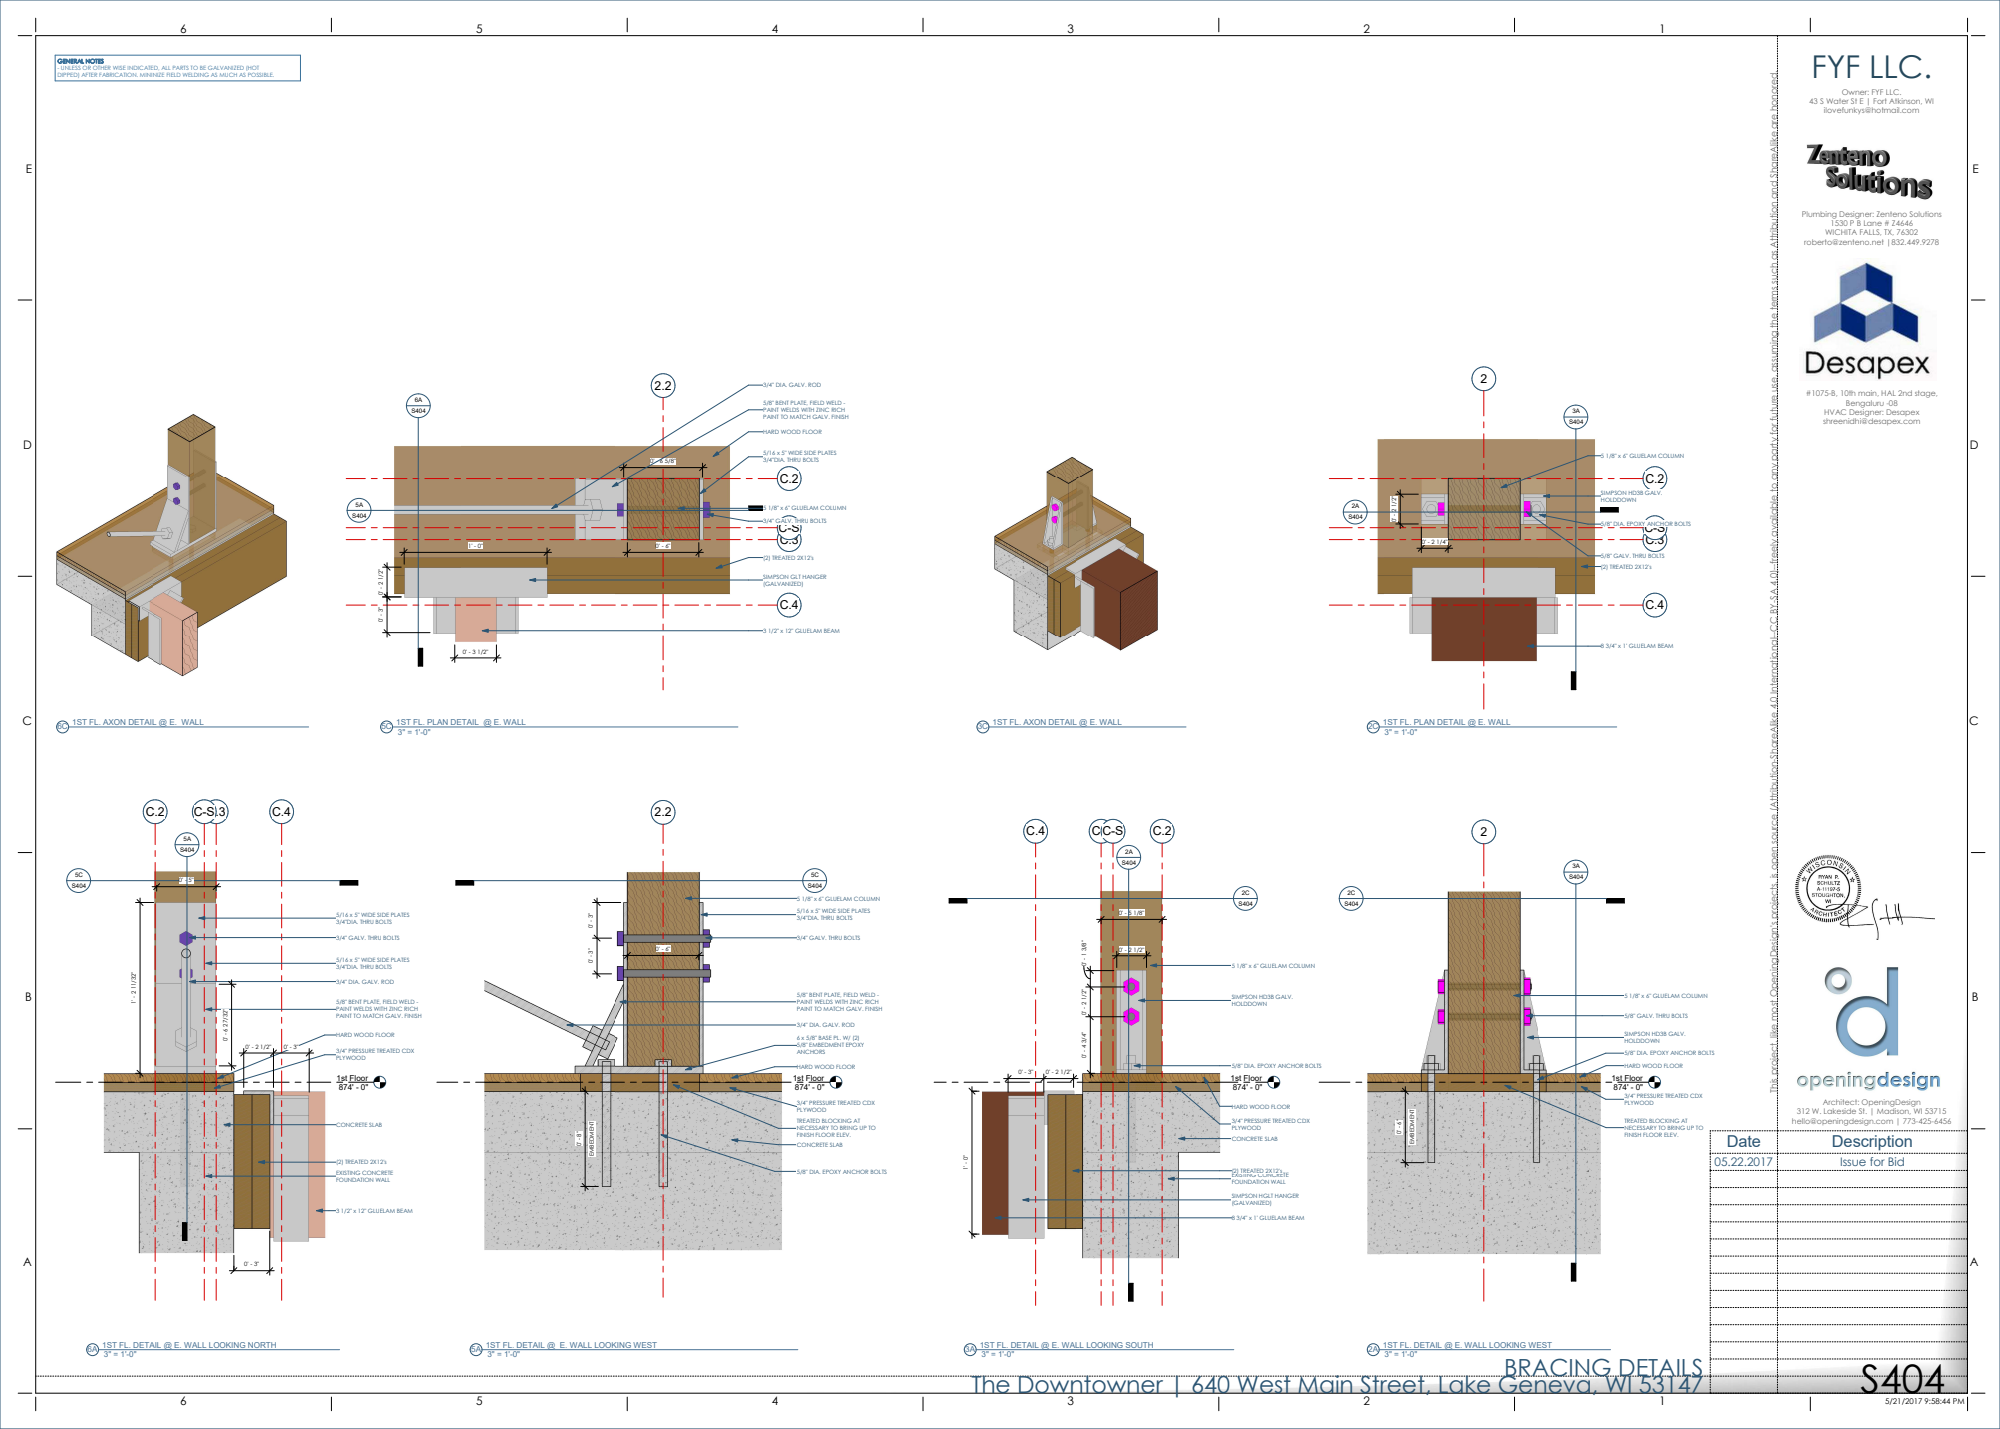
[picture p260: page 1]
5 1/8" x 6" GLUELAM COLUMN; (2) TREATED 2X12's; SIMPSON GLT HANGER (GALVANIZED); 3 1/2" x 12" GLUELAM BEAM; 1st Floor 874' - 0"; CONCRETE SLAB; EXISTING CONCRETE FOUNDATION WALL; 8 3/4" x 1' GLUELAM BEAM; SIMPSON HD3B GALV. HOLDDOWN; EMBEDMENT; 6 x 5/8" BASE PL. W/ (2) 5/8" EMBEDMENT EPOXY ANCHORS; HARD WOOD FLOOR; Architect: OpeningDesign; FYF LLC.; Date; Description

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

Owner: FYF LLC.

43 S Water St E | Fort Atkinson, WI
ilovefunkys@hotmail.com

Plumbing Designer: Zenteno Solutions

1530 P B Lane # Z4646
WICHITA FALLS, TX, 76302
roberto@zenteno.net |832.449.9278

3/4" DIA. GALV. ROD

#1075-B, 10th main, HAL 2nd stage,

5/8" BENT PLATE, FIELD WELD -
PAINT WELDS WITH ZINC RICH
PAINT TO MATCH GALV. FINISH

Bengaluru -08
HVAC Designer: Desapex
shreenidhi@desapex.com

HARD WOOD FLOOR

5/16 x 5" WIDE SIDE PLATES
3/4"DIA. THRU BOLTS

3/4" GALV. THRU BOLTS

5/8" DIA. EPOXY ANCHOR BOLTS

5/8" GALV. THRU BOLTS

6C 1ST FL. AXON DETAIL @ E. WALL

3" = 1'-0" 5C 1ST FL. PLAN DETAIL @ E. WALL

3" = 1'-0" 2C 1ST FL. PLAN DETAIL @ E. WALL 3C 1ST FL. AXON DETAIL @ E. WALL

0' - 3" 0' - 3" 3/4" GALV. THRU BOLTS 5/16 x 5" WIDE SIDE PLATES 3/4"DIA. THRU BOLTS

0' - 4 3/4" 0' - 2 1/2" 0' - 1 3/8" 5 1/8" x 6" GLUELAM COLUMN 0' - 2 1/2" SIMPSON HD3B GALV. HOLDDOWN

3/4" PRESSURE TREATED CDX
PLYWOOD

1st Floor

312 W. Lakeside St. | Madison, WI 53715
hello@openingdesign.com | 773-425-6456

TREATED BLOCKING AT
NECESSARY TO BRING UP TO
FINISH FLOOR ELEV.
CONCRETE SLAB

05.22.2017 Issue for Bid

SIMPSON HGLT HANGER
(GALVANIZED)

3" = 1'-0" 6A 1ST FL. DETAIL @ E. WALL LOOKING NORTH

3" = 1'-0" 2A 1ST FL. DETAIL @ E. WALL LOOKING WEST 3" = 1'-0" 5A 1ST FL. DETAIL @ E. WALL LOOKING WEST

3" = 1'-0" 3A 1ST FL. DETAIL @ E. WALL LOOKING SOUTH
S404 BRACING DETAILS The Downtowner | 640 West Main Street, Lake Geneva, WI 53147
