OpeningDesign/Vacation_Rental/Transfer/20170519 ----- ISSUE FOR BID & PERMIT -------/The_Downtowner_PLMB_ZS - Sheet - P1-04 - DETAILS.pdf

# SWEDGELOCK ADAPTER

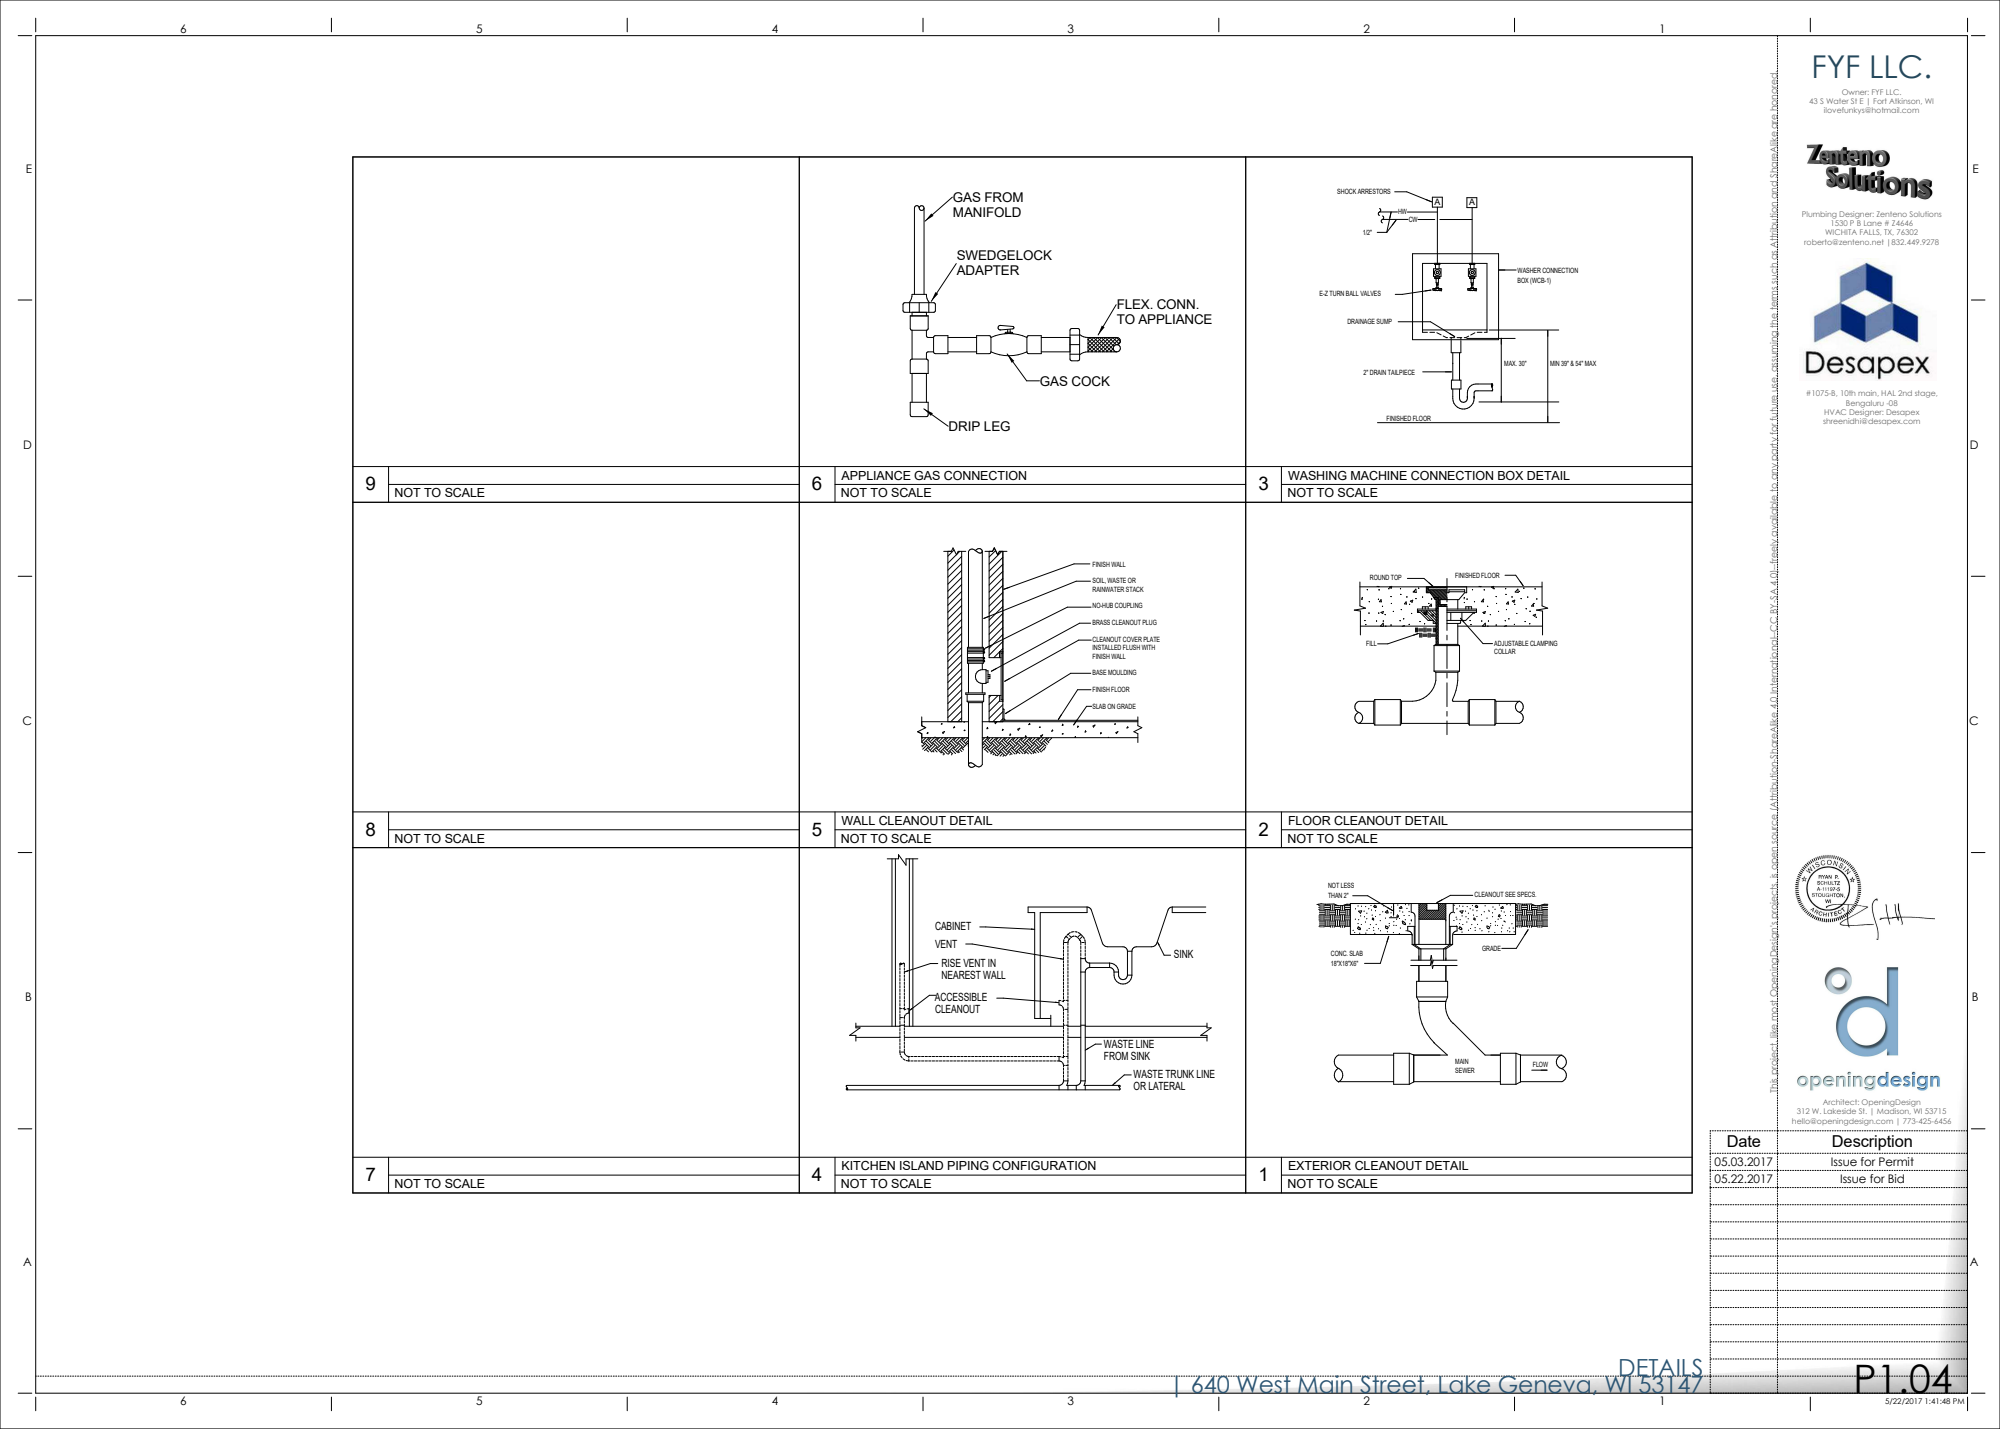
[picture p261: page 1]
GAS COCK; GAS FROM MANIFOLD; DRIP LEG; FLEX. CONN. TO APPLIANCE; SHOCK ARRESTORS; DRAINAGE SUMP; 2" DRAIN TAILPIECE; FINISHED FLOOR; WASHER CONNECTION BOX (WCB-1); MAX. 30"; MIN 39" & 54" MAX; ROUND TOP; THAN 2"; CLEANOUT SEE SPECS.; NOT LESS; CONC. SLAB 18"X18"X6"; MAIN SEWER; GRADE; FLOW; ADJUSTABLE CLAMPING COLLAR; FILL; FINISH WALL; BASE MOULDING; FINISH FLOOR; CLEANOUT; ACCESSIBLE; SINK; NOT TO SCALE 1 NOT TO SCALE 4 NOT TO SCALE 7; KITCHEN ISLAND PIPING CONFIGURATION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

Owner: FYF LLC.

43 S Water St E | Fort Atkinson, WI
ilovefunkys@hotmail.com

Plumbing Designer: Zenteno Solutions

1530 P B Lane # Z4646
WICHITA FALLS, TX, 76302
roberto@zenteno.net |832.449.9278

E-Z TURN BALL VALVES

#1075-B, 10th main, HAL 2nd stage,

Bengaluru -08
HVAC Designer: Desapex
shreenidhi@desapex.com

APPLIANCE GAS CONNECTION

WASHING MACHINE CONNECTION BOX DETAIL

NOT TO SCALE 3 NOT TO SCALE 6 NOT TO SCALE 9

SOIL, WASTE OR
RAINWATER STACK

NO-HUB COUPLING

BRASS CLEANOUT PLUG

CLEANOUT COVER PLATE
INSTALLED FLUSH WITH
FINISH WALL

SLAB ON GRADE

WALL CLEANOUT DETAIL

FLOOR CLEANOUT DETAIL

NOT TO SCALE 2 NOT TO SCALE 5 NOT TO SCALE 8

CABINET
VENT
RISE VENT IN
NEAREST WALL

WASTE LINE
FROM SINK
WASTE TRUNK LINE
OR LATERAL

312 W. Lakeside St. | Madison, WI 53715
hello@openingdesign.com | 773-425-6456

EXTERIOR CLEANOUT DETAIL

05.03.2017 Issue for Permit
05.22.2017 Issue for Bid

DETAILS | 640 West Main Street, Lake Geneva, WI 53147
