OpeningDesign/Vacation_Rental/Transfer/20170503 ----- ISSUE FOR PERMIT ------/M-001 - HVAC Basement & Roof plan.pdf

B

C.3 E

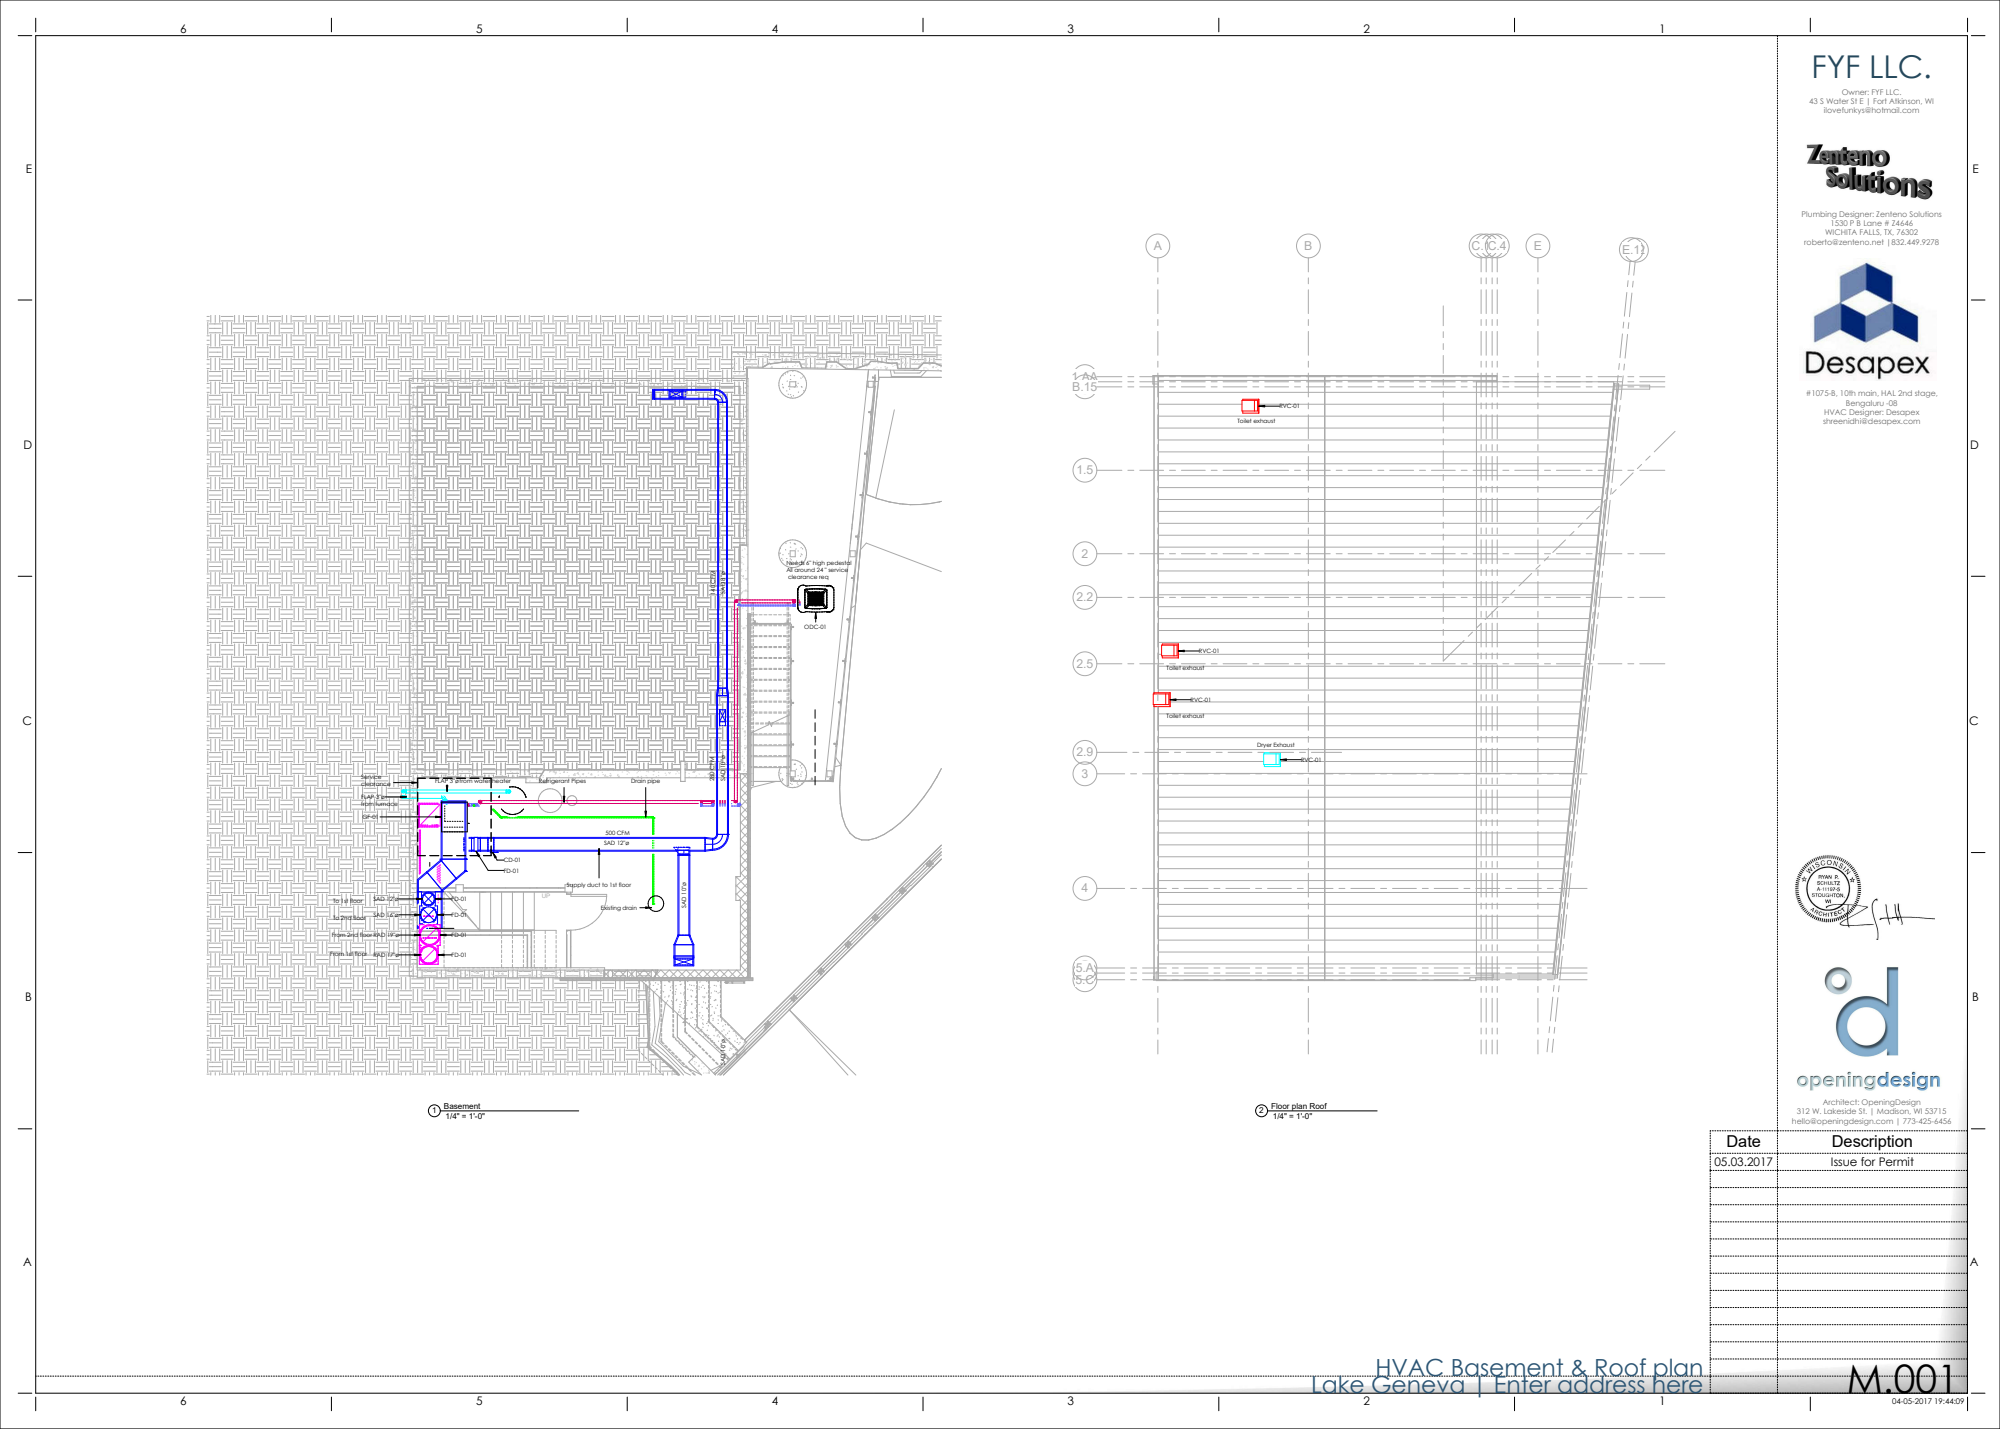
[picture p262: page 1]
500 CFM; SAD 12"ø; SAD 10"ø SAD 8"ø; 280 CFM 140 CFM; ODC-01; RAD 17"ø; To 1st floor; To 2nd floor; From 2nd floor; From 1st floor; FLAP 3"ø; FLAP 3"ø from furnace; Service; clearance; Refrigerant Pipes; Drain pipe; Existing drain; RAD 19"ø; SAD 16"ø; SAD 10"ø; RVC-01; Architect: OpeningDesign; FYF LLC.; 1/4" = 1'-0" 1 Basement; Dryer Exhaust; Toilet exhaust; Date; Description; Issue for Permit

Owner: FYF LLC.

43 S Water St E | Fort Atkinson, WI
ilovefunkys@hotmail.com

Plumbing Designer: Zenteno Solutions

1530 P B Lane # Z4646
WICHITA FALLS, TX, 76302
roberto@zenteno.net |832.449.9278

#1075-B, 10th main, HAL 2nd stage,

Bengaluru -08
HVAC Designer: Desapex
shreenidhi@desapex.com

Needs 6" high pedestal
All around 24 " service
clearance req

from water heater

Supply duct to 1st floor

1/4" = 1'-0" 2 Floor plan Roof

312 W. Lakeside St. | Madison, WI 53715
hello@openingdesign.com | 773-425-6456

HVAC Basement & Roof plan Lake Geneva | Enter address here
