OpeningDesign/Vacation_Rental/Transfer/20170503 ----- ISSUE FOR PERMIT ------/A102 - BASEMENT & ROOF FLOOR PLANS.pdf

B

C.3 E

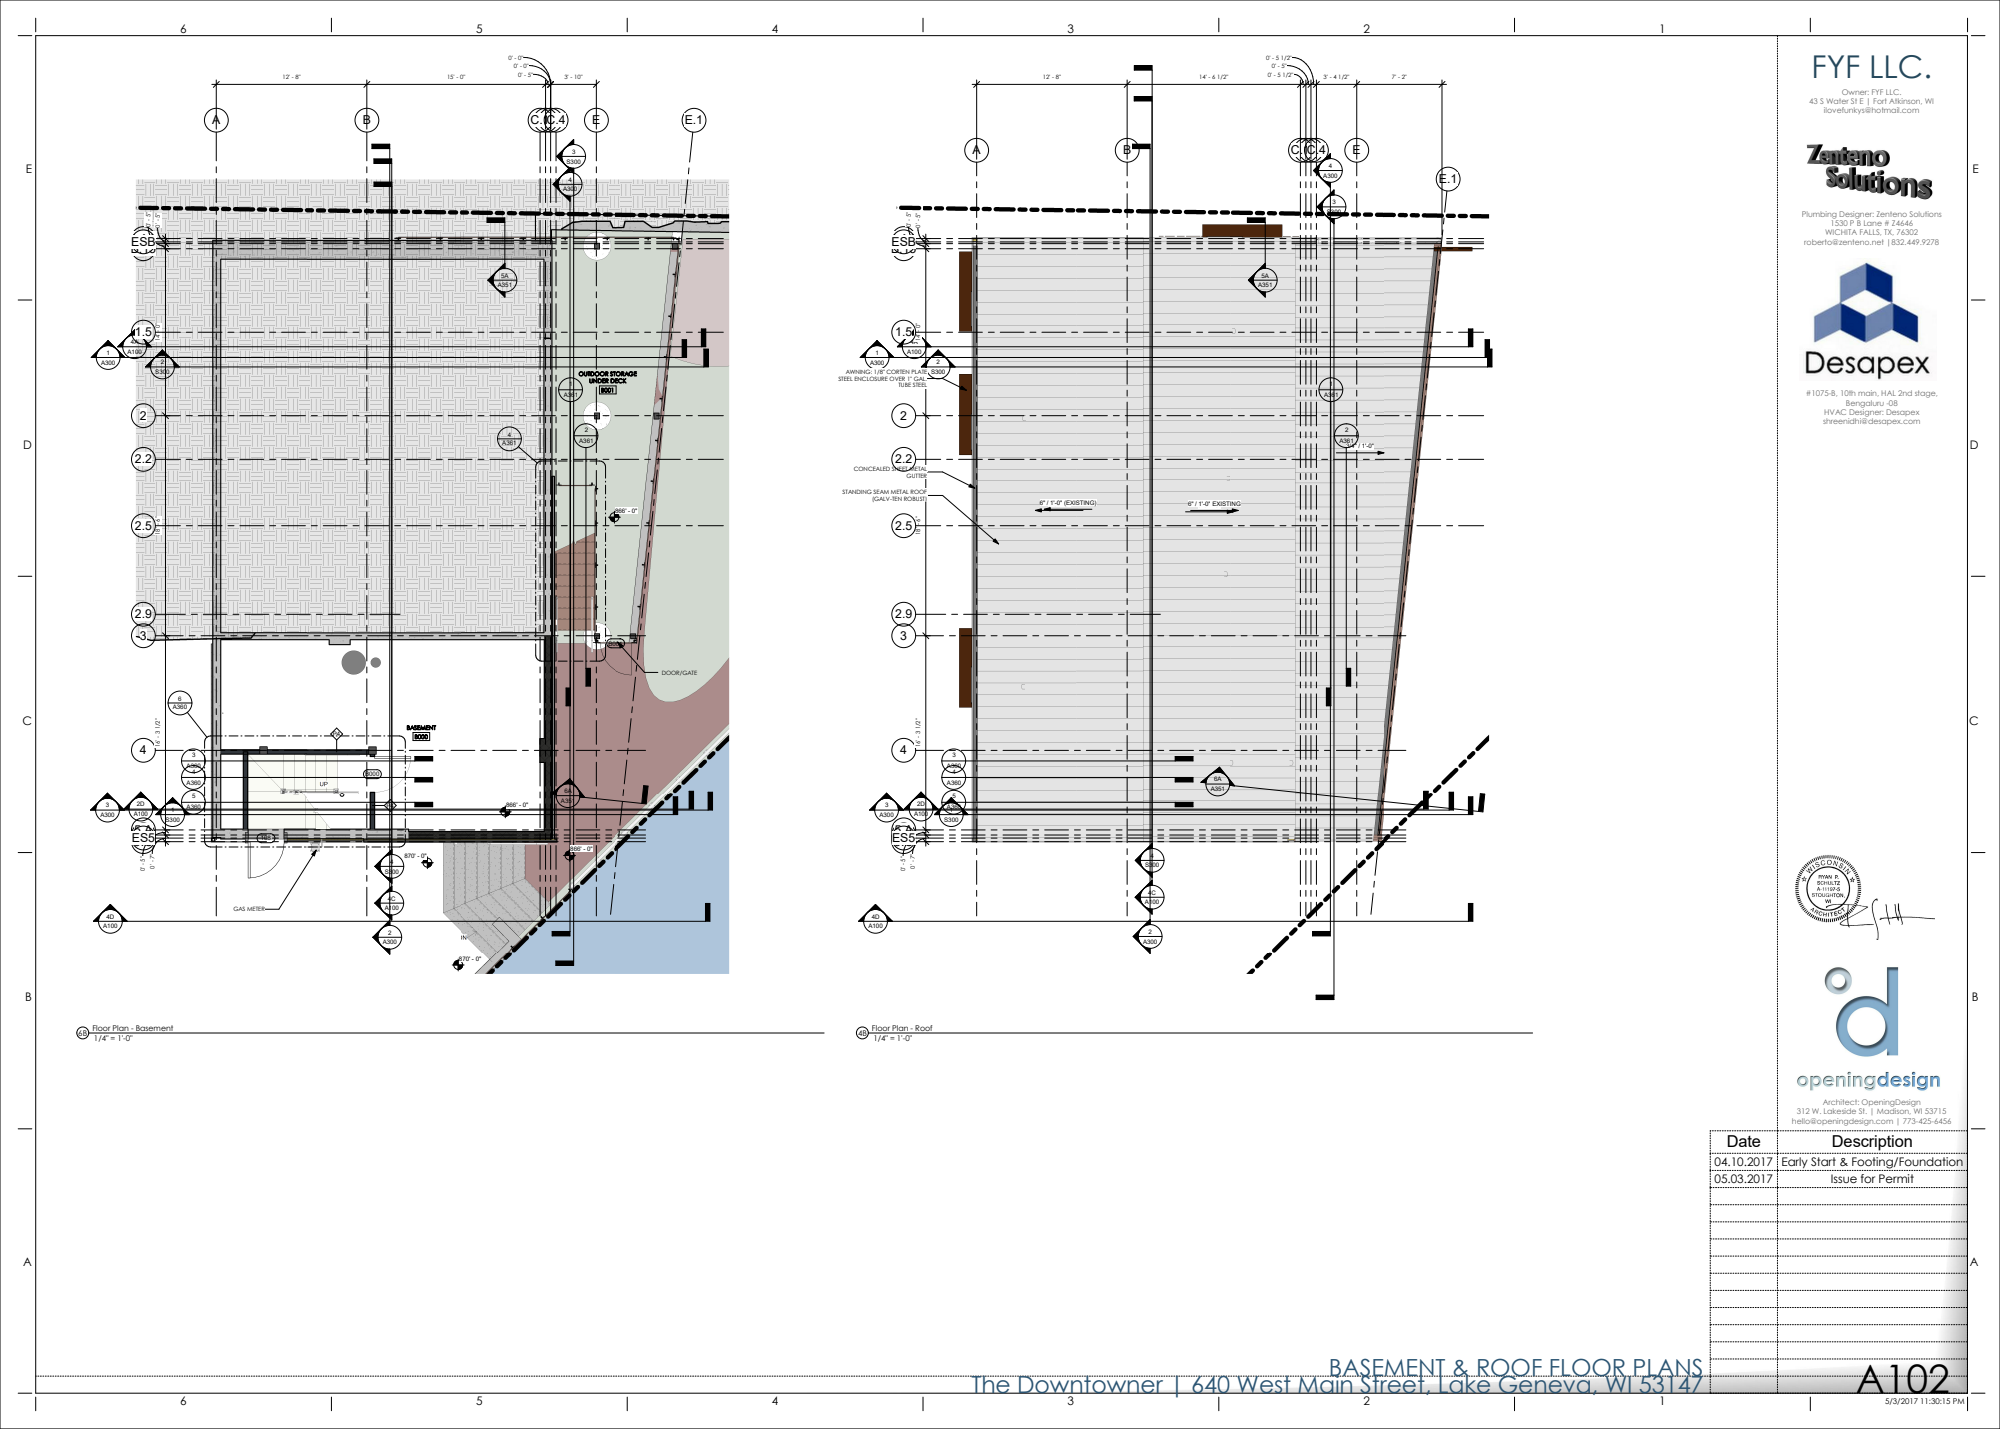
[picture p263: page 1]
BASEMENT; OUTDOOR STORAGE UNDER DECK; GAS METER; DOOR/GATE; ESB; 6" / 1'-0" (EXISTING); 6" / 1'-0" EXISTING; GUTTER; TUBE STEEL; Architect: OpeningDesign; FYF LLC.; 1/4" = 1'-0" 6B Floor Plan - Basement; 1/4" = 1'-0" 4B Floor Plan - Roof; Date; Description

Owner: FYF LLC.

43 S Water St E | Fort Atkinson, WI
ilovefunkys@hotmail.com

Plumbing Designer: Zenteno Solutions

1530 P B Lane # Z4646
WICHITA FALLS, TX, 76302
roberto@zenteno.net |832.449.9278

AWNING: 1/8" CORTEN PLATE
STEEL ENCLOSURE OVER 1" GAL.

#1075-B, 10th main, HAL 2nd stage,

Bengaluru -08
HVAC Designer: Desapex
shreenidhi@desapex.com

CONCEALED SHEET METAL

STANDING SEAM METAL ROOF

(GALV-TEN ROBUST)

312 W. Lakeside St. | Madison, WI 53715
hello@openingdesign.com | 773-425-6456

04.10.2017 Early Start & Footing/Foundation
05.03.2017 Issue for Permit

BASEMENT & ROOF FLOOR PLANS The Downtowner | 640 West Main Street, Lake Geneva, WI 53147
