OpeningDesign/Vacation_Rental/Transfer/20170503 ----- ISSUE FOR PERMIT ------/A151 - 1ST & 2ND REFLECTED CEILING PLANS.pdf

B

C.3 E

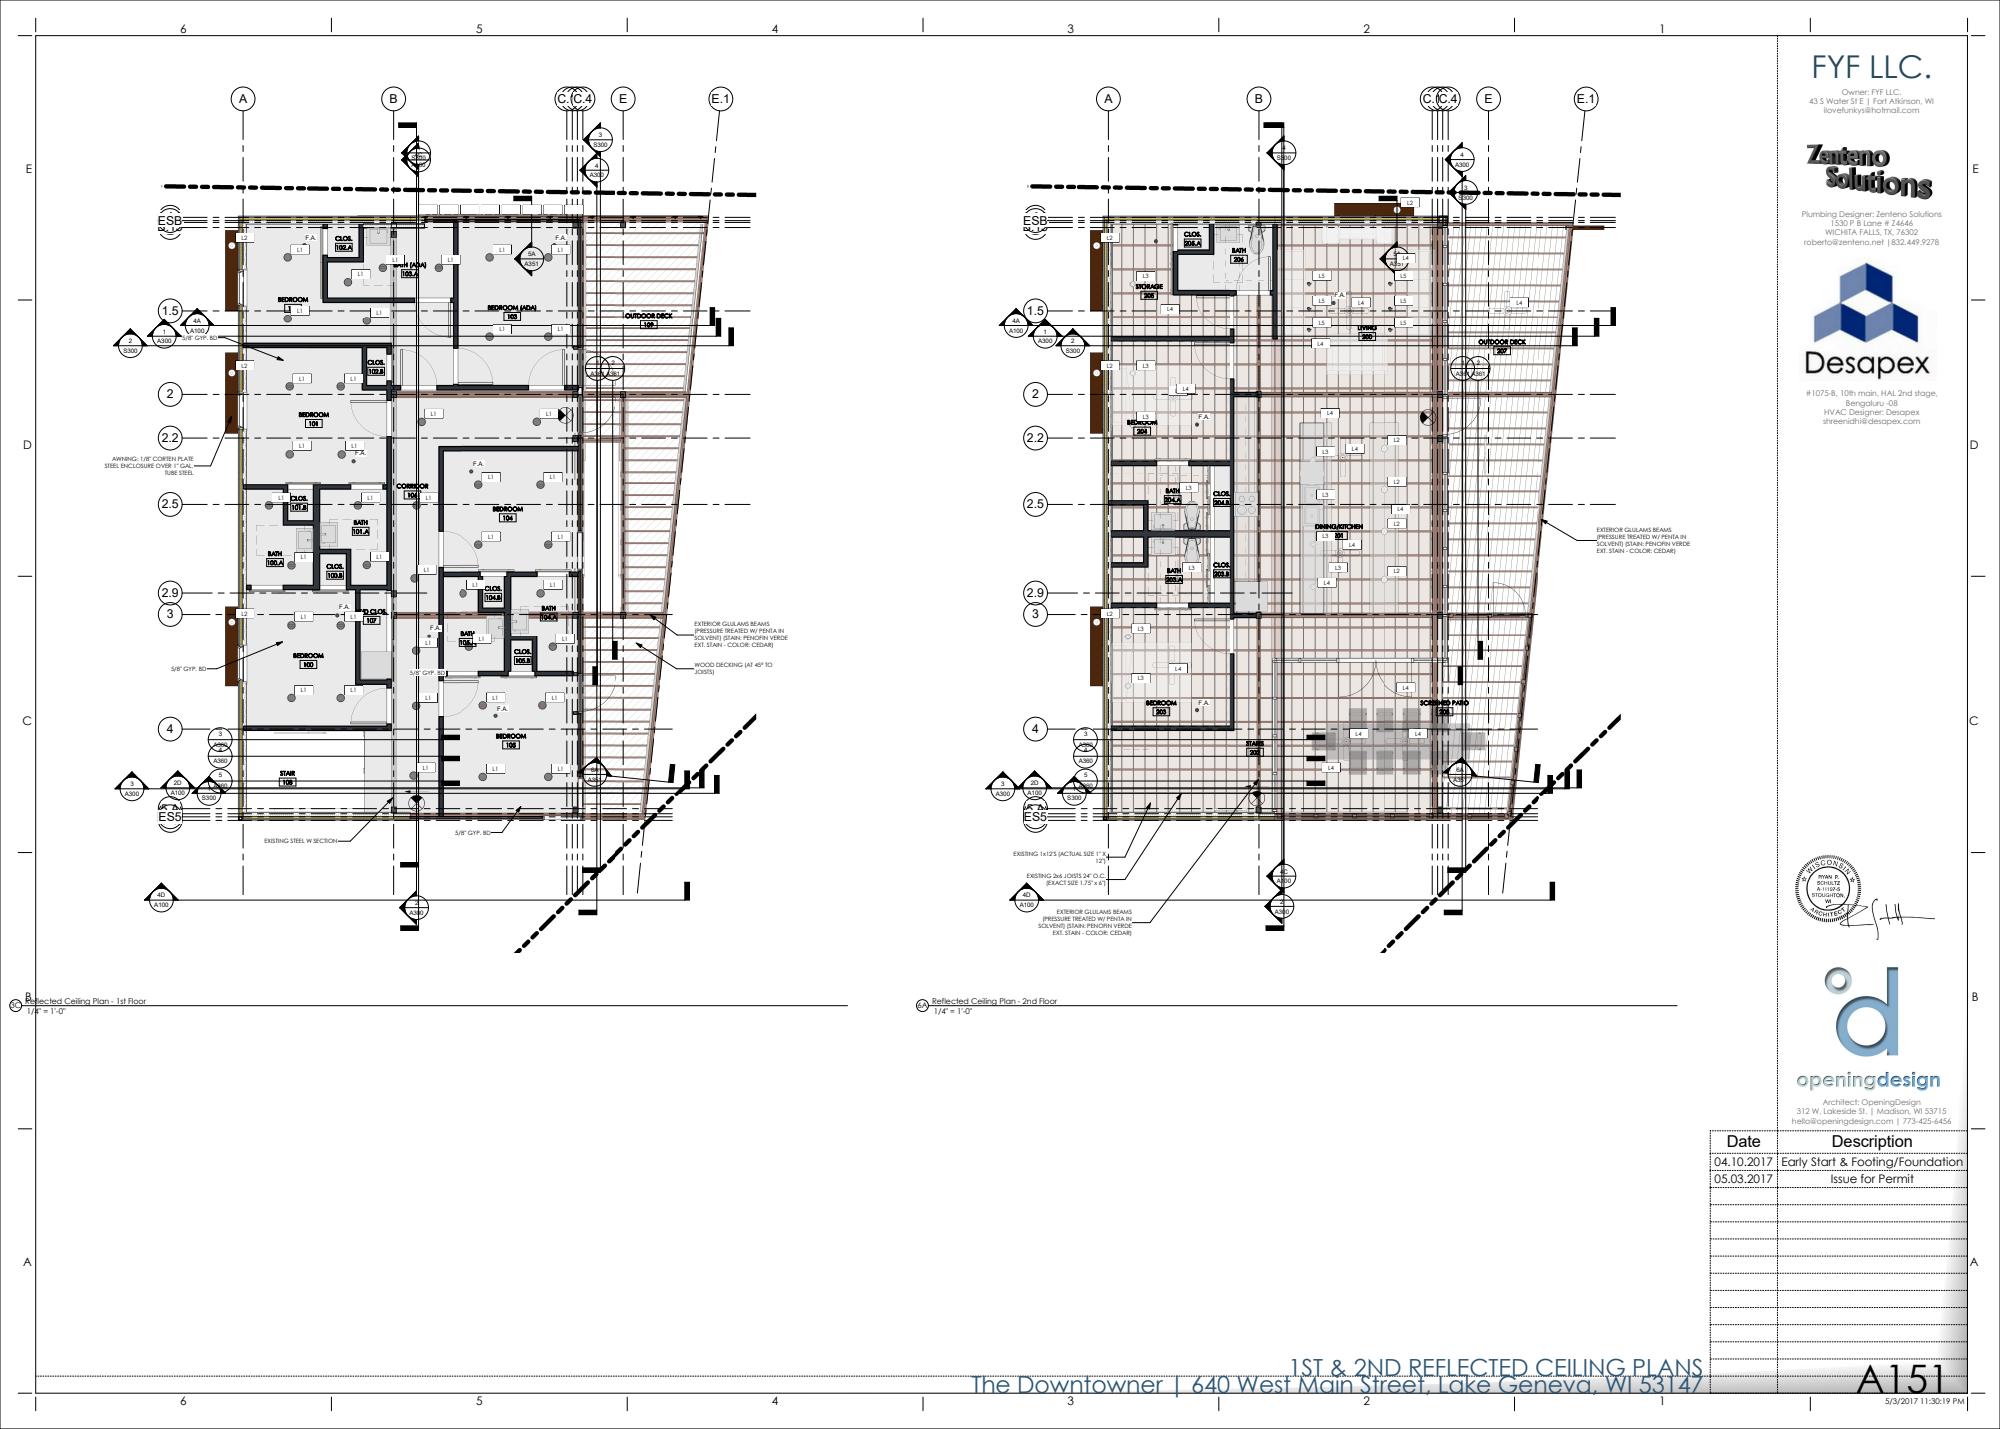
[picture p264: page 1]
BEDROOM; BATH; BATH (ADA); BEDROOM (ADA); CORRIDOR; CLOS.; W/D CLOS.; STAIR; OUTDOOR DECK; ESB; 5/8" GYP. BD; TUBE STEEL; STORAGE; SCREENED PATIO; LIVING; DINING/KITCHEN; STAIRS; EXISTING 2x6 JOISTS 24" O.C. (EXACT SIZE 1.75" x 6"); Architect: OpeningDesign; FYF LLC.; 1/4" = 1'-0" 3C Reflected Ceiling Plan - 1st Floor; 1/4" = 1'-0" 6A Reflected Ceiling Plan - 2nd Floor; Date; Description

Owner: FYF LLC.

43 S Water St E | Fort Atkinson, WI
ilovefunkys@hotmail.com

Plumbing Designer: Zenteno Solutions

1530 P B Lane # Z4646
WICHITA FALLS, TX, 76302
roberto@zenteno.net |832.449.9278

#1075-B, 10th main, HAL 2nd stage,

Bengaluru -08
HVAC Designer: Desapex
shreenidhi@desapex.com

AWNING: 1/8" CORTEN PLATE
STEEL ENCLOSURE OVER 1" GAL.

EXTERIOR GLULAMS BEAMS
(PRESSURE TREATED W/ PENTA IN
SOLVENT) (STAIN: PENOFIN VERDE
EXT. STAIN - COLOR: CEDAR)

WOOD DECKING (AT 45° TO
JOISTS)

EXISTING STEEL W SECTION

EXISTING 1x12'S (ACTUAL SIZE 1" X

312 W. Lakeside St. | Madison, WI 53715
hello@openingdesign.com | 773-425-6456

04.10.2017 Early Start & Footing/Foundation
05.03.2017 Issue for Permit

1ST & 2ND REFLECTED CEILING PLANS The Downtowner | 640 West Main Street, Lake Geneva, WI 53147
