OpeningDesign/Vacation_Rental/Transfer/20170503 ----- ISSUE FOR PERMIT ------/A200 - EXTERIOR ELEVATIONS.pdf

## 2nd Floor

## Existing Roof Joist

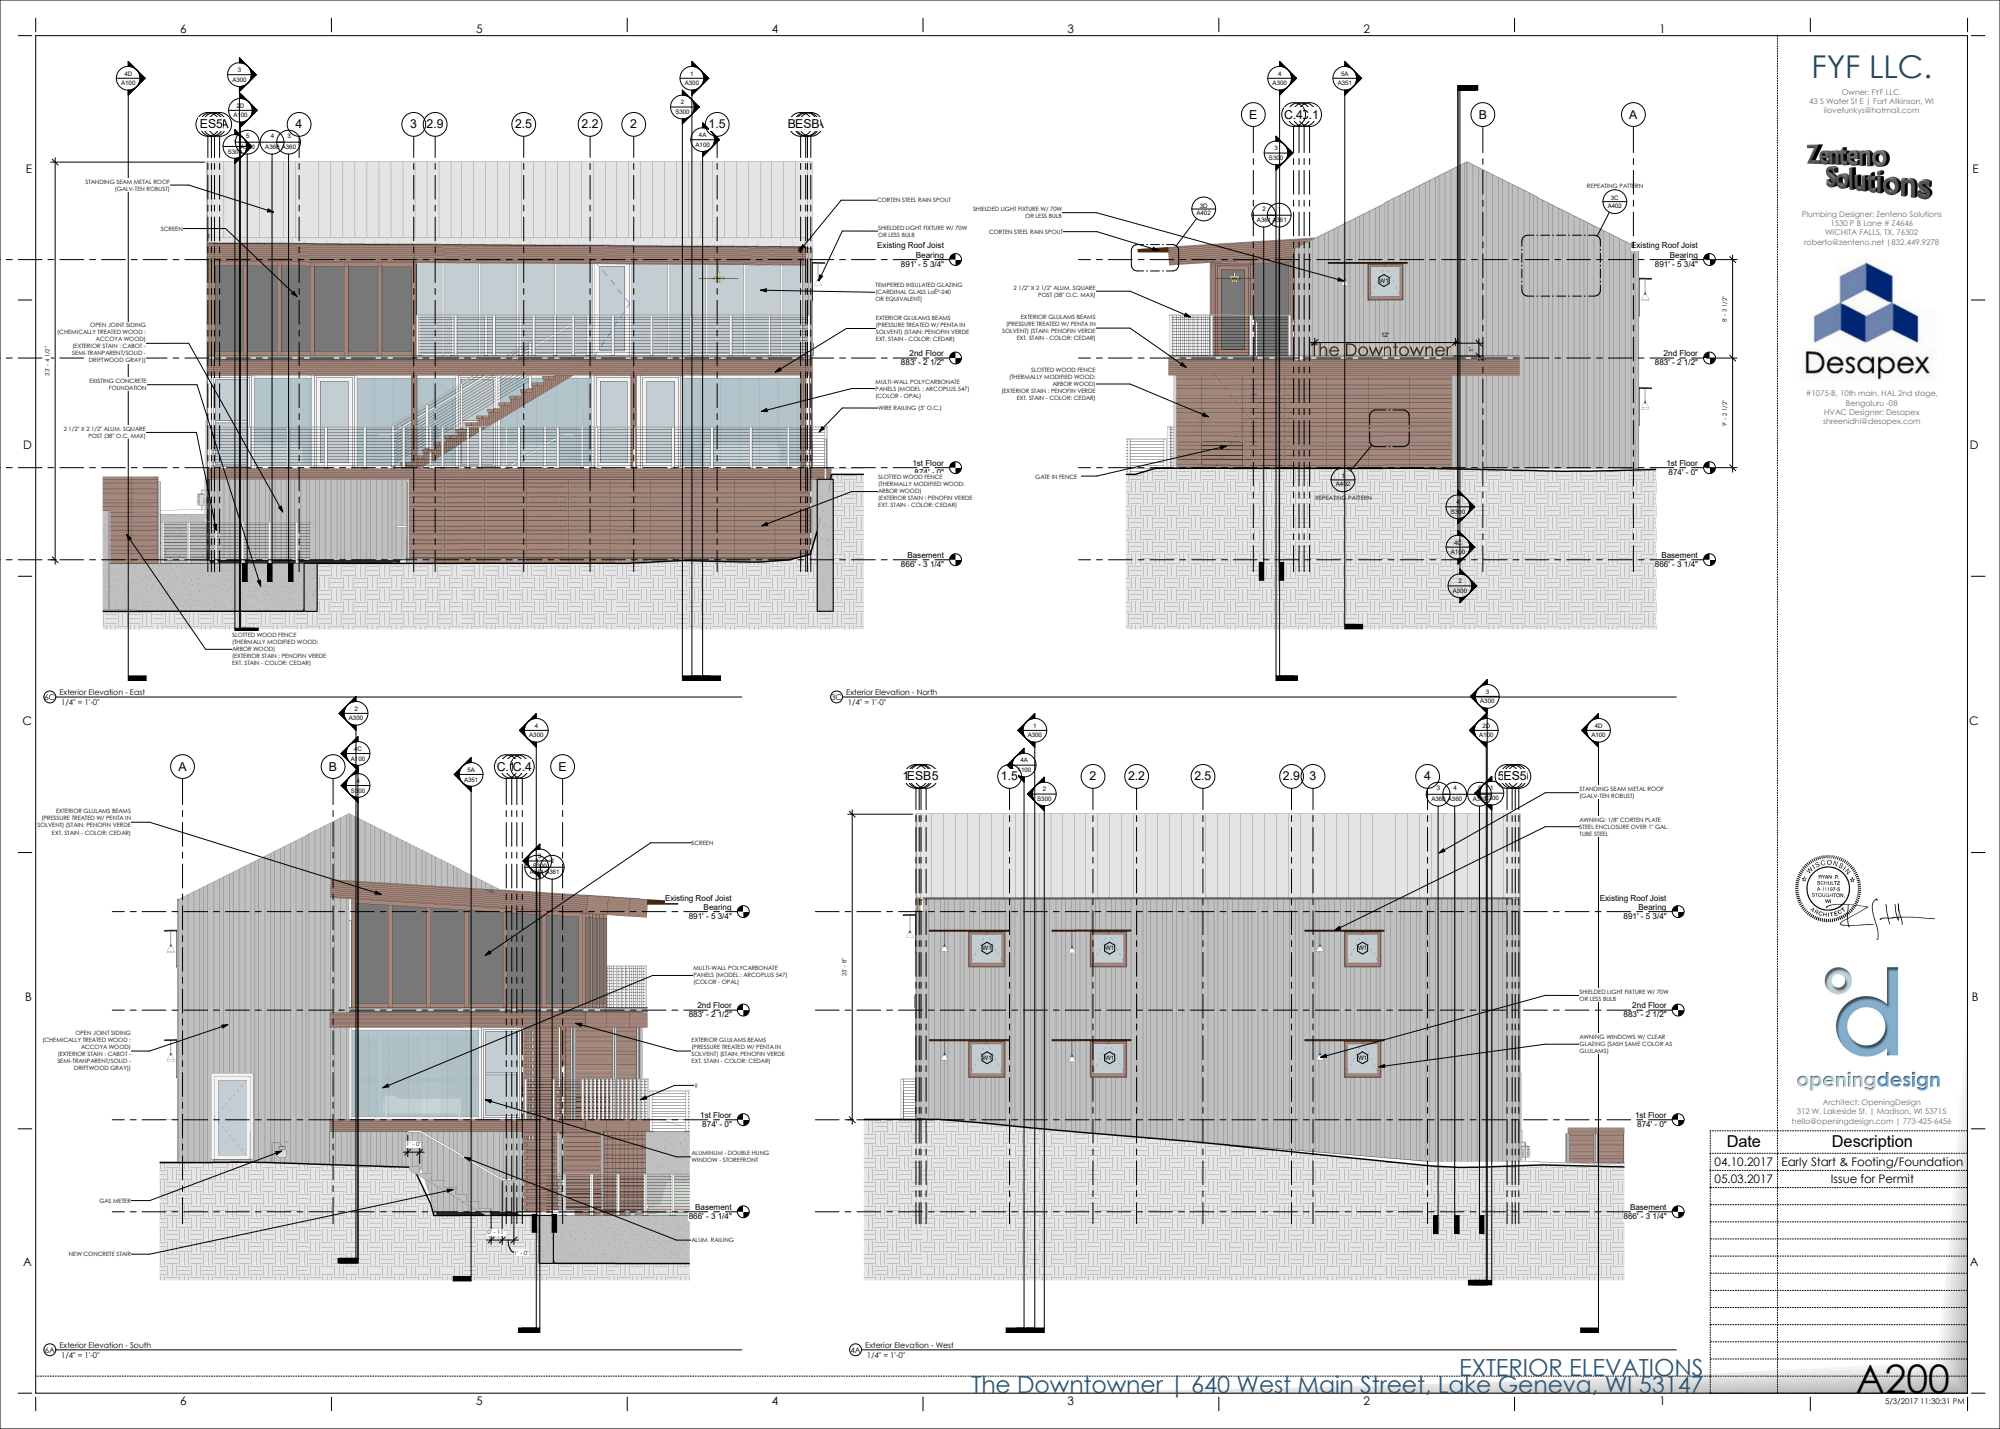
[picture p265: page 1]
1st Floor 874' - 0"; Basement 866' - 3 1/4"; Bearing 891' - 5 3/4"; WIRE RAILING (3" O.C.); SCREEN; ACCOYA WOOD); EXISTING CONCRETE FOUNDATION; 2 1/2" X 2 1/2" ALUM. SQUARE POST (38" O.C. MAX); ESB; 2nd Floor 883' - 2 1/2"; REPEATING PATTERN; ARBOR WOOD); ALUM. RAILING; GAS METER; 1.AAB.15; Architect: OpeningDesign; FYF LLC.; 1/4" = 1'-0" 6C Exterior Elevation - East; 1/4" = 1'-0" 3C Exterior Elevation - North; 1/4" = 1'-0" 6A Exterior Elevation - South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

Owner: FYF LLC.

43 S Water St E | Fort Atkinson, WI
ilovefunkys@hotmail.com

STANDING SEAM METAL ROOF

(GALV-TEN ROBUST)

CORTEN STEEL RAIN SPOUT

SHIELDED LIGHT FIXTURE W/ 70W

OR LESS BULB

Plumbing Designer: Zenteno Solutions

1530 P B Lane # Z4646
WICHITA FALLS, TX, 76302
roberto@zenteno.net |832.449.9278

Existing Roof Joist

TEMPERED INSULATED GLAZING
(CARDINAL GLASS LoĒ²-240
OR EQUIVALENT)

9' - 2 1/2" 8' - 3 1/2" EXTERIOR GLULAMS BEAMS (PRESSURE TREATED W/ PENTA IN SOLVENT) (STAIN: PENOFIN VERDE EXT. STAIN - COLOR: CEDAR)

EXTERIOR GLULAMS BEAMS
(PRESSURE TREATED W/ PENTA IN
SOLVENT) (STAIN: PENOFIN VERDE
EXT. STAIN - COLOR: CEDAR)

OPEN JOINT SIDING

(CHEMICALLY TREATED WOOD :

(EXTERIOR STAIN : CABOT -
SEMI-TRANPARENT/SOLID -
DRIFTWOOD GRAY))

SLOTTED WOOD FENCE

(THERMALLY MODIFIED WOOD:

MULTI-WALL POLYCARBONATE
PANELS (MODEL : ARCOPLUS 547)
(COLOR - OPAL)

(EXTERIOR STAIN : PENOFIN VERDE

#1075-B, 10th main, HAL 2nd stage,

Bengaluru -08
HVAC Designer: Desapex
shreenidhi@desapex.com

ARBOR WOOD)

GATE IN FENCE

AWNING: 1/8" CORTEN PLATE
STEEL ENCLOSURE OVER 1" GAL.
TUBE STEEL

AWNING WINDOWS W/ CLEAR
GLAZING (SASH SAME COLOR AS
GLULAMS)

312 W. Lakeside St. | Madison, WI 53715
hello@openingdesign.com | 773-425-6456

ALUMINUM - DOUBLE HUNG
WINDOW - STOREFRONT

04.10.2017 Early Start & Footing/Foundation
05.03.2017 Issue for Permit

NEW CONCRETE STAIR

EXTERIOR ELEVATIONS The Downtowner | 640 West Main Street, Lake Geneva, WI 53147
