OpeningDesign/Vacation_Rental/Transfer/20170503 ----- ISSUE FOR PERMIT ------/A360 - STAIR SECTIONS.pdf

E

E

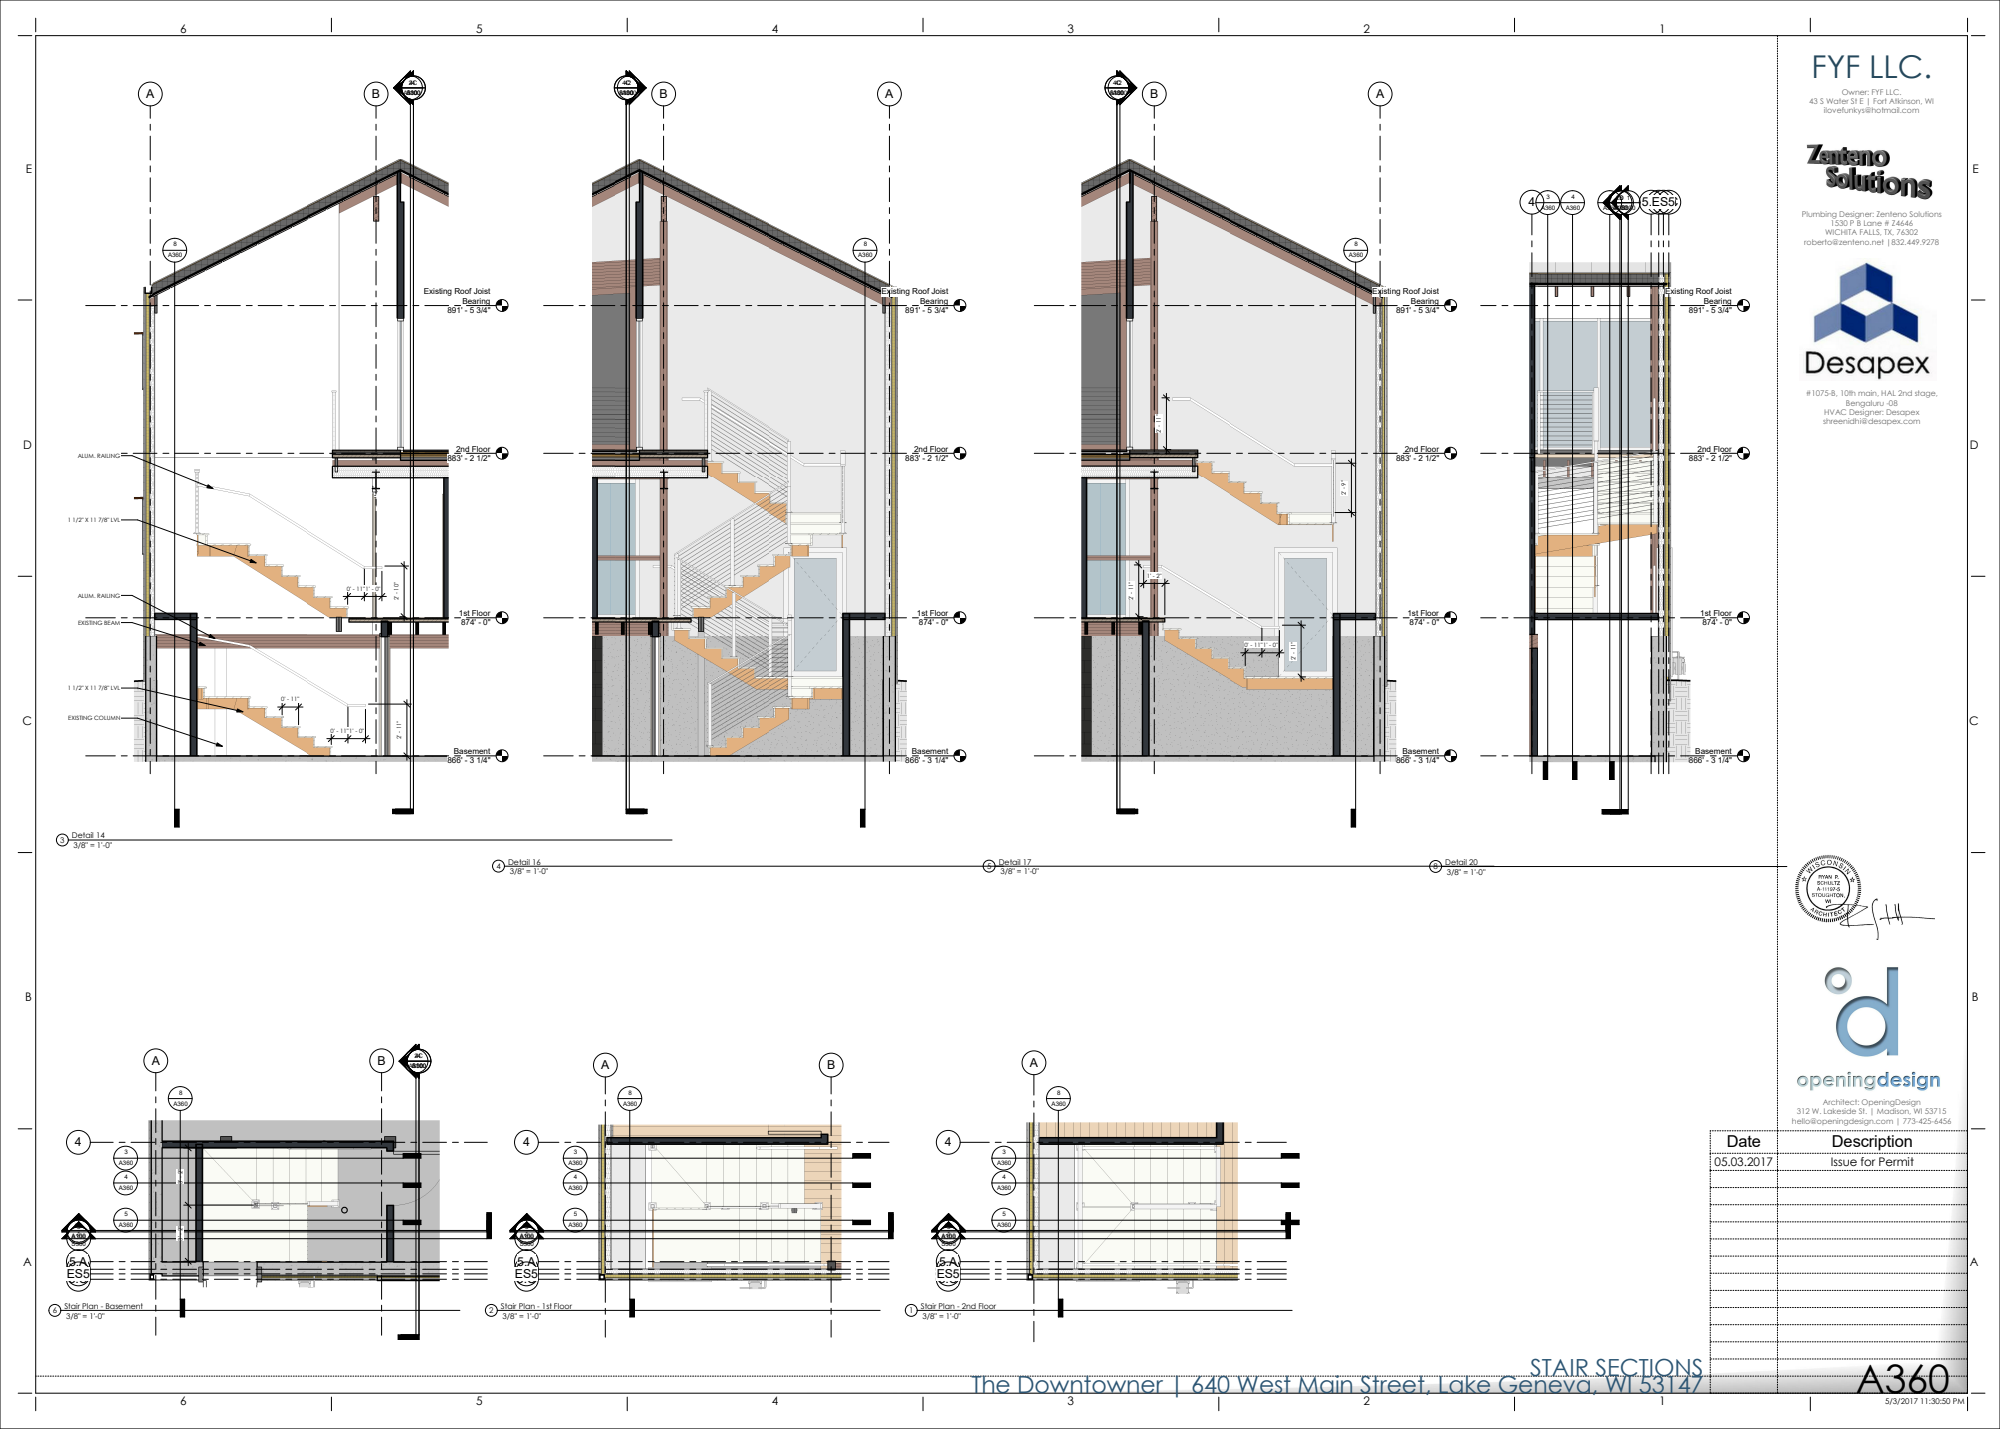
[picture p266: page 1]
1st Floor 874' - 0"; 2nd Floor 883' - 2 1/2"; Basement 866' - 3 1/4"; Bearing 891' - 5 3/4"; ALUM. RAILING; 1 1/2" X 11 7/8" LVL; EXISTING COLUMN; EXISTING BEAM; Architect: OpeningDesign; FYF LLC.; 3/8" = 1'-0" 3 Detail 14; 3/8" = 1'-0" 4 Detail 16; 3/8" = 1'-0" 5 Detail 17; 3/8" = 1'-0" 8 Detail 20; Date; Description

Owner: FYF LLC.

43 S Water St E | Fort Atkinson, WI
ilovefunkys@hotmail.com

Plumbing Designer: Zenteno Solutions

1530 P B Lane # Z4646
WICHITA FALLS, TX, 76302
roberto@zenteno.net |832.449.9278

Existing Roof Joist

#1075-B, 10th main, HAL 2nd stage,

Bengaluru -08
HVAC Designer: Desapex
shreenidhi@desapex.com

312 W. Lakeside St. | Madison, WI 53715
hello@openingdesign.com | 773-425-6456

05.03.2017 Issue for Permit

3/8" = 1'-0" 6 Stair Plan - Basement

3/8" = 1'-0" 1 Stair Plan - 2nd Floor 3/8" = 1'-0" 2 Stair Plan - 1st Floor

STAIR SECTIONS The Downtowner | 640 West Main Street, Lake Geneva, WI 53147
