OpeningDesign/Vacation_Rental/Transfer/20170503 ----- ISSUE FOR PERMIT ------/A361 - STAIR SECTIONS.pdf

## Existing Roof Joist Bearing

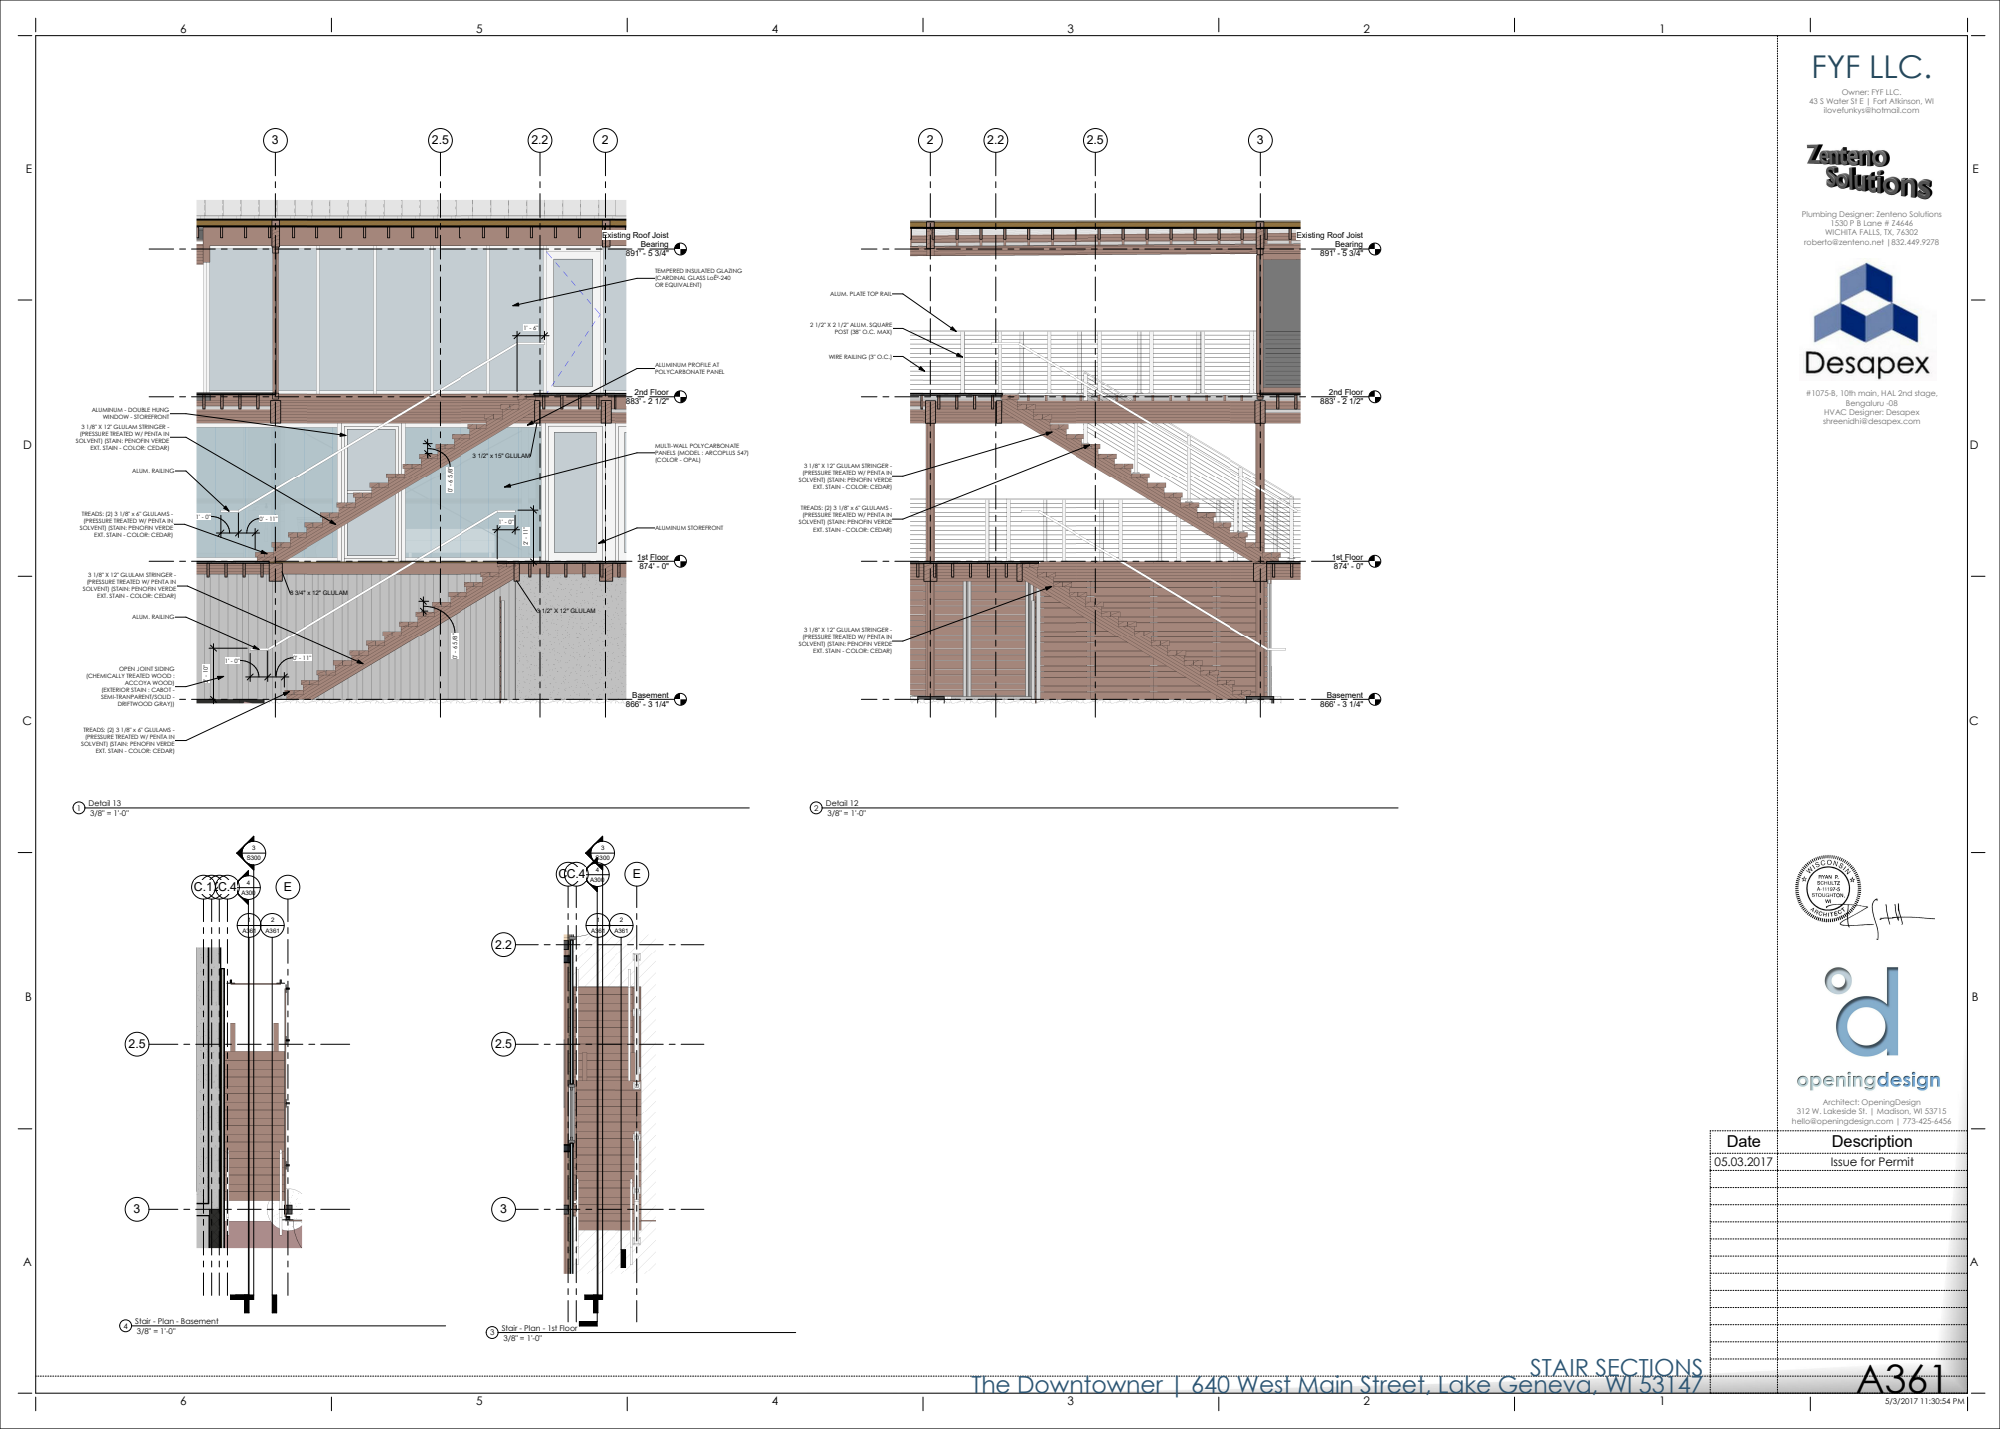
[picture p267: page 1]
1st Floor 874' - 0"; 2nd Floor 883' - 2 1/2"; Basement 866' - 3 1/4"; ALUM. RAILING; 3 1/2" x 15" GLULAM; 3 1/2" X 12" GLULAM; 8 3/4" x 12" GLULAM; ALUMINUM STOREFRONT; ACCOYA WOOD); Bearing 891' - 5 3/4"; 2 1/2" X 2 1/2" ALUM. SQUARE POST (38" O.C. MAX); WIRE RAILING (3" O.C.); Architect: OpeningDesign; FYF LLC.; Date; Description; 3/8" = 1'-0" 1 Detail 13; 3/8" = 1'-0" 2 Detail 12

Owner: FYF LLC.

43 S Water St E | Fort Atkinson, WI
ilovefunkys@hotmail.com

Plumbing Designer: Zenteno Solutions

1530 P B Lane # Z4646
WICHITA FALLS, TX, 76302
roberto@zenteno.net |832.449.9278

Existing Roof Joist

TEMPERED INSULATED GLAZING
(CARDINAL GLASS LoĒ²-240
OR EQUIVALENT)

ALUM. PLATE TOP RAIL

ALUMINUM PROFILE AT
POLYCARBONATE PANEL

#1075-B, 10th main, HAL 2nd stage,

Bengaluru -08
HVAC Designer: Desapex
shreenidhi@desapex.com

ALUMINUM - DOUBLE HUNG
WINDOW - STOREFRONT

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

MULTI-WALL POLYCARBONATE
PANELS (MODEL : ARCOPLUS 547)
(COLOR - OPAL)

TREADS: (2) 3 1/8" x 6" GLULAMS -

OPEN JOINT SIDING

(CHEMICALLY TREATED WOOD :

(EXTERIOR STAIN : CABOT -
SEMI-TRANPARENT/SOLID -
DRIFTWOOD GRAY))

312 W. Lakeside St. | Madison, WI 53715
hello@openingdesign.com | 773-425-6456

05.03.2017 Issue for Permit

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

STAIR SECTIONS The Downtowner | 640 West Main Street, Lake Geneva, WI 53147
