OpeningDesign/Vacation_Rental/Transfer/20170503 ----- ISSUE FOR PERMIT ------/P1-02 - SECOND FLOOR AND ROOF PLUMING PLANS.pdf

B

C.3 E

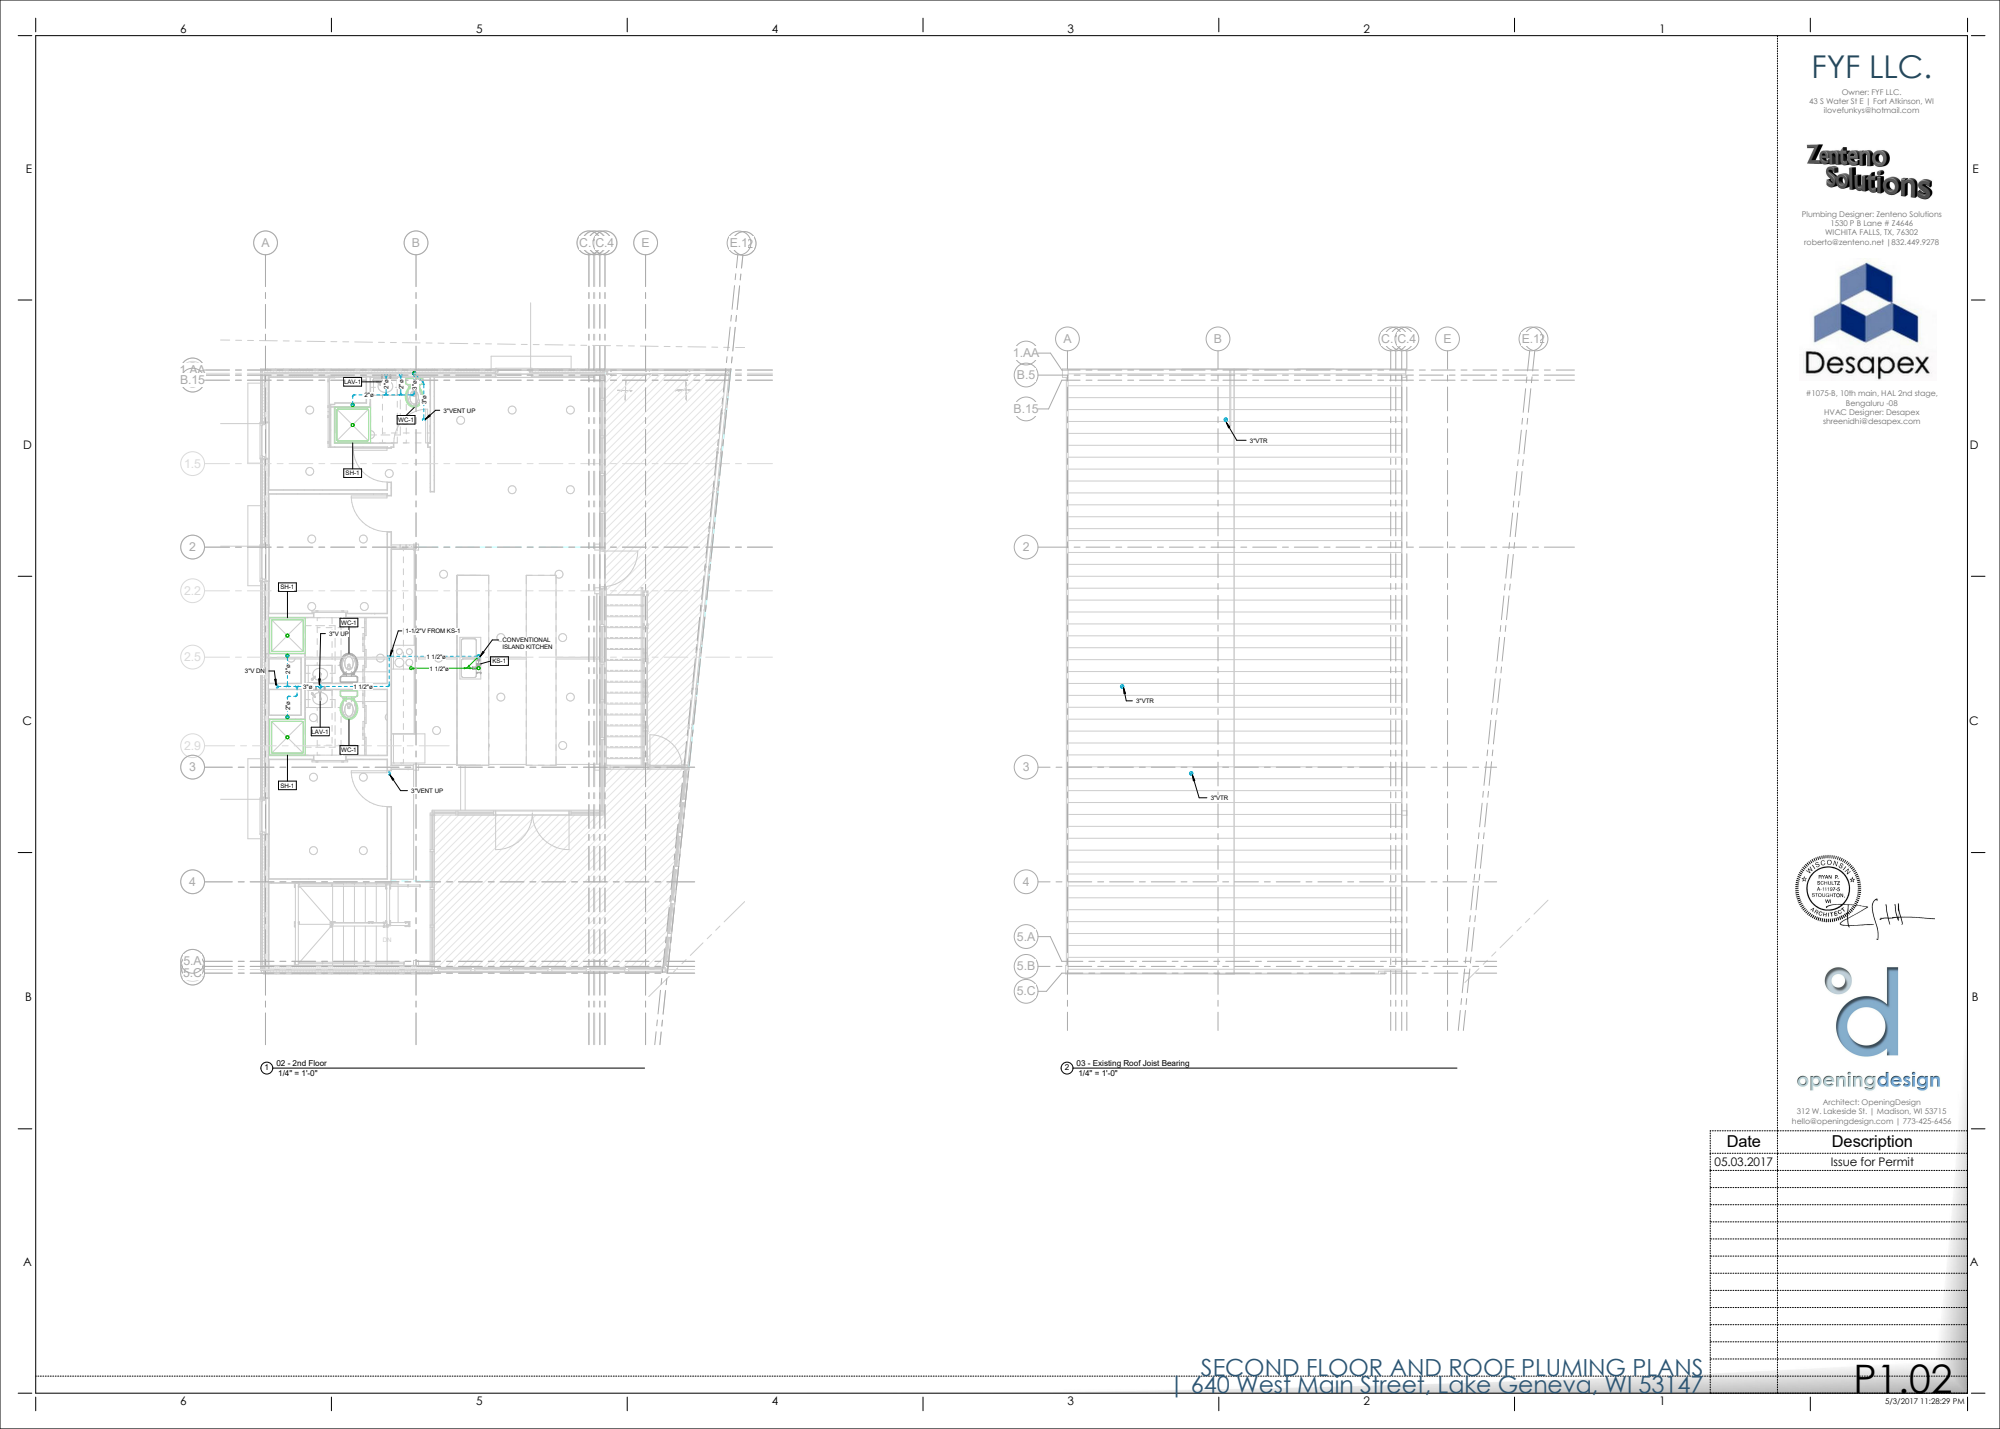
[picture p268: page 1]
ESB; LAV-1; 3"VENT UP; CONVENTIONAL ISLAND KITCHEN; 1-1/2"V FROM KS-1; 3"VTR; Architect: OpeningDesign; FYF LLC.; 1/4" = 1'-0" 1 02 - 2nd Floor; 1/4" = 1'-0" 2 03 - Existing Roof Joist Bearing; Date; Description

Owner: FYF LLC.

43 S Water St E | Fort Atkinson, WI
ilovefunkys@hotmail.com

Plumbing Designer: Zenteno Solutions

1530 P B Lane # Z4646
WICHITA FALLS, TX, 76302
roberto@zenteno.net |832.449.9278

#1075-B, 10th main, HAL 2nd stage,

Bengaluru -08
HVAC Designer: Desapex
shreenidhi@desapex.com

312 W. Lakeside St. | Madison, WI 53715
hello@openingdesign.com | 773-425-6456

05.03.2017 Issue for Permit

SECOND FLOOR AND ROOF PLUMING PLANS | 640 West Main Street, Lake Geneva, WI 53147
