OpeningDesign/Vacation_Rental/Transfer/20170503 ----- ISSUE FOR PERMIT ------/S400 - BRACING ELEVATION.pdf

E

E

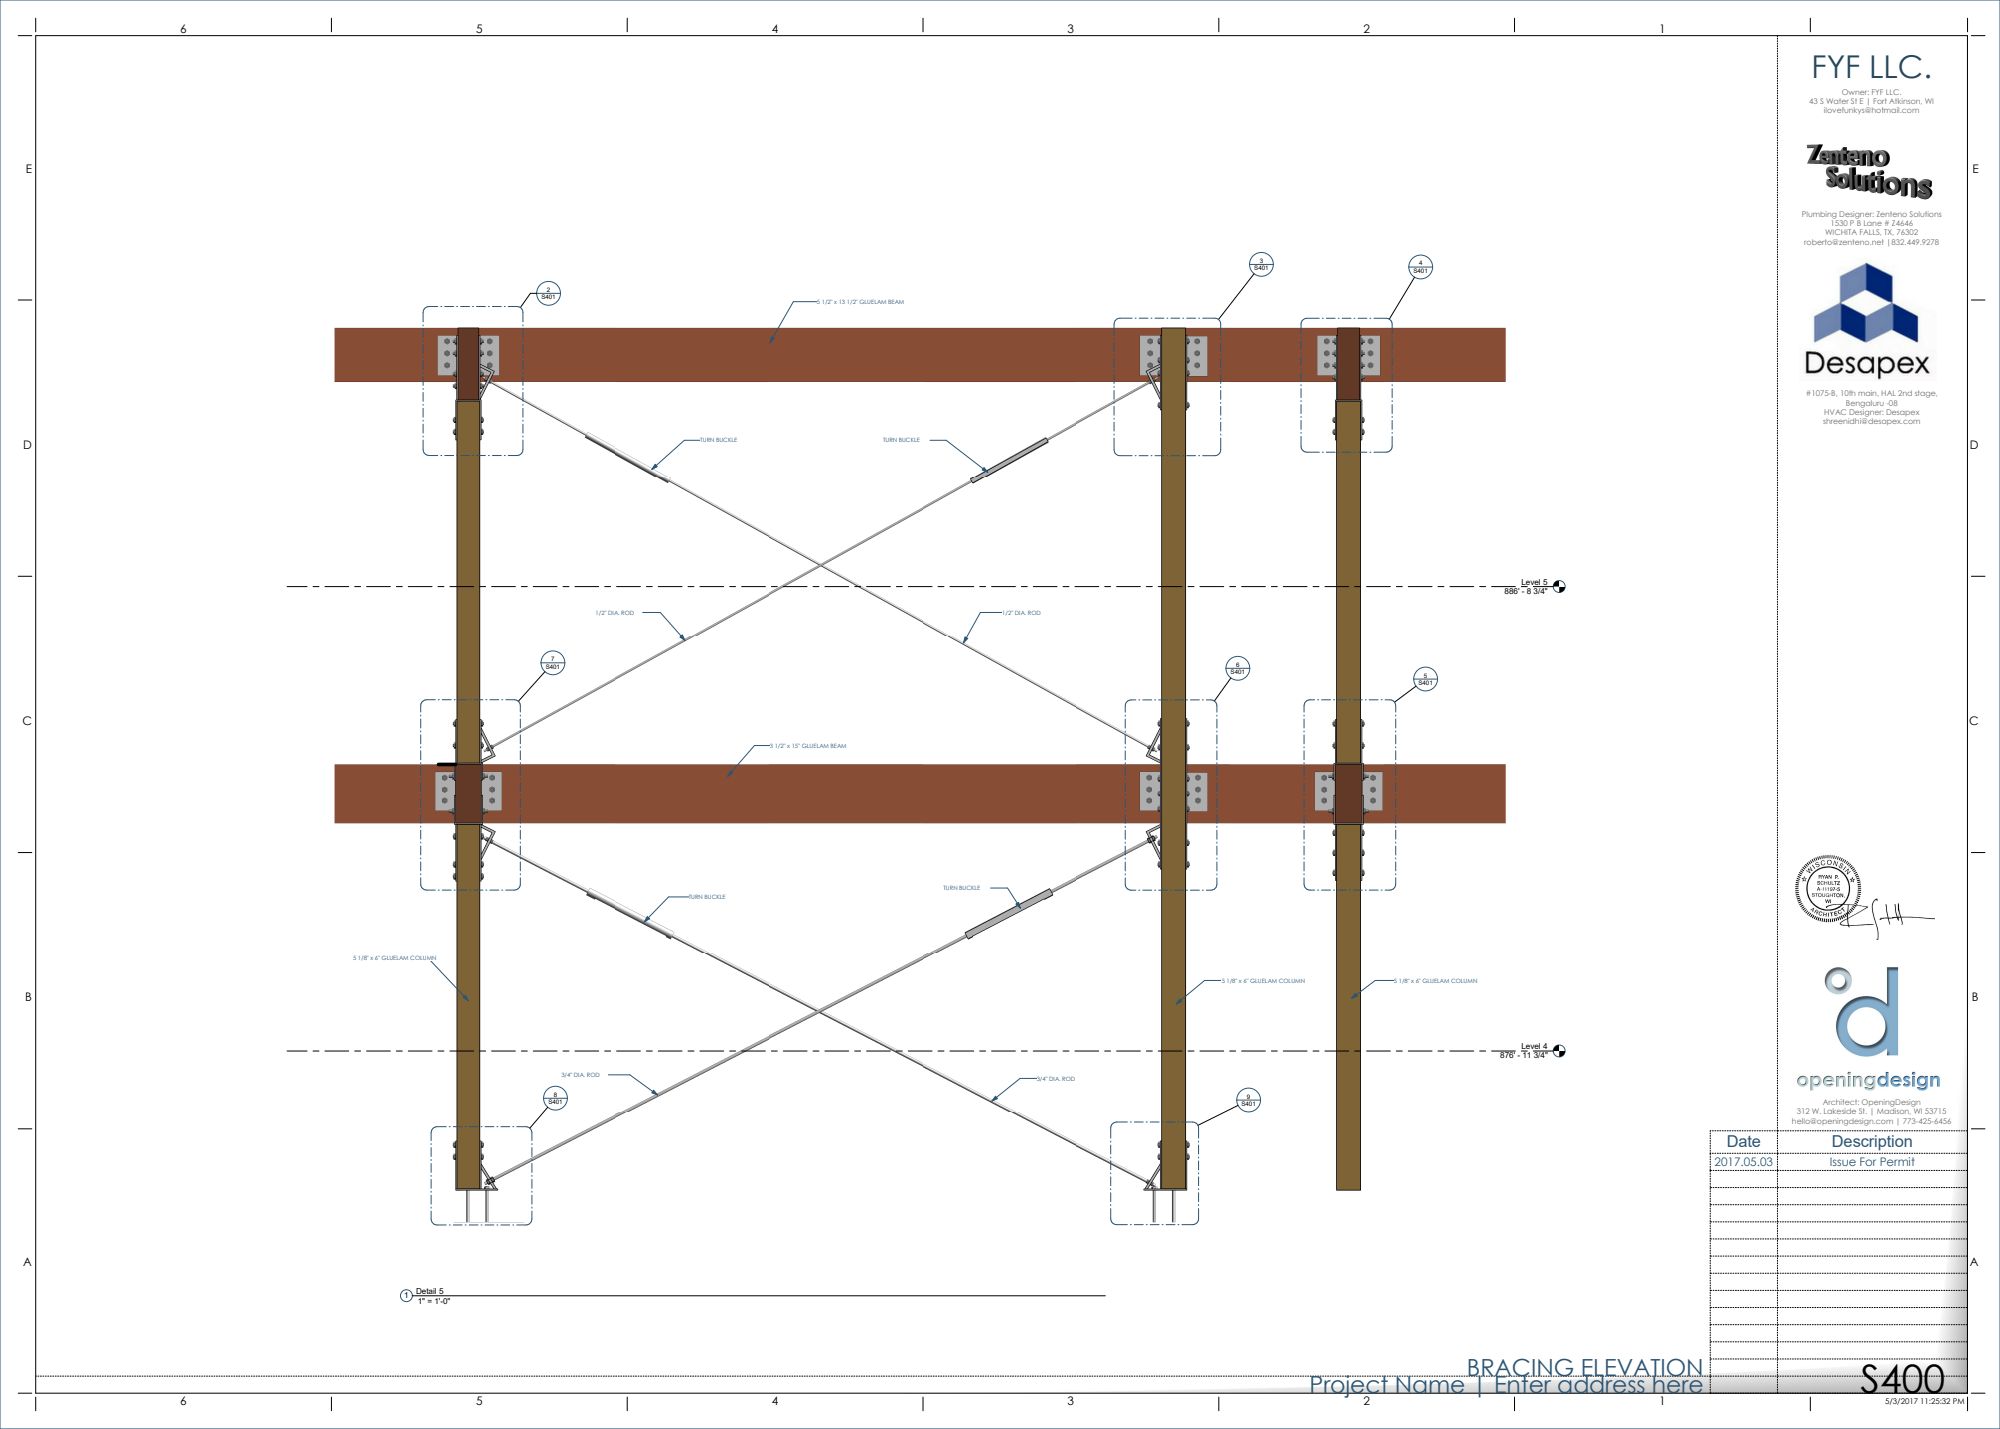
[picture p269: page 1]
Level 4 876' - 11 3/4"; Level 5 886' - 8 3/4"; TURN BUCKLE; 1/2" DIA. ROD; 5 1/8" x 6" GLUELAM COLUMN; 3 1/2" x 15" GLUELAM BEAM; 5 1/2" x 13 1/2" GLUELAM BEAM; Architect: OpeningDesign; FYF LLC.; 1" = 1'-0" 1 Detail 5; Date; Description

Owner: FYF LLC.

43 S Water St E | Fort Atkinson, WI
ilovefunkys@hotmail.com

Plumbing Designer: Zenteno Solutions

1530 P B Lane # Z4646
WICHITA FALLS, TX, 76302
roberto@zenteno.net |832.449.9278

#1075-B, 10th main, HAL 2nd stage,

Bengaluru -08
HVAC Designer: Desapex
shreenidhi@desapex.com

3/4" DIA. ROD

312 W. Lakeside St. | Madison, WI 53715
hello@openingdesign.com | 773-425-6456

2017.05.03 Issue For Permit

S400 BRACING ELEVATION Project Name | Enter address here
