OpeningDesign/Vacation_Rental/Transfer/20170503 ----- ISSUE FOR PERMIT ------/S401 - BRACING DETAILS.pdf

E

E

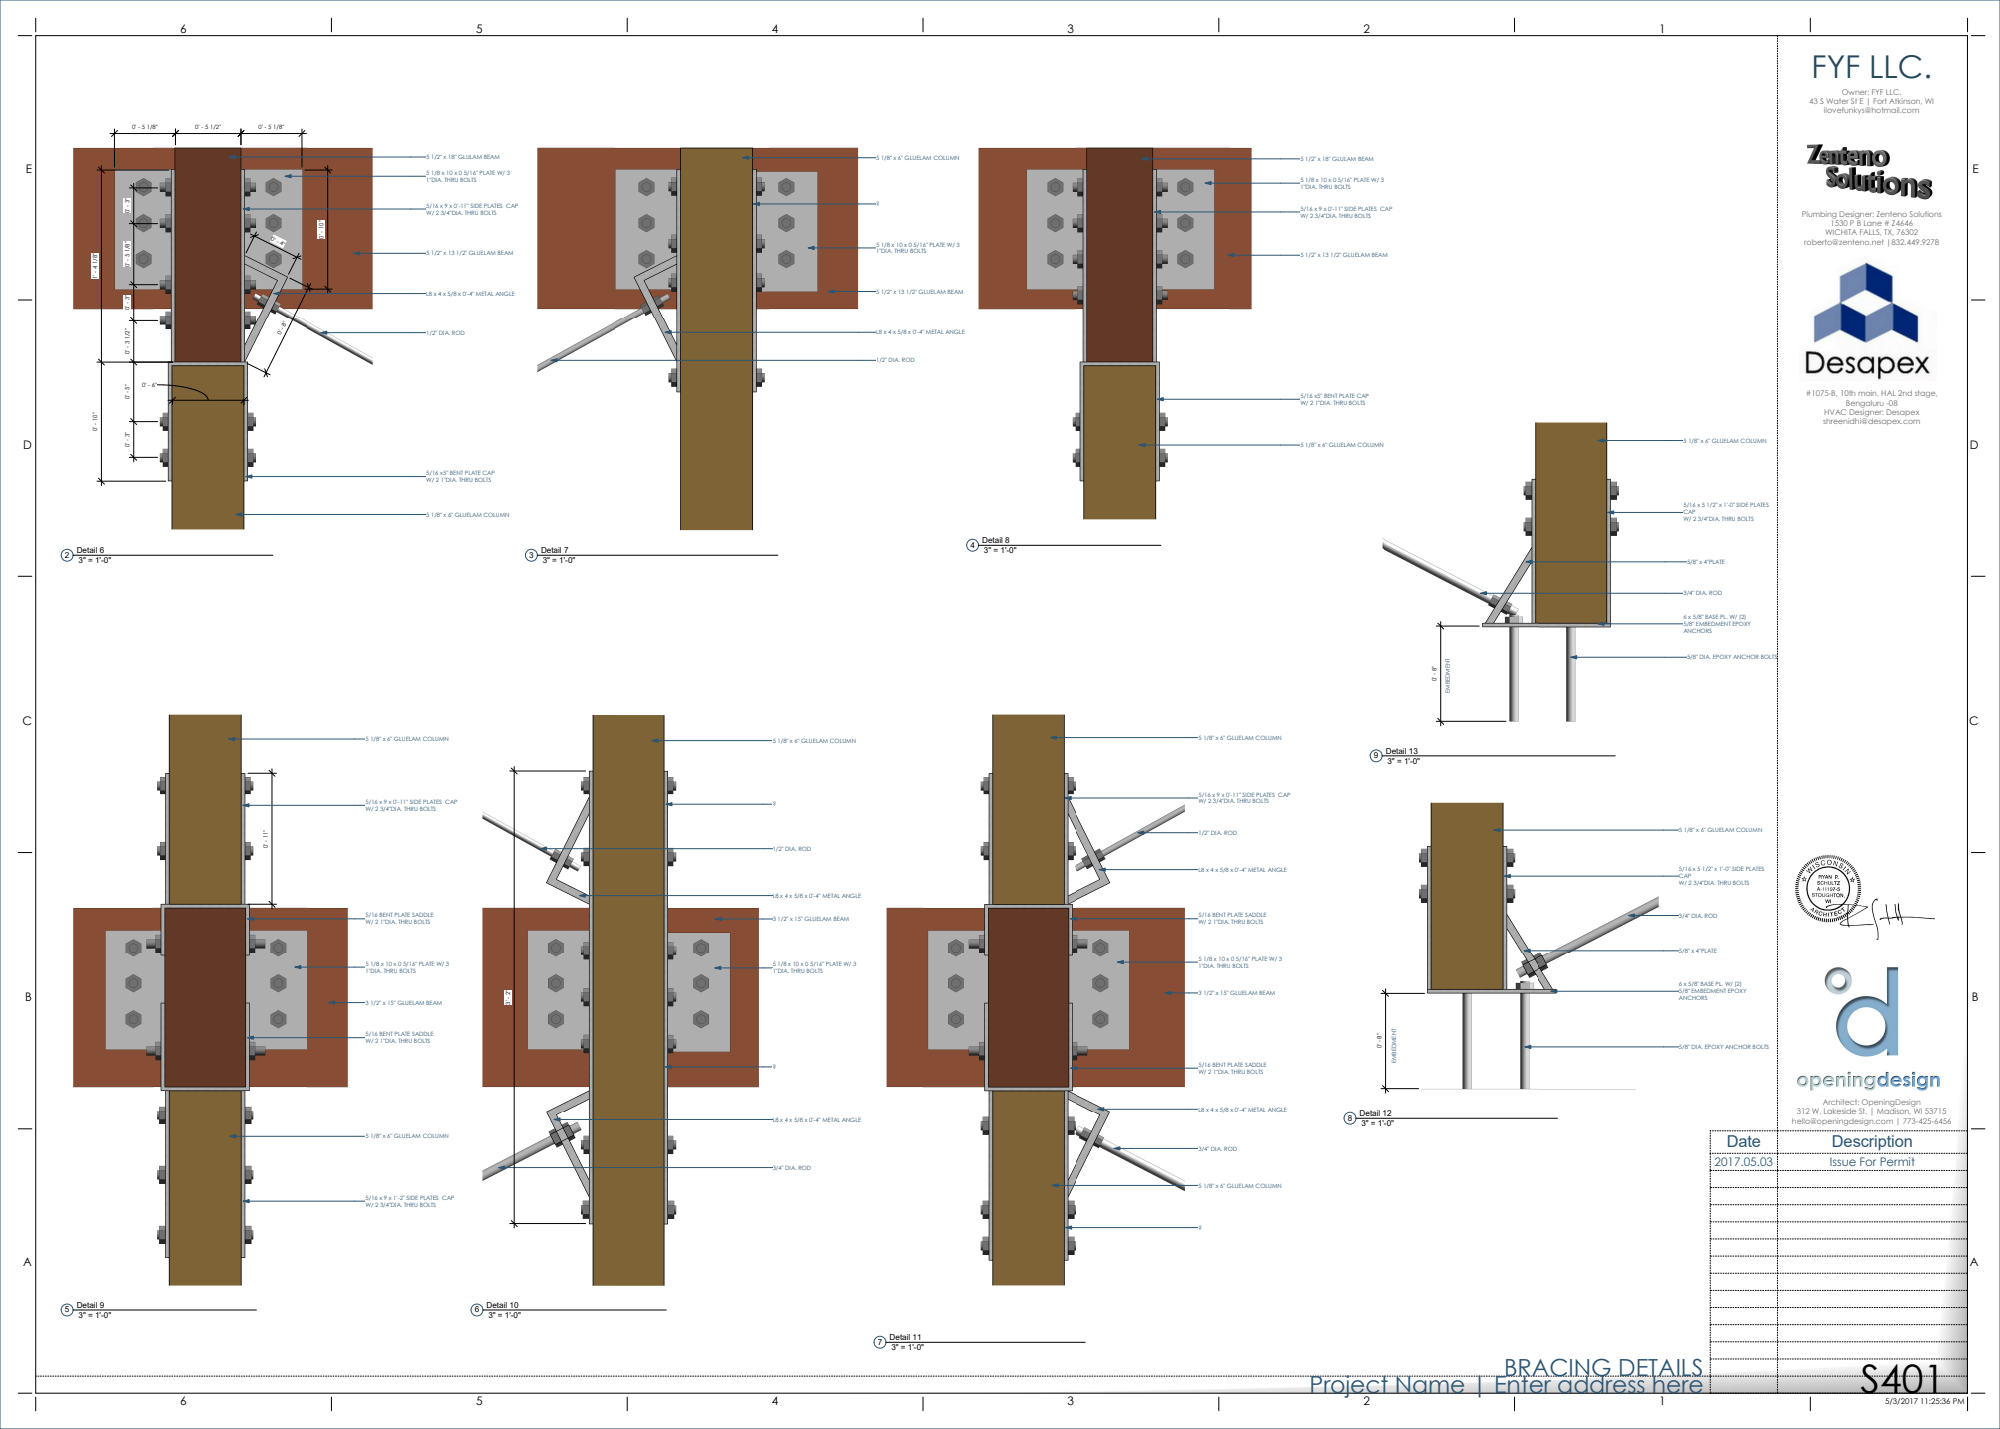
[picture p270: page 1]
5 1/8" x 6" GLUELAM COLUMN; L8 x 4 x 5/8 x 0'-4" METAL ANGLE; 1/2" DIA. ROD; 5 1/2" x 13 1/2" GLUELAM BEAM; 5 1/2" x 18" GLULAM BEAM; 3 1/2" x 15" GLUELAM BEAM; 3/4" DIA. ROD; 6 x 5/8" BASE PL. W/ (2) 5/8" EMBEDMENT EPOXY ANCHORS; 5/8" x 4"PLATE; EMBEDMENT; Architect: OpeningDesign; FYF LLC.; BRACING DETAILS; Detail 6; Detail 7; Detail 8; Detail 9; Detail 10; Detail 11; Detail 12; Detail 13; Date; Description

Owner: FYF LLC.

43 S Water St E | Fort Atkinson, WI
ilovefunkys@hotmail.com

5 1/8 x 10 x 0 5/16" PLATE W/ 3
1"DIA. THRU BOLTS

5/16 x 9 x 0'-11" SIDE PLATES CAP
W/ 2 3/4"DIA. THRU BOLTS

Plumbing Designer: Zenteno Solutions

1530 P B Lane # Z4646
WICHITA FALLS, TX, 76302
roberto@zenteno.net |832.449.9278

5/16 x5" BENT PLATE CAP
W/ 2 1"DIA. THRU BOLTS

#1075-B, 10th main, HAL 2nd stage,

Bengaluru -08
HVAC Designer: Desapex
shreenidhi@desapex.com

5/16 x 5 1/2" x 1'-0" SIDE PLATES
CAP

5/8" DIA. EPOXY ANCHOR BOLTS

5/16 BENT PLATE SADDLE

312 W. Lakeside St. | Madison, WI 53715
hello@openingdesign.com | 773-425-6456

2017.05.03 Issue For Permit

5/16 x 9 x 1'-2" SIDE PLATES CAP

Project Name | Enter address here
