OpeningDesign/Vacation_Rental/Transfer/20170925 - Custom Hardware - Question to Kurt/The Downtowner_ARCH_Exterior Details.pdf

E

E

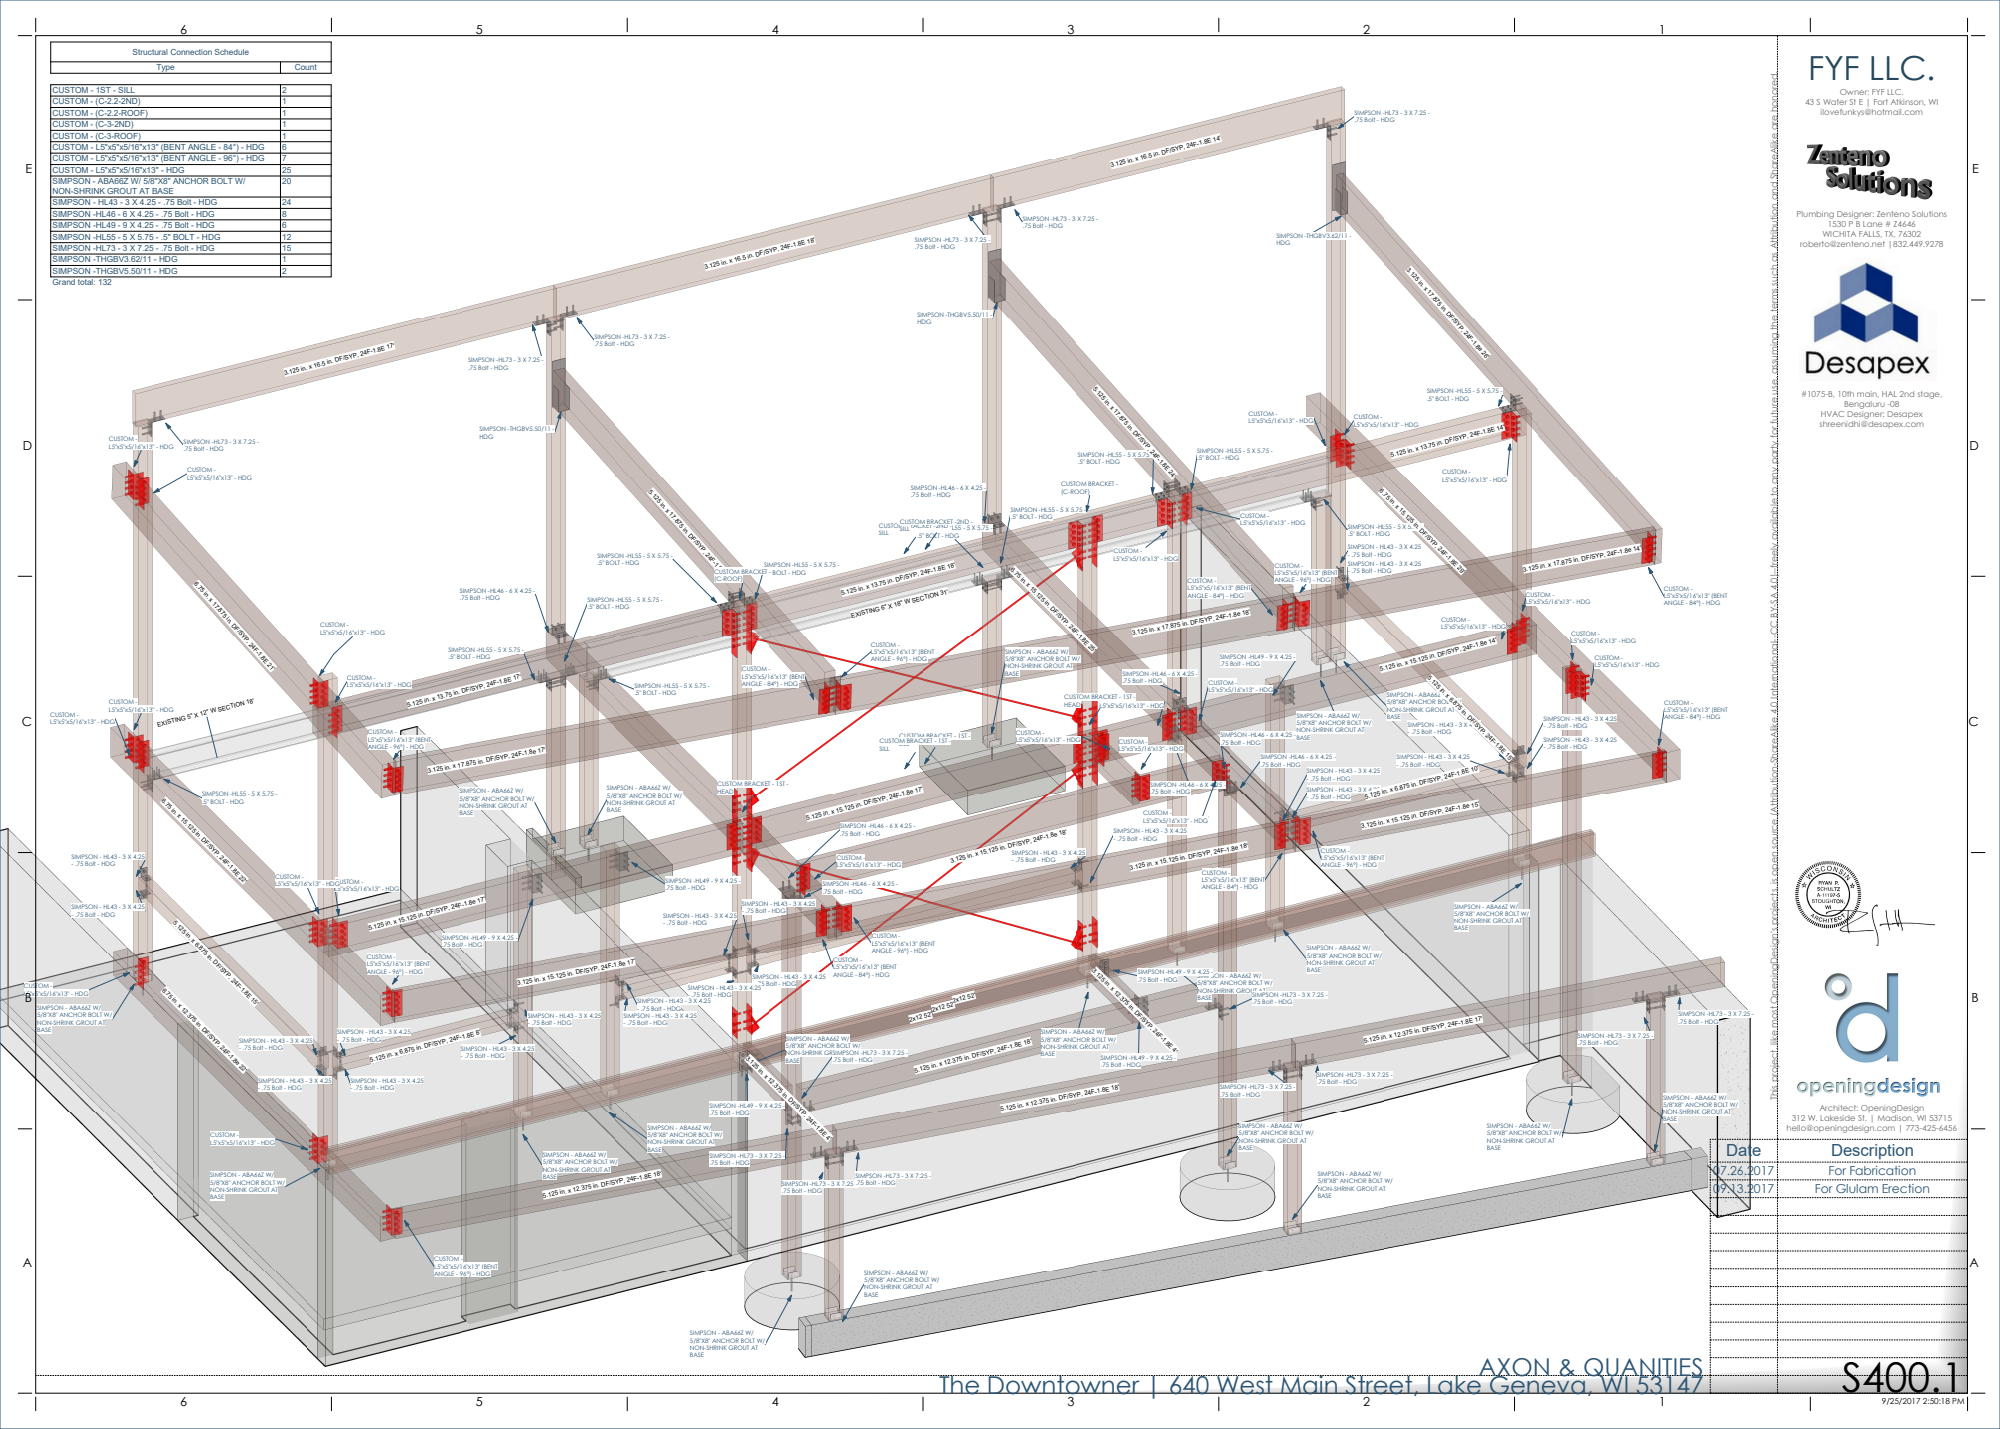
[picture p271: page 1]
CUSTOM - L5"x5"x5/16"x13" (BENT ANGLE - 84°) - HDG; CUSTOM - L5"x5"x5/16"x13" (BENT ANGLE - 96°) - HDG; CUSTOM - L5"x5"x5/16"x13" - HDG; SIMPSON -HL55 - 5 X 5.75 - .5" BOLT - HDG; SIMPSON -HL73 - 3 X 7.25 - .75 Bolt - HDG; SIMPSON - HL43 - 3 X 4.25 - .75 Bolt - HDG; SIMPSON - HL43 - 3 X 4.25 - .75 Bolt - HDG SIMPSON - HL43 - 3 X 4.25 - .75 Bolt - HDG SIMPSON - HL43 - 3 X 4.25 - .75 Bolt - HDG; SIMPSON -HL49 - 9 X 4.25 - .75 Bolt - HDG; SIMPSON - ABA66Z W/; BASE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

Structural Connection Schedule

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

CUSTOM - 1ST - SILL | 2
CUSTOM - (C-2.2-2ND) | 1
CUSTOM - (C-2.2-ROOF) | 1
CUSTOM - (C-3-2ND) | 1
CUSTOM - (C-3-ROOF) | 1
CUSTOM - L5"x5"x5/16"x13" (BENT ANGLE - 84°) - HDG | 6
CUSTOM - L5"x5"x5/16"x13" (BENT ANGLE - 96°) - HDG | 7
CUSTOM - L5"x5"x5/16"x13" - HDG | 25
SIMPSON - ABA66Z W/ 5/8"X8" ANCHOR BOLT W/ NON-SHRINK GROUT AT BASE | 20

Owner: FYF LLC.

43 S Water St E | Fort Atkinson, WI
ilovefunkys@hotmail.com

3.125 in. x 16.5 in. DF/SYP, 24F-1.8E 17' 3.125 in. x 16.5 in. DF/SYP, 24F-1.8E 18' 3.125 in. x 16.5 in. DF/SYP, 24F-1.8E 14'

SIMPSON - HL43 - 3 X 4.25 - .75 Bolt - HDG | 24
SIMPSON -HL46 - 6 X 4.25 - .75 Bolt - HDG | 8
SIMPSON -HL49 - 9 X 4.25 - .75 Bolt - HDG | 6
SIMPSON -HL55 - 5 X 5.75 - .5" BOLT - HDG | 12
SIMPSON -HL73 - 3 X 7.25 - .75 Bolt - HDG | 15
SIMPSON -THGBV3.62/11 - HDG | 1
SIMPSON -THGBV5.50/11 - HDG | 2

Plumbing Designer: Zenteno Solutions

1530 P B Lane # Z4646
WICHITA FALLS, TX, 76302
roberto@zenteno.net |832.449.9278

3.125 in. x 17.875 in. DF/SYP, 24F-1.8e 26'

5.125 in. x 17.875 in. DF/SYP, 24F-1.8E 24'

#1075-B, 10th main, HAL 2nd stage,

Bengaluru -08
HVAC Designer: Desapex
shreenidhi@desapex.com

5.125 in. x 13.75 in. DF/SYP, 24F-1.8E 18' 5.125 in. x 13.75 in. DF/SYP, 24F-1.8E 14'

5.125 in. x 17.875 in. DF/SYP, 24F-1.8E 23'

6.75 in. x 15.125 in. DF/SYP, 24F-1.8E 29'

3.125 in. x 17.875 in. DF/SYP, 24F-1.8e 14'

6.75 in. x 15.125 in. DF/SYP, 24F-1.8E 25'

6.75 in. x 17.875 in. DF/SYP, 24F-1.8E 21'

3.125 in. x 17.875 in. DF/SYP, 24F-1.8e 18'

5.125 in. x 15.125 in. DF/SYP, 24F-1.8e 14'

SIMPSON - ABA66Z W/
5/8"X8" ANCHOR BOLT W/
NON-SHRINK GROUT AT
BASE

5.125 in. x 13.75 in. DF/SYP, 24F-1.8E 17'

5.125 in. x 6.875 in. DF/SYP, 24F-1.8E 15'

3.125 in. x 17.875 in. DF/SYP, 24F-1.8e 17'

5.125 in. x 6.875 in. DF/SYP, 24F-1.8E 10'

5.125 in. x 15.125 in. DF/SYP, 24F-1.8e 17'

6.75 in. x 15.125 in. DF/SYP, 24F-1.8E 22'

3.125 in. x 15.125 in. DF/SYP, 24F-1.8e 15'

3.125 in. x 15.125 in. DF/SYP, 24F-1.8e 18'

3.125 in. x 15.125 in. DF/SYP, 24F-1.8e 17'

3.125 in. x 12.375 in. DF/SYP, 24F-1.8E 4'

6.75 in. x 12.375 in. DF/SYP, 24F-1.8e 22'

5.125 in. x 12.375 in. DF/SYP, 24F-1.8E 17' 5.125 in. x 12.375 in. DF/SYP, 24F-1.8E 18'

5.125 in. x 6.875 in. DF/SYP, 24F-1.8E 8'

5.125 in. x 12.375 in. DF/SYP, 24F-1.8E 18'

312 W. Lakeside St. | Madison, WI 53715
hello@openingdesign.com | 773-425-6456

07.26.2017 For Fabrication
09.13.2017 For Glulam Erection

The Downtowner | 640 West Main Street, Lake Geneva, WI 53147
