OpeningDesign/Vacation_Rental/Transfer/20170519 ----- ISSUE FOR BID & PERMIT -------/The Downtowner_ARCH - Sheet - A351 - WALL SECTIONS.pdf

E.1E.2
B.5

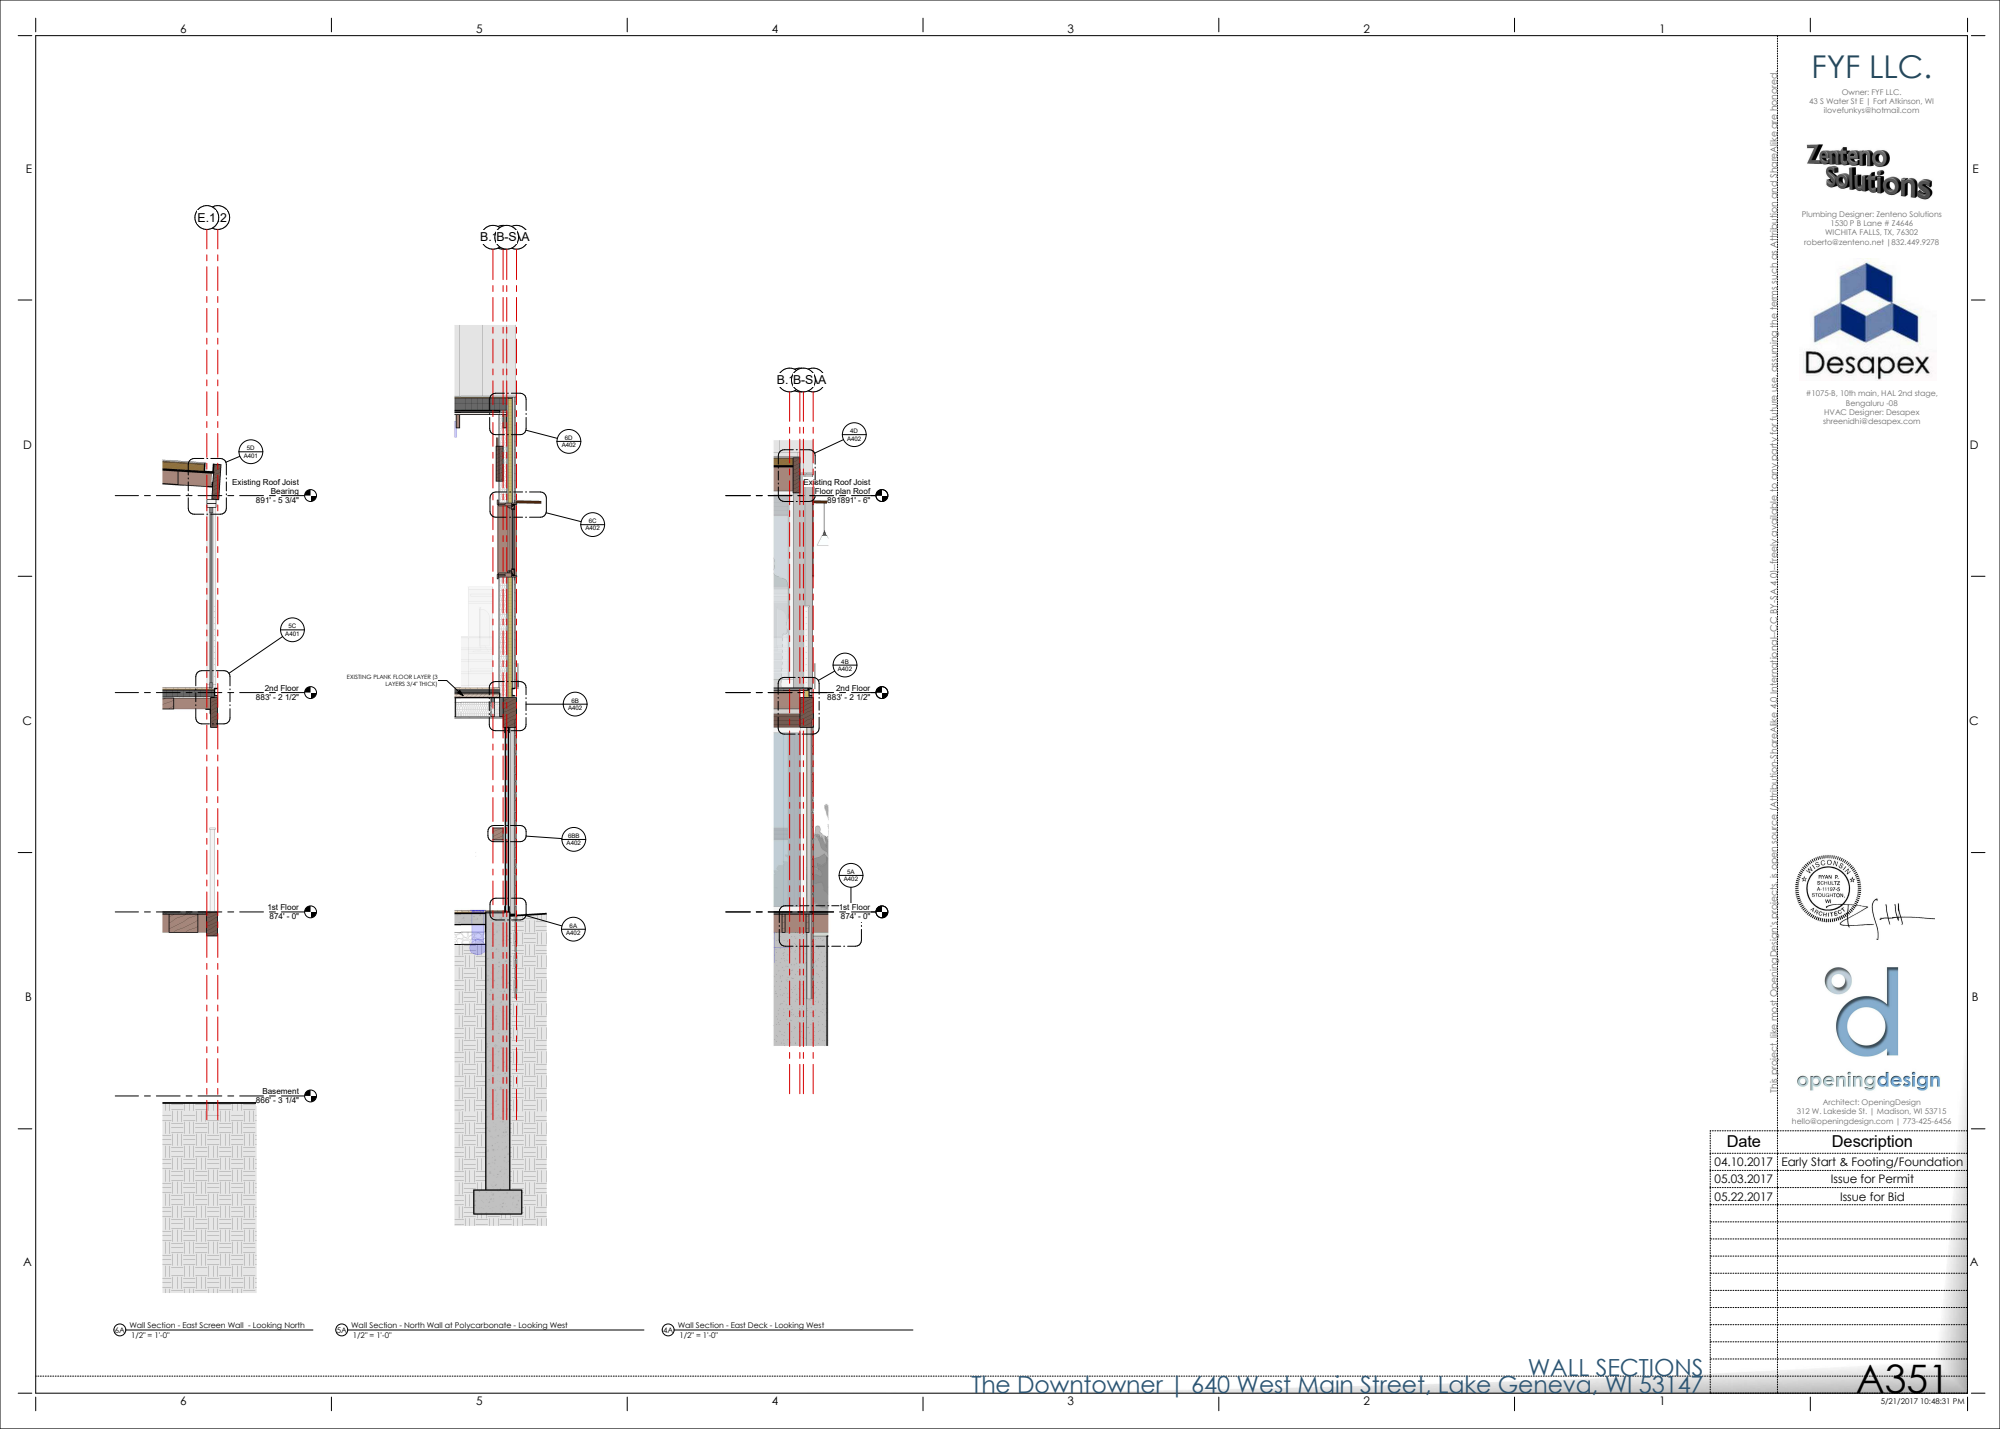
[picture p275: page 1]
1st Floor 874' - 0"; 2nd Floor 883' - 2 1/2"; Basement 866' - 3 1/4"; Bearing 891' - 5 3/4"; LAYERS 3/4" THICK); Bearing; Architect: OpeningDesign; FYF LLC.; 1/2" = 1'-0" 6A Wall Section - East Screen Wall - Looking North; 1/2" = 1'-0" 5A Wall Section - North Wall at Polycarbonate - Looking West; 1/2" = 1'-0" 4A Wall Section - East Deck - Looking West; Date; Description

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

Owner: FYF LLC.

43 S Water St E | Fort Atkinson, WI
ilovefunkys@hotmail.com

Plumbing Designer: Zenteno Solutions

1530 P B Lane # Z4646
WICHITA FALLS, TX, 76302
roberto@zenteno.net |832.449.9278

#1075-B, 10th main, HAL 2nd stage,

Bengaluru -08
HVAC Designer: Desapex
shreenidhi@desapex.com

Existing Roof Joist

Floor plan Roof

EXISTING PLANK FLOOR LAYER (3

312 W. Lakeside St. | Madison, WI 53715
hello@openingdesign.com | 773-425-6456

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

WALL SECTIONS The Downtowner | 640 West Main Street, Lake Geneva, WI 53147
