OpeningDesign/Vacation_Rental/Transfer/20170519 ----- ISSUE FOR BID & PERMIT -------/The Downtowner_ARCH - Sheet - S101 - STRUCTURAL - FOUNDATION & 1ST FLOOR.pdf

B

C.3 E

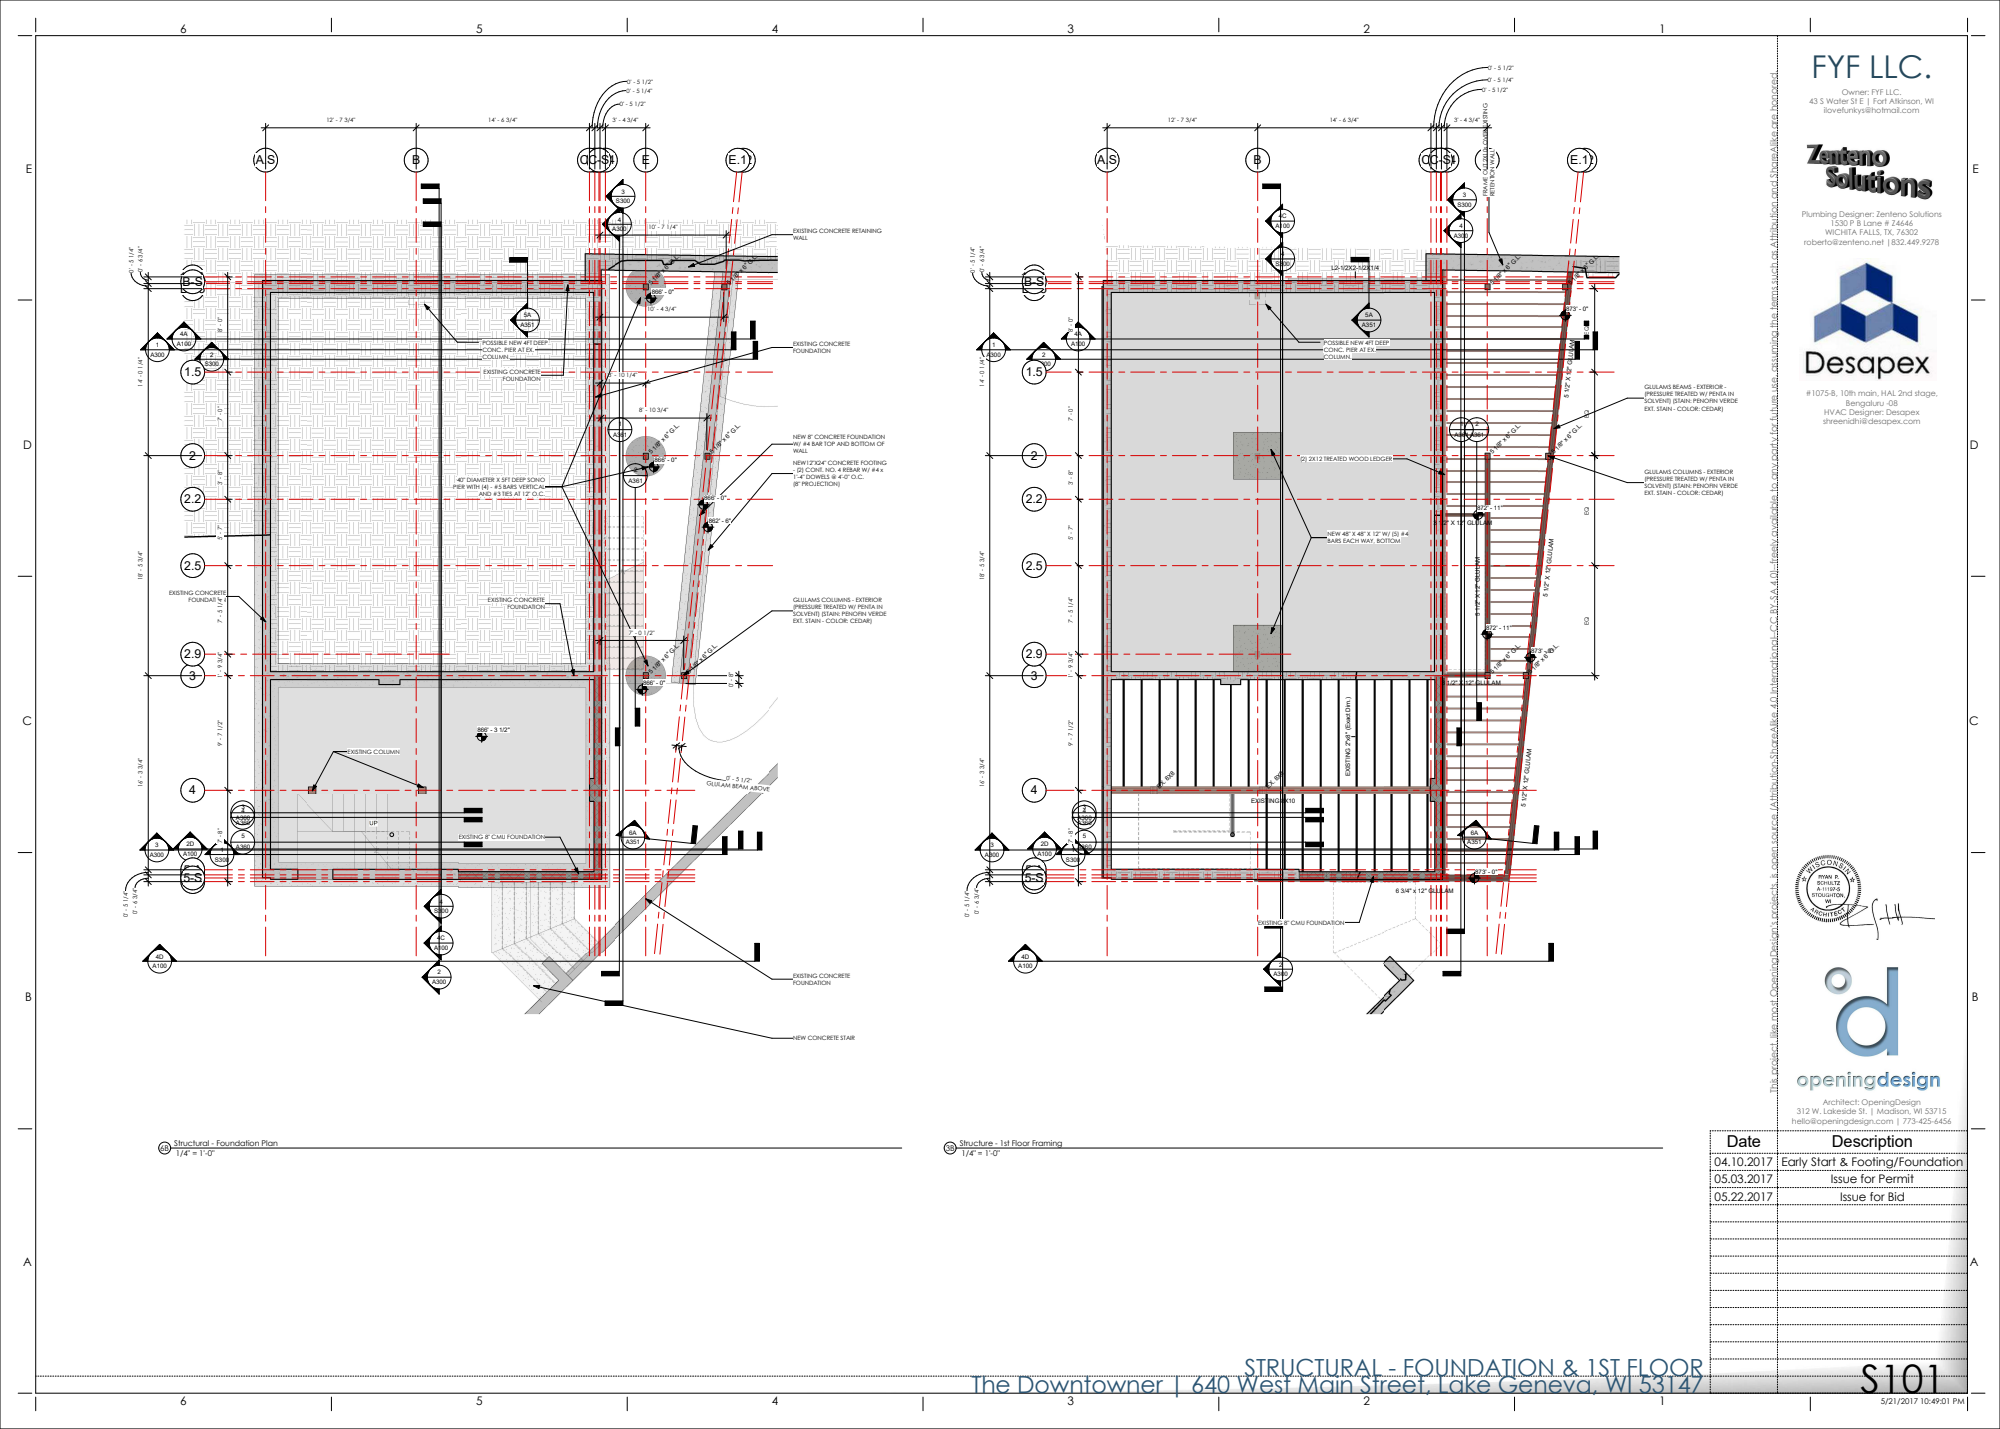
[picture p276: page 1]
EXISTING 8X10; 5 1/2" X 12" GLULAM 5 1/2" X 12" GL; LAM; 6 3/4" x 12" GLULAM; 3 1/2" X 12" GLULAM; RETENTION WALL C-S E.1; EXISTING CONCRETE FOUNDATION; EXISTING COLUMN; Architect: OpeningDesign; FYF LLC.; 1/4" = 1'-0" 3B Structure - 1st Floor Framing 1/4" = 1'-0" 6B Structural - Foundation Plan; Date; Description

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

Owner: FYF LLC.

43 S Water St E | Fort Atkinson, WI
ilovefunkys@hotmail.com

FRAME OUT 2X10s OVER EXISTING

Plumbing Designer: Zenteno Solutions

1530 P B Lane # Z4646
WICHITA FALLS, TX, 76302
roberto@zenteno.net |832.449.9278

EXISTING CONCRETE RETAINING
WALL

POSSIBLE NEW 4FT DEEP
CONC. PIER AT EX.
COLUMN.

GLULAMS BEAMS - EXTERIOR -
(PRESSURE TREATED W/ PENTA IN
SOLVENT) (STAIN: PENOFIN VERDE
EXT. STAIN - COLOR: CEDAR)

#1075-B, 10th main, HAL 2nd stage,

Bengaluru -08
HVAC Designer: Desapex
shreenidhi@desapex.com

NEW 8" CONCRETE FOUNDATION
W/ #4 BAR TOP AND BOTTOM OF

(2) 2X12 TREATED WOOD LEDGER

NEW12"X24" CONCRETE FOOTING
- (2) CONT. NO. 4 REBAR W/ #4 x
1'-4" DOWELS @ 4'-0" O.C.
(8" PROJECTION)

GLULAMS COLUMNS - EXTERIOR

40" DIAMETER X 5FT DEEP SONO
PIER WITH (4) - #5 BARS VERTICAL

AND #3 TIES AT 12" O.C.

NEW 48" X 48" X 12" W/ (5) #4
BARS EACH WAY, BOTTOM

EXISTING 2"x8" (Exact Dim.)

GLULAM BEAM ABOVE

EXISTING 8" CMU FOUNDATION

NEW CONCRETE STAIR

312 W. Lakeside St. | Madison, WI 53715
hello@openingdesign.com | 773-425-6456

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

S101 STRUCTURAL - FOUNDATION & 1ST FLOOR The Downtowner | 640 West Main Street, Lake Geneva, WI 53147
