OpeningDesign/Vacation_Rental/Transfer/20170519 ----- ISSUE FOR BID & PERMIT -------/The Downtowner_ARCH - Sheet - S102 - STRUCTURAL - 2ND FLOOR & ROOF FRAMING.pdf

B

C.3 E

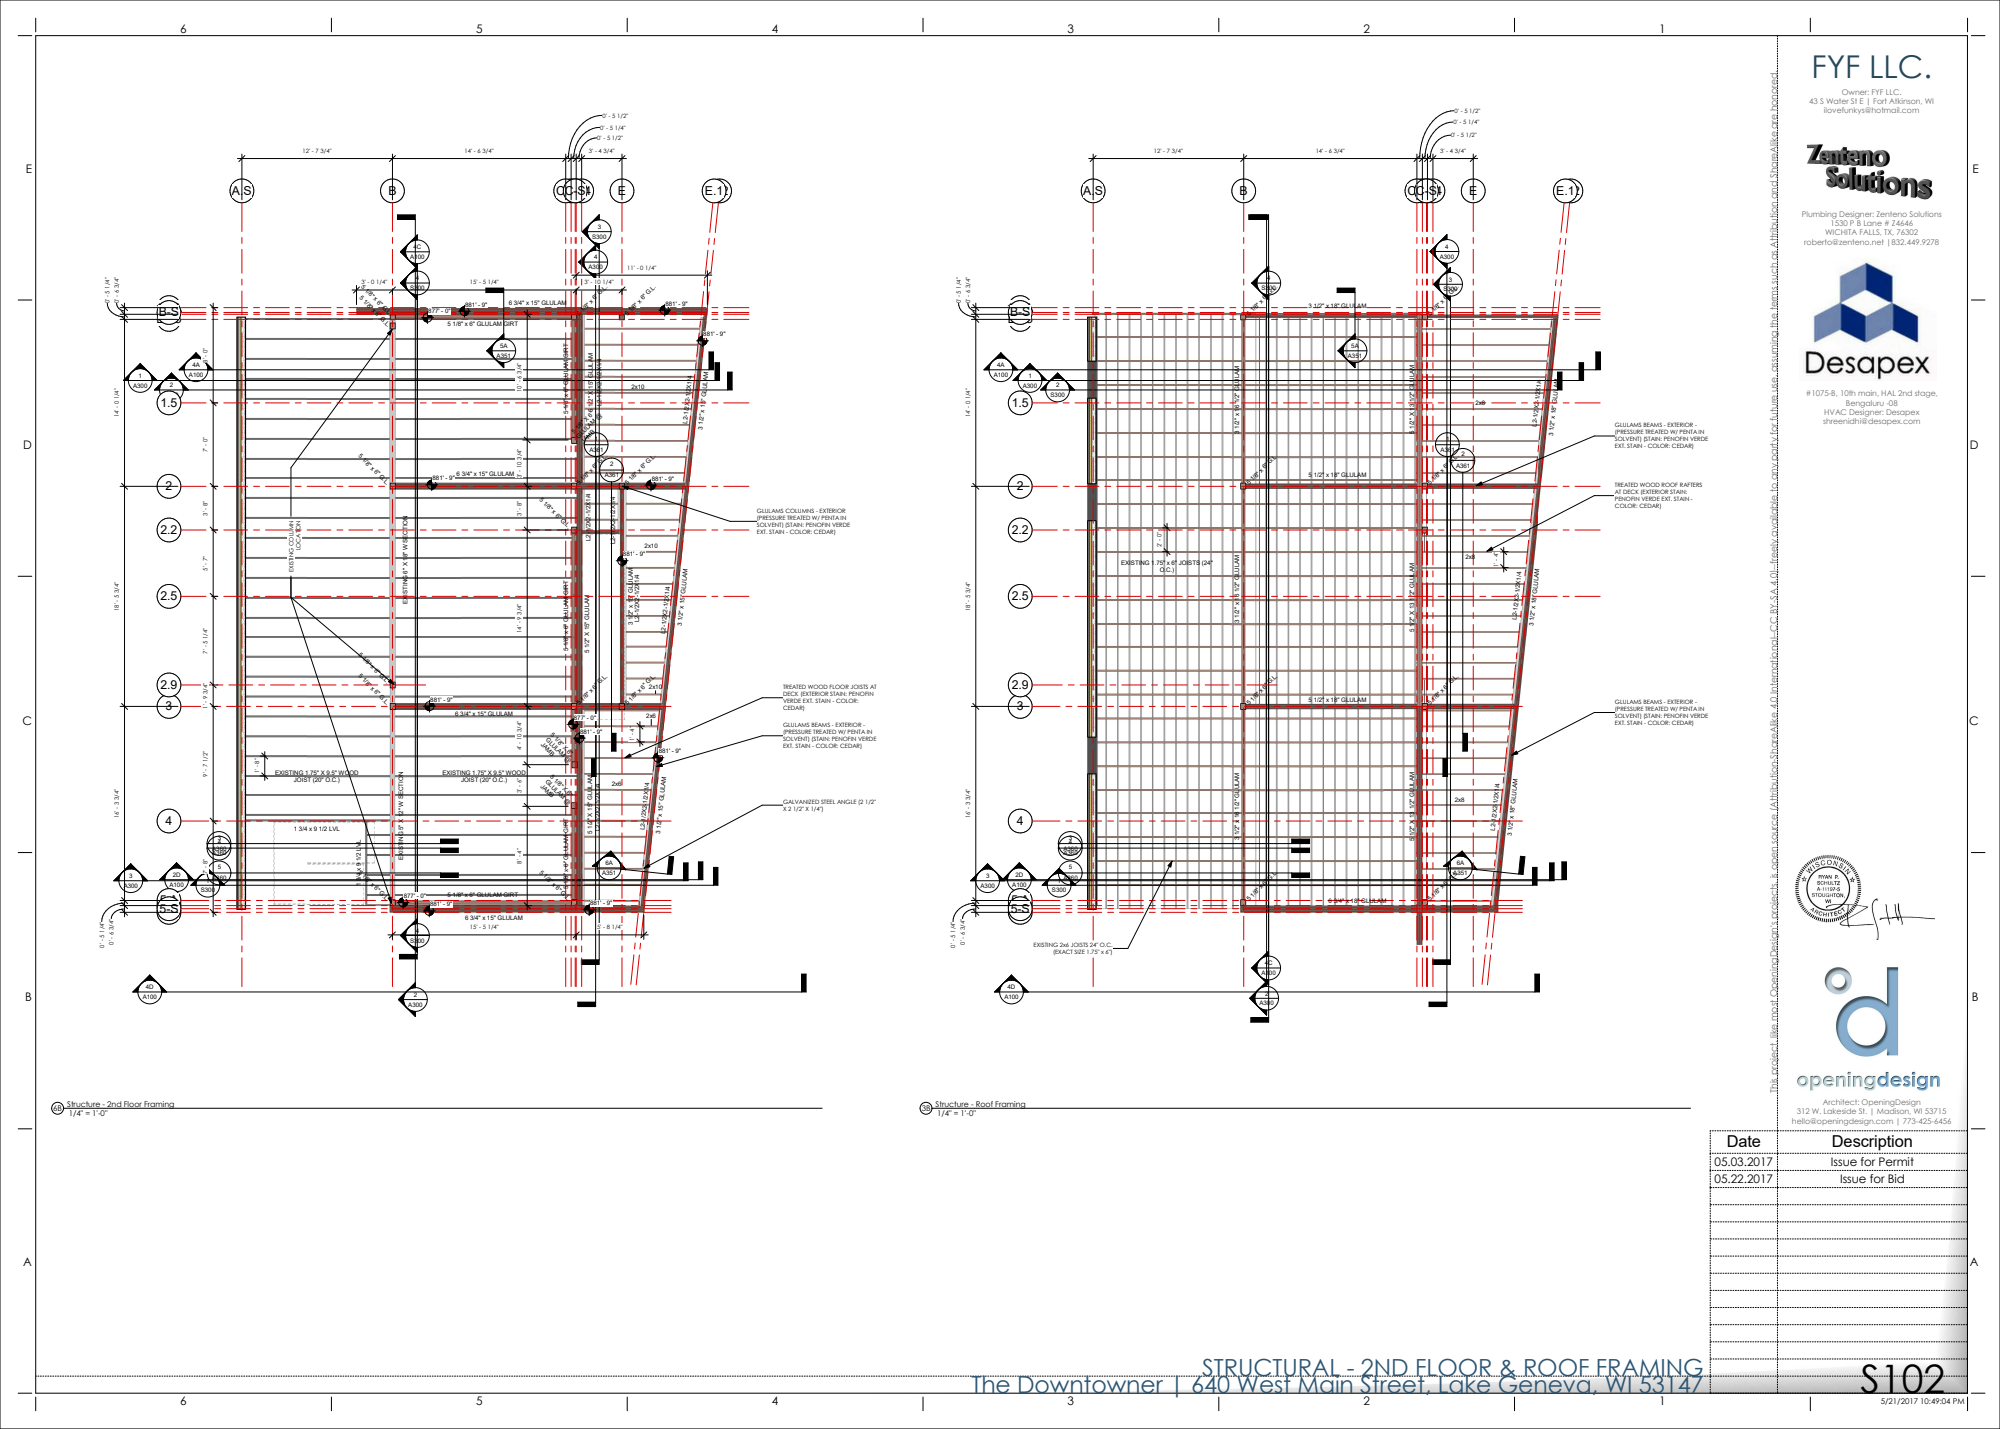
[picture p277: page 1]
3 1/2" x 18" GLULAM; 5 1/2" x 18" GLULAM; 6 3/4" x 18" GLULAM; 3 1/2" x 16 1/2" GLULAM 3 1/2" x 16 1/2" GLULAM; 3 1/2" x 16 1/2" GLULAM; EXISTING 1.75" x 6" JOISTS (24" O.C.); EXISTING 2x6 JOISTS 24" O.C. (EXACT SIZE 1.75" x 6"); LAM; 6 3/4" x 15" GLULAM; 3 1/2" x 15" GLULAM; 5 1/2" X 15" GLULAM; 5 1/2" X 15" GLULAM 5 1/2" X 15" GLULAM; 5 1/8" X 6" GLULAM @ JAMB; 5 1/8" x 6" GLULAM GIRT; EXISTING 5" X 12" W SECTION; EXISTING 6" X 18" W SECTION; EXISTING COLUMN; LOCATION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

Owner: FYF LLC.

43 S Water St E | Fort Atkinson, WI
ilovefunkys@hotmail.com

Plumbing Designer: Zenteno Solutions

1530 P B Lane # Z4646
WICHITA FALLS, TX, 76302
roberto@zenteno.net |832.449.9278

5 1/8" x 6" GLULAM GIRT 5 1/8" x 6" GLULAM GIRT 5 1/8" x 6" GLULAM GIRT

7' - 8" 9' - 7 1/2" 1' - 9 3/4" 7' - 5 1/4" 5' - 7" 3' - 8" 7' - 0" 8' - 0" GLULAMS COLUMNS - EXTERIOR (PRESSURE TREATED W/ PENTA IN SOLVENT) (STAIN: PENOFIN VERDE EXT. STAIN - COLOR: CEDAR)

5 1/2" X 13 1/2" GLULAM 5 1/2" X 13 1/2" GLULAM 5 1/2" X 13 1/2" GLULAM 3 1/2" x 18" GLULAM 3 1/2" x 18" GLULAM 3 1/2" x 18" GLULAM

#1075-B, 10th main, HAL 2nd stage,

Bengaluru -08
HVAC Designer: Desapex
shreenidhi@desapex.com

GLULAMS BEAMS - EXTERIOR -
(PRESSURE TREATED W/ PENTA IN
SOLVENT) (STAIN: PENOFIN VERDE
EXT. STAIN - COLOR: CEDAR)

TREATED WOOD ROOF RAFTERS
AT DECK (EXTERIOR STAIN:
PENOFIN VERDE EXT. STAIN -
COLOR: CEDAR)

TREATED WOOD FLOOR JOISTS AT
DECK (EXTERIOR STAIN: PENOFIN
VERDE EXT. STAIN - COLOR:
CEDAR)

GALVANIZED STEEL ANGLE (2 1/2"

1/4" = 1'-0" 3B Structure - Roof Framing 1/4" = 1'-0" 6B Structure - 2nd Floor Framing

312 W. Lakeside St. | Madison, WI 53715
hello@openingdesign.com | 773-425-6456

05.03.2017 Issue for Permit
05.22.2017 Issue for Bid

S102 STRUCTURAL - 2ND FLOOR & ROOF FRAMING The Downtowner | 640 West Main Street, Lake Geneva, WI 53147
