OpeningDesign/Vacation_Rental/Transfer/20170519 ----- ISSUE FOR BID & PERMIT -------/The Downtowner_ARCH_Exterior Details - Sheet - S400 - BRACING ELEVATION.pdf

## C.4C.3 C-SC.2C.1

### BCDE

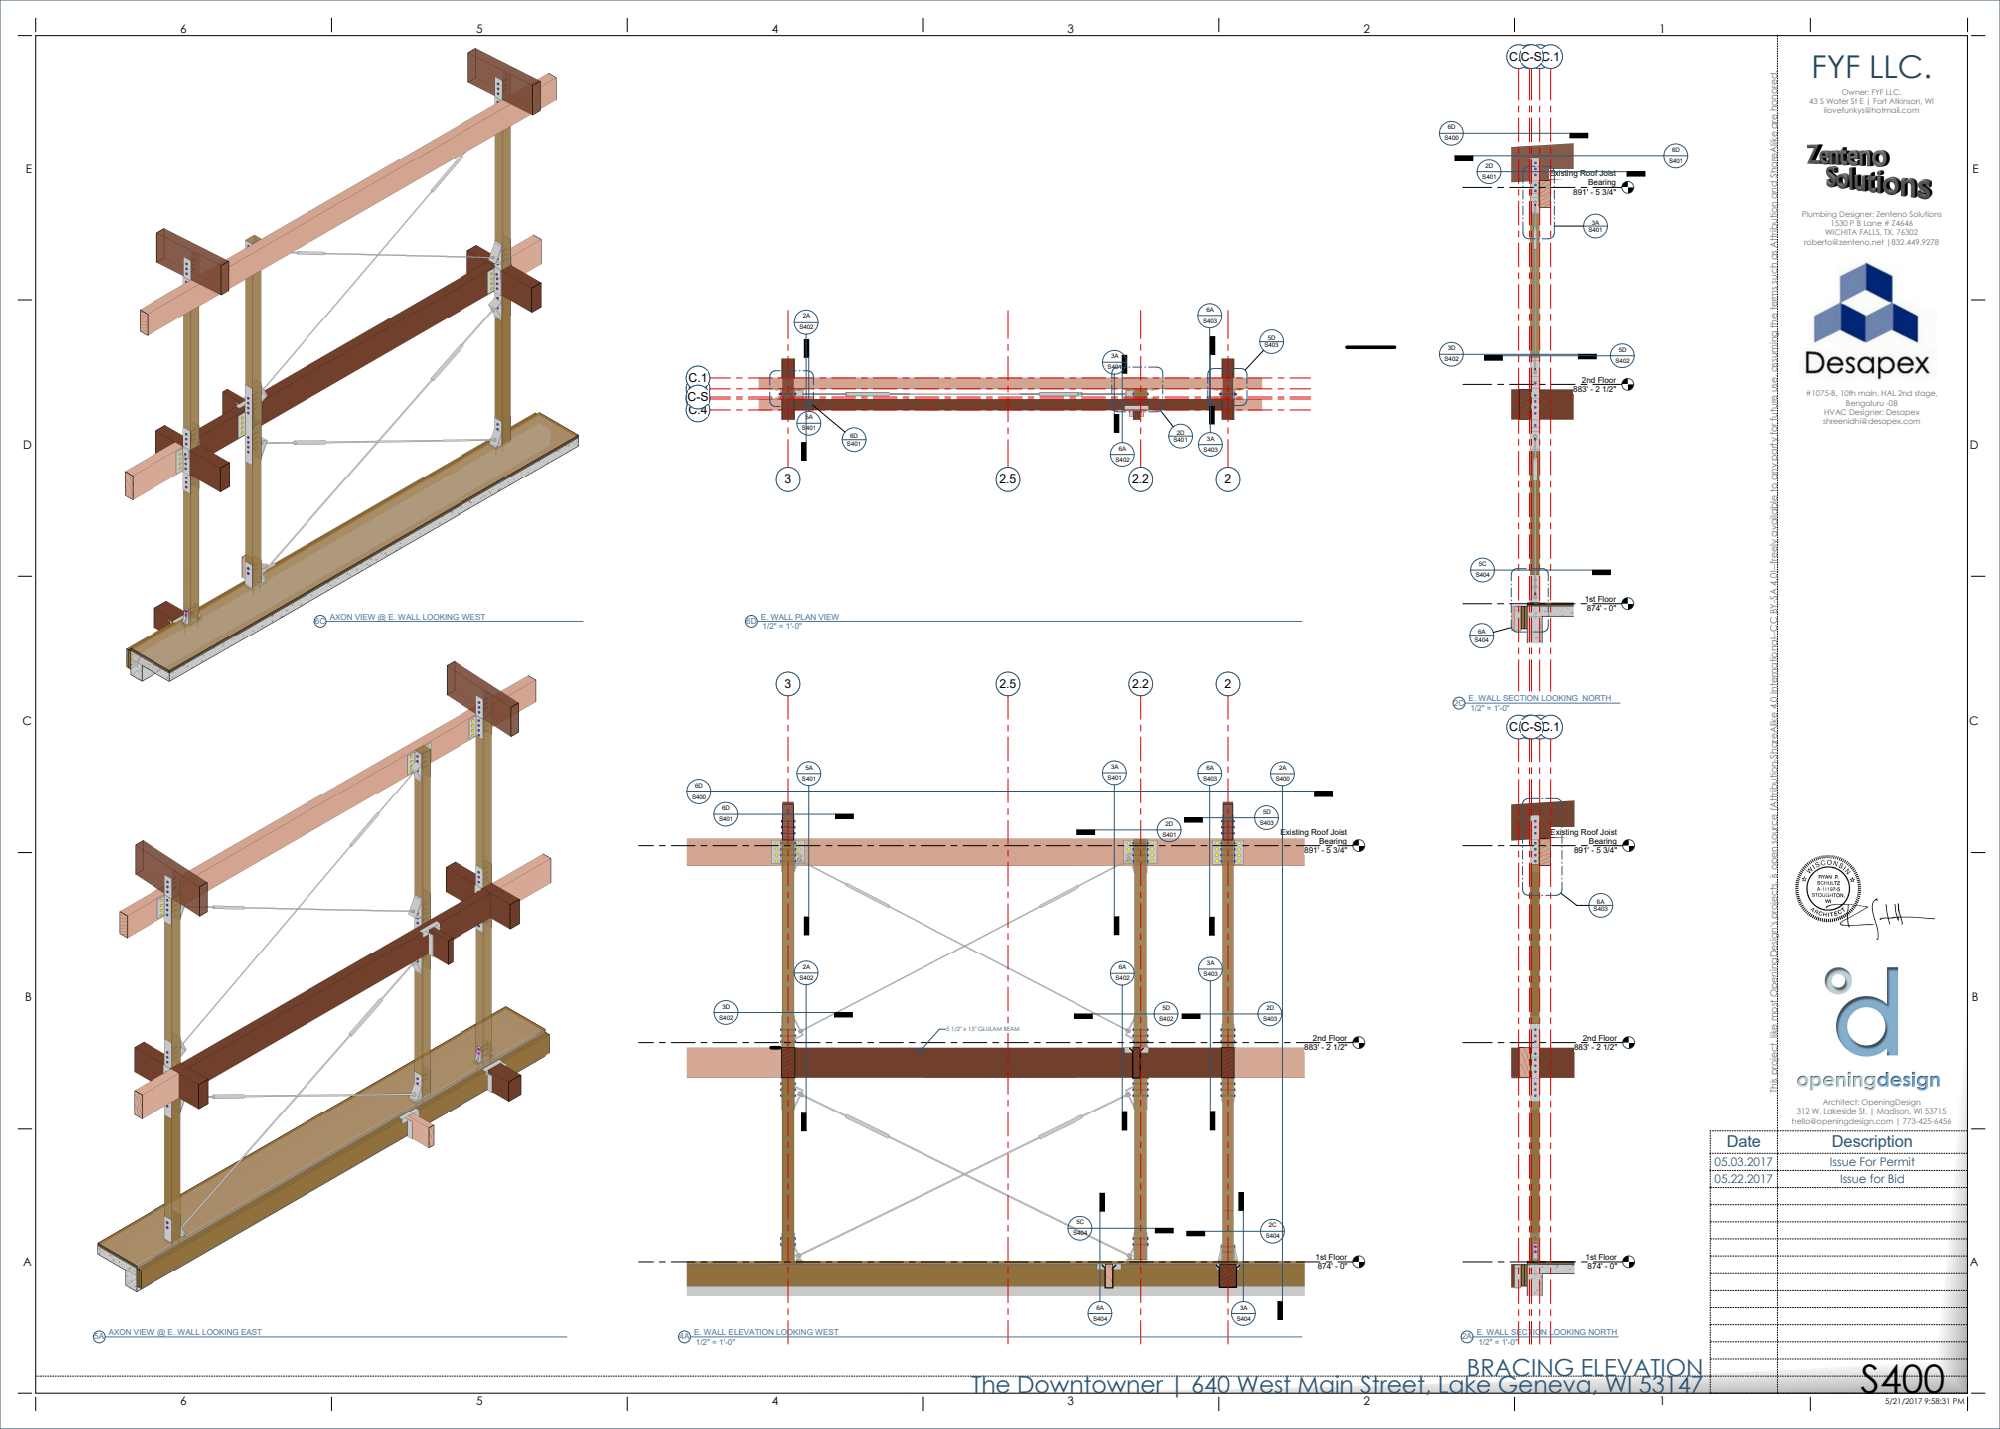
[picture p278: page 1]
1st Floor 874' - 0"; 2nd Floor 883' - 2 1/2"; Existing Roof Joist Bearing 891' - 5 3/4"; 5 1/2" x 15" GLULAM BEAM; Bearing 891' - 5 3/4"; Architect: OpeningDesign; ABCDE; FYF LLC.; E. WALL ELEVATION LOOKING WEST; E. WALL SECTION LOOKING NORTH; Date; Description

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

Owner: FYF LLC.

43 S Water St E | Fort Atkinson, WI
ilovefunkys@hotmail.com

Existing Roof Joist

Plumbing Designer: Zenteno Solutions

1530 P B Lane # Z4646
WICHITA FALLS, TX, 76302
roberto@zenteno.net |832.449.9278

#1075-B, 10th main, HAL 2nd stage,

Bengaluru -08
HVAC Designer: Desapex
shreenidhi@desapex.com

E. WALL PLAN VIEW 6C AXON VIEW @ E. WALL LOOKING WEST

312 W. Lakeside St. | Madison, WI 53715
hello@openingdesign.com | 773-425-6456

05.03.2017 Issue For Permit
05.22.2017 Issue for Bid

5A AXON VIEW @ E. WALL LOOKING EAST

E. WALL SECTION LOOKING NORTH
BRACING ELEVATION

The Downtowner | 640 West Main Street, Lake Geneva, WI 53147
