OpeningDesign/Vacation_Rental/Transfer/20170519 ----- ISSUE FOR BID & PERMIT -------/The_Downtowner_PLMB_ZS - Sheet - P1-03 - BASEMENT & FIRST FLOOR WATER DISTRIBUTION.pdf

E

E

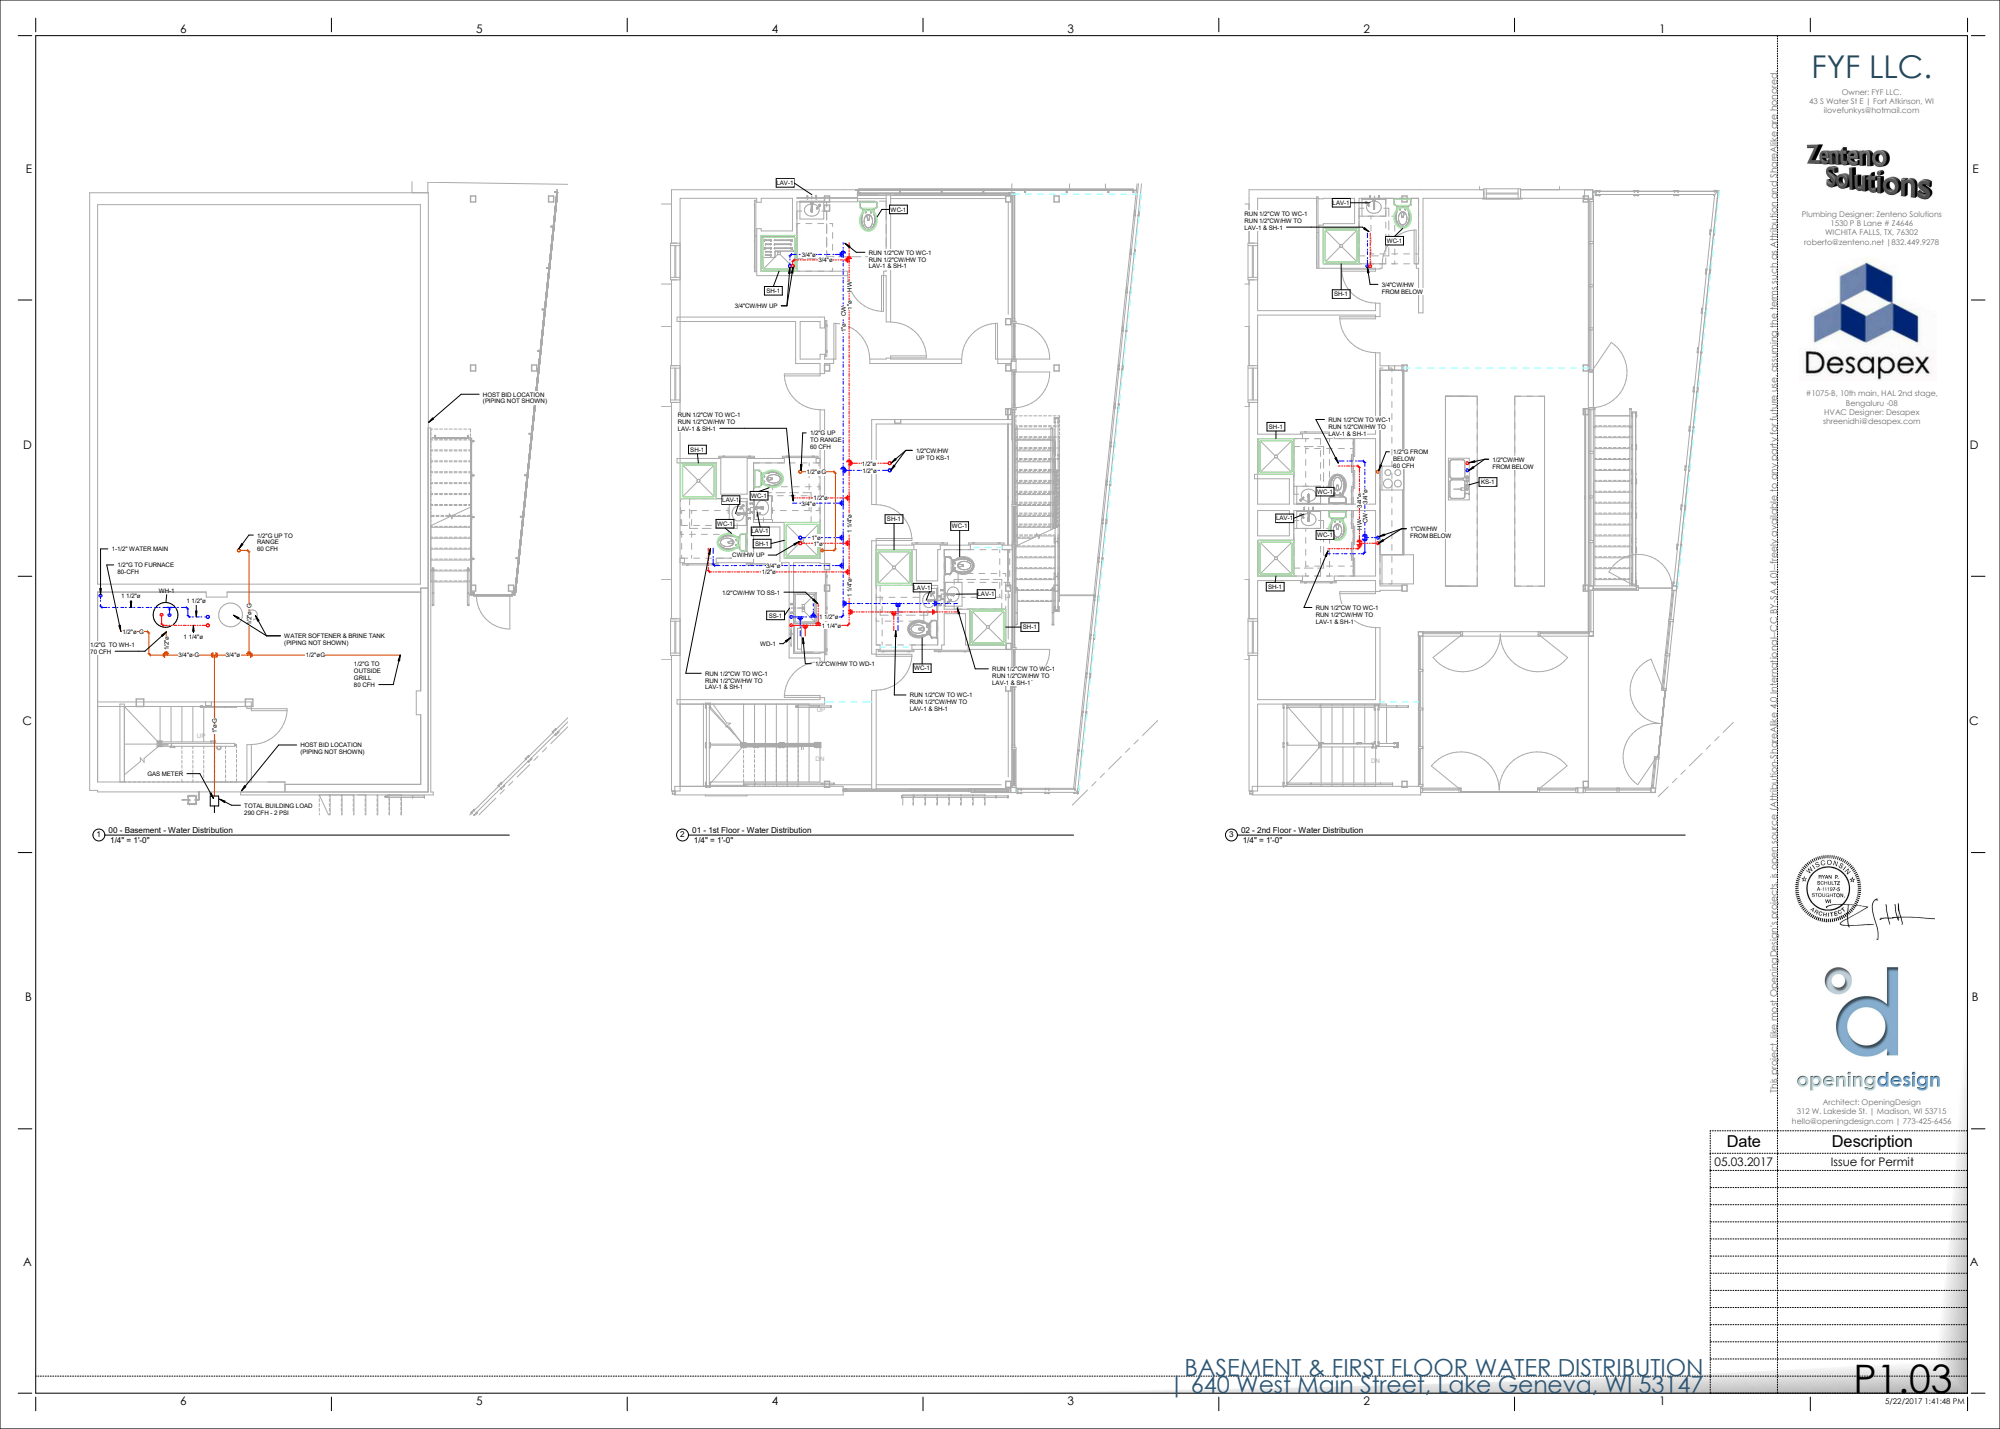
[picture p279: page 1]
1/2"G TO FURNACE 80-CFH; 70 CFH; GAS METER; 1/2"G UP TO RANGE 60 CFH; 1/2"G TO OUTSIDE GRILL 80 CFH; 1-1/2" WATER MAIN; LAV-1; 1/2"G FROM BELOW 60 CFH; 1/2"CW/HW FROM BELOW; 1"CW/HW FROM BELOW; 3/4"CW/HW FROM BELOW; Architect: OpeningDesign; FYF LLC.; 1/4" = 1'-0" 1 00 - Basement - Water Distribution; 1/4" = 1'-0" 2 01 - 1st Floor - Water Distribution; 1/4" = 1'-0" 3 02 - 2nd Floor - Water Distribution; Date; Description

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

Owner: FYF LLC.

43 S Water St E | Fort Atkinson, WI
ilovefunkys@hotmail.com

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

Plumbing Designer: Zenteno Solutions

1530 P B Lane # Z4646
WICHITA FALLS, TX, 76302
roberto@zenteno.net |832.449.9278

HOST BID LOCATION
(PIPING NOT SHOWN)

#1075-B, 10th main, HAL 2nd stage,

Bengaluru -08
HVAC Designer: Desapex
shreenidhi@desapex.com

WATER SOFTENER & BRINE TANK

TOTAL BUILDING LOAD
290 CFH - 2 PSI

312 W. Lakeside St. | Madison, WI 53715
hello@openingdesign.com | 773-425-6456

05.03.2017 Issue for Permit

BASEMENT & FIRST FLOOR WATER DISTRIBUTION | 640 West Main Street, Lake Geneva, WI 53147
