OpeningDesign/Vacation_Rental/Transfer/20170503 ----- ISSUE FOR PERMIT ------/M-002 - HVAC 1st & 2nd Floor plan.pdf

E

E

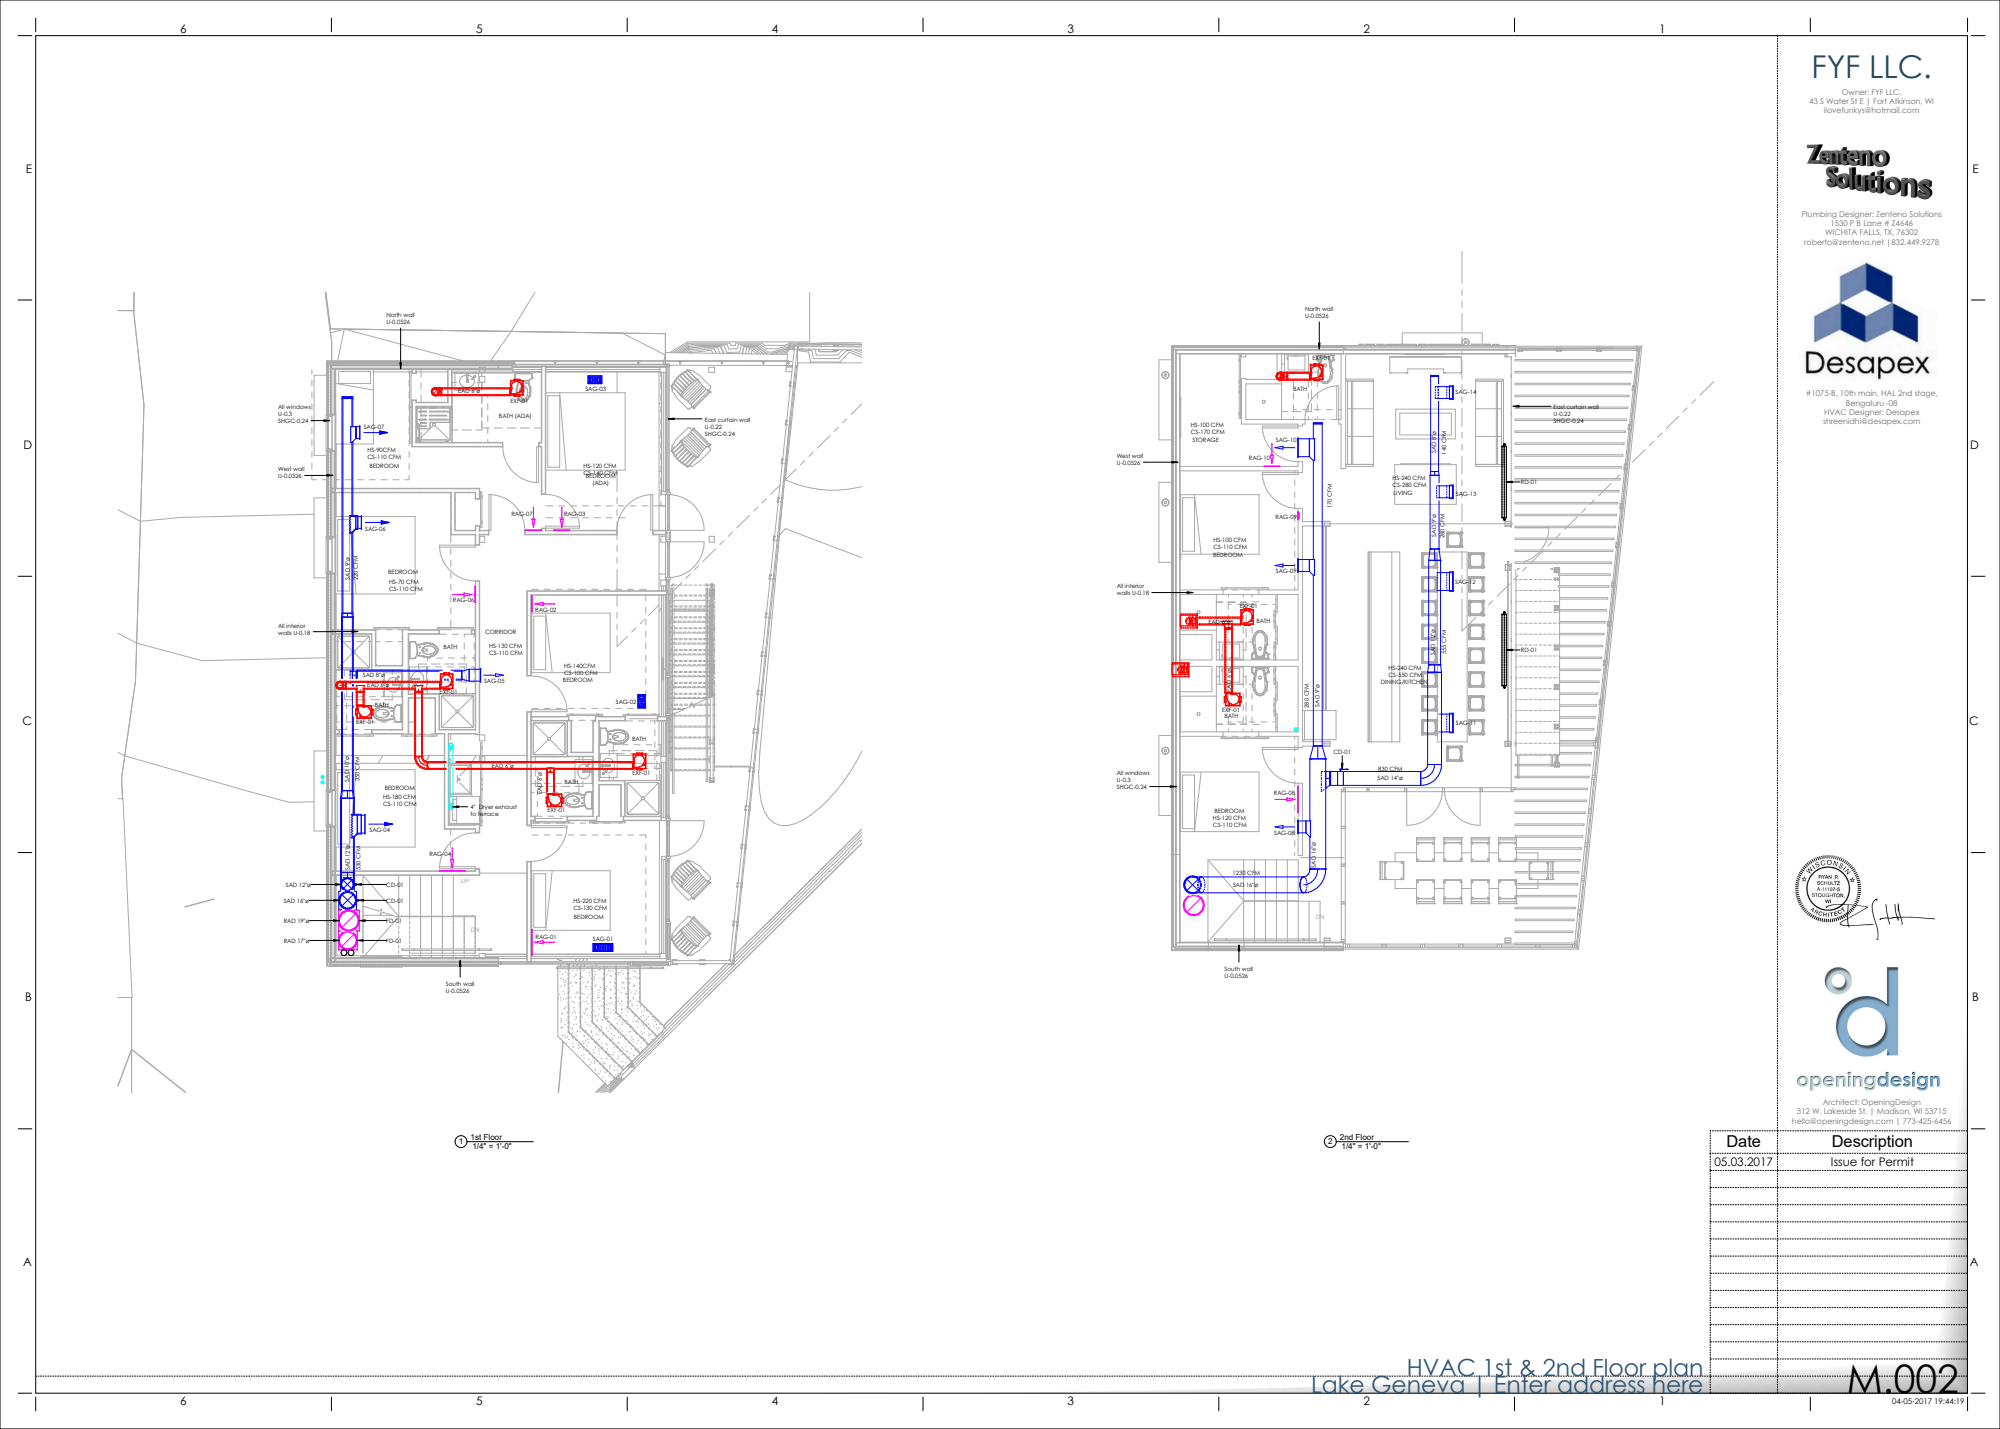
[picture p280: page 1]
HS-180 CFM CS-110 CFM; SAD 12"ø; EXF-01; SAD 10"ø SAD 9"ø; EAD 6"ø; SAG-04; SAG-05; SAG-07; SAG-06; RAG-01; RAG-02; RAG-07; RAG-03; RAG-06; HS-70 CFM CS-110 CFM; HS-90CFM CS-110 CFM; HS-220 CFM CS-130 CFM; HS-140CFM CS-100 CFM; HS-120 CFM CS-140 CFM; HS-130 CFM CS-110 CFM; SAD 16"ø; RAD 19"ø; SAG-02; East curtain wall U-0.22 SHGC-0.24; West wall U-0.0526; North wall U-0.0526; South wall U-0.0526; All interior walls U-0.18; All windows U-0.3 SHGC-0.24; SAG-03; SAG-01; RAG-04; SAD 8"ø; RAD 17"ø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

Owner: FYF LLC.

43 S Water St E | Fort Atkinson, WI
ilovefunkys@hotmail.com

Plumbing Designer: Zenteno Solutions

1530 P B Lane # Z4646
WICHITA FALLS, TX, 76302
roberto@zenteno.net |832.449.9278

#1075-B, 10th main, HAL 2nd stage,

Bengaluru -08
HVAC Designer: Desapex
shreenidhi@desapex.com

SAD 12"ø SAD 9"ø SAD 8"ø

555 CFM 280 CFM 140 CFM

530 CFM 350 CFM 220 CFM

312 W. Lakeside St. | Madison, WI 53715
hello@openingdesign.com | 773-425-6456

HVAC 1st & 2nd Floor plan Lake Geneva | Enter address here
