OpeningDesign/Vacation_Rental/Transfer/20170503 ----- ISSUE FOR PERMIT ------/A100 - DEMOLITION PLANS.pdf

B

5.B | 3 | 2

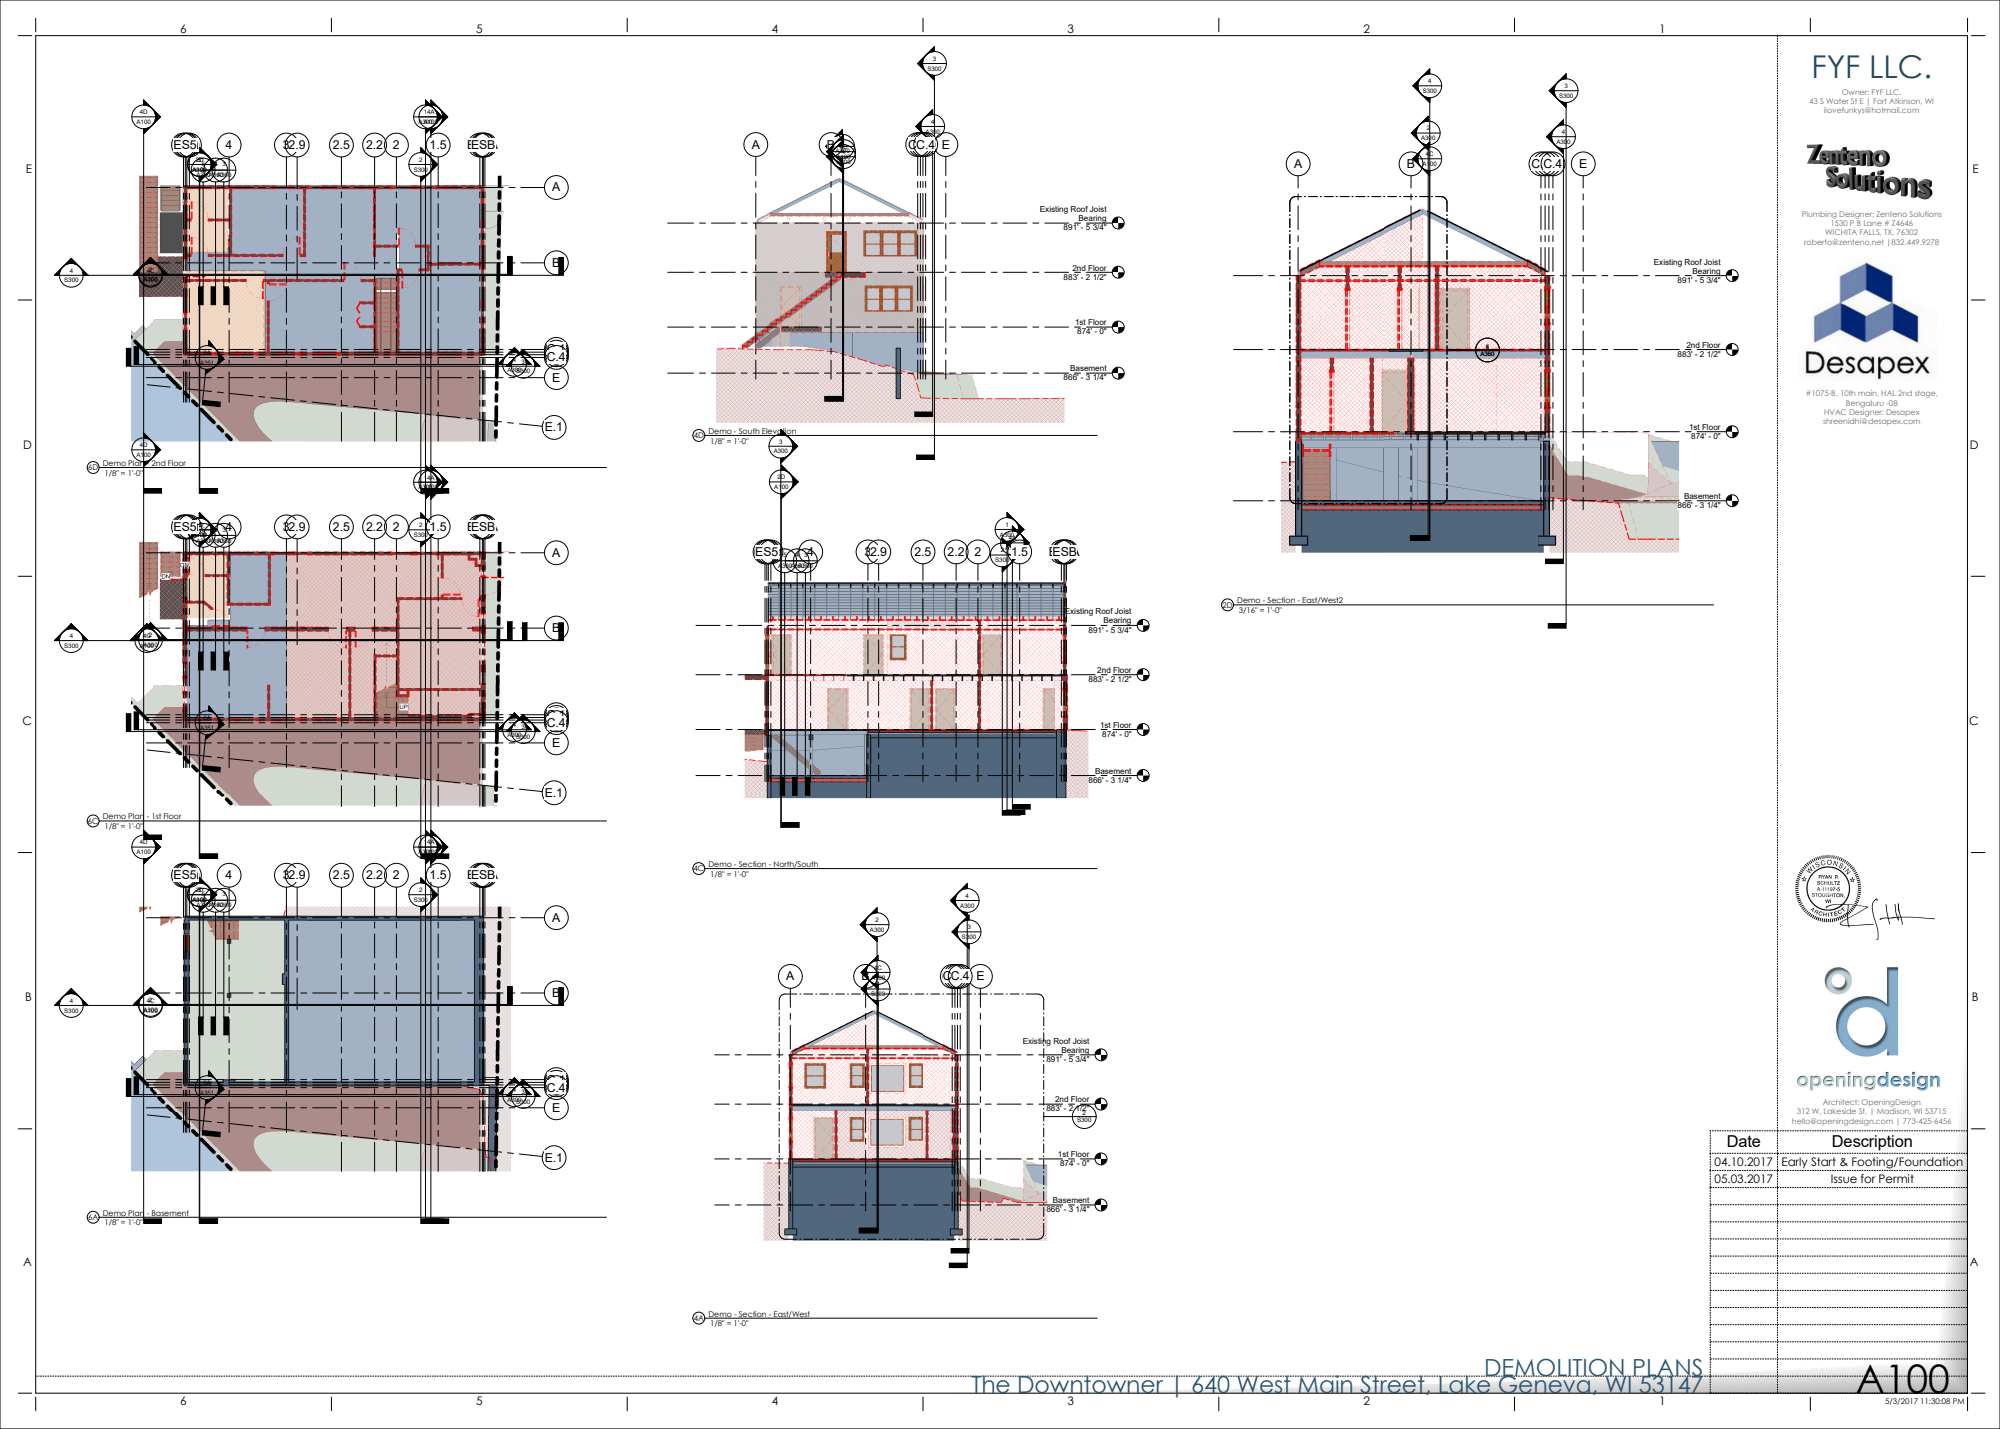
[picture p281: page 1]
ESB; 1st Floor 874' - 0"; 2nd Floor 883' - 2 1/2"; Basement 866' - 3 1/4"; Bearing 891' - 5 3/4"; Architect: OpeningDesign; FYF LLC.; Date; Description

Owner: FYF LLC.

43 S Water St E | Fort Atkinson, WI
ilovefunkys@hotmail.com

Existing Roof Joist

Plumbing Designer: Zenteno Solutions

1530 P B Lane # Z4646
WICHITA FALLS, TX, 76302
roberto@zenteno.net |832.449.9278

#1075-B, 10th main, HAL 2nd stage,

Bengaluru -08
HVAC Designer: Desapex
shreenidhi@desapex.com

1/8" = 1'-0" 4D Demo - South Elevation

1/8" = 1'-0" 6D Demo Plan - 2nd Floor

3/16" = 1'-0" 2D Demo - Section - East/West2

1/8" = 1'-0" 6C Demo Plan - 1st Floor

1/8" = 1'-0" 4C Demo - Section - North/South

312 W. Lakeside St. | Madison, WI 53715
hello@openingdesign.com | 773-425-6456

04.10.2017 Early Start & Footing/Foundation
05.03.2017 Issue for Permit

1/8" = 1'-0" 6A Demo Plan - Basement

1/8" = 1'-0" 4A Demo - Section - East/West

DEMOLITION PLANS The Downtowner | 640 West Main Street, Lake Geneva, WI 53147
