OpeningDesign/Vacation_Rental/Transfer/20170503 ----- ISSUE FOR PERMIT ------/A101 - 1ST & 2ND FLOOR PLANS.pdf

B

C.3 E

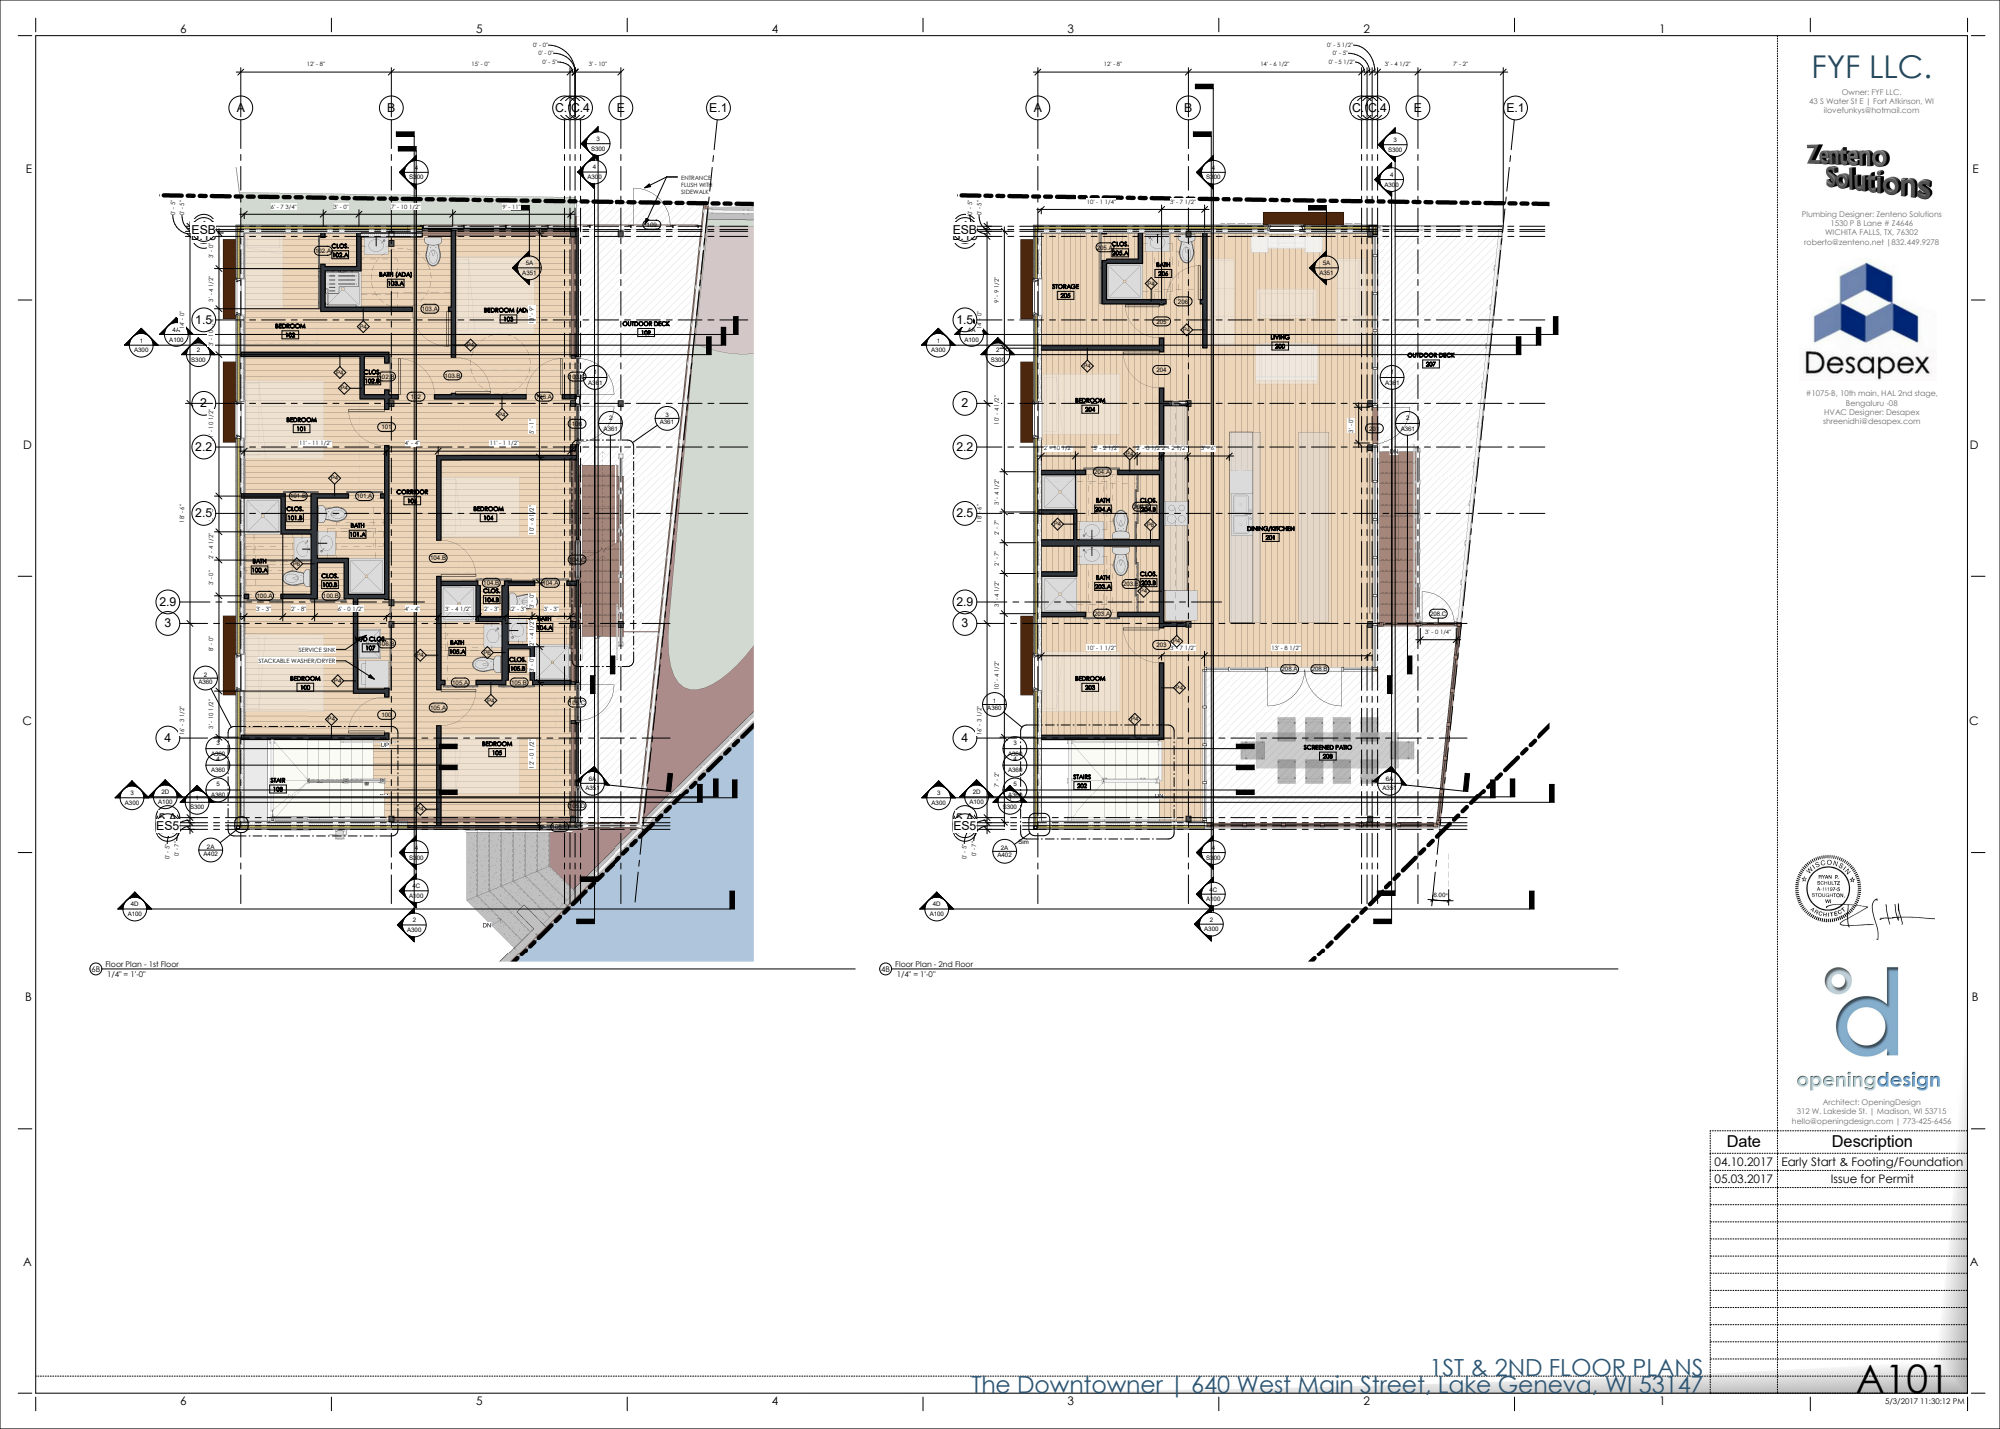
[picture p282: page 1]
BEDROOM; BATH; W/D CLOS.; BATH (ADA); BEDROOM (ADA); CLOS.; CORRIDOR; STAIR; OUTDOOR DECK; ESB; ENTRANCE FLUSH WITH SIDEWALK; STORAGE; STAIRS; DINING/KITCHEN; LIVING; SCREENED PATIO; Sim; Architect: OpeningDesign; FYF LLC.; 1/4" = 1'-0" 6B Floor Plan - 1st Floor; 1/4" = 1'-0" 4B Floor Plan - 2nd Floor; Date; Description

Owner: FYF LLC.

43 S Water St E | Fort Atkinson, WI
ilovefunkys@hotmail.com

Plumbing Designer: Zenteno Solutions

1530 P B Lane # Z4646
WICHITA FALLS, TX, 76302
roberto@zenteno.net |832.449.9278

12' - 0 1/2" 3' - 0" 2' - 4 1/2" 3' - 0" 10' - 6 1/2" 5' - 1" 13' - 9" SERVICE SINK STACKABLE WASHER/DRYER

#1075-B, 10th main, HAL 2nd stage,

Bengaluru -08
HVAC Designer: Desapex
shreenidhi@desapex.com

312 W. Lakeside St. | Madison, WI 53715
hello@openingdesign.com | 773-425-6456

04.10.2017 Early Start & Footing/Foundation
05.03.2017 Issue for Permit

1ST & 2ND FLOOR PLANS The Downtowner | 640 West Main Street, Lake Geneva, WI 53147
