OpeningDesign/Vacation_Rental/Transfer/20170503 ----- ISSUE FOR PERMIT ------/A152 - BASEMENT REFLECTED CEILING PLANS.pdf

B

C.3 E

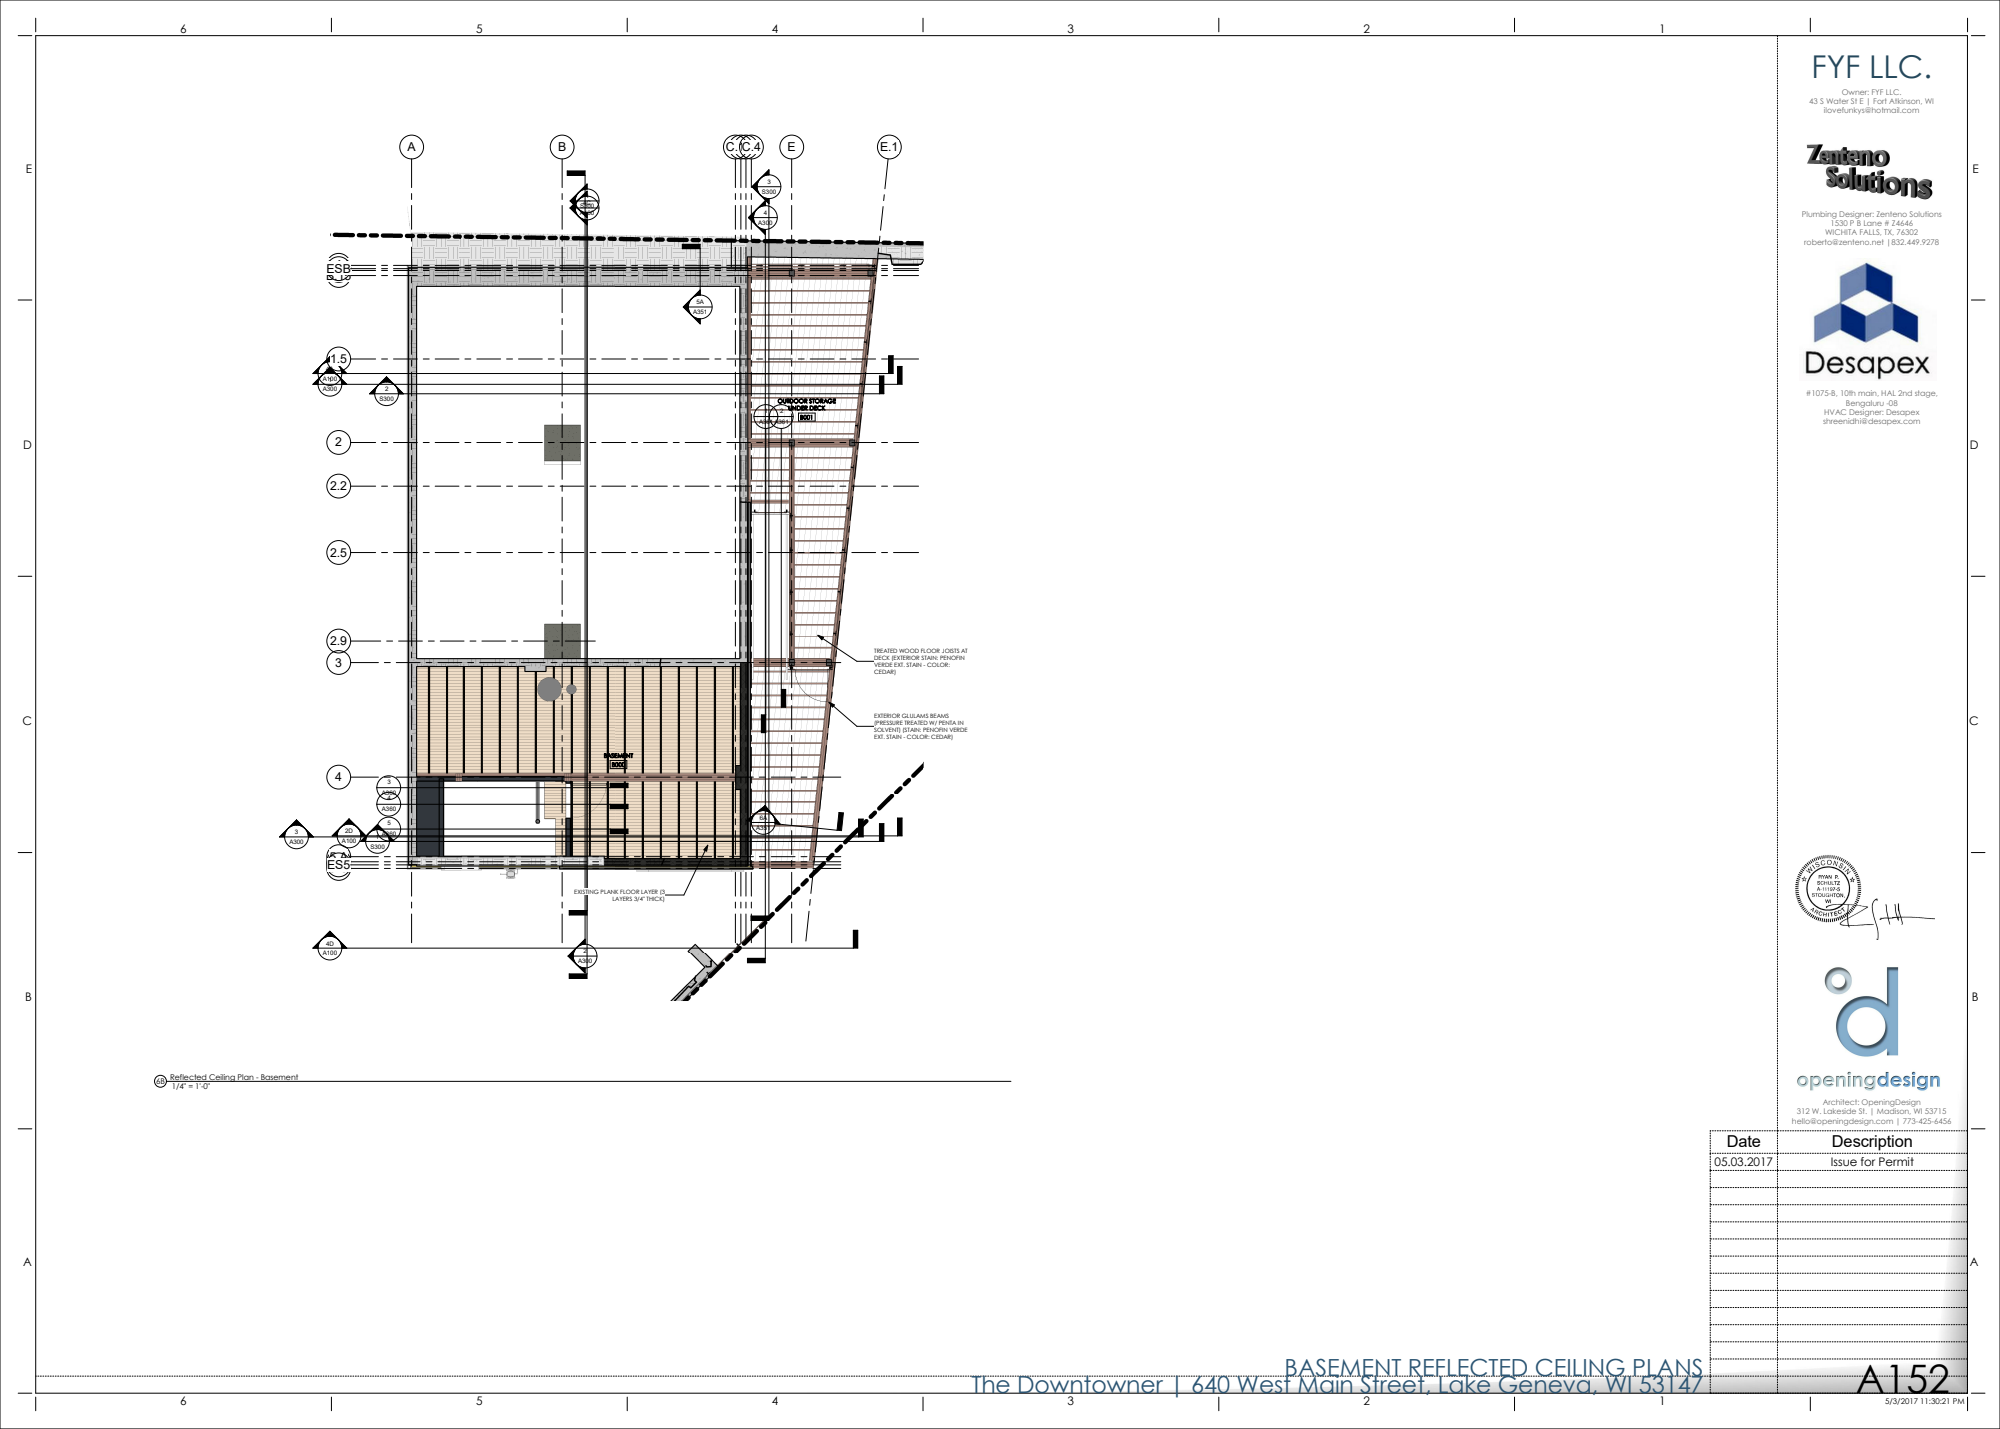
[picture p283: page 1]
BASEMENT; OUTDOOR STORAGE UNDER DECK; ESB; LAYERS 3/4" THICK); Architect: OpeningDesign; FYF LLC.; Date; Description

Owner: FYF LLC.

43 S Water St E | Fort Atkinson, WI
ilovefunkys@hotmail.com

Plumbing Designer: Zenteno Solutions

1530 P B Lane # Z4646
WICHITA FALLS, TX, 76302
roberto@zenteno.net |832.449.9278

#1075-B, 10th main, HAL 2nd stage,

Bengaluru -08
HVAC Designer: Desapex
shreenidhi@desapex.com

TREATED WOOD FLOOR JOISTS AT
DECK (EXTERIOR STAIN: PENOFIN
VERDE EXT. STAIN - COLOR:
CEDAR)

EXTERIOR GLULAMS BEAMS
(PRESSURE TREATED W/ PENTA IN
SOLVENT) (STAIN: PENOFIN VERDE
EXT. STAIN - COLOR: CEDAR)

EXISTING PLANK FLOOR LAYER (3

1/4" = 1'-0" 6B Reflected Ceiling Plan - Basement

312 W. Lakeside St. | Madison, WI 53715
hello@openingdesign.com | 773-425-6456

05.03.2017 Issue for Permit

BASEMENT REFLECTED CEILING PLANS The Downtowner | 640 West Main Street, Lake Geneva, WI 53147
