OpeningDesign/Vacation_Rental/Transfer/20170503 ----- ISSUE FOR PERMIT ------/S101 - STRUCTURAL - FLOOR PLANS.pdf

5.B | 3 | 2

4

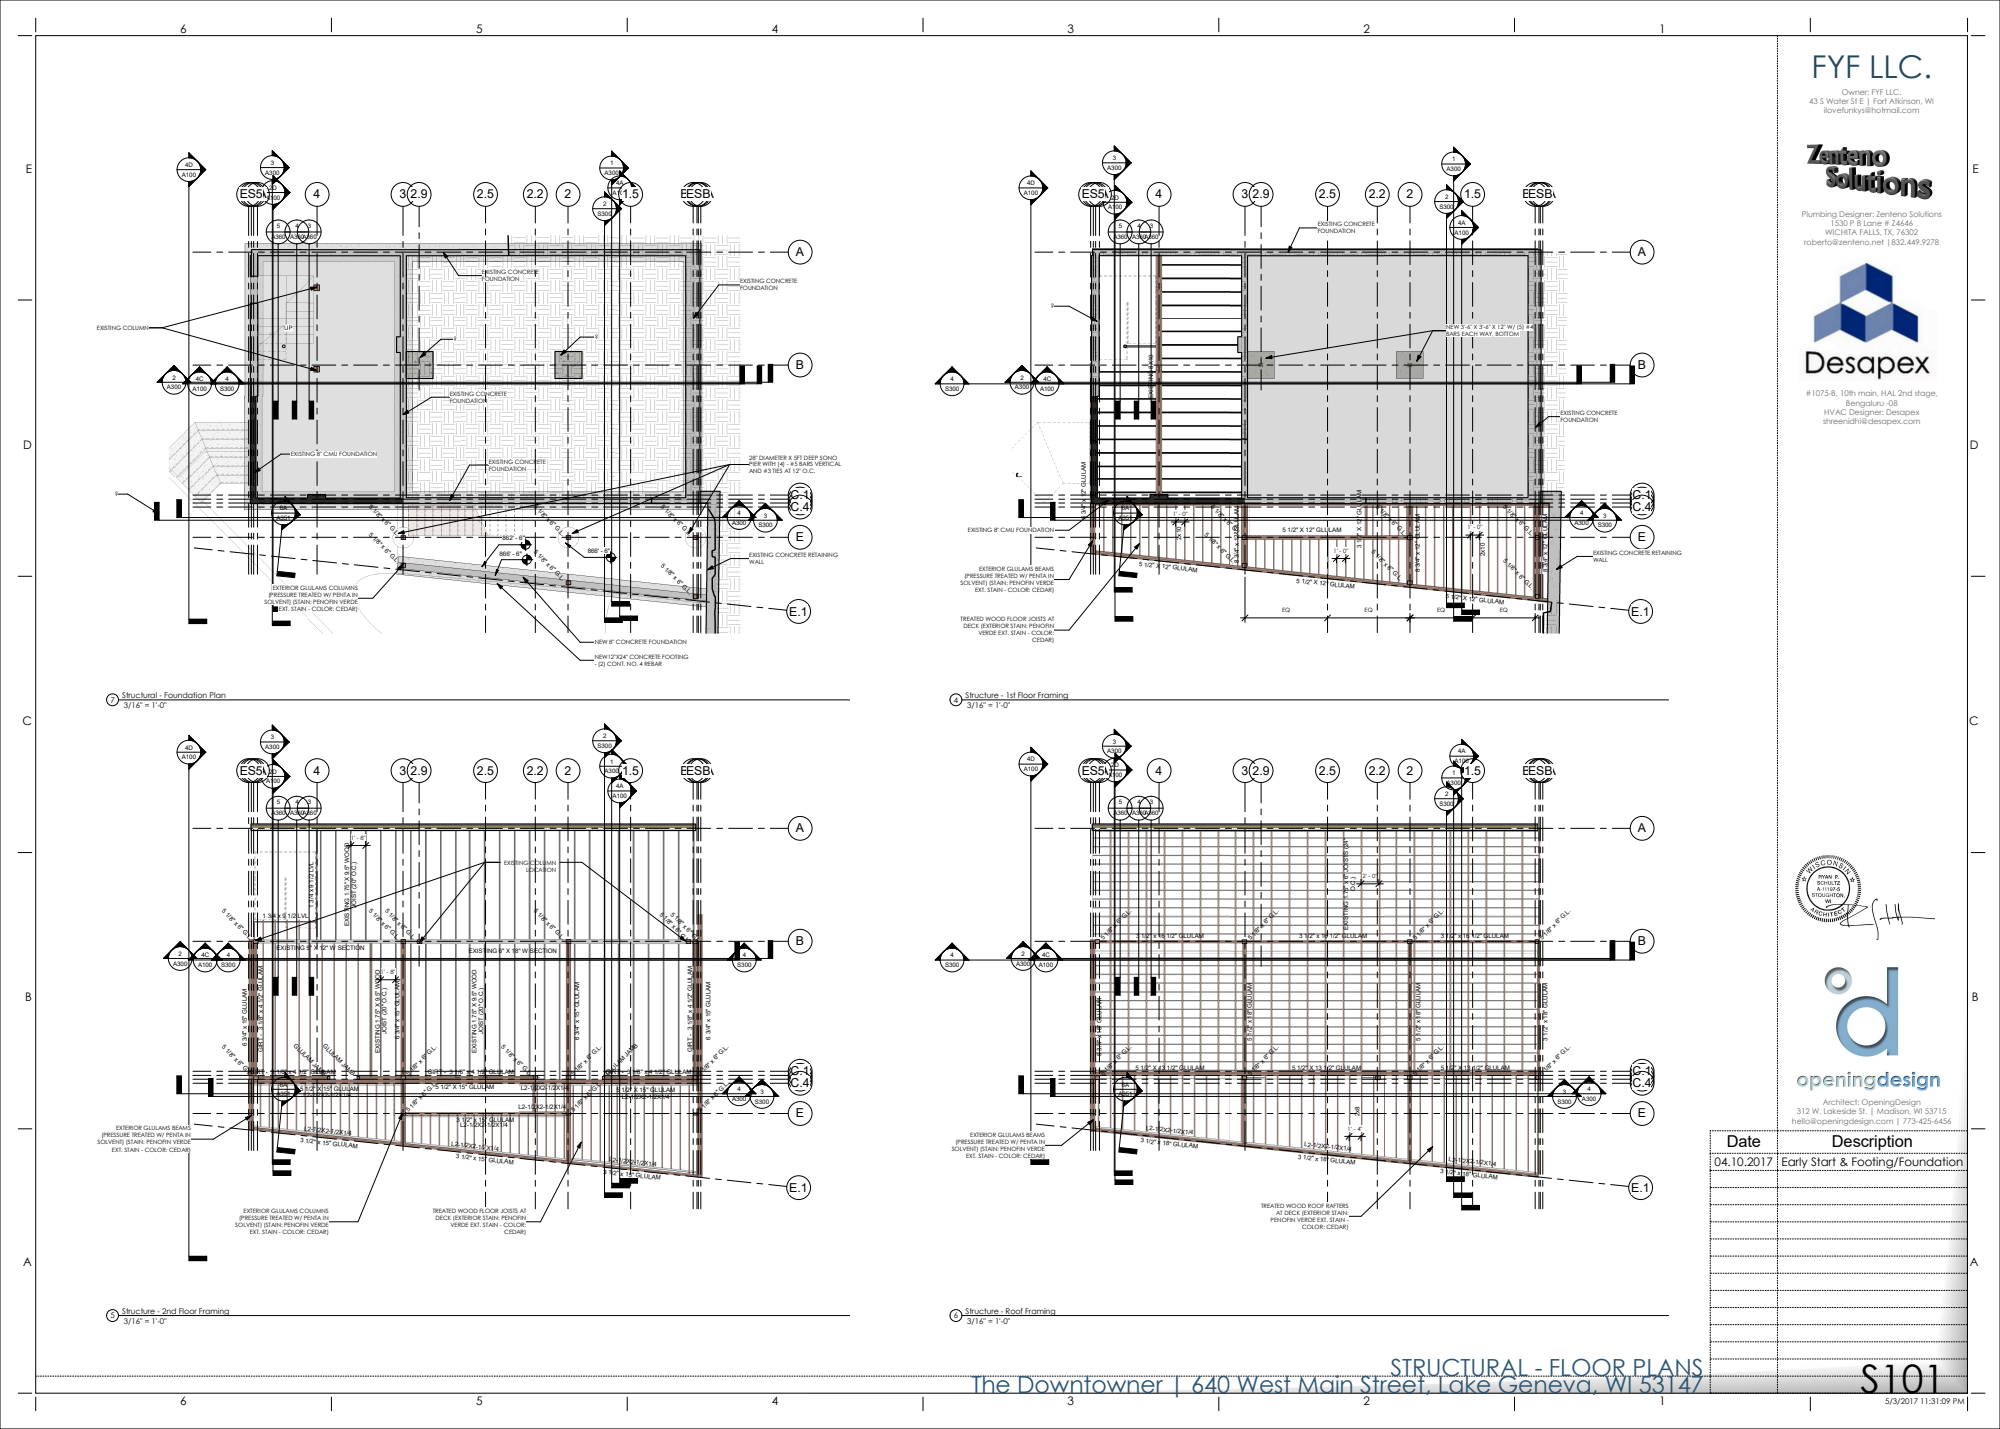
[picture p284: page 1]
EXISTING 8X10; 5 1/2" X 12" GLULAM; 8 3/4" x 12" GLULAM; 6 3/4" x 12" GLULAM; EXISTING CONCRETE FOUNDATION; EXISTING CONCRETE RETAINING; WALL; 3 1/2" X 12" GLULAM; CEDAR); ESB; 3 1/2" x 15" GLULAM; 6 3/4" x 15" GLULAM; 5 1/2" X 15" GLULAM 5 1/2" X 15" GLULAM; 5 1/2" X 15" GLULAM; GIRT - 3 1/8" x 4 1/2" GLULAM; GIRT - 3 1/8" x 4 1/2" GLULAM 5 1/8"; EXISTING 5" X 12" W SECTION; EXISTING 6" X 18" W SECTION; EXISTING COLUMN LOCATION; GLULAM JAMB 5 1/8" x 6" G.L.; EXISTING 1.75" X 9.5" WOOD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

Owner: FYF LLC.

43 S Water St E | Fort Atkinson, WI
ilovefunkys@hotmail.com

Plumbing Designer: Zenteno Solutions

1530 P B Lane # Z4646
WICHITA FALLS, TX, 76302
roberto@zenteno.net |832.449.9278

NEW 3'-6" X 3'-6" X 12" W/ (5) #4
BARS EACH WAY, BOTTOM

#1075-B, 10th main, HAL 2nd stage,

Bengaluru -08
HVAC Designer: Desapex
shreenidhi@desapex.com

EXISTING 8" CMU FOUNDATION

28" DIAMETER X 5FT DEEP SONO
PIER WITH (4) - #5 BARS VERTICAL
AND #3 TIES AT 12" O.C.

EXISTING CONCRETE RETAINING
WALL

EXTERIOR GLULAMS BEAMS
(PRESSURE TREATED W/ PENTA IN
SOLVENT) (STAIN: PENOFIN VERDE
EXT. STAIN - COLOR: CEDAR)

EXTERIOR GLULAMS COLUMNS

TREATED WOOD FLOOR JOISTS AT
DECK (EXTERIOR STAIN: PENOFIN
VERDE EXT. STAIN - COLOR:

NEW 8" CONCRETE FOUNDATION

NEW12"X24" CONCRETE FOOTING
- (2) CONT. NO. 4 REBAR

3/16" = 1'-0" 7 Structural - Foundation Plan

3/16" = 1'-0" 4 Structure - 1st Floor Framing

GLULAM JAMB GLULAM JAMB 5 1/8" x 6" G.L.

312 W. Lakeside St. | Madison, WI 53715
hello@openingdesign.com | 773-425-6456

04.10.2017 Early Start & Footing/Foundation

TREATED WOOD ROOF RAFTERS
AT DECK (EXTERIOR STAIN:
PENOFIN VERDE EXT. STAIN -

S101 STRUCTURAL - FLOOR PLANS The Downtowner | 640 West Main Street, Lake Geneva, WI 53147
