OpeningDesign/Vacation_Rental/Transfer/20170503 ----- ISSUE FOR PERMIT ------/S300 - STRUCTURAL - SECTIONS.pdf

B

C.3 E

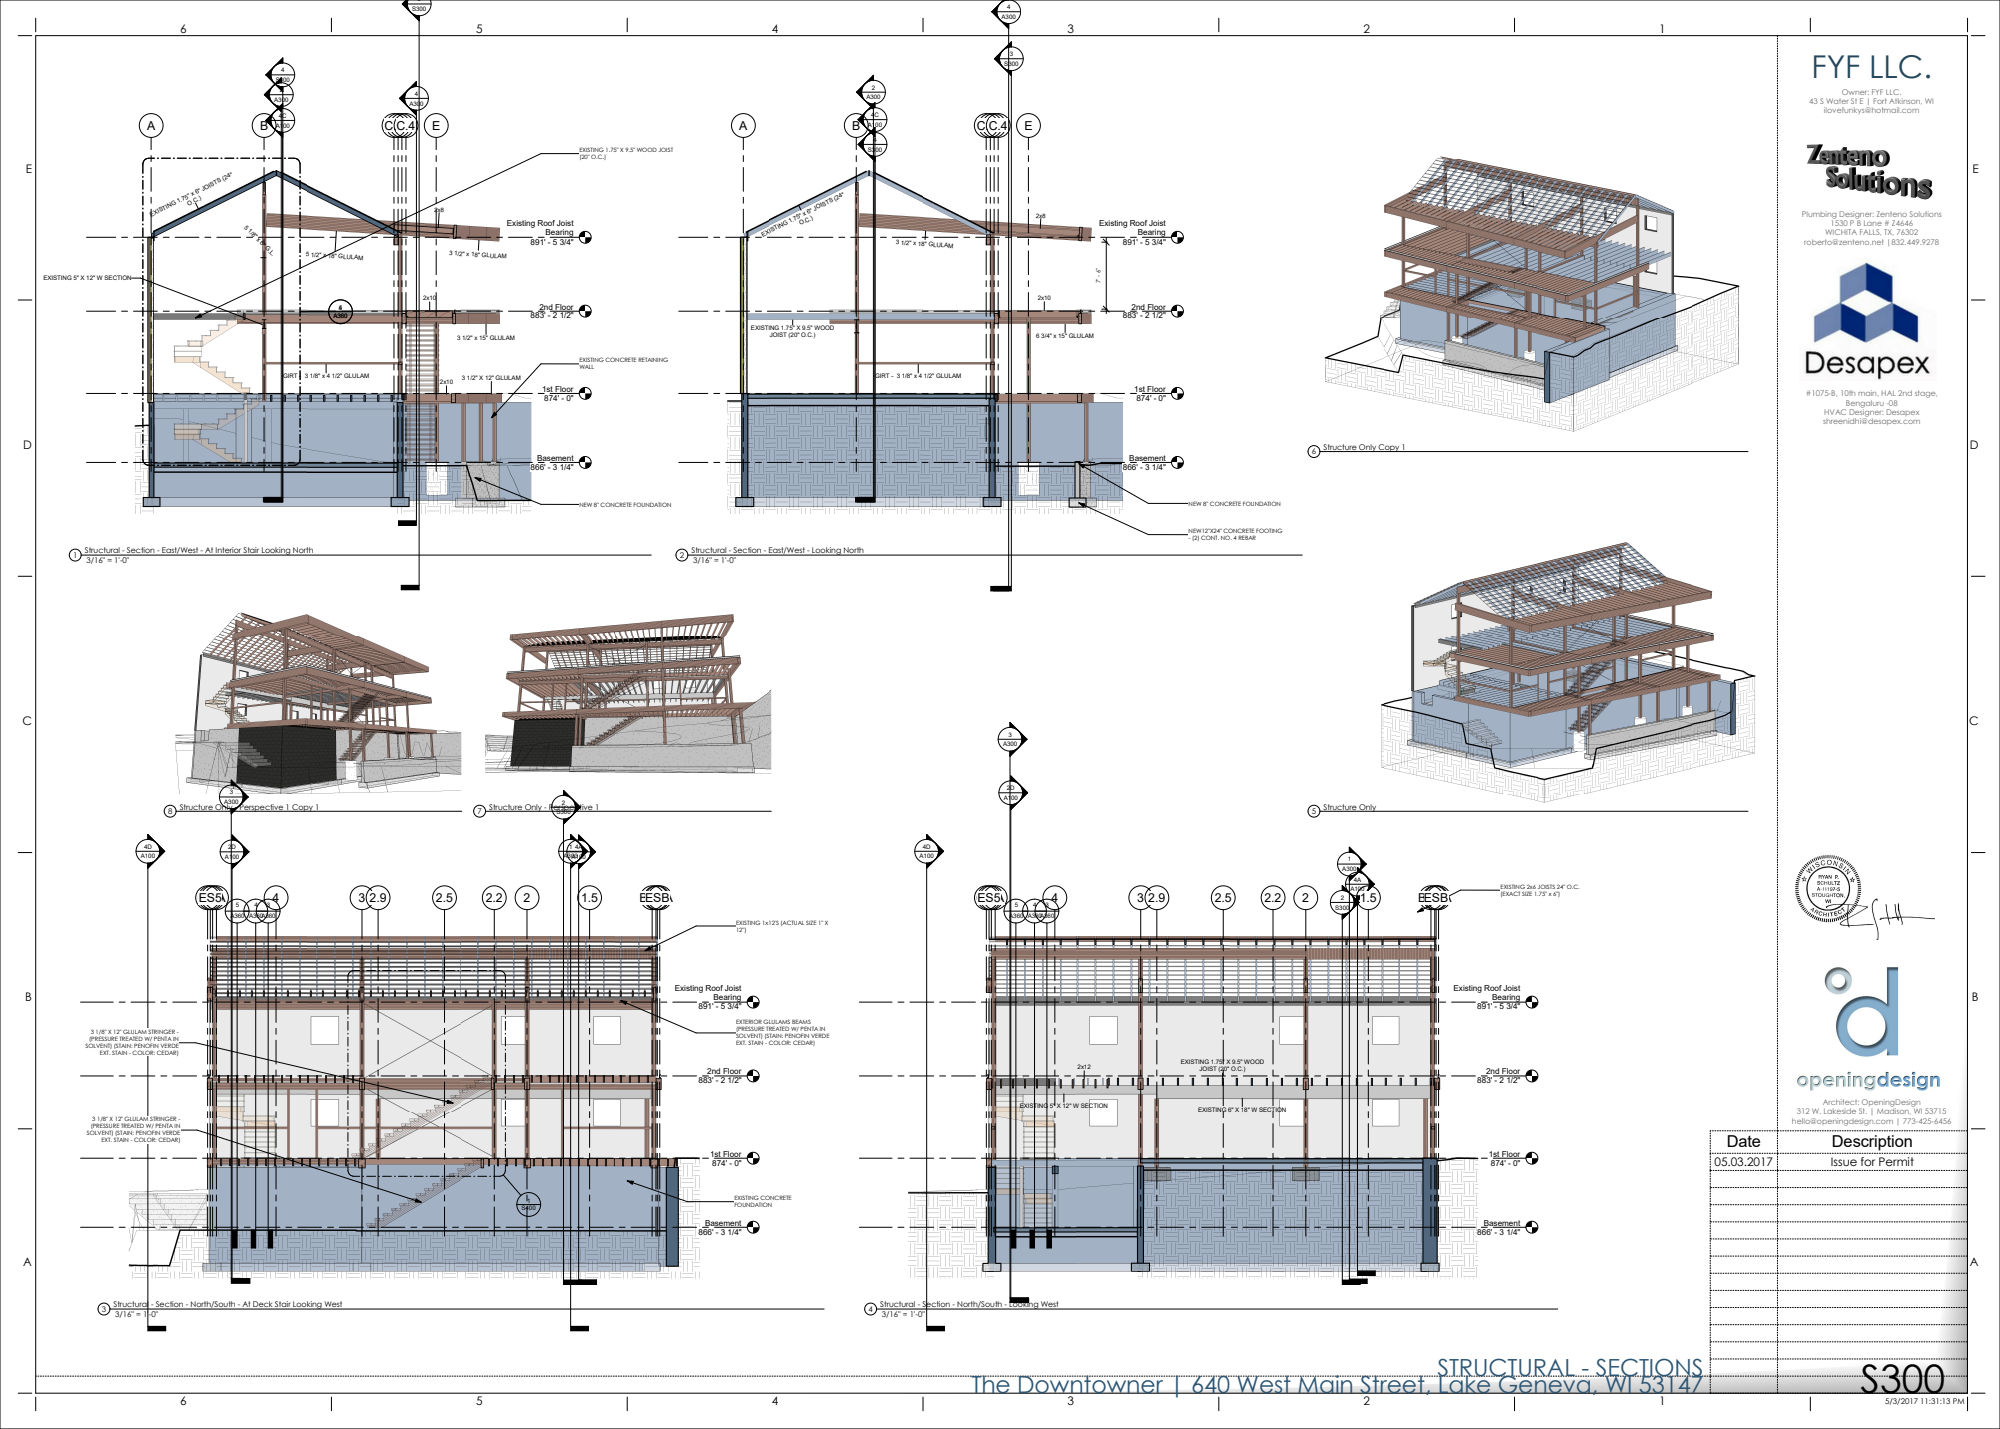
[picture p285: page 1]
1st Floor 874' - 0"; 2nd Floor 883' - 2 1/2"; Basement 866' - 3 1/4"; Bearing 891' - 5 3/4"; 3 1/2" x 15" GLULAM; 3 1/2" x 18" GLULAM; 5 1/2" x 18" GLULAM; EXISTING 5" X 12" W SECTION; GIRT - 3 1/8" x 4 1/2" GLULAM; 3 1/2" X 12" GLULAM; EXISTING 1.75" x 6" JOISTS (24" O.C.); EXISTING 1.75" X 9.5" WOOD; JOIST (20" O.C.); 6 3/4" x 15" GLULAM; EXISTING CONCRETE FOUNDATION; ESB; EXISTING 2x6 JOISTS 24" O.C.; (EXACT SIZE 1.75" x 6") 2.9; EXISTING 1.75" X 9.5" WOOD JOIST (20" O.C.) 2x12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

Owner: FYF LLC.

43 S Water St E | Fort Atkinson, WI
ilovefunkys@hotmail.com

EXISTING 1.75" X 9.5" WOOD JOIST

Plumbing Designer: Zenteno Solutions

Existing Roof Joist

1530 P B Lane # Z4646
WICHITA FALLS, TX, 76302
roberto@zenteno.net |832.449.9278

EXISTING CONCRETE RETAINING
WALL

#1075-B, 10th main, HAL 2nd stage,

Bengaluru -08
HVAC Designer: Desapex
shreenidhi@desapex.com

6 Structure Only Copy 1

NEW 8" CONCRETE FOUNDATION

NEW12"X24" CONCRETE FOOTING
- (2) CONT. NO. 4 REBAR

7 Structure Only - Perspective 1 8 Structure Only - Perspective 1 Copy 1

EXISTING 1x12'S (ACTUAL SIZE 1" X

EXTERIOR GLULAMS BEAMS
(PRESSURE TREATED W/ PENTA IN
SOLVENT) (STAIN: PENOFIN VERDE
EXT. STAIN - COLOR: CEDAR)

3 1/8" X 12" GLULAM STRINGER -

EXISTING 6" X 18" W SECTION EXISTING 5" X 12" W SECTION

312 W. Lakeside St. | Madison, WI 53715
hello@openingdesign.com | 773-425-6456

05.03.2017 Issue for Permit

S300 STRUCTURAL - SECTIONS The Downtowner | 640 West Main Street, Lake Geneva, WI 53147
