OpeningDesign/Vacation_Rental/Transfer/20171222 - fence design - owner review/20171222 - The Downtowner - Fence Details.pdf

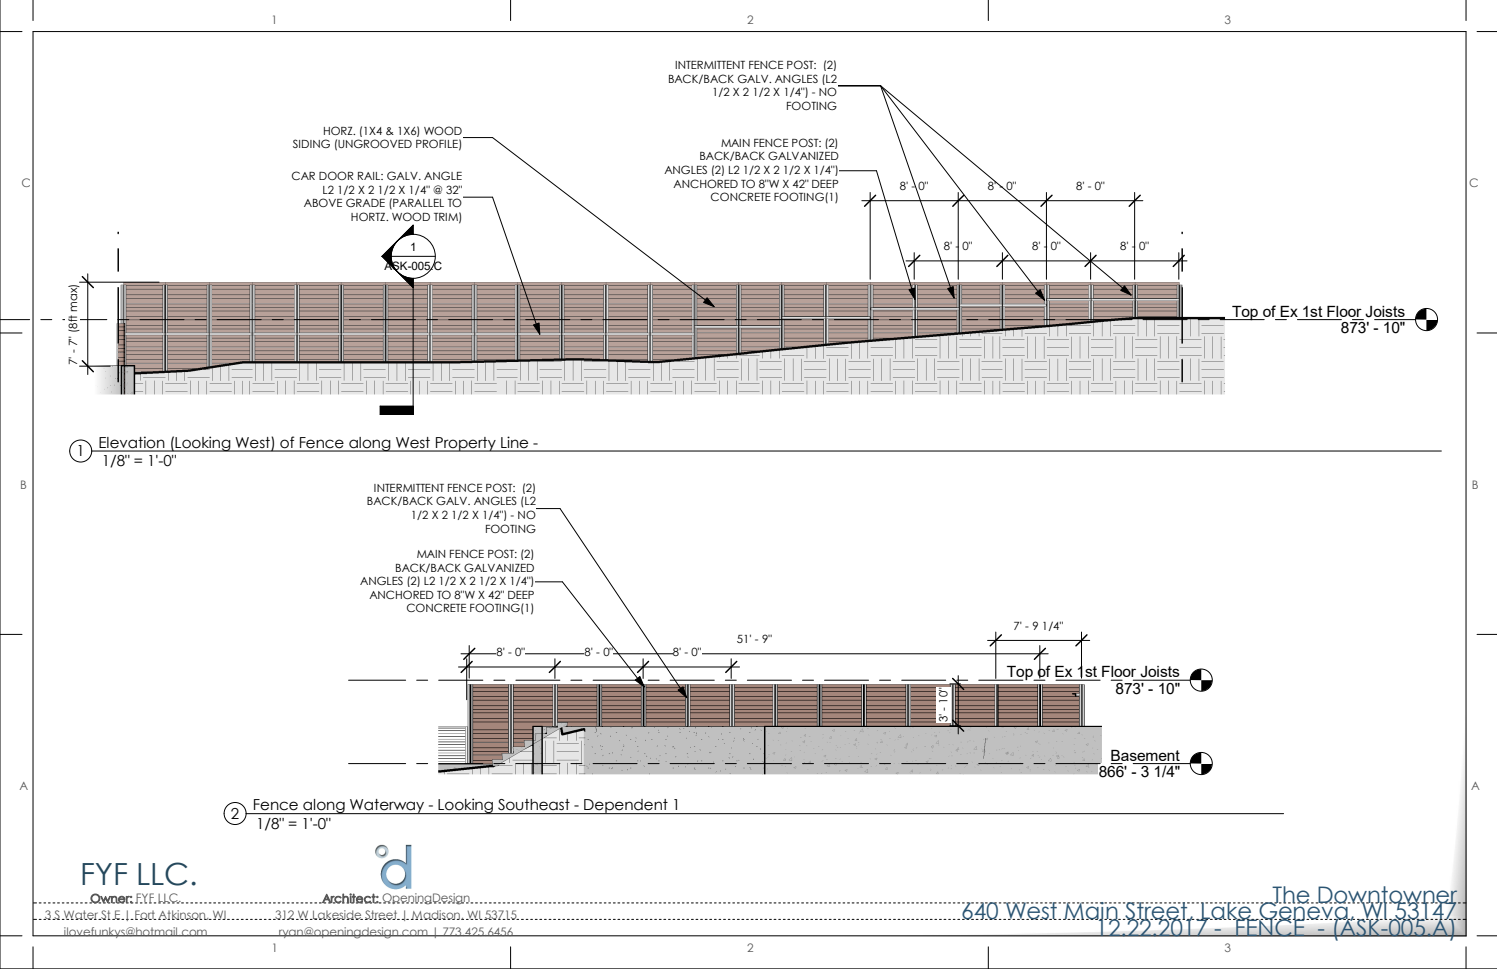
[picture p286: page 1]
7' - 7" (8ft max); CONCRETE FOOTING(1); 1/2 X 2 1/2 X 1/4") - NO FOOTING; ASK-005.C; Basement 866' - 3 1/4"; Architect: OpeningDesign; FYF LLC.; The Downtowner 12.22.2017 - FENCE - (ASK-005.A)

INTERMITTENT FENCE POST: (2)
BACK/BACK GALV. ANGLES (L2

HORZ. (1X4 & 1X6) WOOD
SIDING (UNGROOVED PROFILE)

MAIN FENCE POST: (2)
BACK/BACK GALVANIZED

ANGLES (2) L2 1/2 X 2 1/2 X 1/4")
ANCHORED TO 8"W X 42" DEEP

CAR DOOR RAIL: GALV. ANGLE
ABOVE GRADE (PARALLEL TO

HORTZ. WOOD TRIM)

Top of Ex 1st Floor Joists

Elevation (Looking West) of Fence along West Property Line -

Fence along Waterway - Looking Southeast - Dependent 1

Owner: FYF LLC.

640 West Main Street, Lake Geneva, WI 53147

3 S Water St E | Fort Atkinson, WI
ilovefunkys@hotmail.com

312 W Lakeside Street | Madison, WI 53715
ryan@openingdesign.com | 773.425.6456

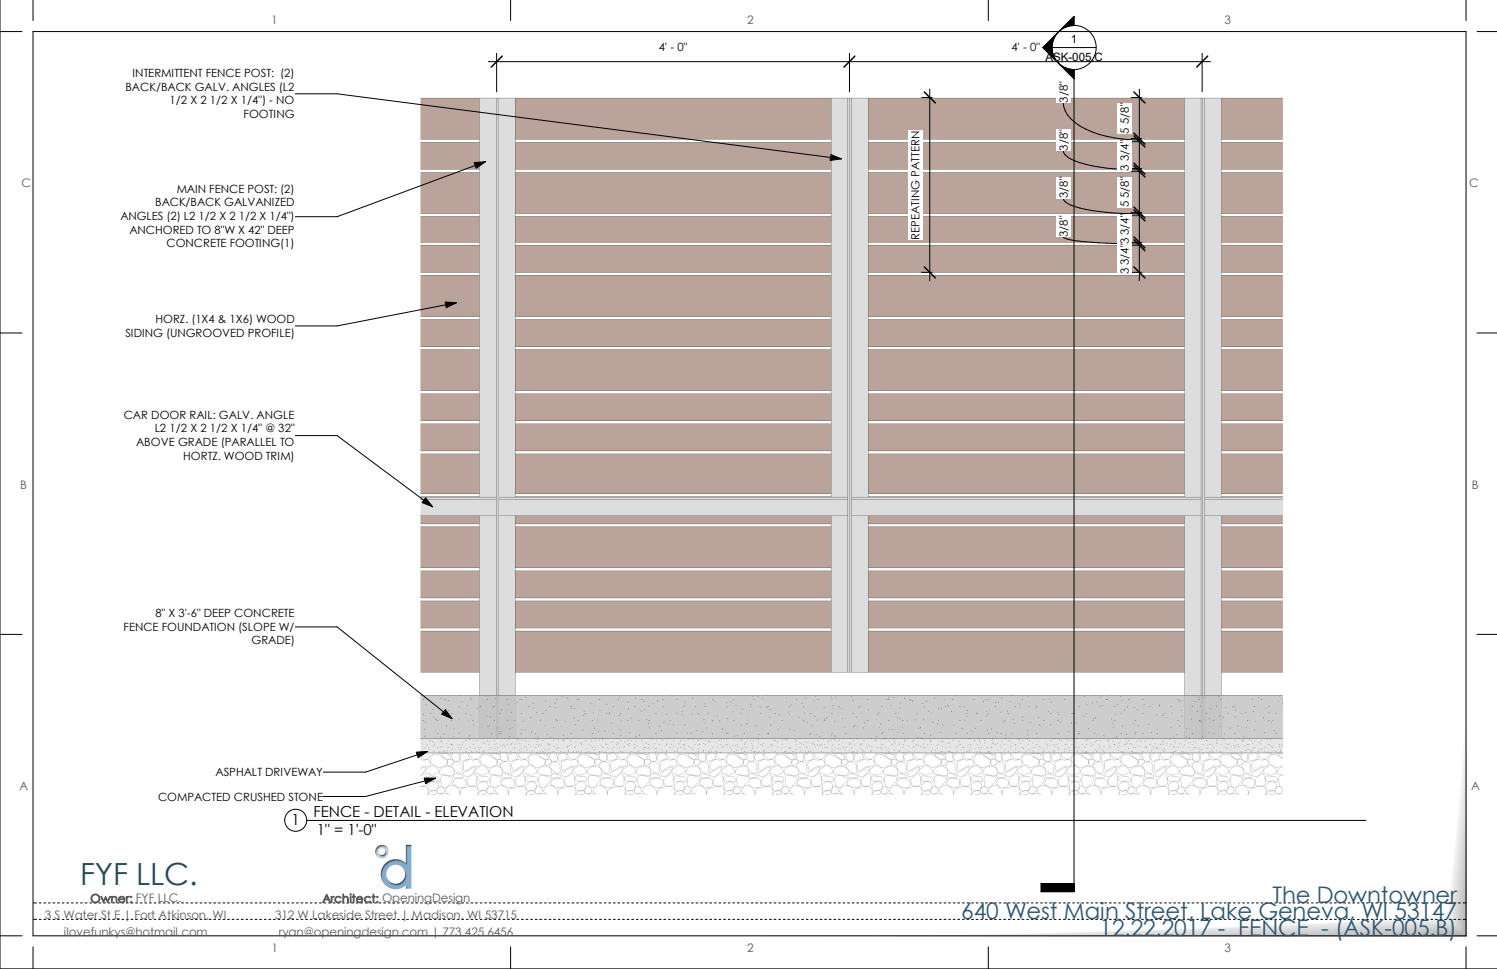
[picture p287: page 2]
REPEATING PATTERN; 1/2 X 2 1/2 X 1/4") - NO FOOTING; CONCRETE FOOTING(1); GRADE); ASPHALT DRIVEWAY; ASK-005.C; FYF LLC.; 12.22.2017 - FENCE - (ASK-005.B)

INTERMITTENT FENCE POST: (2)
BACK/BACK GALV. ANGLES (L2

MAIN FENCE POST: (2)
BACK/BACK GALVANIZED

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

HORZ. (1X4 & 1X6) WOOD
SIDING (UNGROOVED PROFILE)

CAR DOOR RAIL: GALV. ANGLE
ABOVE GRADE (PARALLEL TO

HORTZ. WOOD TRIM)

8" X 3'-6" DEEP CONCRETE
FENCE FOUNDATION (SLOPE W/

COMPACTED CRUSHED STONE

FENCE - DETAIL - ELEVATION

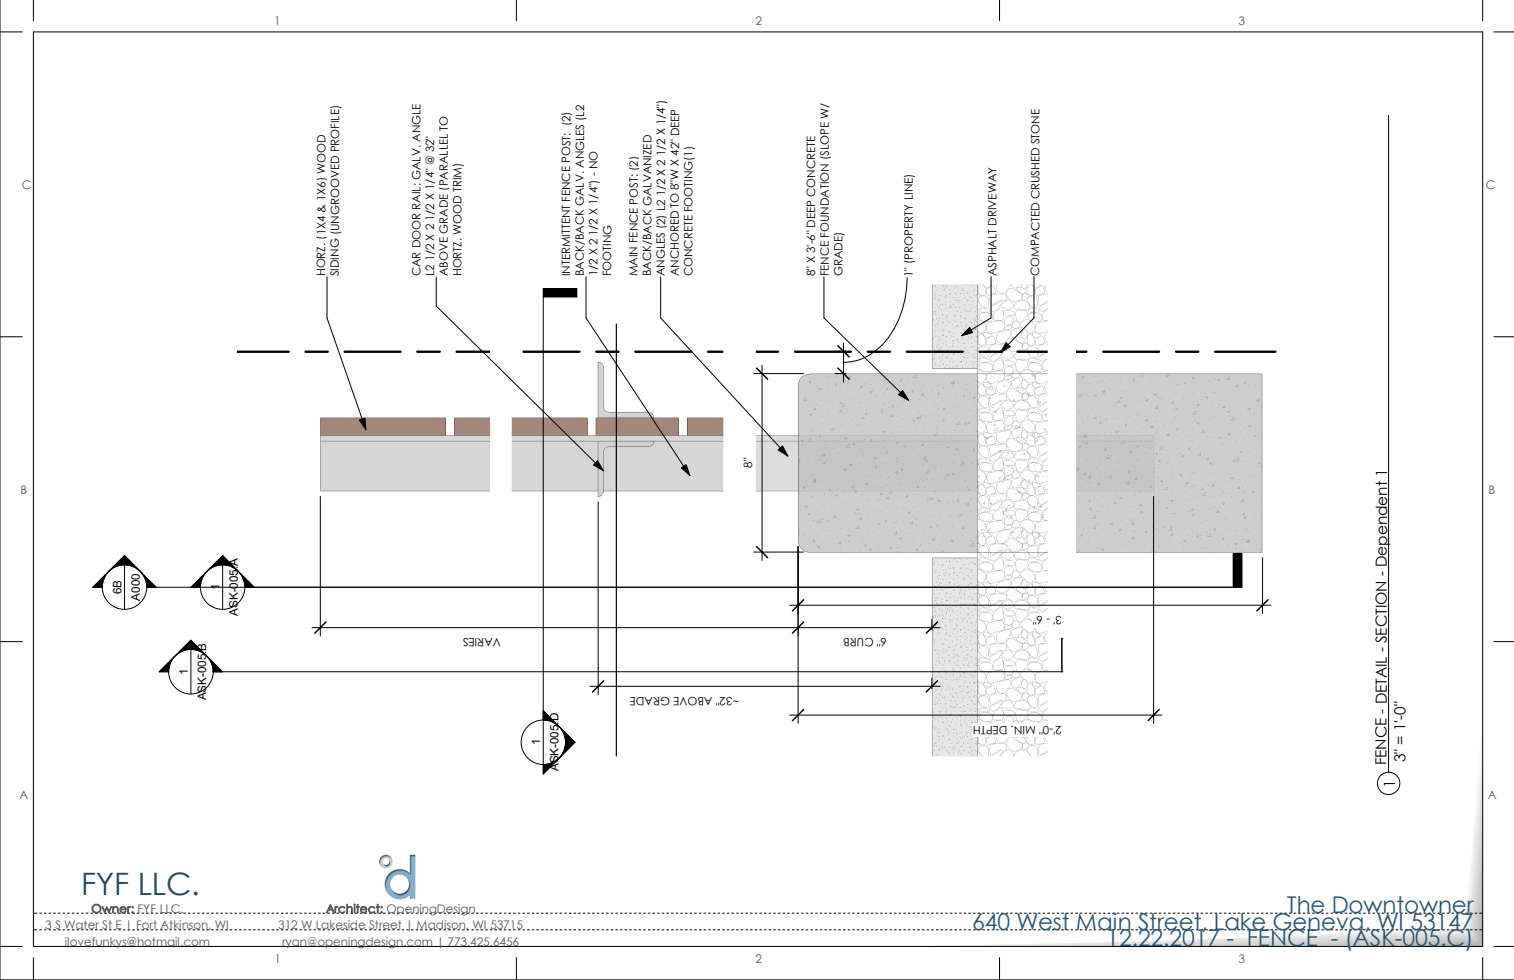
[picture p288: page 3]
8" X 3'-6" DEEP C; CRETE; FEN; CE FOUN; ATIO; N (SLOPE W/; GRA; ASPH; ALT DRIVEW; INTERMITTENT FEN; CE POST: (2); ALV. A; GLES (L2; OTIN; MPA; CTED; CRUSHED STO; ORZ. (1X; SIDIN; GRO; VED PROFILE); 1" (PROPERTY LINE); OR RAIL: G; GLE; ABO; VE GRA; ORTZ. W; D TRIM); AIN FEN; ALV; NIZED; GLES (2) L2 1/2; ORED TO; 2" DEEP; CRETE FO; FYF LLC.; 12.22.2017 - FENCE - (ASK-005.C); AIL - S; TIO

DE (PARALLEL TO

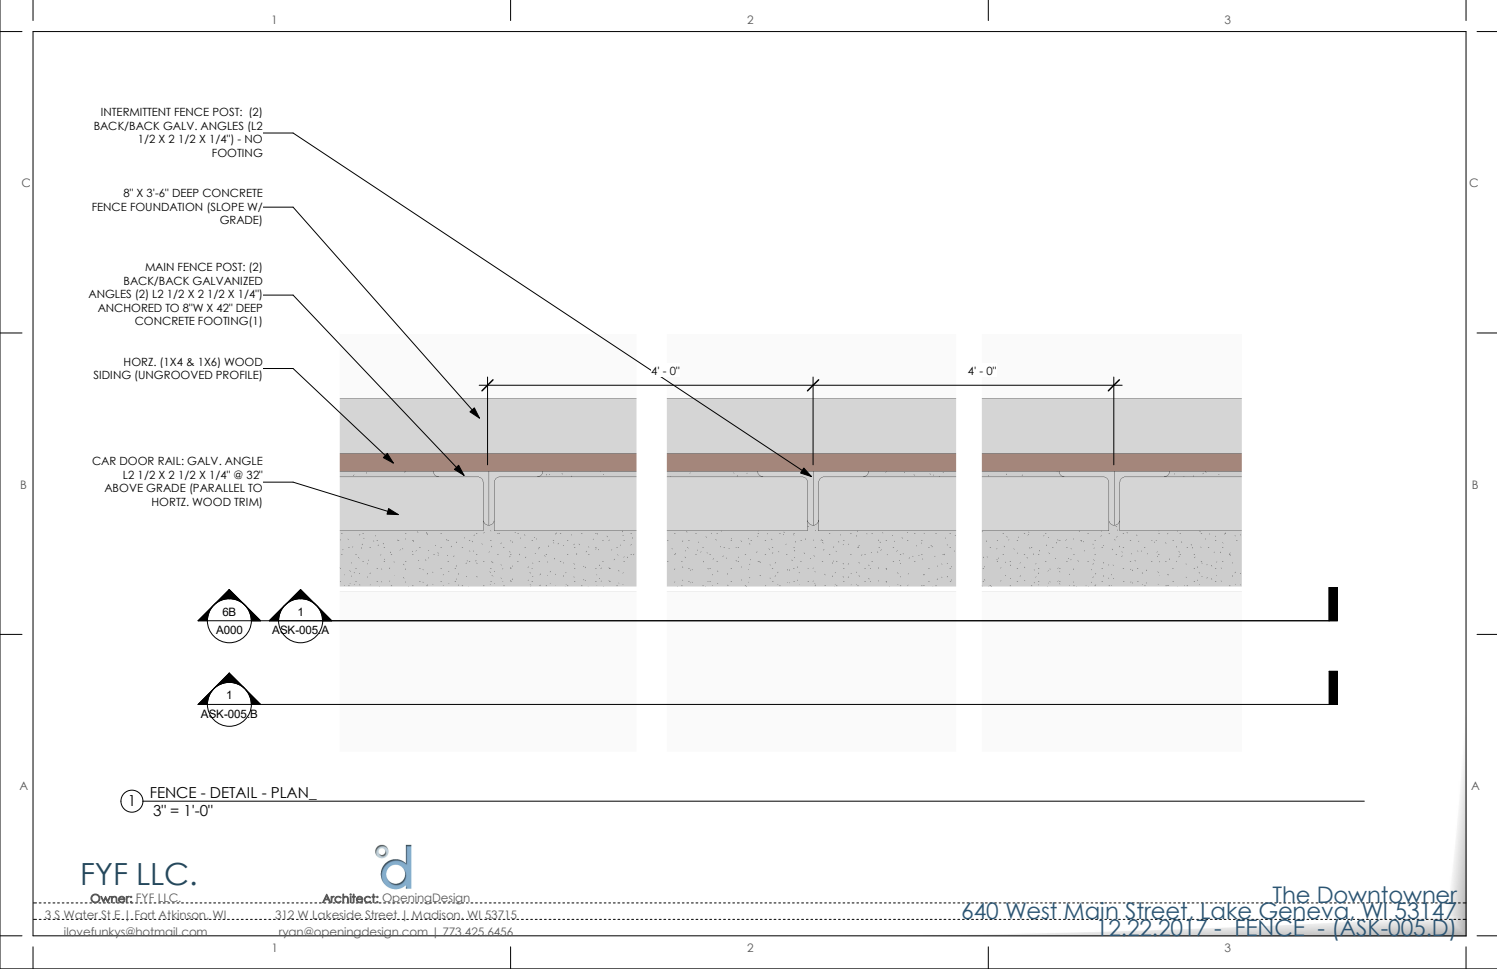
[picture p289: page 4]
ASK-005.A; ASK-005.B; CONCRETE FOOTING(1); GRADE); 1/2 X 2 1/2 X 1/4") - NO FOOTING; FYF LLC.; 12.22.2017 - FENCE - (ASK-005.D); FENCE - DETAIL - PLAN_

INTERMITTENT FENCE POST: (2)
BACK/BACK GALV. ANGLES (L2

8" X 3'-6" DEEP CONCRETE
FENCE FOUNDATION (SLOPE W/

MAIN FENCE POST: (2)
BACK/BACK GALVANIZED

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

HORZ. (1X4 & 1X6) WOOD
SIDING (UNGROOVED PROFILE)

CAR DOOR RAIL: GALV. ANGLE
ABOVE GRADE (PARALLEL TO

HORTZ. WOOD TRIM)

C

B

A

C

B

A

FYF LLC.

# 12.22.2017 - FENCE - (ASK-005.E)

1

FENCE - DETAIL - 3D - FROM NEIGHBORING PROPERTY | 2

## FENCE - DETAIL - 3D - FROM DRIVEWAY
