OpeningDesign/Vacation_Rental/Research and CA/Research and Submittals/02 - Existing Conditions and Code Research/Site Photos and Videos/20170418 - basement photos/2017-04-18 16.36.40.jpg

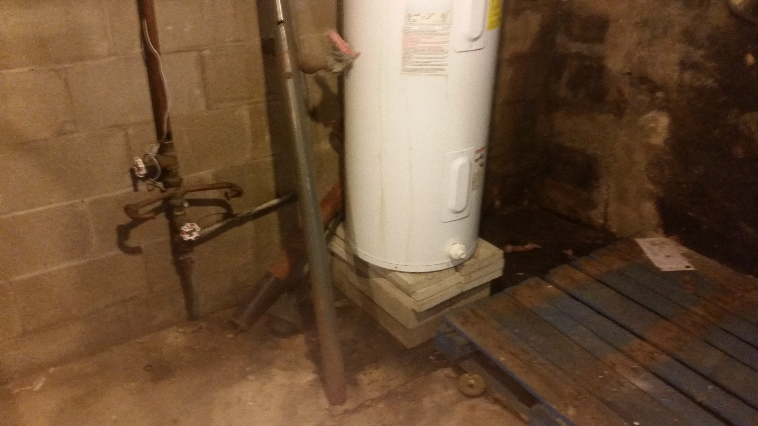
Research and CA/Research and Submittals/02 - Existing Conditions and Code Research/Site Photos and Videos/20170418 - basement photos/2017-04-18 16.36.40.jpg
